jonnew/ONIX/eib-64/README.md

# eib-64
64-channel electrode interface board (EIB) with electrical and optical
stimulation. Designed for small animal (e.g. mouse) tetrode electrophysiology.
Compatible with [headstage-64](../headstage-64/) and small shuttle-drives.

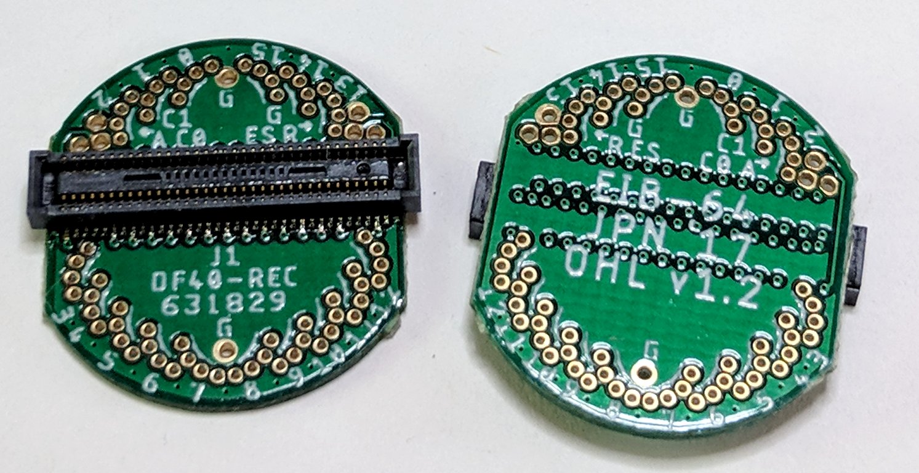
[picture p6: eib-64/img/eib-64.jpg]
eib-64


## Gerber Files
{% include gerber_layers.md %}

## Bill of Materials
The BOM is located on [this google
sheet](https://docs.google.com/spreadsheets/d/1F-KWcdvH_63iXjZf0cgCfDiFX6XXW3qw6rlR8DZrFpQ/edit#gid=1934583654).

## Pinout
The EIB pinout (ADC input mapping, stimulation connections, etc) is located on [this google sheet](https://docs.google.com/spreadsheets/d/11wRDYOqHN5lPb03yUdfXfK0zvaDYsVetplaNK-R90Gg/edit#gid=0)

## Tetrode Connectorization
This EIB uses Neuralynx ["small" gold pins](https://neuralynx.com/hardware/small-eib-pins) to attach tetrode wires. Usage instructions are provided in the [Neuralynx EIB pin Manual](https://neuralynx.com/documents/EIB%20Pins%20Manual.pdf).
