jonnew/ONIX/nanoz-adapter-128-256/README.md

# nanoz-adapter-128-256
Multiplexed adapter to interface eib-128 and eib-256 with the popular
[nanoZ](http://www.white-matter.com/nanoz/) electrode impedance tester and
plating device.

nanoz-128

## Gerber Files
{% include gerber_layers.md %}

## Bill of Materials
The BOM is located on [this google
sheet](https://docs.google.com/spreadsheets/d/1F-KWcdvH_63iXjZf0cgCfDiFX6XXW3qw6rlR8DZrFpQ/edit#gid=889124438).

## Electrode Mapping
The NanoZ internal channel number to EIB mapping for [eib-128](../README.md) and [eib-256](../eib-256/README.md) are provided in the following google sheets:
- [eib-128 channel mapping](https://docs.google.com/spreadsheets/d/11wRDYOqHN5lPb03yUdfXfK0zvaDYsVetplaNK-R90Gg/edit#gid=663991061)
- [eib-256 channel mapping](https://docs.google.com/spreadsheets/d/11wRDYOqHN5lPb03yUdfXfK0zvaDYsVetplaNK-R90Gg/edit#gid=538743909)
