jonnew/ONIX/nanoz-adapter-64/README.md

# nanoz-adapter-64
Adapter to interface eib-64 with the popular
[nanoZ](http://www.white-matter.com/nanoz/) electrode impedance tester and
plating device.

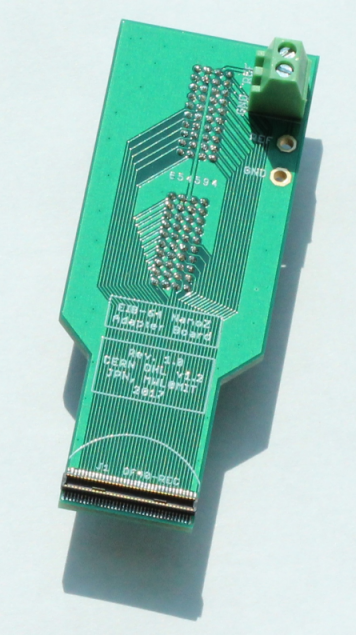
[picture p10: nanoz-adapter-64/img/nanoz-adapter-64.png]
nanoz-64


## Gerber Files
{% include gerber_layers.md %}

## Bill of Materials
The BOM is located on [this google
sheet](https://docs.google.com/spreadsheets/d/1F-KWcdvH_63iXjZf0cgCfDiFX6XXW3qw6rlR8DZrFpQ/edit#gid=889124438).

## Electrode Mapping
The NanoZ internal channel number to [eib-64](../eib-64/README.md) channel mapping is provided on [this google sheet](https://docs.google.com/spreadsheets/d/11wRDYOqHN5lPb03yUdfXfK0zvaDYsVetplaNK-R90Gg/edit#gid=0).
