jonnew/ONIX/omnetics-adapter-64/README.md

# omnetics-adapter-64
Adapter board for using omnetics-based EIBs with headstage-64

## Gerber Files
{% include gerber_layers.md %}

## Bill of Materials
The BOM is located on [this google
sheet](https://docs.google.com/spreadsheets/d/1F-KWcdvH_63iXjZf0cgCfDiFX6XXW3qw6rlR8DZrFpQ/edit#gid=1934583654).

## Pinout
The adapter pinout is located on [this google
sheet](https://docs.google.com/spreadsheets/d/11wRDYOqHN5lPb03yUdfXfK0zvaDYsVetplaNK-R90Gg/edit#gid=1490495645)
