jonnew/ONIX/headstage-neuropix/headstage-neuropix_large-zif/README.md

# headstage-neuropix (large ZIF)
This version of the headstage has a larger, more reliable ZIF connector.

## Bill of materials
TODO
