jonnew/ONIX/headstage-neuropix/headstage-neuropix_standard-zif/README.md

# headstage-neuropix (standard ZIF)
This version of the headstage uses the IMEC-specified ZIF connector.

## Bill of materials
TODO
