jonnew/ONIX/breakout/case/case_.JPG

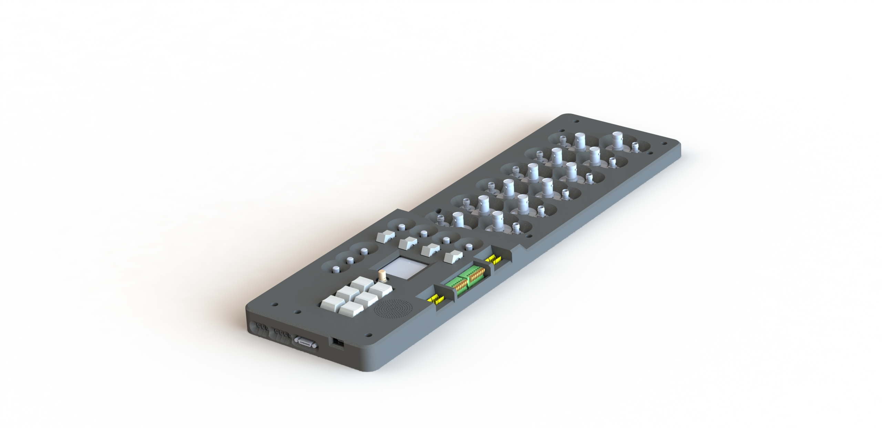
breakout/case/case_.JPG
