jonnew/ONIX/breakout/case/label/top_label_600ppi.png

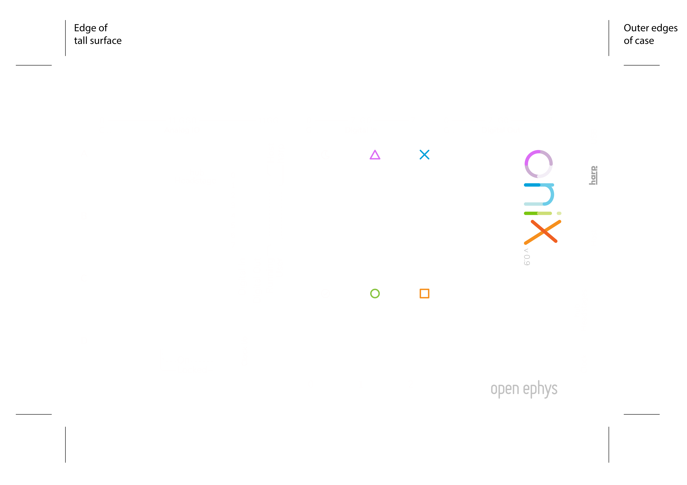
breakout/case/label/top_label_600ppi.png
