jonnew/ONIX/fmc-host/resources/fmc-lpc-pinout.jpg

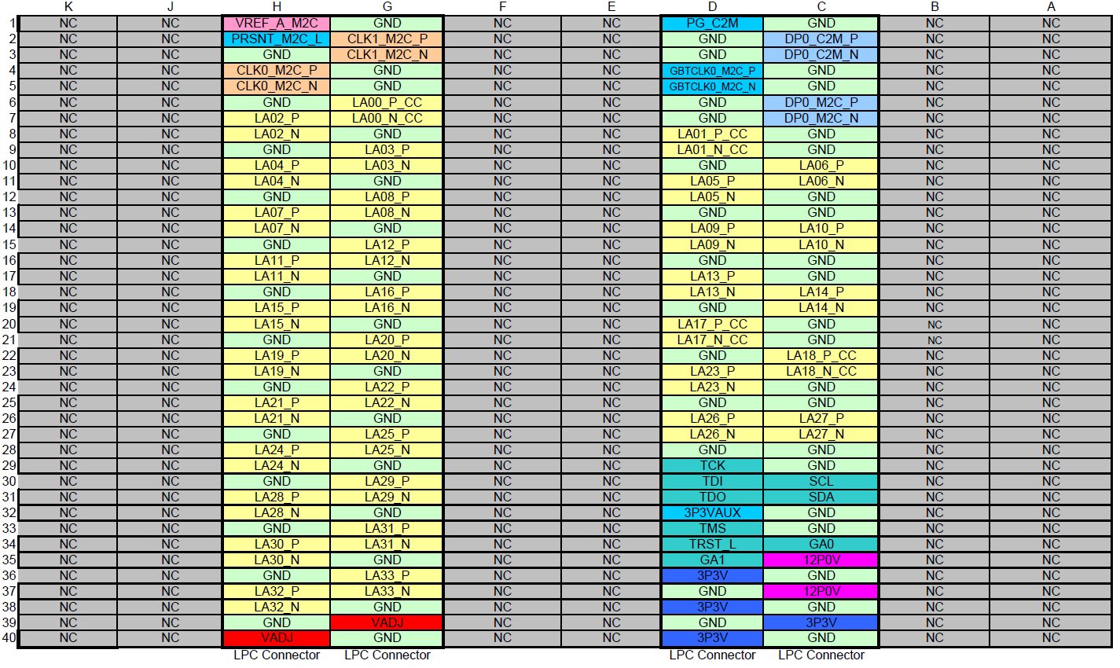
fmc-host/resources/fmc-lpc-pinout.jpg
