jonnew/ONIX/headstage-64/datasheets/MAX10_V81_WLCSP_routing_scheme.png

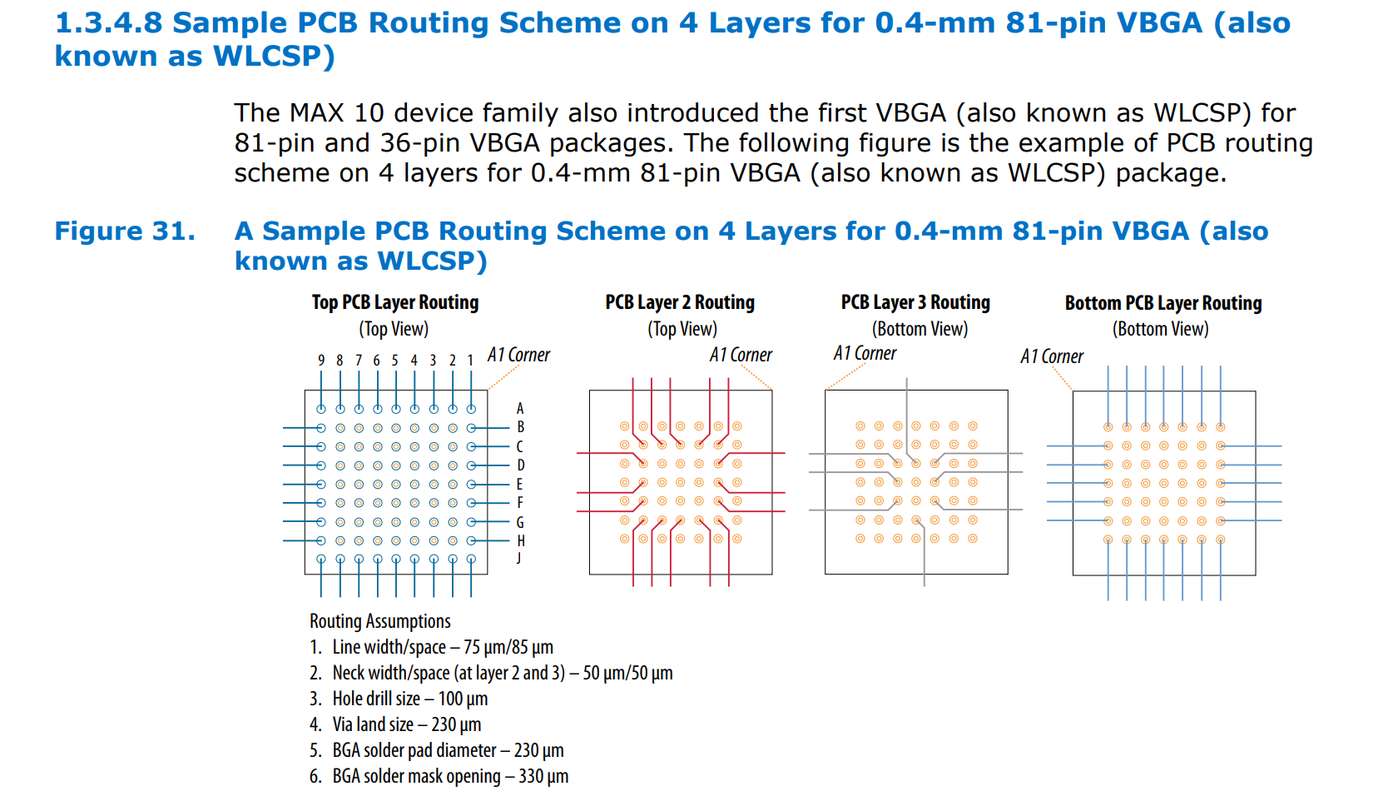
headstage-64/datasheets/MAX10_V81_WLCSP_routing_scheme.png
