jonnew/ONIX/headstage-64/decoupling-capacitors/max10-decoupling-plan.png

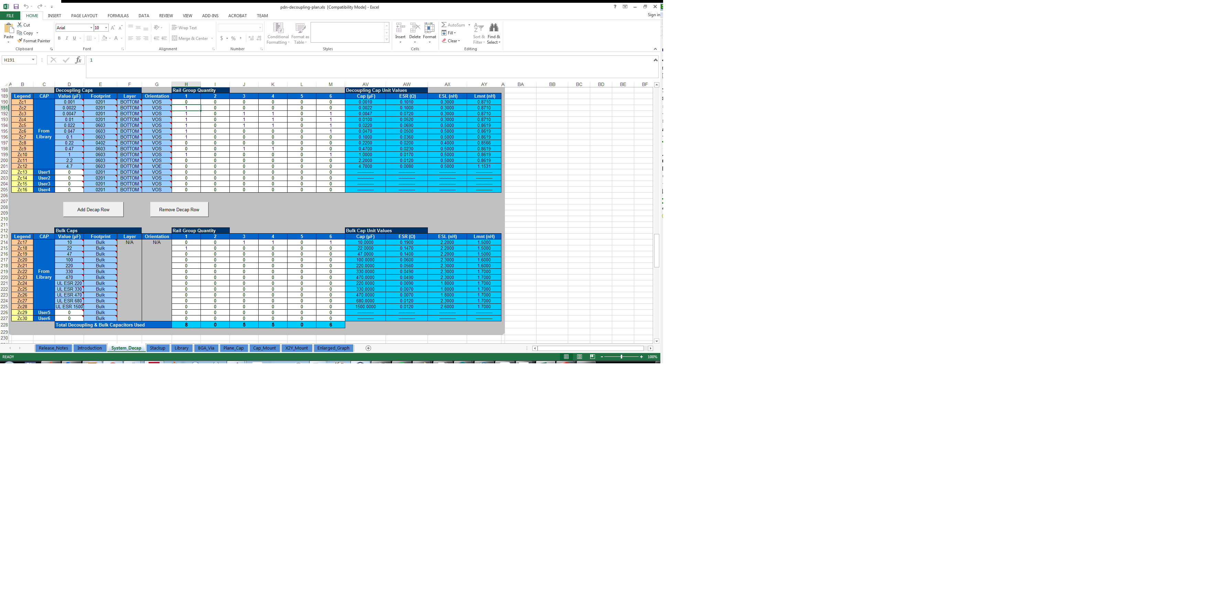
headstage-64/decoupling-capacitors/max10-decoupling-plan.png
