jonnew/ONIX/headstage-256/gerber/README_tab-placement.png

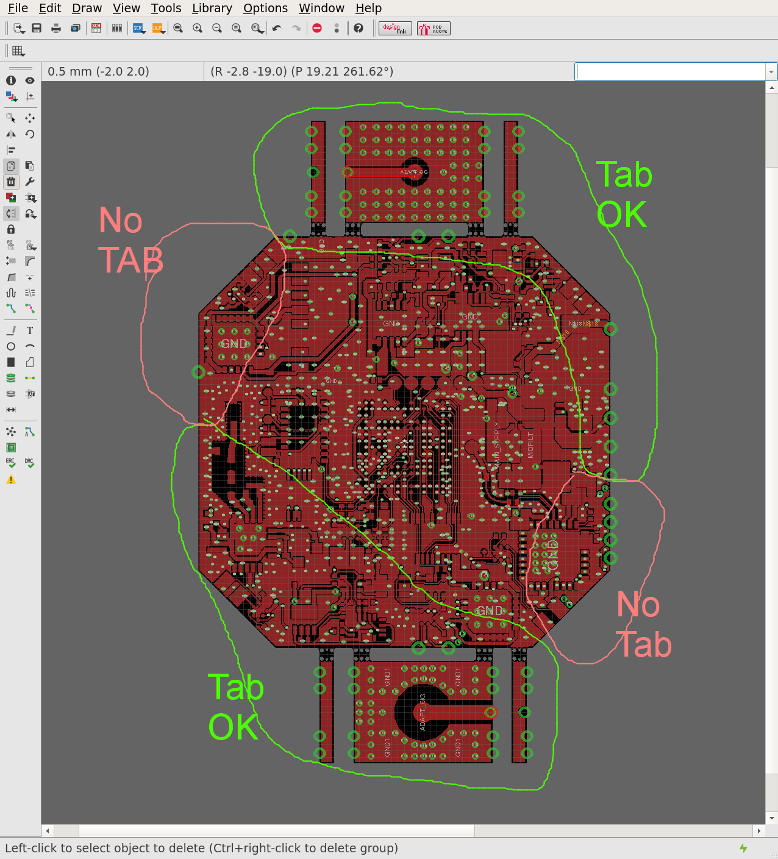
headstage-256/gerber/README_tab-placement.png
