jonnew/ONIX/breakout/case/label/onix_logo_bw.dxf

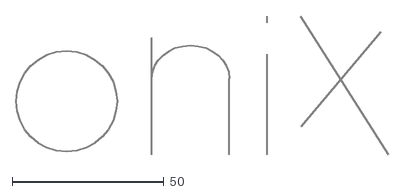
[picture p46: CAD file, 2020-10-13]
breakout/case/label/onix_logo_bw.dxf
122.9 x 45.6
