jonnew/ONIX/doc/size_comparison/rhd64.SLDPRT

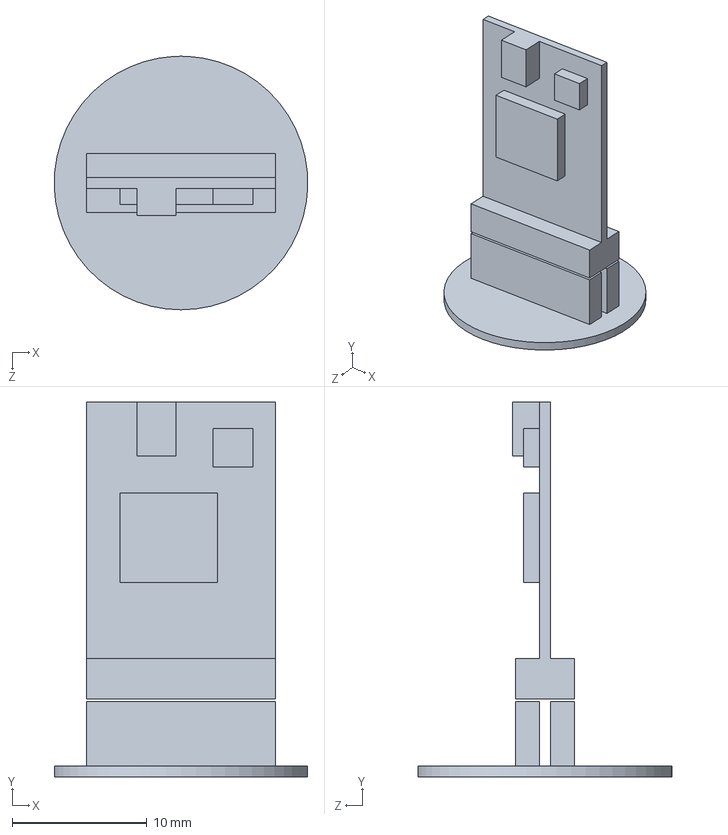
[picture p47: CAD file, 2020-05-30]
doc/size_comparison/rhd64.SLDPRT
18.8 x 27.8 x 18.8 mm
