jonnew/ONIX/fmc-host/pcie_case/fmc_host_pcie_case.SLDPRT

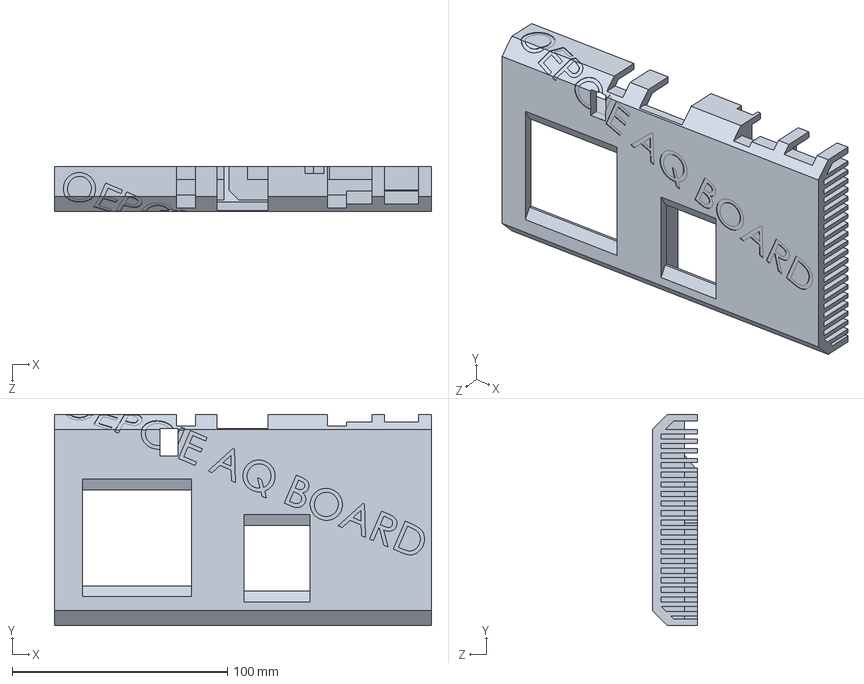
[picture p48: CAD file, 2019-09-29]
fmc-host/pcie_case/fmc_host_pcie_case.SLDPRT
175.0 x 98.0 x 21.0 mm
