jonnew/ONIX/fmc-host/revisions/rev-1.4/pcie_bracket/fmc-host.dxf

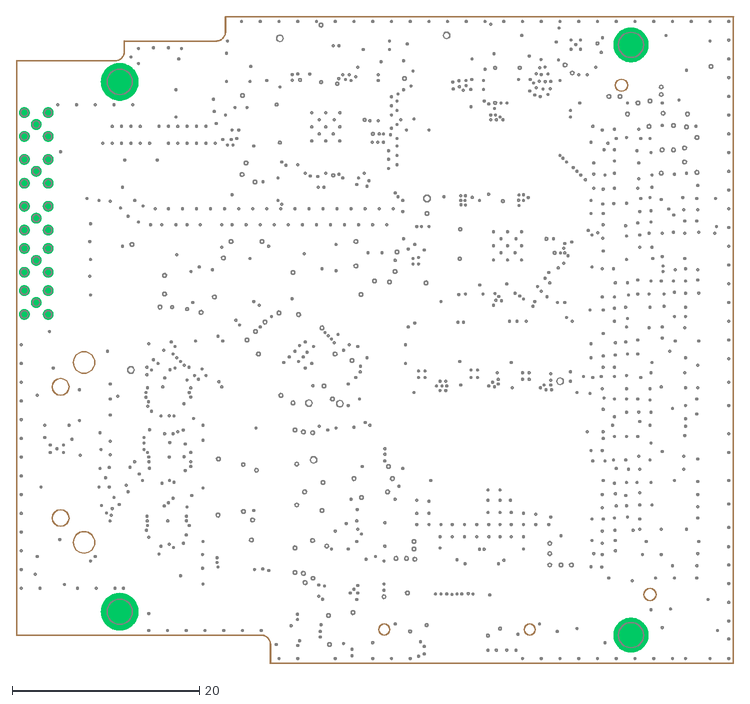
[picture p49: CAD file, 2020-07-13]
fmc-host/revisions/rev-1.4/pcie_bracket/fmc-host.dxf
76.6 x 69.1
