jonnew/ONIX/headstage-programmer/mechanical/headstage-neuropix-holder.SLDPRT

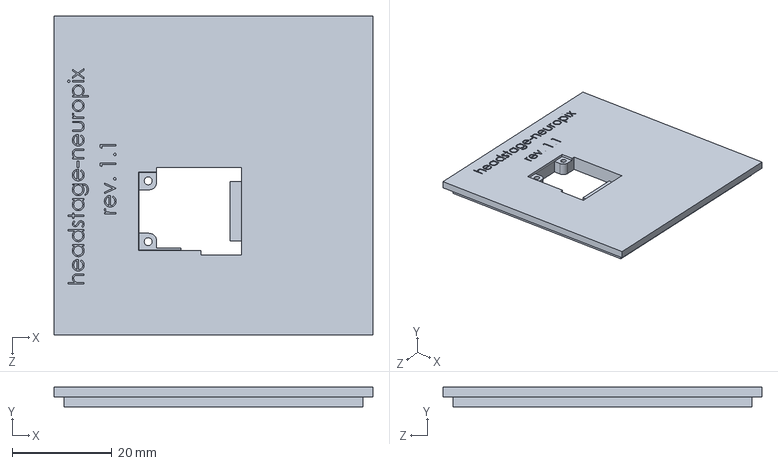
[picture p50: CAD file, 2019-10-03]
headstage-programmer/mechanical/headstage-neuropix-holder.SLDPRT
64.0 x 4.00 x 64.0 mm
