jonnew/ONIX/breakout/case/components/1_5_inch_screen/Adafruit_1.5_128x128_RGB_OLED.dxf

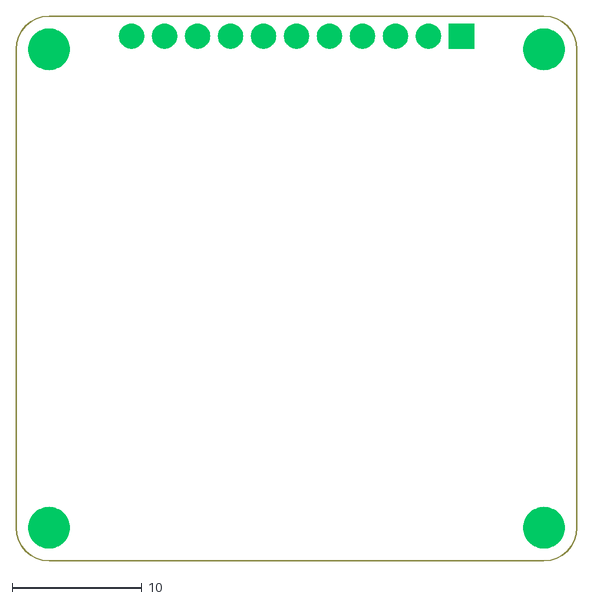
[picture p51: CAD file, 2019-09-01]
breakout/case/components/1_5_inch_screen/Adafruit_1.5_128x128_RGB_OLED.dxf
43.2 x 41.9
