jonnew/ONIX/breakout/case/components/cherryMX/MX轴 轴体 底部.SLDPRT

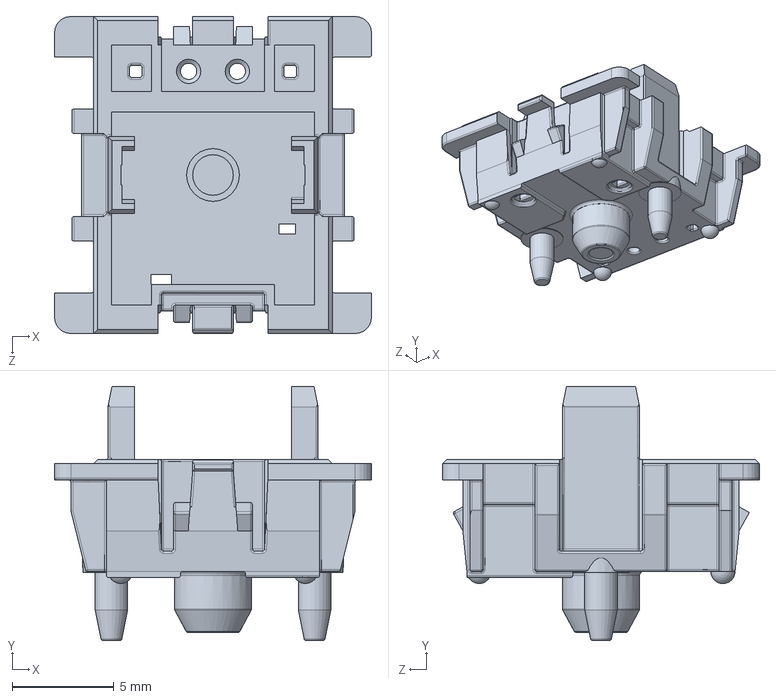
[picture p52: CAD file, 2019-09-01]
breakout/case/components/cherryMX/MX轴 轴体 底部.SLDPRT
15.6 x 12.5 x 15.6 mm
