jonnew/ONIX/breakout/case/components/sma_tall.SLDPRT

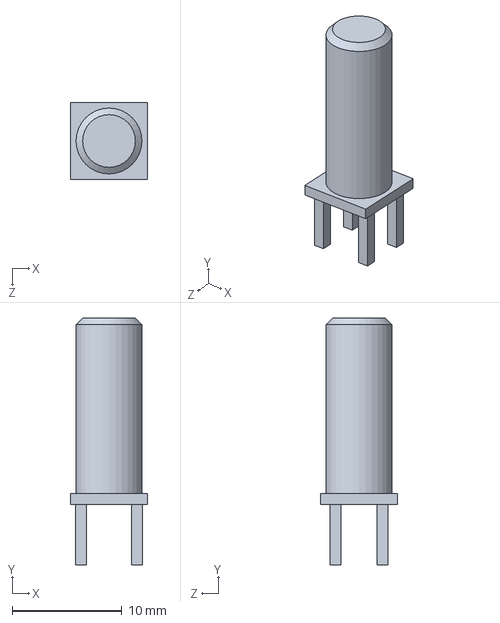
[picture p53: CAD file, 2019-12-28]
breakout/case/components/sma_tall.SLDPRT
7.00 x 22.5 x 7.00 mm
