jonnew/ONIX/breakout/case/pcb_spacer_lasercut_4mm_plastic.DXF

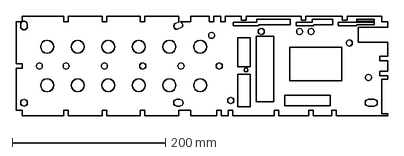
[picture p54: CAD file, 2021-03-16]
breakout/case/pcb_spacer_lasercut_4mm_plastic.DXF
485.0 x 130.0 mm
