jonnew/ONIX/doc/size_comparison/oe_round_spi.SLDPRT

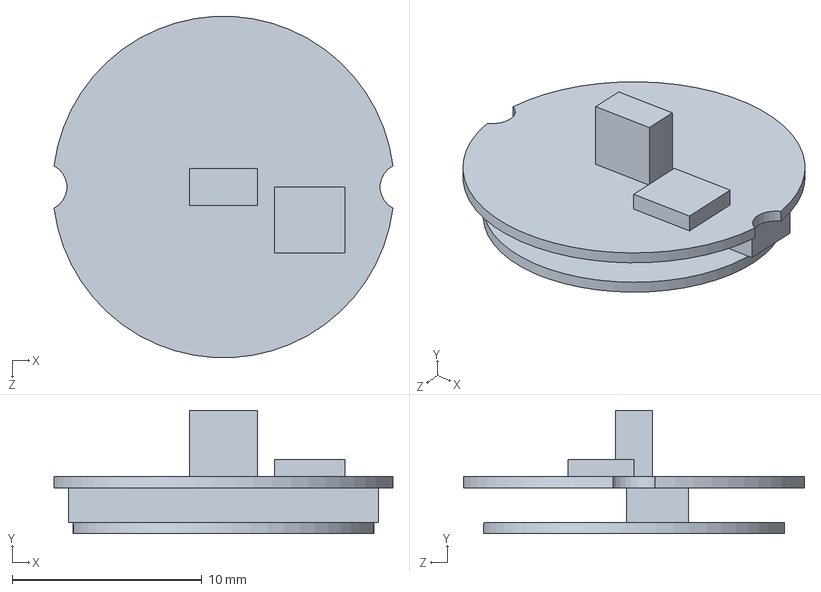
[picture p55: CAD file, 2020-05-30]
doc/size_comparison/oe_round_spi.SLDPRT
17.9 x 6.50 x 18.0 mm
