jonnew/ONIX/fmc-host/pcie_case/refs/WaveTherm-OC-PCB-FMC_OC-PCB-FMC.SLDPRT

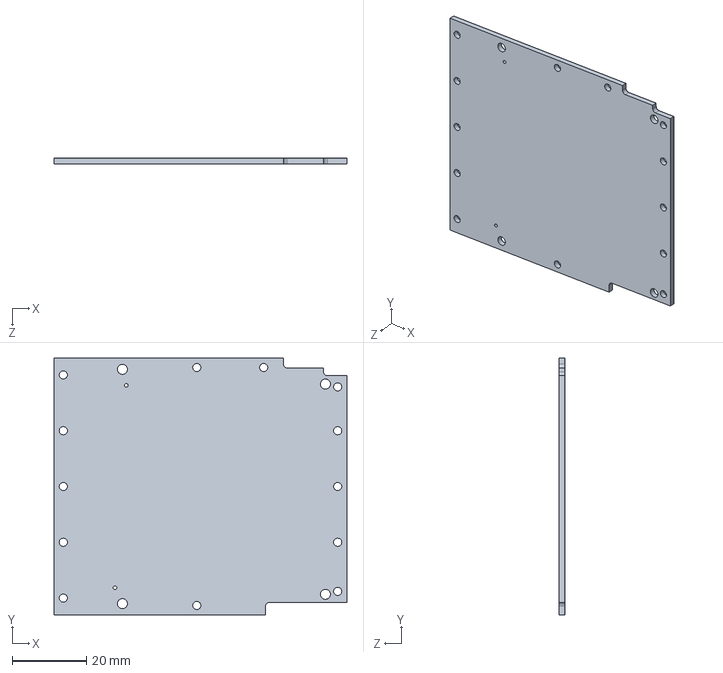
[picture p56: CAD file, 2019-05-07]
fmc-host/pcie_case/refs/WaveTherm-OC-PCB-FMC_OC-PCB-FMC.SLDPRT
78.8 x 69.0 x 1.60 mm
