jonnew/ONIX/fmc-host/revisions/rev-1.4/pcie_bracket/PCIe_bracket_cnc_thick.SLDPRT

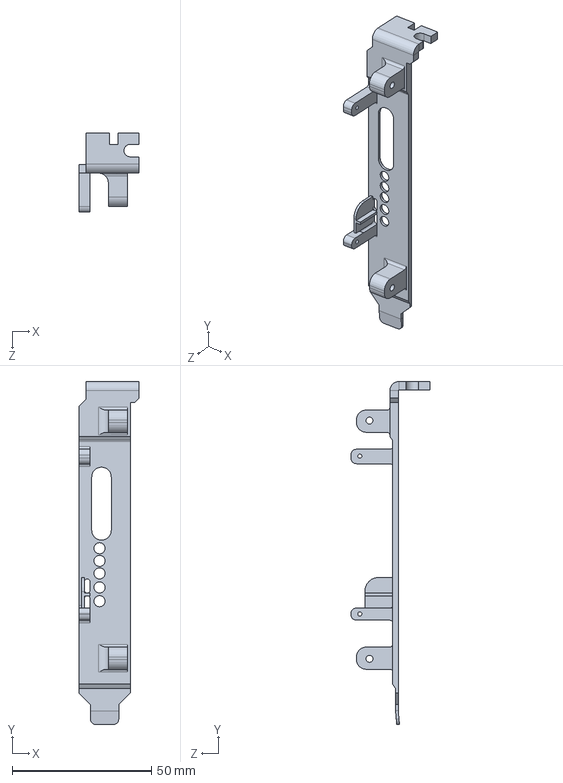
[picture p57: CAD file, 2020-03-31]
fmc-host/revisions/rev-1.4/pcie_bracket/PCIe_bracket_cnc_thick.SLDPRT
21.6 x 123.0 x 28.4 mm
