jonnew/ONIX/breakout/case/components/audio_plug_CUI_SJ1-3514-SMT-TR.sldprt

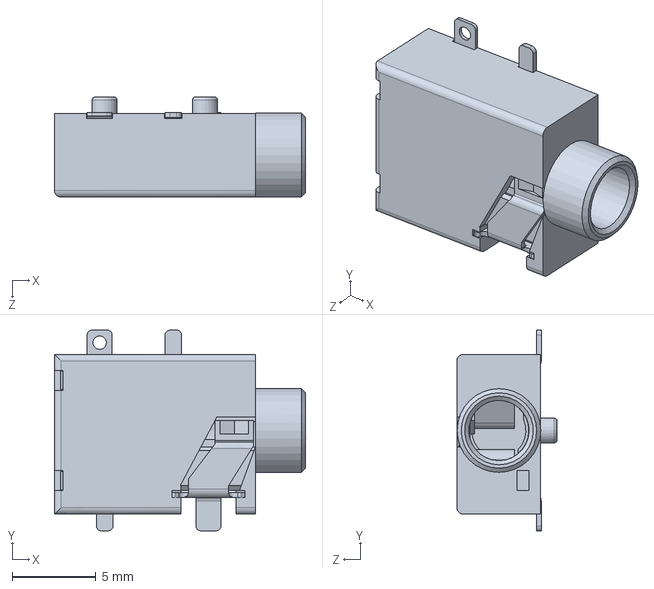
[picture p58: CAD file, 2019-12-28]
breakout/case/components/audio_plug_CUI_SJ1-3514-SMT-TR.sldprt
15.0 x 12.0 x 6.00 mm
