jonnew/ONIX/breakout/case/components/cherryMX/MX .STEP

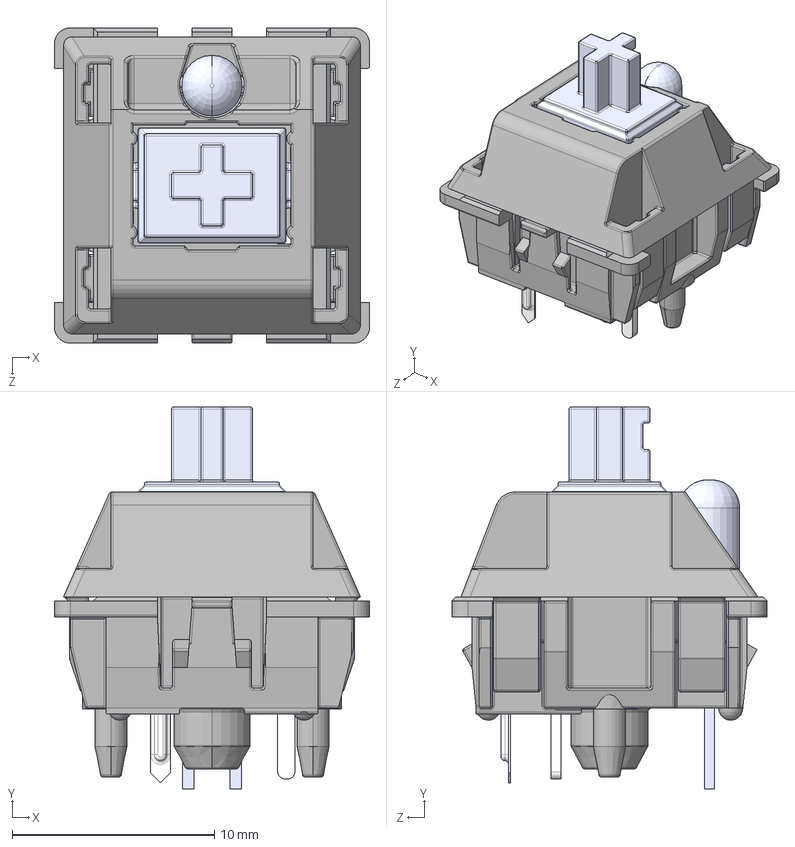
[picture p59: CAD file, 2019-09-01]
breakout/case/components/cherryMX/MX .STEP
15.6 x 18.9 x 15.6 mm
MX 轴 按键′_ü___¨1
MX 轴 轴体áì_¨￠¨__
MX粣 拸簽LEDLEDLED
MX轴 轴体 底部 μ×2__默认_á2____è_
针脚___默认__è_
