jonnew/ONIX/fmc-host/pcie_case/refs/WaveTherm-OC-PCB-FMC_SAMTEC_ASP-134488-01.sldprt

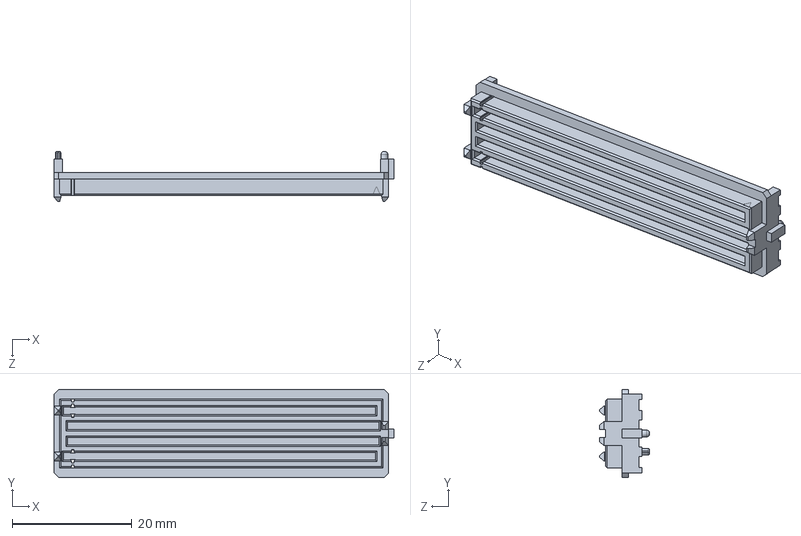
[picture p60: CAD file, 2019-05-07]
fmc-host/pcie_case/refs/WaveTherm-OC-PCB-FMC_SAMTEC_ASP-134488-01.sldprt
56.7 x 14.7 x 8.38 mm
