jonnew/ONIX/breakout/case/components/header_height_spacer_10mm.SLDPRT

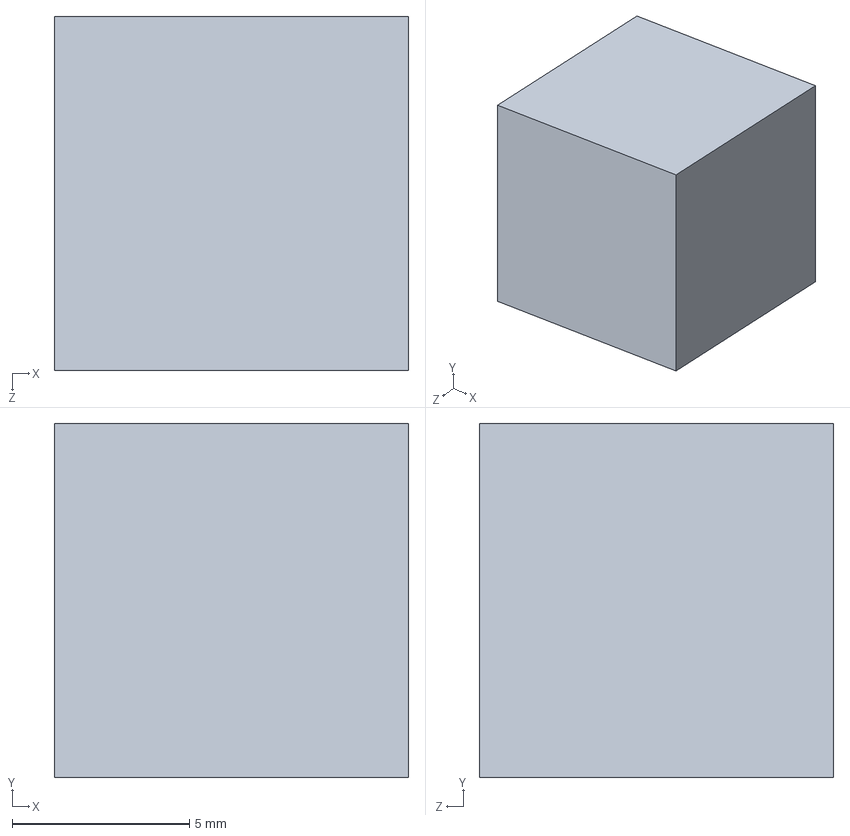
[picture p62: CAD file, 2019-12-28]
breakout/case/components/header_height_spacer_10mm.SLDPRT
10.0 x 10.0 x 10.0 mm
