jonnew/ONIX/fmc-host/revisions/rev-1.4/pcie_bracket/fmc_pcb.SLDPRT

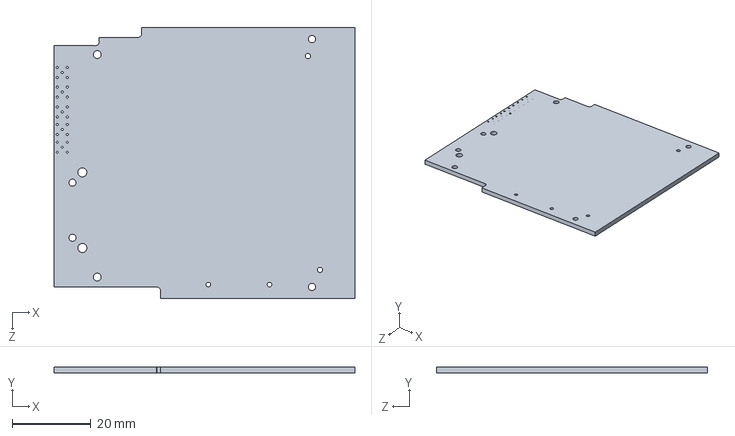
[picture p64: CAD file, 2019-09-29]
fmc-host/revisions/rev-1.4/pcie_bracket/fmc_pcb.SLDPRT
76.5 x 1.60 x 69.0 mm
