jonnew/ONIX/breakout/case/components/cherryMX/针脚.SLDPRT

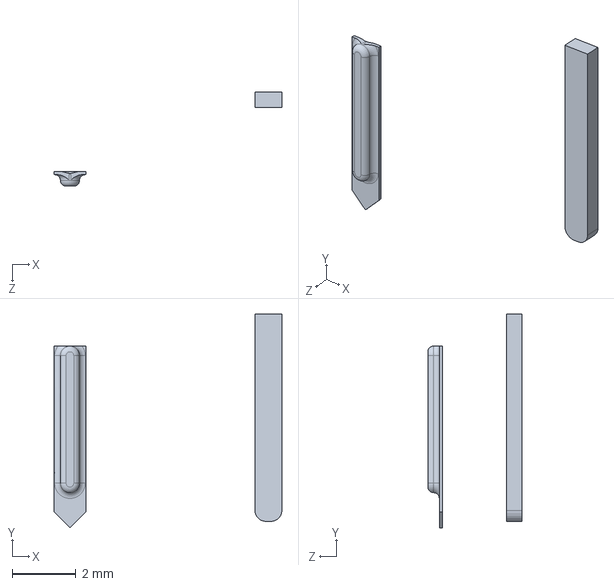
[picture p65: CAD file, 2019-09-01]
breakout/case/components/cherryMX/针脚.SLDPRT
7.15 x 6.70 x 2.96 mm
