jonnew/ONIX/breakout/case/components/mmcx_through_hole.SLDPRT

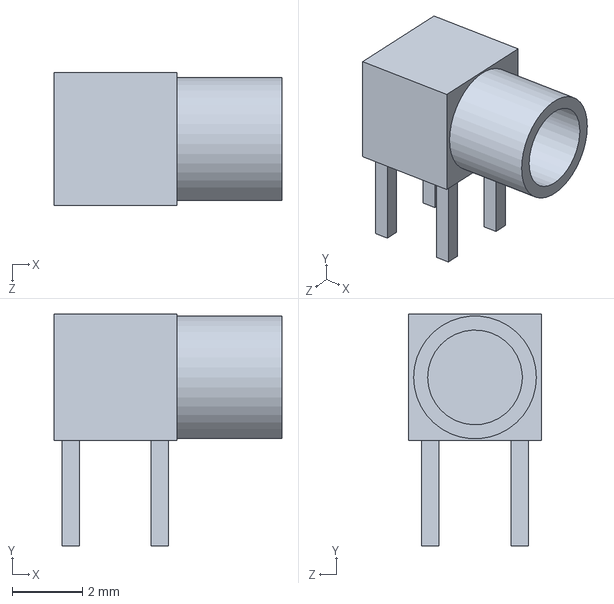
[picture p66: CAD file, 2019-12-28]
breakout/case/components/mmcx_through_hole.SLDPRT
6.50 x 6.60 x 3.80 mm
