jonnew/ONIX/breakout/case/pcb_bottom_waterjet_3mm_aluminum.DXF

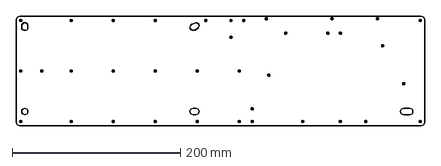
[picture p67: CAD file, 2021-03-16]
breakout/case/pcb_bottom_waterjet_3mm_aluminum.DXF
485.0 x 130.0 mm
