jonnew/ONIX/fmc-host/revisions/rev-1.4/pcie_bracket/PCIe bracket slot 1.SLDPRT

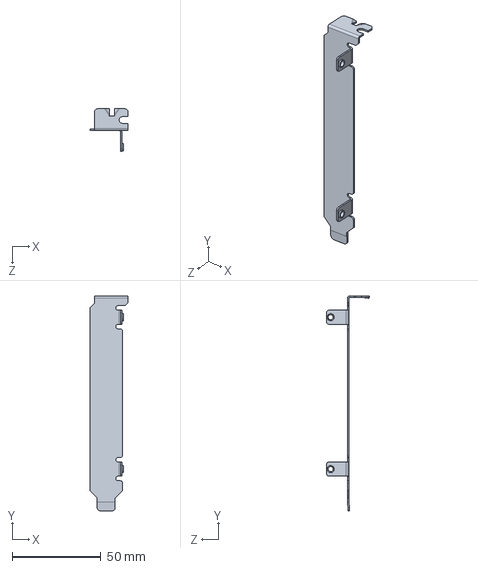
[picture p68: CAD file, 2019-09-29]
fmc-host/revisions/rev-1.4/pcie_bracket/PCIe bracket slot 1.SLDPRT
21.6 x 120.9 x 24.1 mm
