jonnew/ONIX/breakout/case/Body3.sldprt

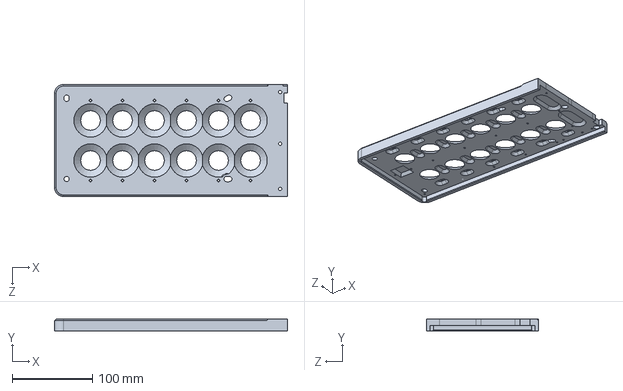
[picture p69: CAD file, 2021-03-16]
breakout/case/Body3.sldprt
291.2 x 15.0 x 140.0 mm
