jonnew/ONIX/breakout/case/components/bnc_112538.SLDPRT

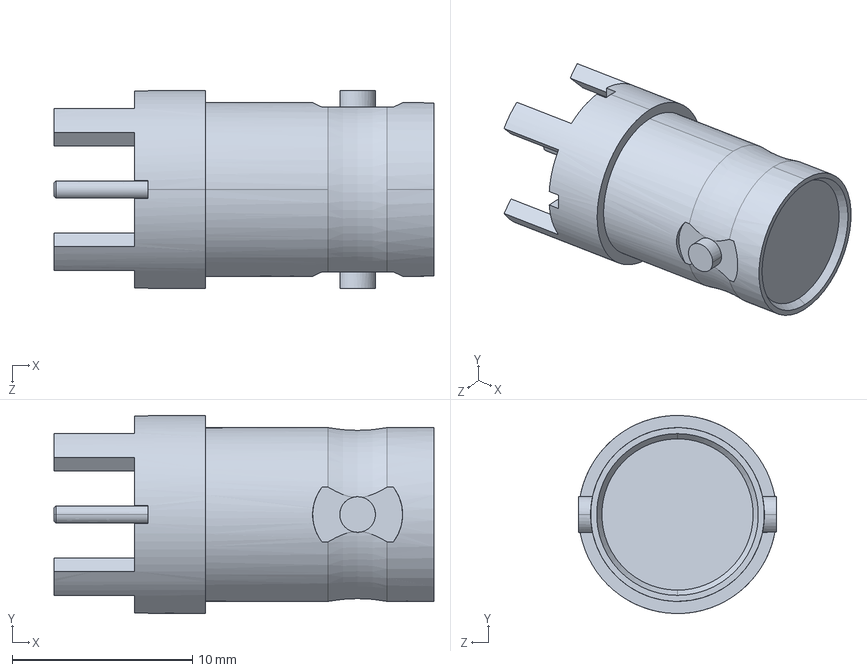
[picture p70: CAD file, 2019-12-28]
breakout/case/components/bnc_112538.SLDPRT
21.1 x 11.0 x 11.0 mm
