jonnew/ONIX/fmc-host/revisions/rev-1.4/pcie_bracket/FMC_10mm_stackheight_spacer.SLDPRT

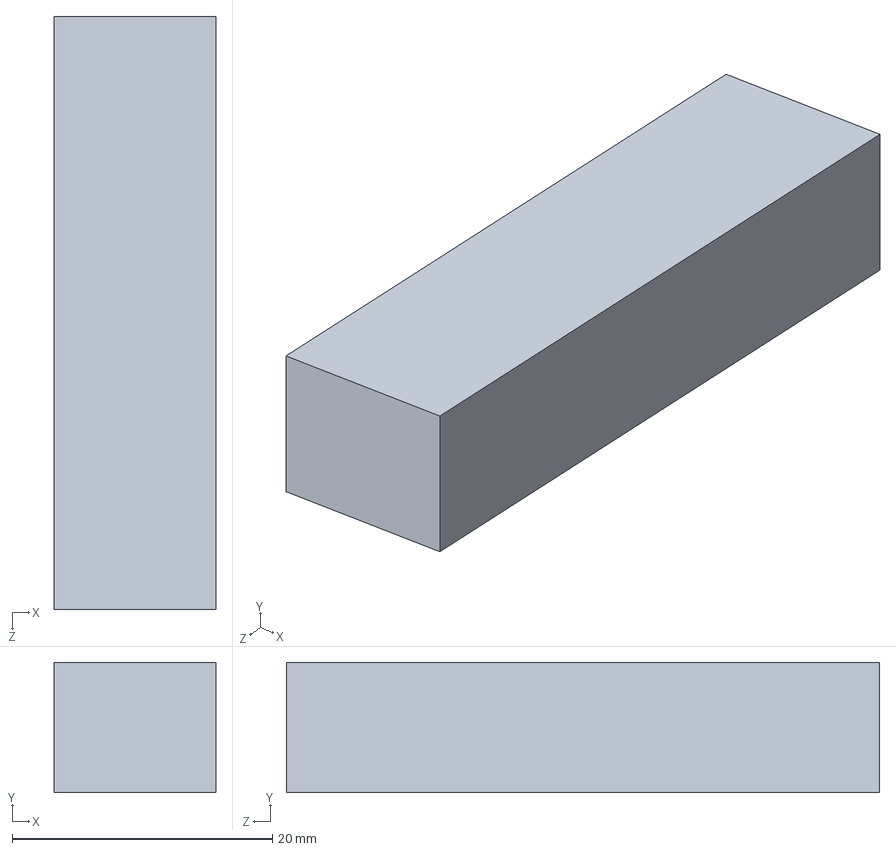
[picture p71: CAD file, 2019-09-29]
fmc-host/revisions/rev-1.4/pcie_bracket/FMC_10mm_stackheight_spacer.SLDPRT
12.5 x 10.0 x 45.6 mm
