jonnew/ONIX/headstage-programmer/mechanical/headstage-64-holder.SLDPRT

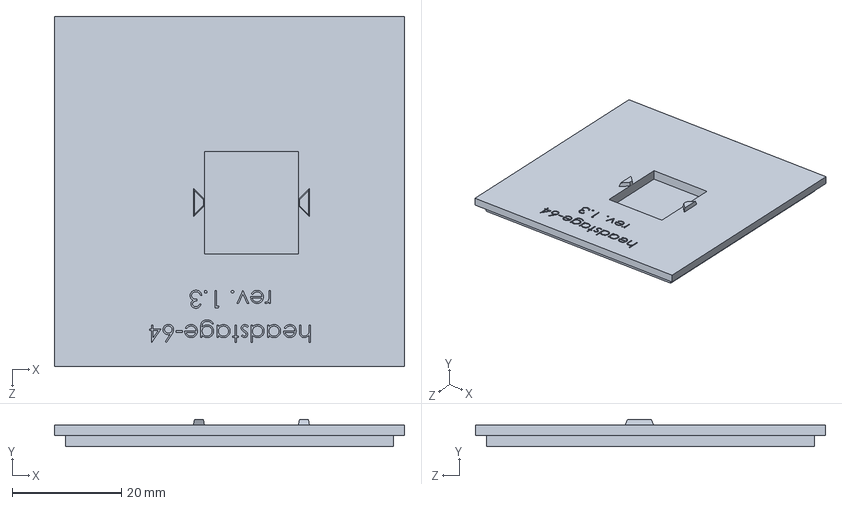
[picture p72: CAD file, 2019-09-30]
headstage-programmer/mechanical/headstage-64-holder.SLDPRT
64.0 x 5.00 x 64.0 mm
