jonnew/ONIX/breakout/case/components/cherryMX/MX 轴 轴体.SLDPRT

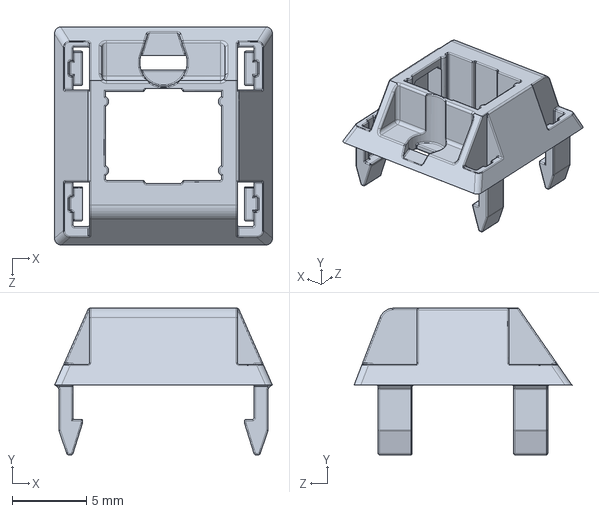
[picture p73: CAD file, 2019-09-01]
breakout/case/components/cherryMX/MX 轴 轴体.SLDPRT
14.7 x 9.90 x 14.7 mm
