jonnew/ONIX/breakout/case/components/header_69168-x20.SLDPRT

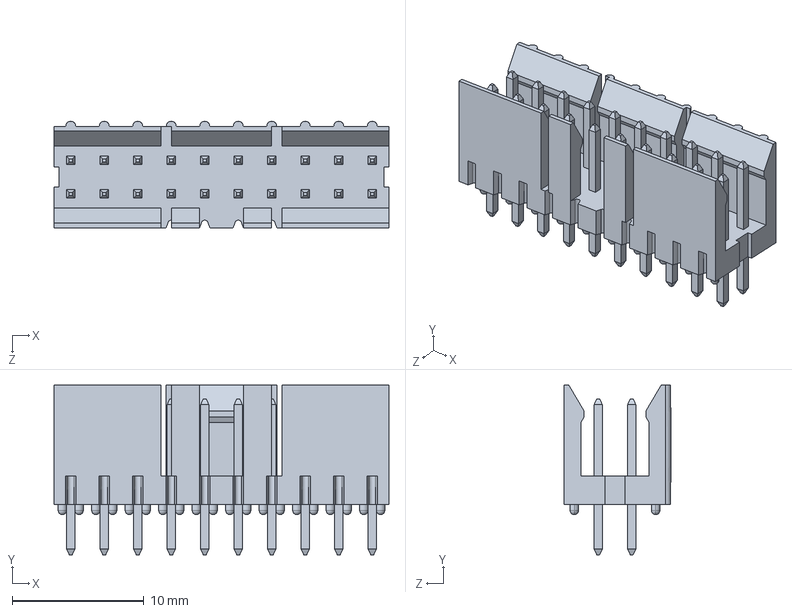
[picture p74: CAD file, 2019-12-28]
breakout/case/components/header_69168-x20.SLDPRT
25.4 x 12.9 x 8.08 mm
