jonnew/ONIX/headstage-programmer/mechanical/pcb-housing-base.SLDPRT

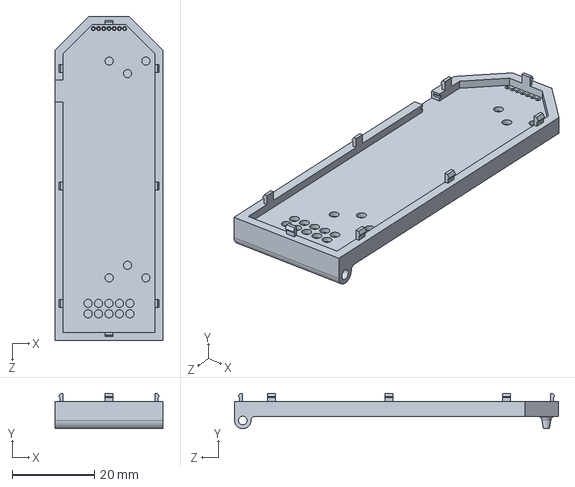
[picture p76: CAD file, 2019-09-30]
headstage-programmer/mechanical/pcb-housing-base.SLDPRT
26.2 x 8.60 x 78.6 mm
