jonnew/ONIX/breakout/case/breakout_case_pcb_3.SLDPRT

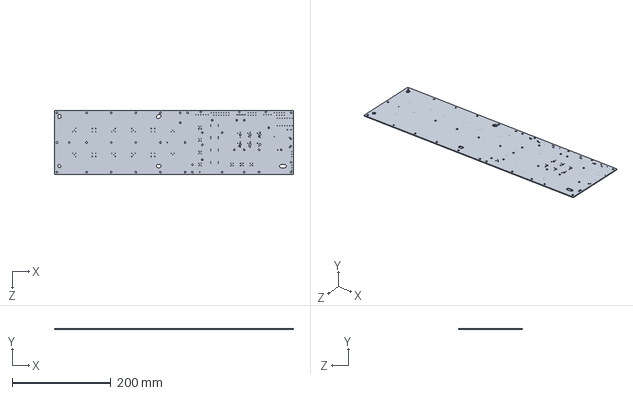
[picture p77: CAD file, 2020-09-16]
breakout/case/breakout_case_pcb_3.SLDPRT
485.0 x 1.60 x 130.0 mm
