jonnew/ONIX/breakout/case/components/cherryMX/MX轴 无帽LED.SLDPRT

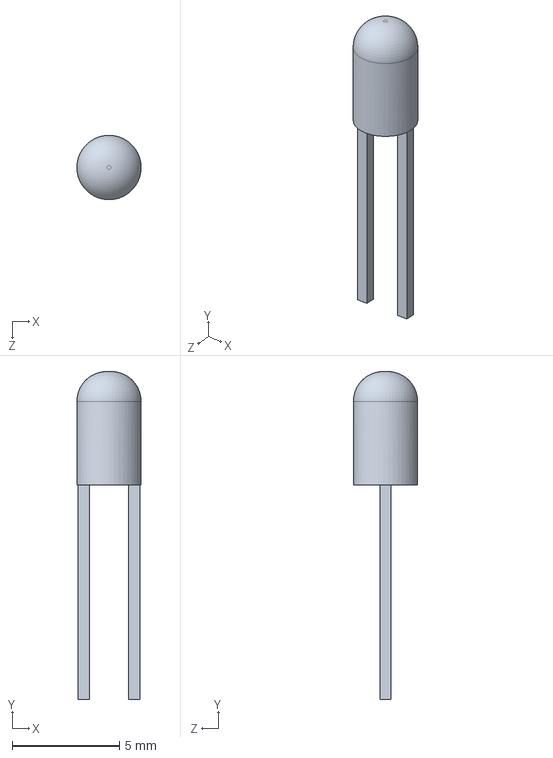
[picture p78: CAD file, 2019-09-01]
breakout/case/components/cherryMX/MX轴 无帽LED.SLDPRT
3.00 x 15.3 x 3.00 mm
