jonnew/ONIX/breakout/case/components/speaker_stapez_ BGC-D40-22-4-002 .SLDPRT

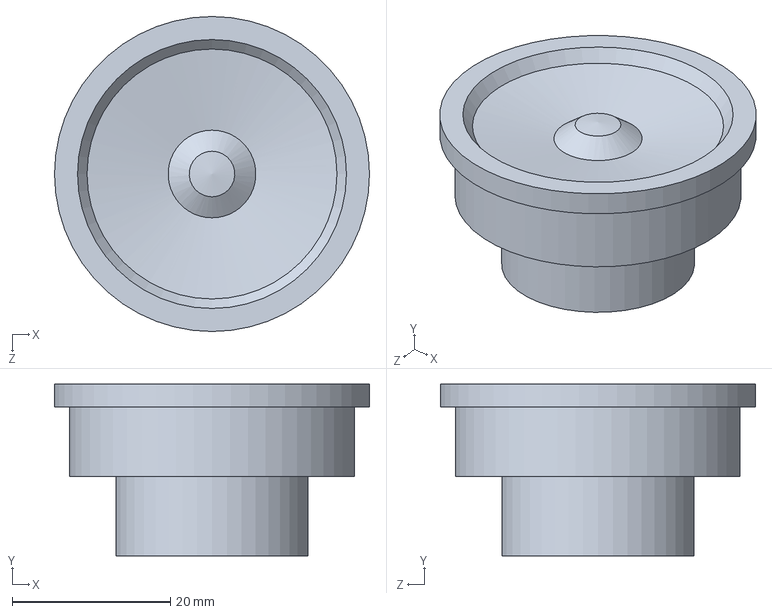
[picture p79: CAD file, 2019-09-01]
breakout/case/components/speaker_stapez_ BGC-D40-22-4-002 .SLDPRT
39.8 x 21.7 x 39.8 mm
