jonnew/ONIX/headstage-programmer/mechanical/headstage-256-holder.SLDPRT

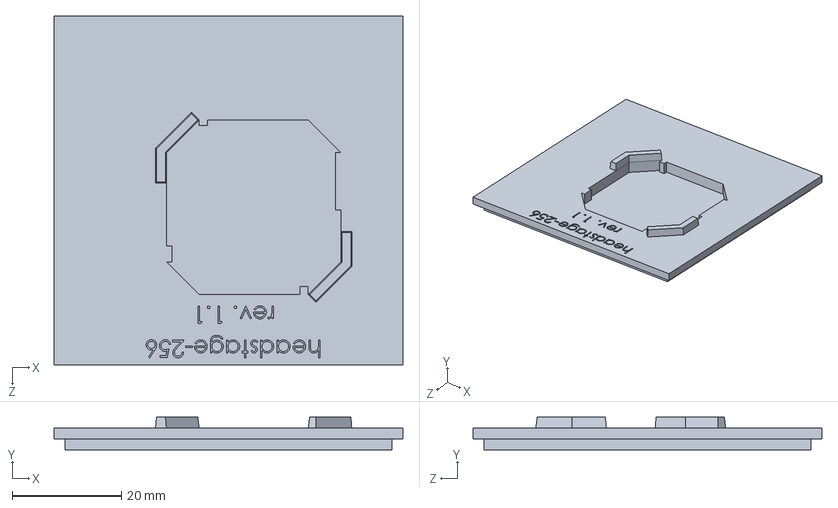
[picture p80: CAD file, 2019-09-30]
headstage-programmer/mechanical/headstage-256-holder.SLDPRT
64.0 x 6.00 x 64.0 mm
