jonnew/ONIX/breakout/case/breakout_case_top_shell.SLDPRT

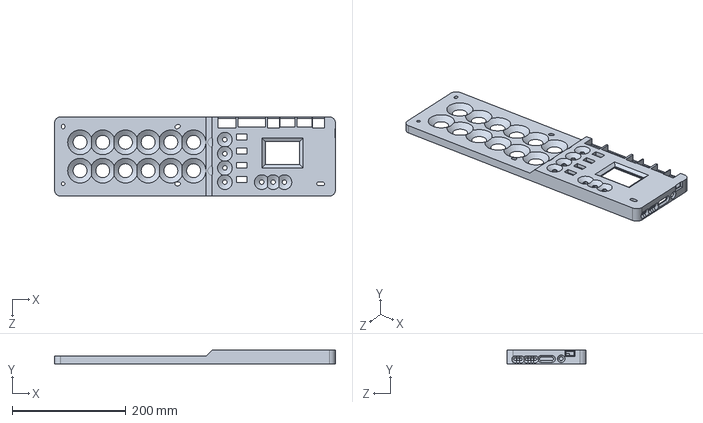
[picture p81: CAD file, 2020-09-01]
breakout/case/breakout_case_top_shell.SLDPRT
495.0 x 24.0 x 140.0 mm
