jonnew/ONIX/breakout/case/components/encoder_CUI_C14D32P-F3.sldprt

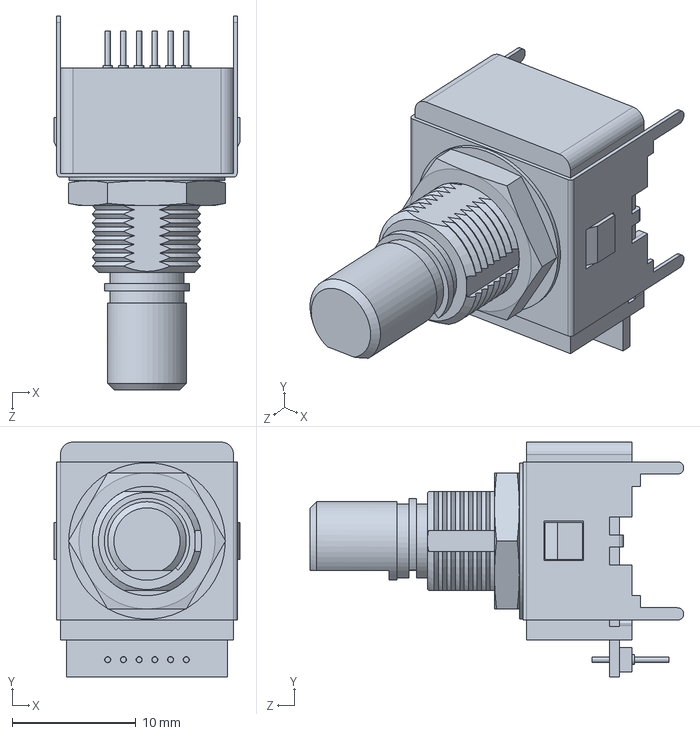
[picture p82: CAD file, 2019-09-01]
breakout/case/components/encoder_CUI_C14D32P-F3.sldprt
15.0 x 19.0 x 30.2 mm
