jonnew/ONIX/breakout/case/components/sma_small_c-5-1814832-1-b-3d.stp

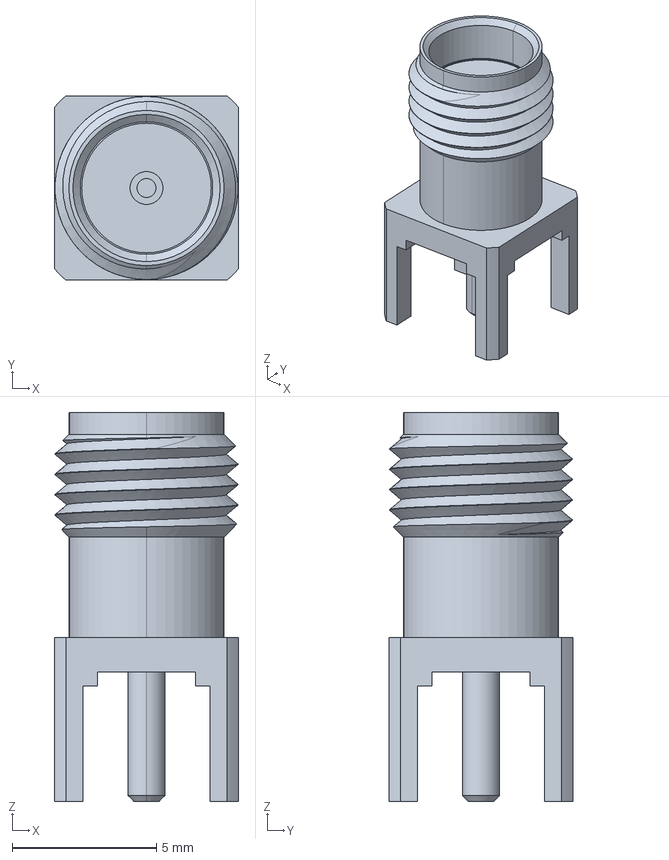
[picture p83: CAD file, 2019-09-01]
breakout/case/components/sma_small_c-5-1814832-1-b-3d.stp
6.40 x 6.40 x 13.5 mm
