jonnew/ONIX/breakout/case/WP154A4SEJ3VBDZGW-CA_rgb-led.SLDPRT

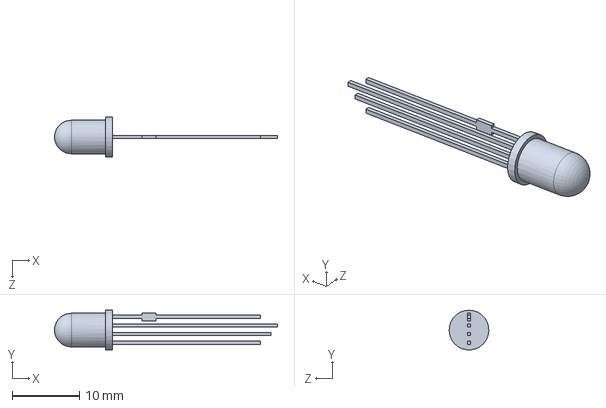
[picture p84: CAD file, 2020-05-30]
breakout/case/WP154A4SEJ3VBDZGW-CA_rgb-led.SLDPRT
33.1 x 5.88 x 5.89 mm
