jonnew/ONIX/headstage-programmer/mechanical/jig-base.sldprt

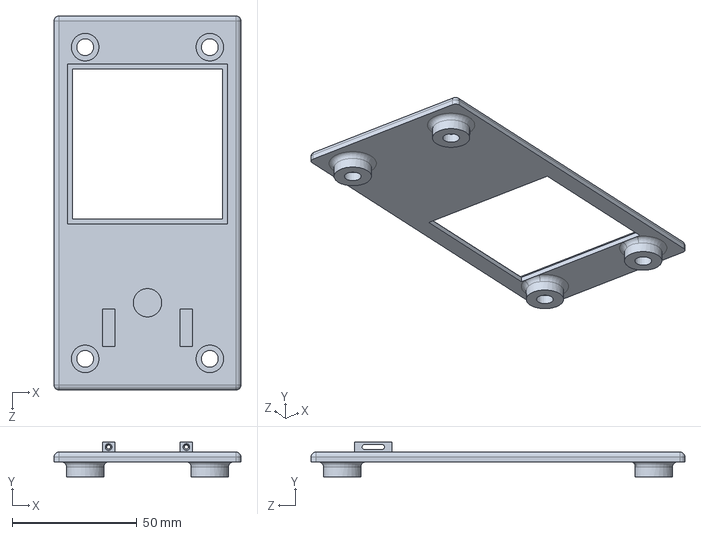
[picture p85: CAD file, 2019-09-30]
headstage-programmer/mechanical/jig-base.sldprt
75.0 x 14.0 x 150.0 mm
