jonnew/ONIX/breakout/case/components/cameralink_12226-8250-00FR.stp

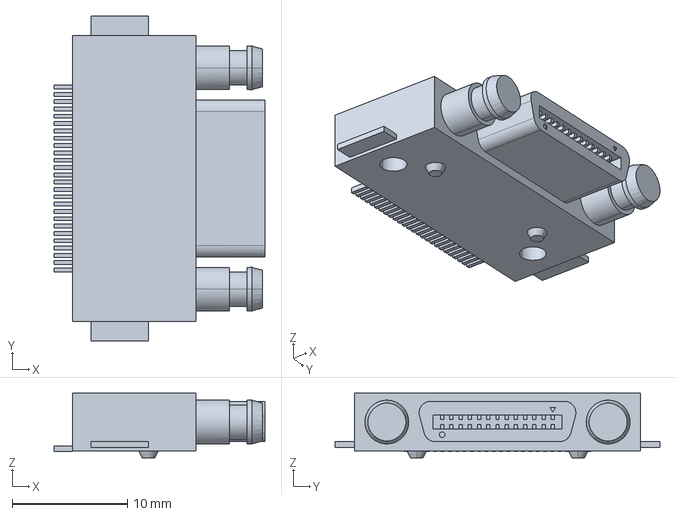
[picture p86: CAD file, 2019-09-01]
breakout/case/components/cameralink_12226-8250-00FR.stp
18.3 x 28.2 x 5.60 mm
