jonnew/ONIX/breakout/case/LPA-C011302S-2_lightpipe.SLDPRT

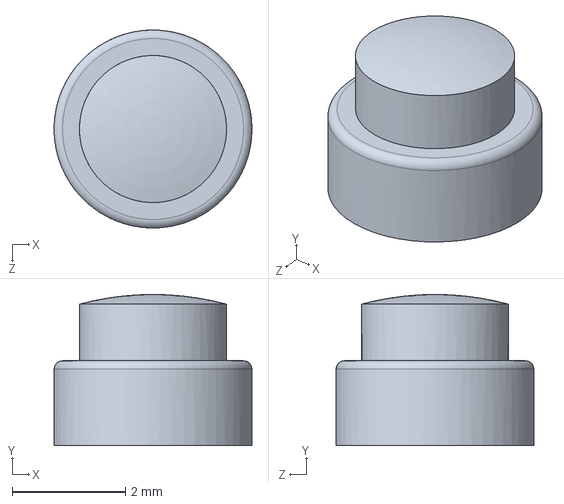
[picture p87: CAD file, 2020-05-30]
breakout/case/LPA-C011302S-2_lightpipe.SLDPRT
3.50 x 2.67 x 3.50 mm
