jonnew/ONIX/headstage-programmer/mechanical/pcb-housing-top.sldprt

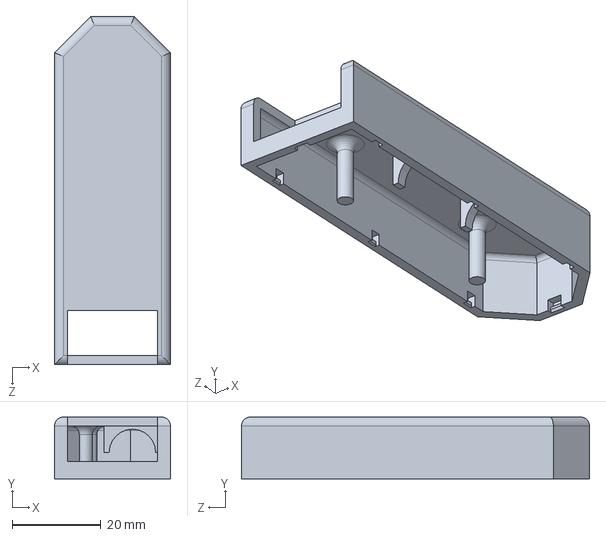
[picture p88: CAD file, 2019-09-30]
headstage-programmer/mechanical/pcb-housing-top.sldprt
26.2 x 14.0 x 78.6 mm
