jonnew/ONIX/breakout/case/breakout_case_bottom_shell.SLDPRT

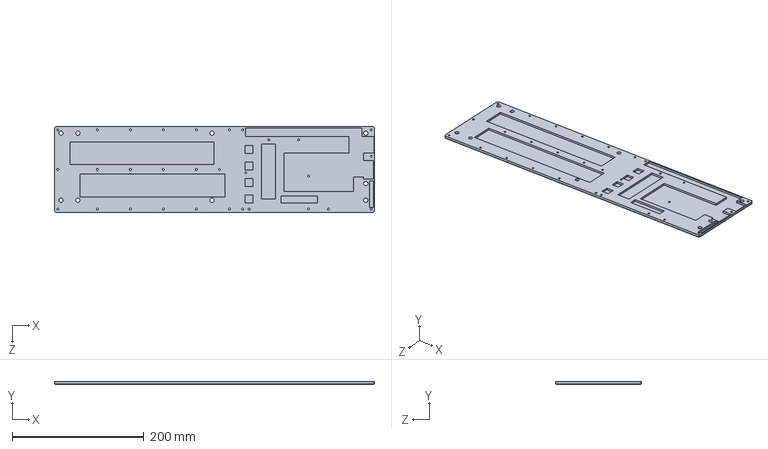
[picture p89: CAD file, 2020-05-30]
breakout/case/breakout_case_bottom_shell.SLDPRT
485.0 x 5.00 x 130.0 mm
