jonnew/ONIX/breakout/case/rotatary_knob.STL

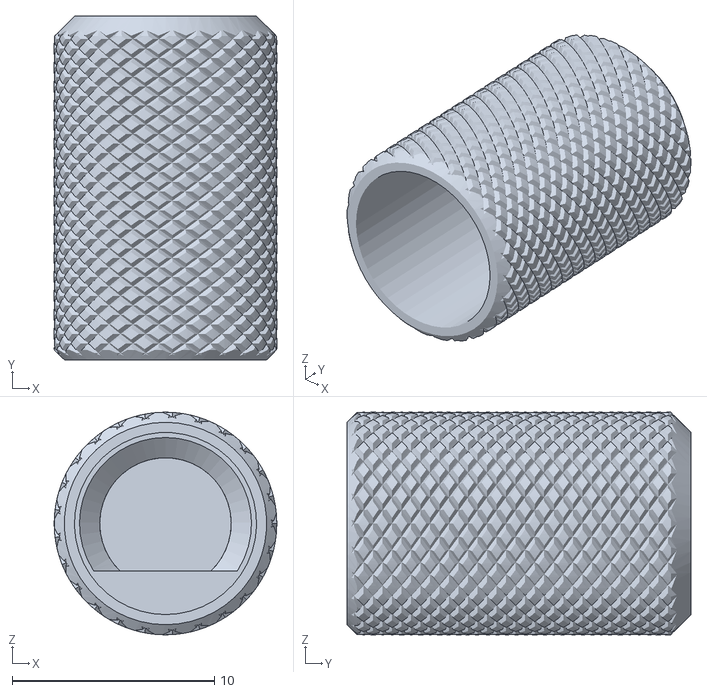
[picture p90: CAD file, 2019-09-23]
breakout/case/rotatary_knob.STL
11.0 x 17.0 x 11.0
