jonnew/ONIX/breakout/case/breakout_case_top_shell_draft.SLDPRT

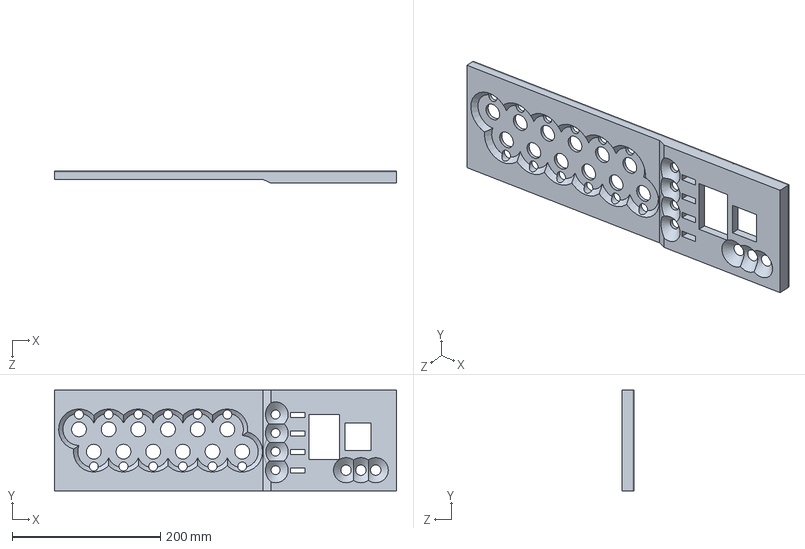
[picture p91: CAD file, 2019-08-21]
breakout/case/breakout_case_top_shell_draft.SLDPRT
461.0 x 136.0 x 16.6 mm
