jonnew/ONIX/breakout/case/analog-io-breakout.step

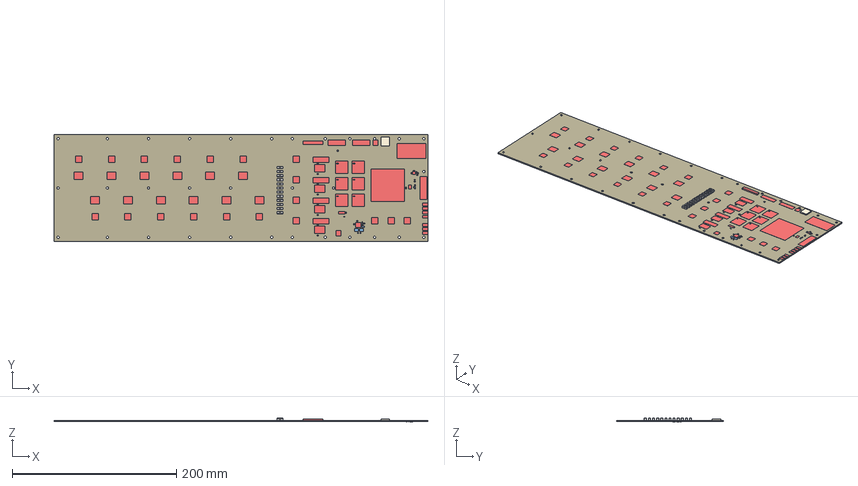
[picture p92: CAD file, 2019-08-19]
breakout/case/analog-io-breakout.step
455.0 x 130.0 x 4.27 mm
Board
FE10-2
MMCX-J-P-X-RA-SM1 x 7
SCREW2 x 2
SCREW8 x 2
SMA_JACK_142-0701-201 x 19
TESTPOINT_2MM
DIODE-ESD-BIDIRECTIONALDO-214AA x 12
TEENSY_3.1_BASIC
ADAFRUIT_1_5_OLED
CHERRY-MX x 6
12226-8250-00FR
1k x 34
SJ_2_0201 x 2
LTC2875_DFN
FIN1032MTCX
SN65LVDS9638DGN x 2
ROCKER_SWITCH x 4
G6KU-2F-RF-TR09DC5 x 4
LTM4622A
10uF
47uF x 2
B1,27 x 2
TCA9555
