jonnew/ONIX/breakout/case/Draw2.DXF

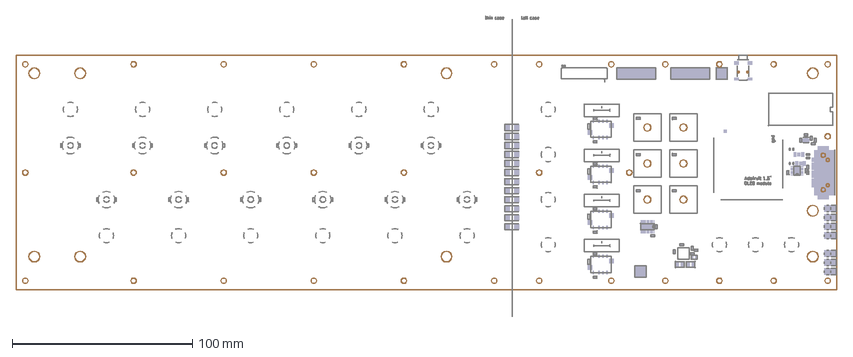
[picture p93: CAD file, 2019-08-19]
breakout/case/Draw2.DXF
455.0 x 166.8 mm
