jonnew/ONIX/omnetics-spi-wire-adapter/RHD2000_cable_adapt_PCB_assembly_guide.pdf

## RHD2000 Cable Adapter Board

0.500”

0.900”

FR-4, 0.031” thick, gold immersion finish

No through-hole components; only one SMD connector on top side only

actual size

Components (1 total)

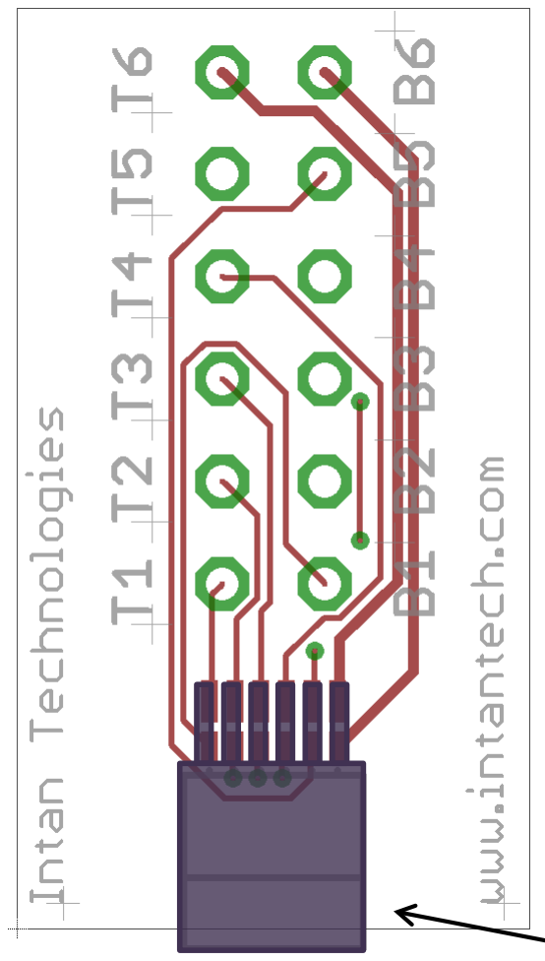
[picture p102: figure]
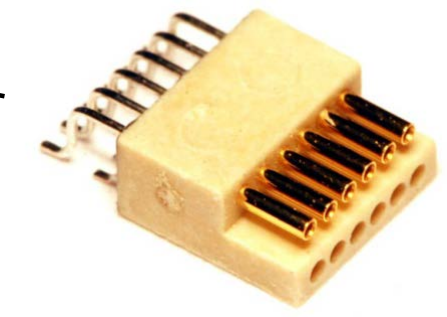
[picture p103: figure]

Omnetics A79623 connector
