jonnew/ONIX/headstage/assembly/bottom_with-mating-connectors.jpg

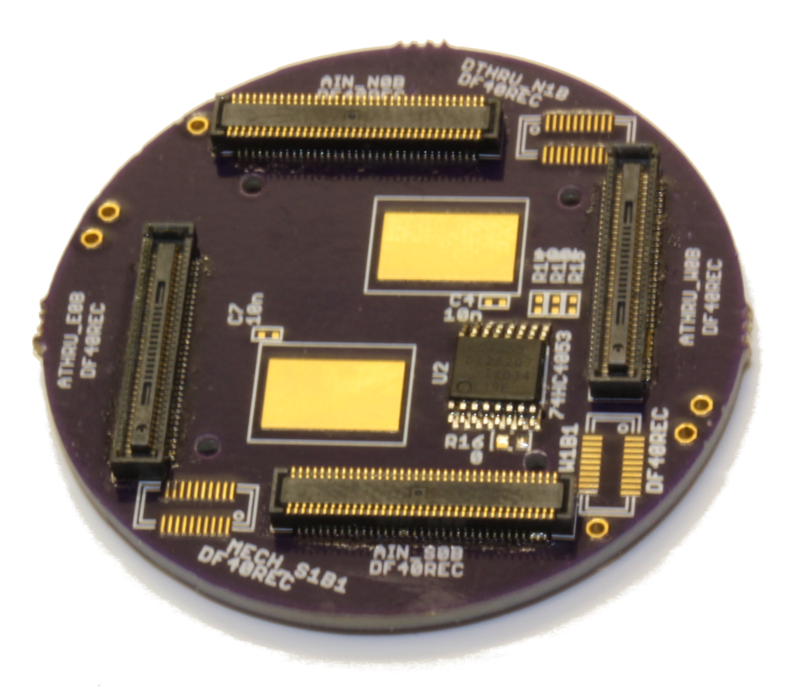
headstage/assembly/bottom_with-mating-connectors.jpg
