jonnew/ONIX/headstage/assembly/rev1.0_top.jpg

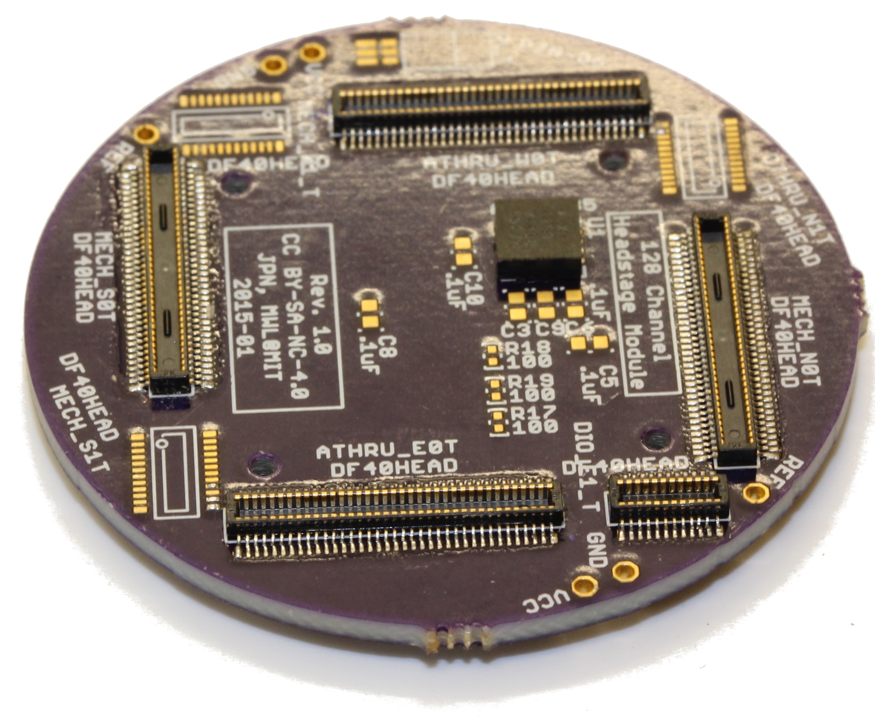
headstage/assembly/rev1.0_top.jpg
