jonnew/ONIX/2x64_Hirose_Circular/assembly/top_dmm-test.pdf

# Suggested pre-epoxy tests using digital multimeter (DMM) Page 1 of 2, PCB Top

Note: It may be easier to perform tests by inserting extra 70-pin headers into the 70 pin recepticals as shown in the picture. This exposes the solder pads of the 70-pin headers for DMM access.

### 8 orange pins: Test using DMM in ohmmeter

mode. Should have < 1Ω to GND test points

### 8 orange pins: Test using DMM in ohmmeter

mode. Should have < 1Ω to REF test points

128 red pins: Test using DMM in diode test mode. Touch the red lead to the GND test point. Touch the black lead to each of these pins. Diode test should return voltage in 0.6-0.8V range.
REF

GND

VCC

REF
GND
VCC
