jonnew/ONIX/headstage-64/revisions/rev-1.3/speedy-fab-files/README.md

## Speedy Circuits Fabrication Files

- These are the post-fabrication files of headstage-64 rev. 1.3 from [Speedy
  Circuits](http://www.speedy-circuits.com.tw/)
- Order number: M212I00018A83
- Board Specs:
  - Layer count: 8
  - Board thickness: 0.8 mm
  - BGA: Yes
  - Base Material: FR4
  - Smallest holes size: 0.1 mm
  - Holes per pc:  ~500 (Using all laser drills with plate shut process)
  - Solder mask: Green x 2 sides, < 1 mil resolution if possible
  - Silk screen: White x 2 sides
  - Min. traces/space: 2/2 mils
  - Board Finished: ENIG
  - Impedance controlled: No required
  - Blind vias: Yes (layers 1-6, 7-8)
  - Filled vias: Yes
  - Via in pad: Yes
