jonnew/ONIX/eib-64/revisions/rev-1.2/gerber-panel/README_HOLE_SIZES.png

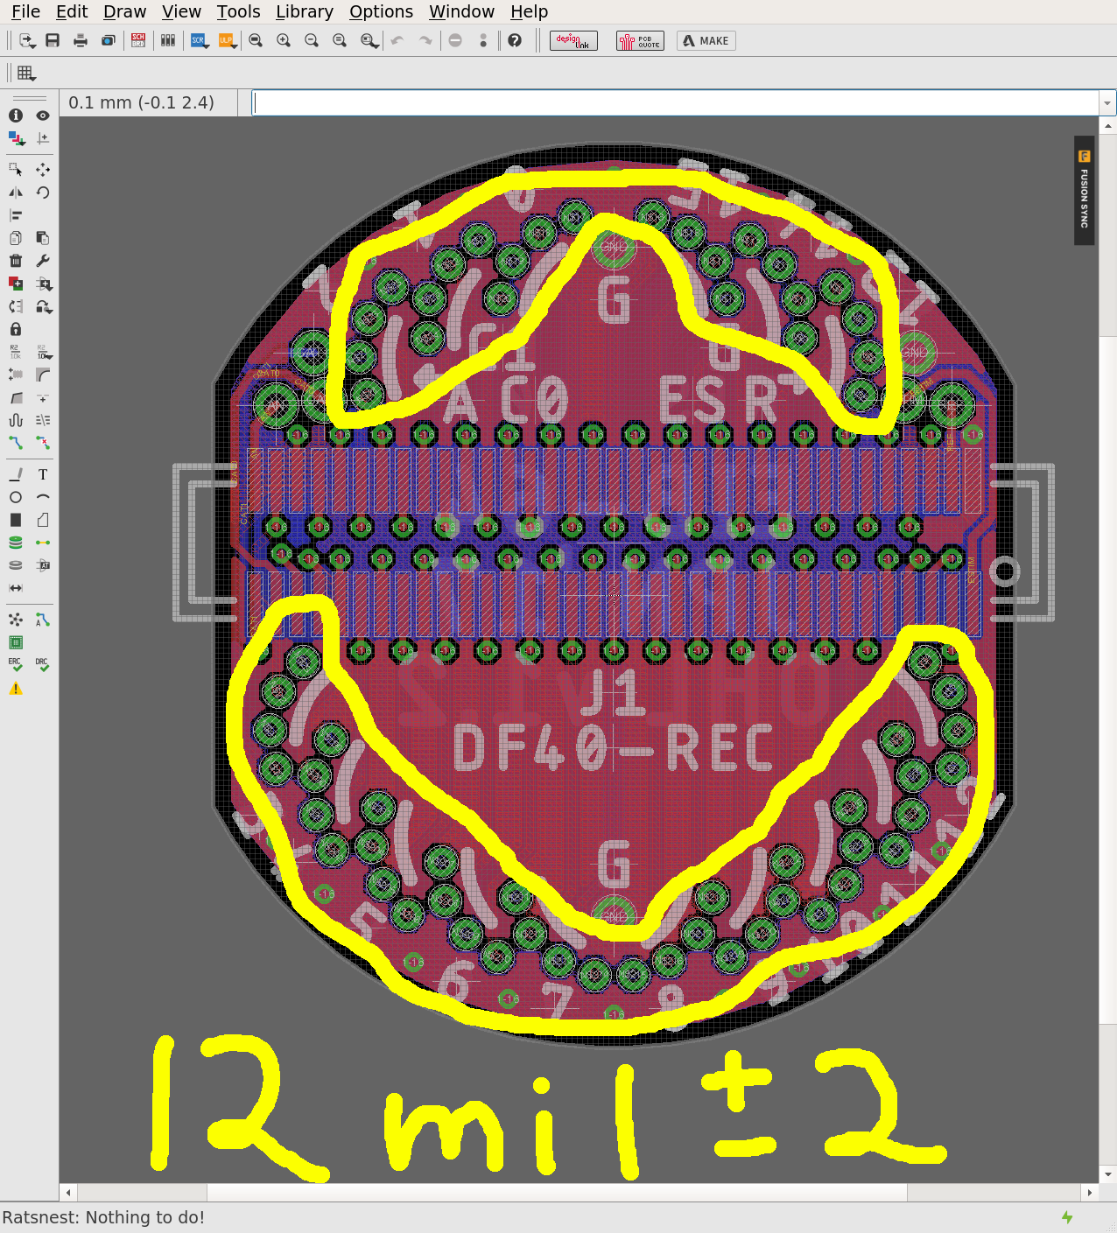
eib-64/revisions/rev-1.2/gerber-panel/README_HOLE_SIZES.png
