jonnew/ONIX/fmc-host/revisions/rev-1.4/gerber/tiles-bw.png

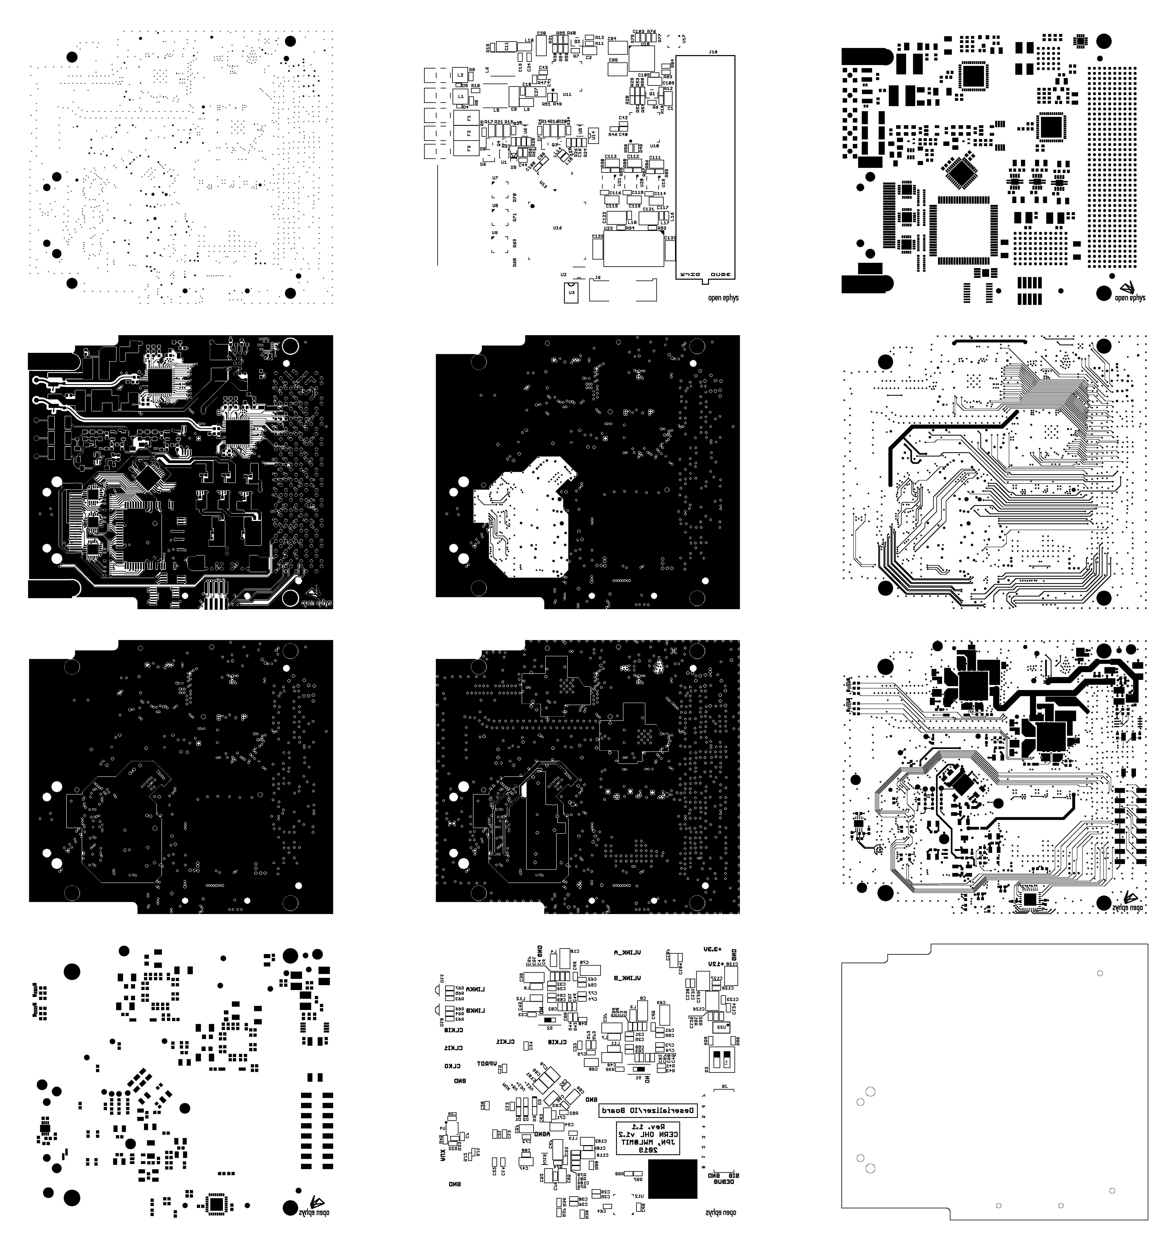
fmc-host/revisions/rev-1.4/gerber/tiles-bw.png
