jonnew/ONIX/headstage-64/revisions/rev-1.3/gerber/README_tab-placement.png

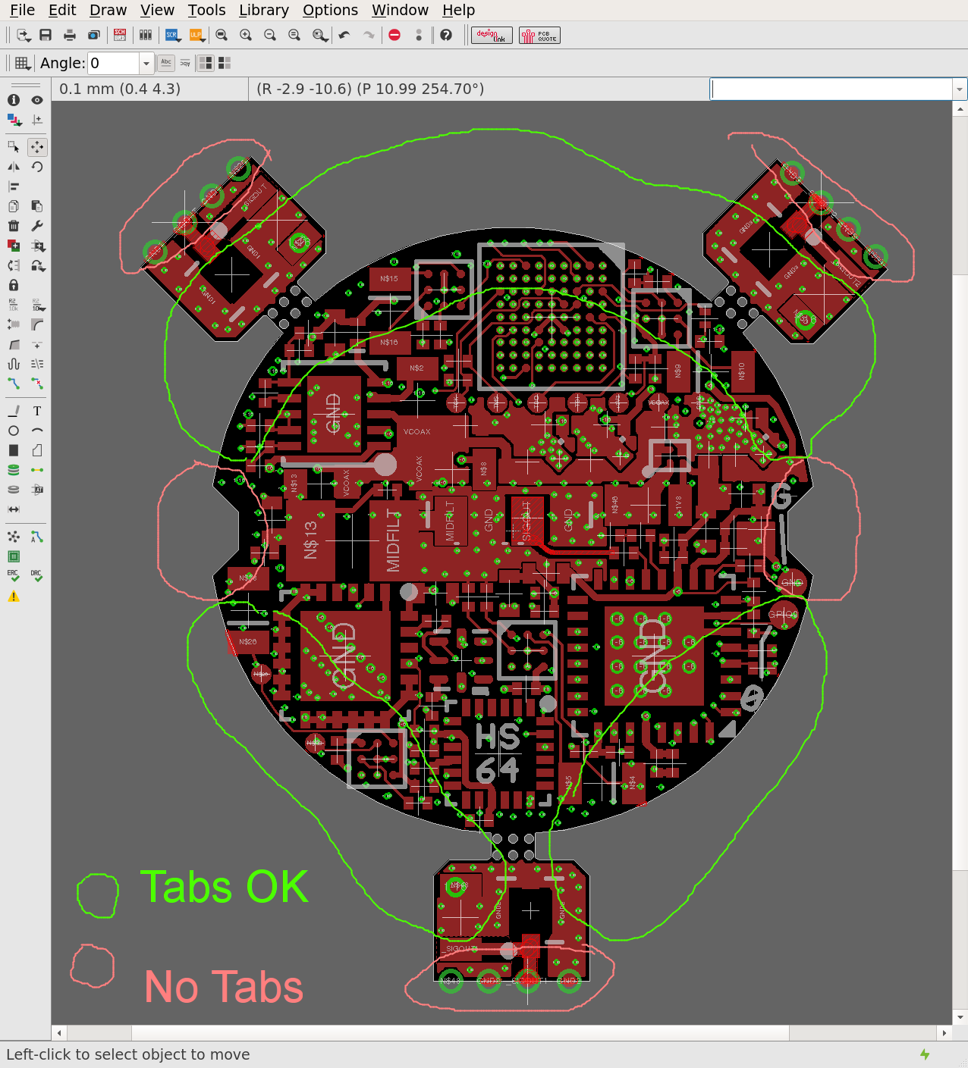
headstage-64/revisions/rev-1.3/gerber/README_tab-placement.png
