jonnew/ONIX/omnetics-spi-wire-adapter/RHD2000_cable_adapt_schematic.pdf

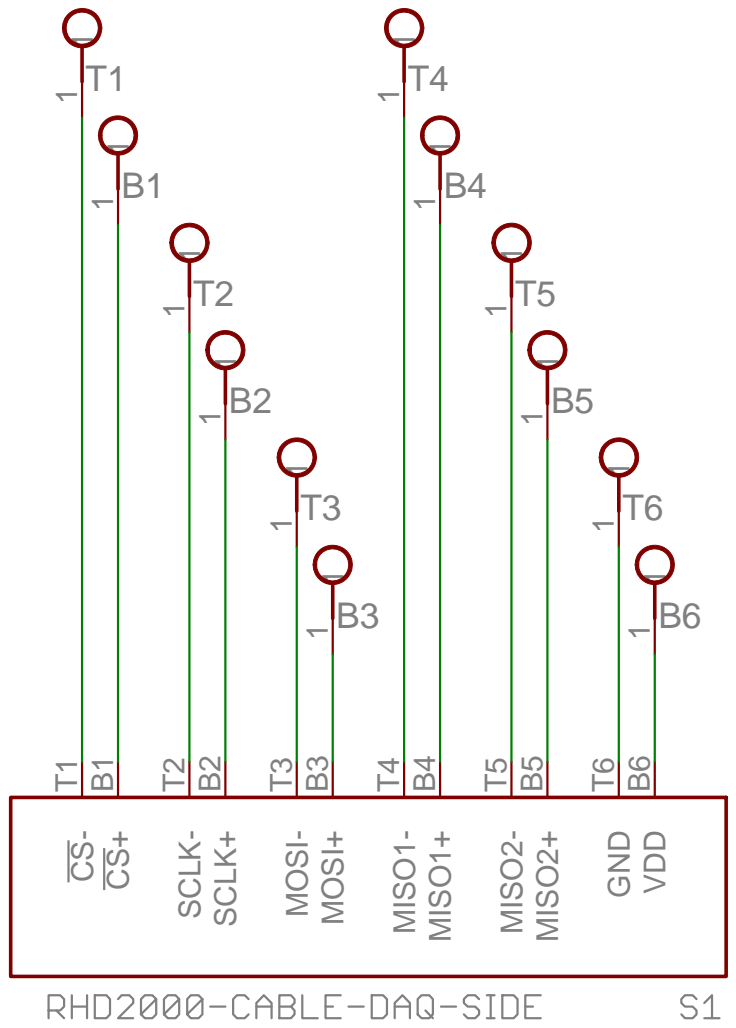
[picture p110: page 1]
MISO2- T5; MISO1+ B4; MISO2+ B5; VDD B6 GND T6; MOSI- T3; SCLK+ B2; MISO1- T4; MOSI+ B3; SCLK- T2

3/14/2013 5:38:04 PM f=1.08 C:\Users\Reid\Documents\PC Boards\RHD2000 Cable Adapter\RHD2000_cable_adapt.sch (Sheet: 1/1)
