jonnew/ONIX/headstage/assembly/bottom_assembly.pdf

# Bottom Components (16 total)

## page 3 of 7

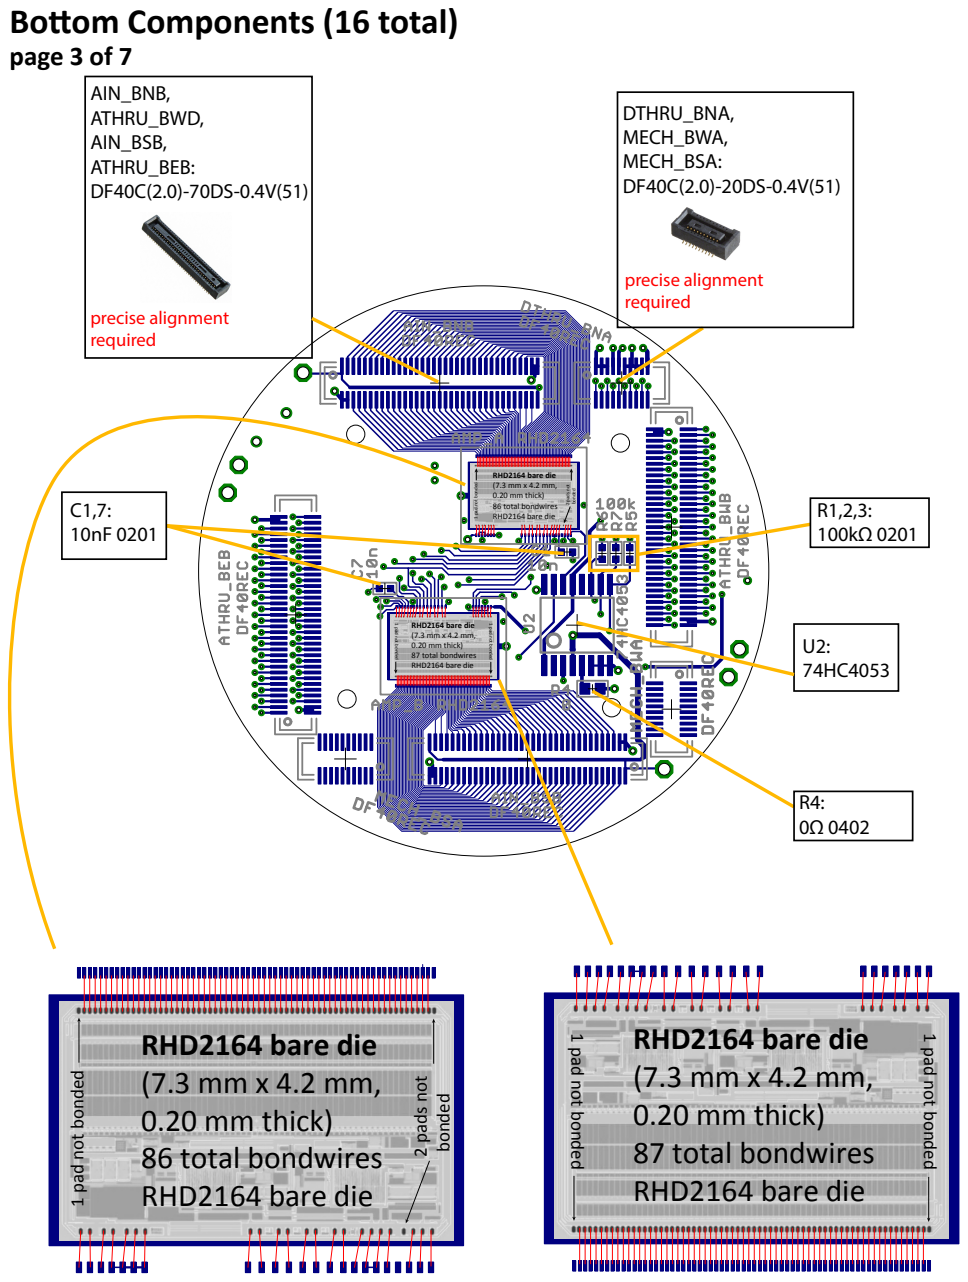
[picture p111: page 1]
RHD2164 bare die (7.3 mm x 4.2 mm, 0.20 mm thick) 86 total bondwires RHD2164 bare die; 2 pads not bonded; RHD2164 bare die (7.3 mm x 4.2 mm, 0.20 mm thick) 87 total bondwires RHD2164 bare die; AIN_BNB, ATHRU_BWD, AIN_BSB, ATHRU_BEB: DF40C(2.0)-70DS-0.4V(51); DTHRU_BNA, MECH_BWA, MECH_BSA: DF40C(2.0)-20DS-0.4V(51); precise alignment

required precise alignment
required

1 pad not bonded
