jonnew/ONIX/headstage/assembly/headstage_true-size.pdf

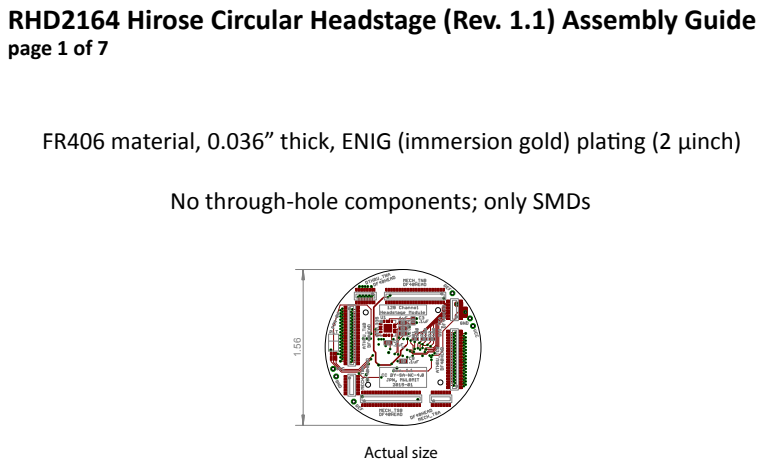
[picture p112: page 1]
Actual size

RHD2164 Hirose Circular Headstage (Rev. 1.1) Assembly Guide
page 1 of 7

FR406 material, 0.036” thick, ENIG (immersion gold) plating (2 μinch)

No through-hole components; only SMDs
