jonnew/ONIX/headstage/assembly/top_assembly.pdf

# Top Components (19 total)

## page 2 of 7

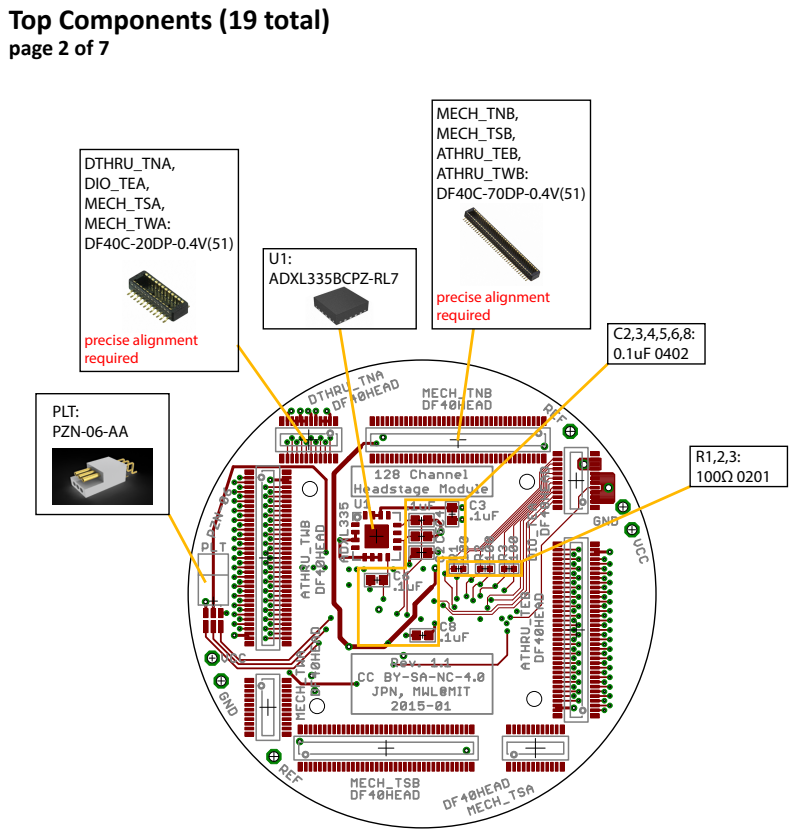
[picture p113: page 1]
U1: ADXL335BCPZ-RL7; MECH_TNB, MECH_TSB, ATHRU_TEB, ATHRU_TWB: DF40C-70DP-0.4V(51); DTHRU_TNA, DIO_TEA, MECH_TSA, MECH_TWA: DF40C-20DP-0.4V(51); PLT: PZN-06-AA; precise alignment required
