jonnew/ONIX/headstage/headstage_pcb.pdf

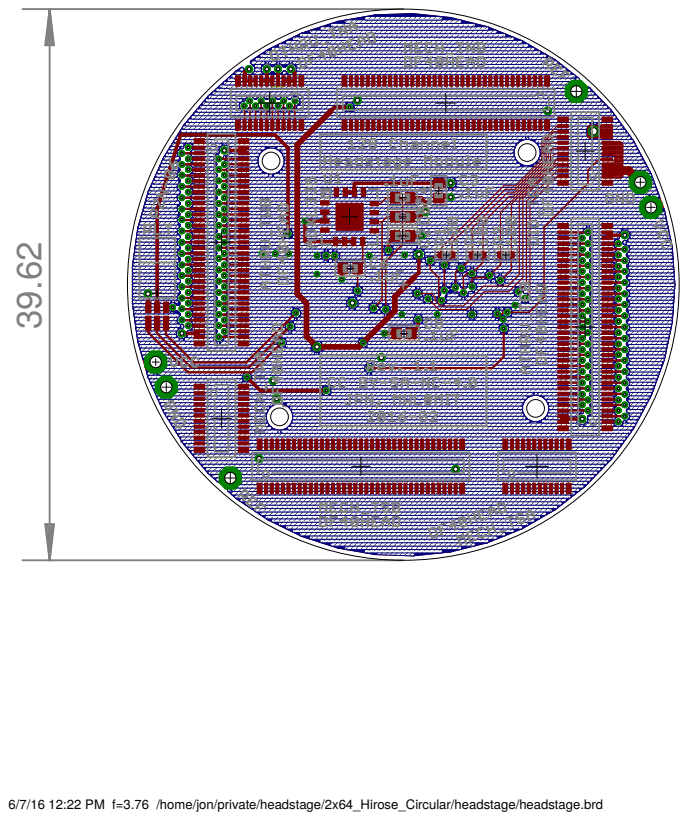
[picture p115: page 1]

6/7/16 12:22 PM f=3.76 /home/jon/private/headstage/2x64_Hirose_Circular/headstage/headstage.brd
