jonnew/ONIX/headstage-64/revisions/rev-1.3/spice/lt3463.asc

C1: cap; 4.7µ
C2: cap; 1µ
C3: cap; 10p
C4: cap; 0.1µ
C5: cap; 1µ
D2: schottky; B540C
L1: ind; 10µ
L2: ind; 10µ
R1: res; 4.53Meg
R2: res; 301k
R3: res; 280k
R4: res; 4.53Meg
R5: res; 100
R6: res; 100
U1: LT3463
V1: voltage; +5
Named nets: 0, +5v, V-, v+
.tran 0 10m 0 1u uic
