jonnew/ONIX/headstage-64/revisions/rev-1.3/spice/lt3472.asc

C1: cap; 10n
C2: cap; 10n
C3: cap; 4.7p
C4: cap; 2.2µ
C5: cap; 10p
C6: cap; 2.2µ
C7: cap; 1µ
L1: ind; 22µ
L2: ind2; 47µ
L3: ind2; 47µ
R1: res; 550K
R2: res; 320K
Rload1: res; 750
Rload2: res; 160
U1: LT3472
V1: voltage; 3.6
Named nets: 0, IN, OUT1, OUT2
.tran 1.5m startup
K1 L2 L3 1
