jonnew/ONIX/lighthouse-booster/spice/drive-circuit.asc

C1: cap; 220µF; V=16 Rser=0
C2: cap; 1100µ; Rser=0.2
C3: cap; 0.1µ
C4: cap; 220µF; V=16 Rser=0
C5: cap; 1100µ; Rser=0.2
C6: cap; 220µF; V=16 Rser=0
C7: cap; 1100µ; Rser=0.2
C8: cap; 220µF; V=16 Rser=0
C9: cap; 1100µ; Rser=0.2
C10: cap; 220µF; V=16 Rser=0
C11: cap; 1100µ; Rser=0.2
C12: cap; 220µF; V=16 Rser=0
C13: cap; 1100µ; Rser=0.2
C14: cap; 220µF; V=16 Rser=0
C15: cap; 1100µ; Rser=0.2
C16: cap; 220µF; V=16 Rser=0
C17: cap; 1100µ; Rser=0.2
C18: cap; 0.1µ
C19: cap; 100µF
D1: diode; F3583W
D2: diode; F3583W
D3: diode; F3583W
D4: diode; F3583W
D5: diode; F3583W
D6: diode; F3583W
D7: diode; F3583W
D8: diode; F3583W
D9: diode; F3583W
D10: diode; F3583W
D11: diode; F3583W
D12: diode; F3583W
D13: diode; F3583W
D14: diode; F3583W
D15: diode; F3583W
D16: diode; F3583W
D17: diode; F3583W
D18: diode; F3583W
D19: diode; F3583W
D20: diode; F3583W
D21: diode; F3583W
D22: diode; F3583W
D23: diode; F3583W
D24: diode; F3583W
D25: diode; F3583W
D26: diode; F3583W
D27: diode; F3583W
D28: diode; F3583W
D29: diode; F3583W
D30: diode; F3583W
D31: diode; F3583W
D32: diode; F3583W
D33: diode; F3583W
D34: diode; F3583W
D35: diode; F3583W
D36: diode; F3583W
D37: diode; F3583W
D38: diode; F3583W
D39: diode; F3583W
D40: diode; F3583W
D41: diode; F3583W
D42: diode; F3583W
D43: diode; F3583W
D44: diode; F3583W
D45: diode; F3583W
D46: diode; F3583W
D47: diode; F3583W
D48: diode; F3583W
D49: diode; F3583W
D50: diode; F3583W
D51: diode; F3583W
D52: diode; F3583W
D53: diode; F3583W
D54: diode; F3583W
D55: diode; F3583W
D56: diode; F3583W
D57: diode; F3583W
D58: diode; F3583W
D59: diode; F3583W
D60: diode; F3583W
D61: diode; F3583W
D62: diode; F3583W
D63: diode; F3583W
D64: diode; F3583W
D65: diode; F3583W
D66: diode; F3583W
D67: diode; F3583W
D68: diode; F3583W
D69: diode; F3583W
D70: diode; F3583W
D71: diode; F3583W
D72: diode; F3583W
D73: diode; F3583W
D74: diode; F3583W
D75: diode; F3583W
D76: diode; F3583W
D77: diode; F3583W
D78: diode; F3583W
D79: diode; F3583W
D80: diode; F3583W
D81: diode; F3583W
D82: diode; F3583W
D83: diode; F3583W
D84: diode; F3583W
D85: diode; F3583W
D86: diode; F3583W
D87: diode; F3583W
D88: diode; F3583W
D89: diode; F3583W
D90: diode; F3583W
D91: diode; F3583W
D92: diode; F3583W
D93: diode; F3583W
D94: diode; F3583W
D95: diode; F3583W
D96: diode; F3583W
D97: diode; F3583W
D98: diode; F3583W
D99: diode; F3583W
D100: diode; F3583W
D101: diode; F3583W
D102: diode; F3583W
D103: diode; F3583W
D104: diode; F3583W
D105: diode; F3583W
D106: diode; F3583W
D107: diode; F3583W
D108: diode; F3583W
D109: diode; F3583W
D110: diode; F3583W
D111: diode; F3583W
D112: diode; F3583W
D113: diode; F3583W
D114: diode; F3583W
D115: diode; F3583W
D116: diode; F3583W
D117: diode; F3583W
D118: diode; F3583W
D119: diode; F3583W
D120: diode; F3583W
L1: ind; 10n
M1: nmos; BSZ035N03LS
M2: nmos; BSZ035N03LS
M3: pmos; AON7407
M4: nmos; BSZ035N03LS
M5: nmos; BSZ035N03LS
M6: nmos; BSZ035N03LS
M7: nmos; BSZ035N03LS
M8: nmos; BSZ035N03LS
M9: nmos; BSZ035N03LS
R1: res; 0.18
R2: res; 0.18
R3: res; 0.2
R4: res; 0.18
R5: res; 0.18
R6: res; 0.18
R7: res; 0.18
R8: res; 0.18
R9: res; 0.18
R10: res; 0.18
R11: res; 0.18
R12: res; 10
R13: res; 0.18
R14: res; 0.18
R15: res; 0.18
R16: res; 0.18
R17: res; 0.18
R18: res; 10
R19: res; 0.18
R20: res; 0.18
R21: res; 0.18
R22: res; 0.18
R23: res; 0.18
R24: res; 10
R25: res; 0.18
R26: res; 0.18
R27: res; 0.18
R28: res; 0.18
R29: res; 0.18
R30: res; 10
R31: res; 0.18
R32: res; 0.18
R33: res; 0.18
R34: res; 0.18
R35: res; 0.18
R36: res; 10
R37: res; 0.18
R38: res; 0.18
R39: res; 0.18
R40: res; 0.18
R41: res; 0.18
R42: res; 10
R43: res; 10
R44: res; 0.18
R45: res; 0.18
R46: res; 0.18
R47: res; 0.18
R48: res; 0.18
R49: res; 10
R50: res; 100k
U1: LTC1693-5
U2: LTC6993-2
V1: voltage; 5V; Rser=0.01
V2: voltage; PULSE(0 5 3m 2n 2n 250n 500n 200)
V4: voltage; 12V; Rser=0.01
Named nets: 0, SYNC, +12V, +12V_CHRG, +5V
.tran 0 10m 0
.model F3583W D (

+               IS =            5.34E-16

+               N =             3.186659616

+               RS =            0.272510378

+               IKF =           506.7107657

+               IBV =           5.00E-10

+               NBV =           70

+               IBVL =          1.00E-08

+               NBVL =          1

+               BV =            6

+               CJO =           2.95E-10

+               TT =            3.50E-08

+               EG =            1.46)
