jonnew/ONIX/lighthouse-booster/spice/drive-circuit-current-sink.asc

C1: cap; 44µF; V=16 Rser=0.01
C2: cap; 1000µ; Rser=0.1
C3: cap; 0.1µ
I1: current; PULSE(0 5 50u 10n 10n 250n 500n 200)
M2: pmos; AON7407
R2: res; 1
U1: LTC1693-5
V1: voltage; 12V; Rser=0.01
V3: voltage; PULSE(0 3.3 50u 2n 2n 100u 500n 1)
Named nets: 0
.tran 500u
