jonnew/ONIX/serdes-interface/spice/estim-bjt-a.asc

C1: cap; 1000p
Q1: pnp; 2N2907
R1: res; 50k
R2: res; 1Meg
U1: LT1008
V1: voltage; 5v
V2: voltage; PULSE(0 {Vctl} 2m 1n 1n 5m)
V3: voltage; -5V
Named nets: 0, Vctl
;op
.tran 0 10m 0 1u
.params Vctl=0
.step param Vctl LIST 1 2 3 4
