jonnew/ONIX/serdes-interface/spice/estim-inst-amp-ac-open-loop.asc

C1: cap; 100p
R1: res; 250
R2: res; {Rload}
R3: res; 5.5k
R4: res; 25k
R5: res; 25k
U1: LTC2057HV
U2: LT1167
V1: voltage; 18V
V2: voltage; -18V
V3: voltage; 3.3V
V4: voltage; 0V; AC 1
Named nets: V+18, V-18, 0, OUT, FB, INM
.ac dec 10 100 10Meg
.step dec param Rload 1000 100e3 1
