jonnew/ONIX/spi-interface/spice/led-drive-ciruit.asc

C1: cap; 10µ
D1: diode; MLE
D2: zener; PDZ10B
M2: nmos; AO3402
R1: res; 24
R2: res; 10
R3: res; 10k
V1: voltage; 10; Rser=5
V2: voltage; PULSE(0 10 1m 1u 1u 1m 3m); Rser=0
Named nets: 0, VLED
.inc AO3402.lib
.inc PDZ10B.lib
.inc XlampMLE-parallel.lib
.inc XlampMLES-series.lib
.tran 3m
