jonnew/ONIX/nanoz-adapter-64/revisions/rev-1.0/eib-64-nanoz-adapter.brd

## EAGLE design nanoz-adapter-64/revisions/rev-1.0/eib-64-nanoz-adapter.brd (2017-12-13)

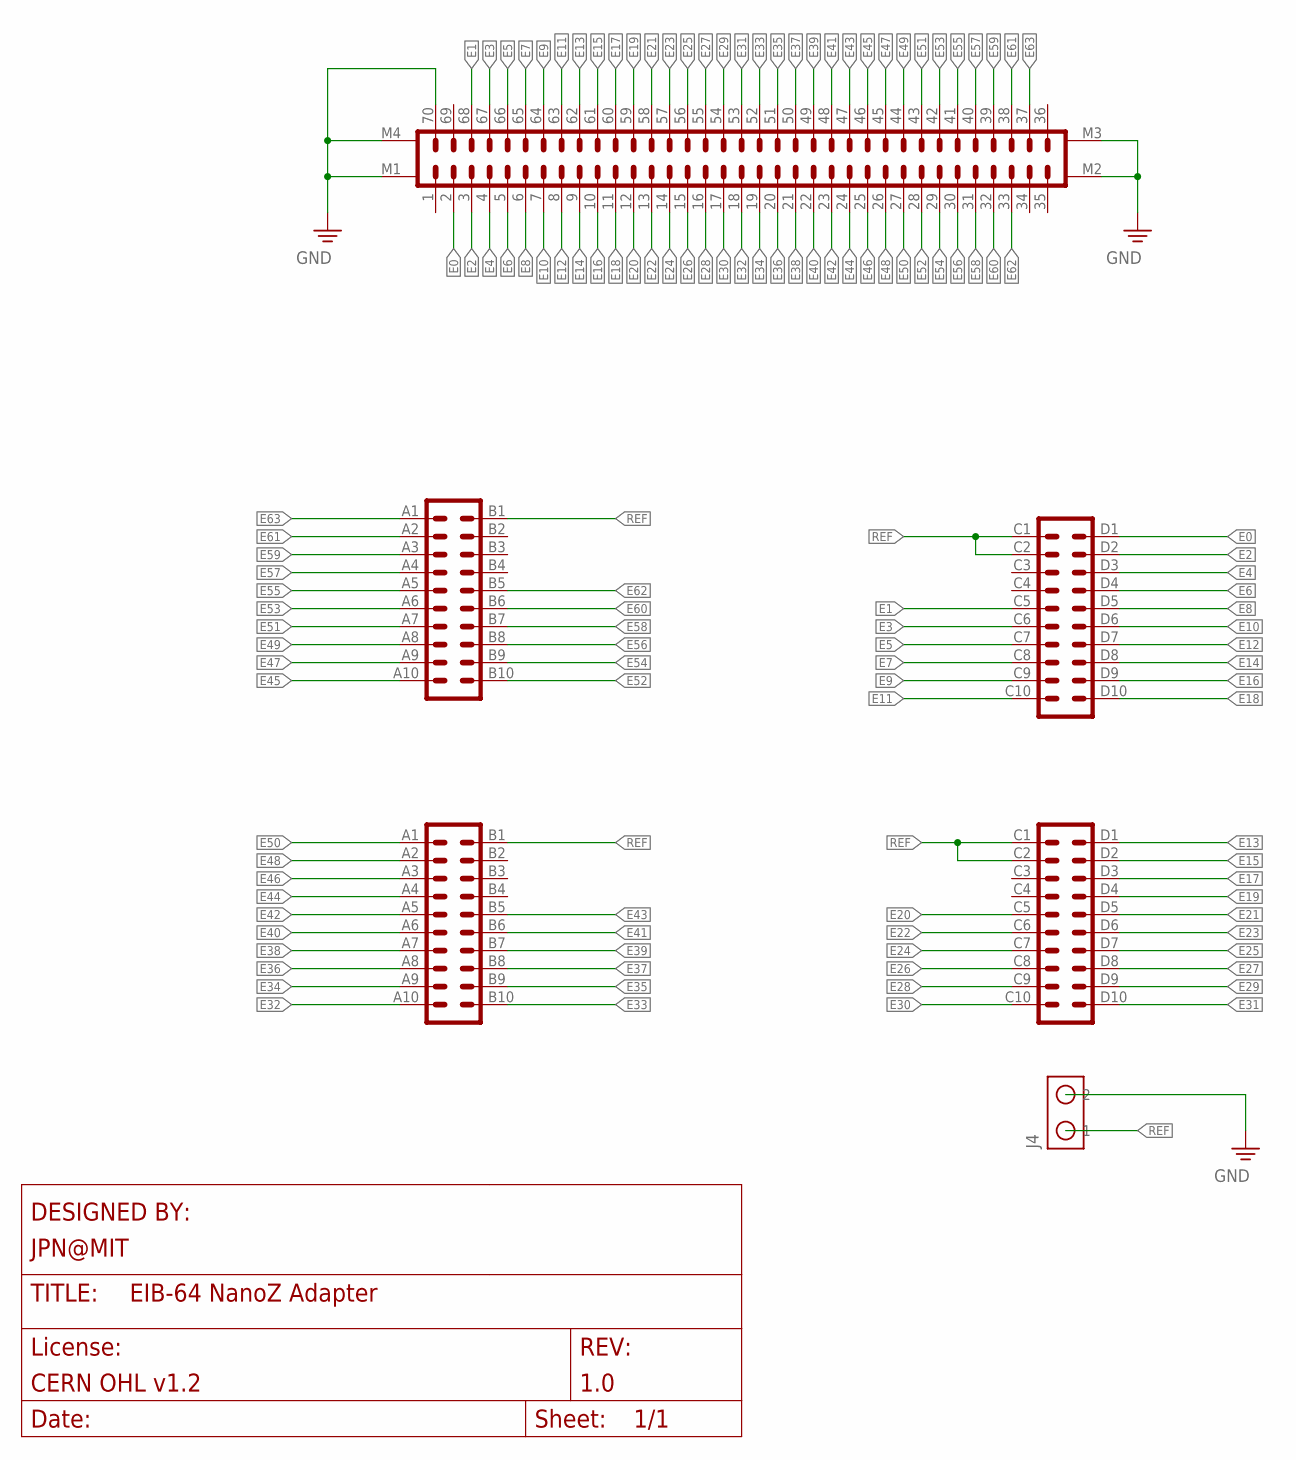
[picture p139: schematic eib-64-nanoz-adapter.sch]

Parts:
J1: DF40-REC; DF40-70HEAD
J2, J3: PINHD-4X10_MOLC-THRU; MOLC-110-11-S-Q
J4: SCREW2

Connections:
E0: J1.2, J2.D1 (20)
E1: J1.68, J2.C5 (5)
E2: J1.3, J2.D2 (19)
E3: J1.67, J2.C6 (6)
E4: J1.4, J2.D3 (18)
E5: J1.66, J2.C7 (7)
E6: J1.5, J2.D4 (17)
E7: J1.65, J2.C8 (8)
E8: J1.6, J2.D5 (16)
E9: J1.64, J2.C9 (9)
E10: J1.7, J2.D6 (15)
E11: J1.63, J2.C10 (10)
E12: J1.8, J2.D7 (14)
E13: J1.62, J3.D1 (20)
E14: J1.9, J2.D8 (13)
E15: J1.61, J3.D2 (19)
E16: J1.10, J2.D9 (12)
E17: J1.60, J3.D3 (18)
E18: J1.11, J2.D10 (11)
E19: J1.59, J3.D4 (17)
E20: J1.12, J3.C5 (5)
E21: J1.58, J3.D5 (16)
E22: J1.13, J3.C6 (6)
E23: J1.57, J3.D6 (15)
E24: J1.14, J3.C7 (7)
E25: J1.56, J3.D7 (14)
E26: J1.15, J3.C8 (8)
E27: J1.55, J3.D8 (13)
E28: J1.16, J3.C9 (9)
E29: J1.54, J3.D9 (12)
E30: J1.17, J3.C10 (10)
E31: J1.53, J3.D10 (11)
E32: J1.18, J3.A10 (10)
E33: J1.52, J3.B10 (11)
E34: J1.19, J3.A9 (9)
E35: J1.51, J3.B9 (12)
E36: J1.20, J3.A8 (8)
E37: J1.50, J3.B8 (13)
E38: J1.21, J3.A7 (7)
E39: J1.49, J3.B7 (14)
E40: J1.22, J3.A6 (6)
E41: J1.48, J3.B6 (15)
E42: J1.23, J3.A5 (5)
E43: J1.47, J3.B5 (16)
E44: J1.24, J3.A4 (4)
E45: J1.46, J2.A10 (10)
E46: J1.25, J3.A3 (3)
E47: J1.45, J2.A9 (9)
E48: J1.26, J3.A2 (2)
E49: J1.44, J2.A8 (8)
E50: J1.27, J3.A1 (1)
E51: J1.43, J2.A7 (7)
E52: J1.28, J2.B10 (11)
E53: J1.42, J2.A6 (6)
E54: J1.29, J2.B9 (12)
E55: J1.41, J2.A5 (5)
E56: J1.30, J2.B8 (13)
E57: J1.40, J2.A4 (4)
E58: J1.31, J2.B7 (14)
E59: J1.39, J2.A3 (3)
E60: J1.32, J2.B6 (15)
E61: J1.38, J2.A2 (2)
E62: J1.33, J2.B5 (16)
E63: J1.37, J2.A1 (1)
GND: J1.70, J1.M1, J1.M2, J1.M3, J1.M4, J4.P$2 (2)
REF: J2.B1 (20), J2.C1 (1), J2.C2 (2), J3.B1 (20), J3.C1 (1), J3.C2 (2), J4.P$1 (1)

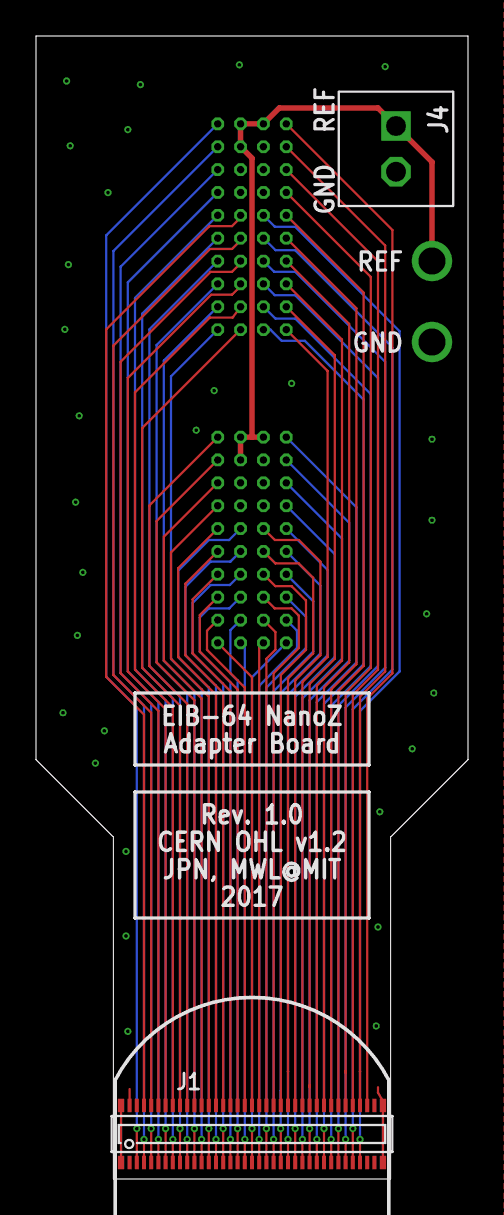
[picture p140: board eib-64-nanoz-adapter.brd from above]

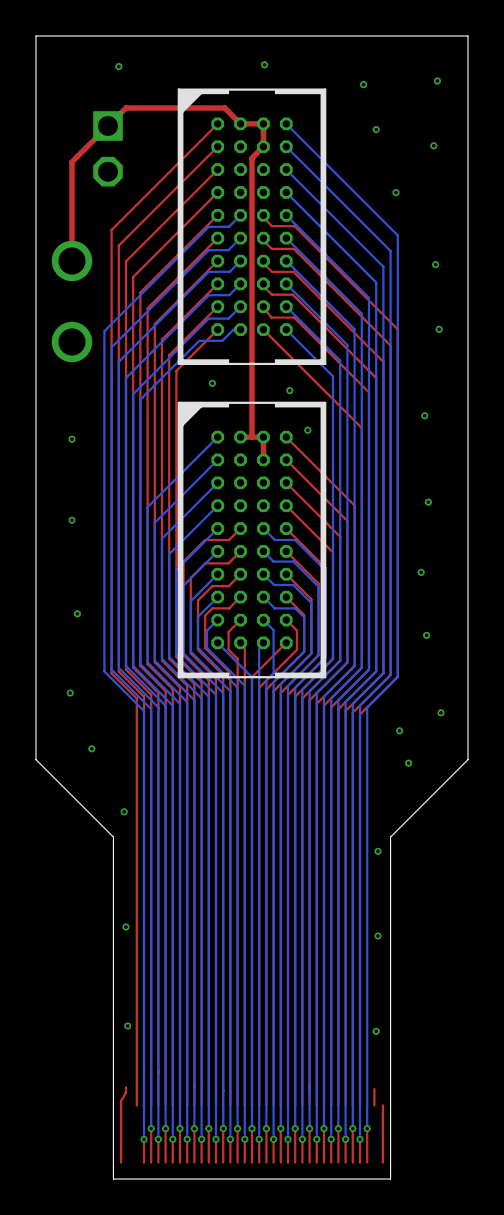
[picture p141: board eib-64-nanoz-adapter.brd from below]

Board: 4 copper layers, 24.0 x 63.5 mm, 4 parts (2 on the bottom side), 66 nets.
