jonnew/ONIX/eib-64-large/revisions/rev-1.0/eib-64-large.brd

## EAGLE design eib-64-large/revisions/rev-1.0/eib-64-large.brd (2019-12-16)

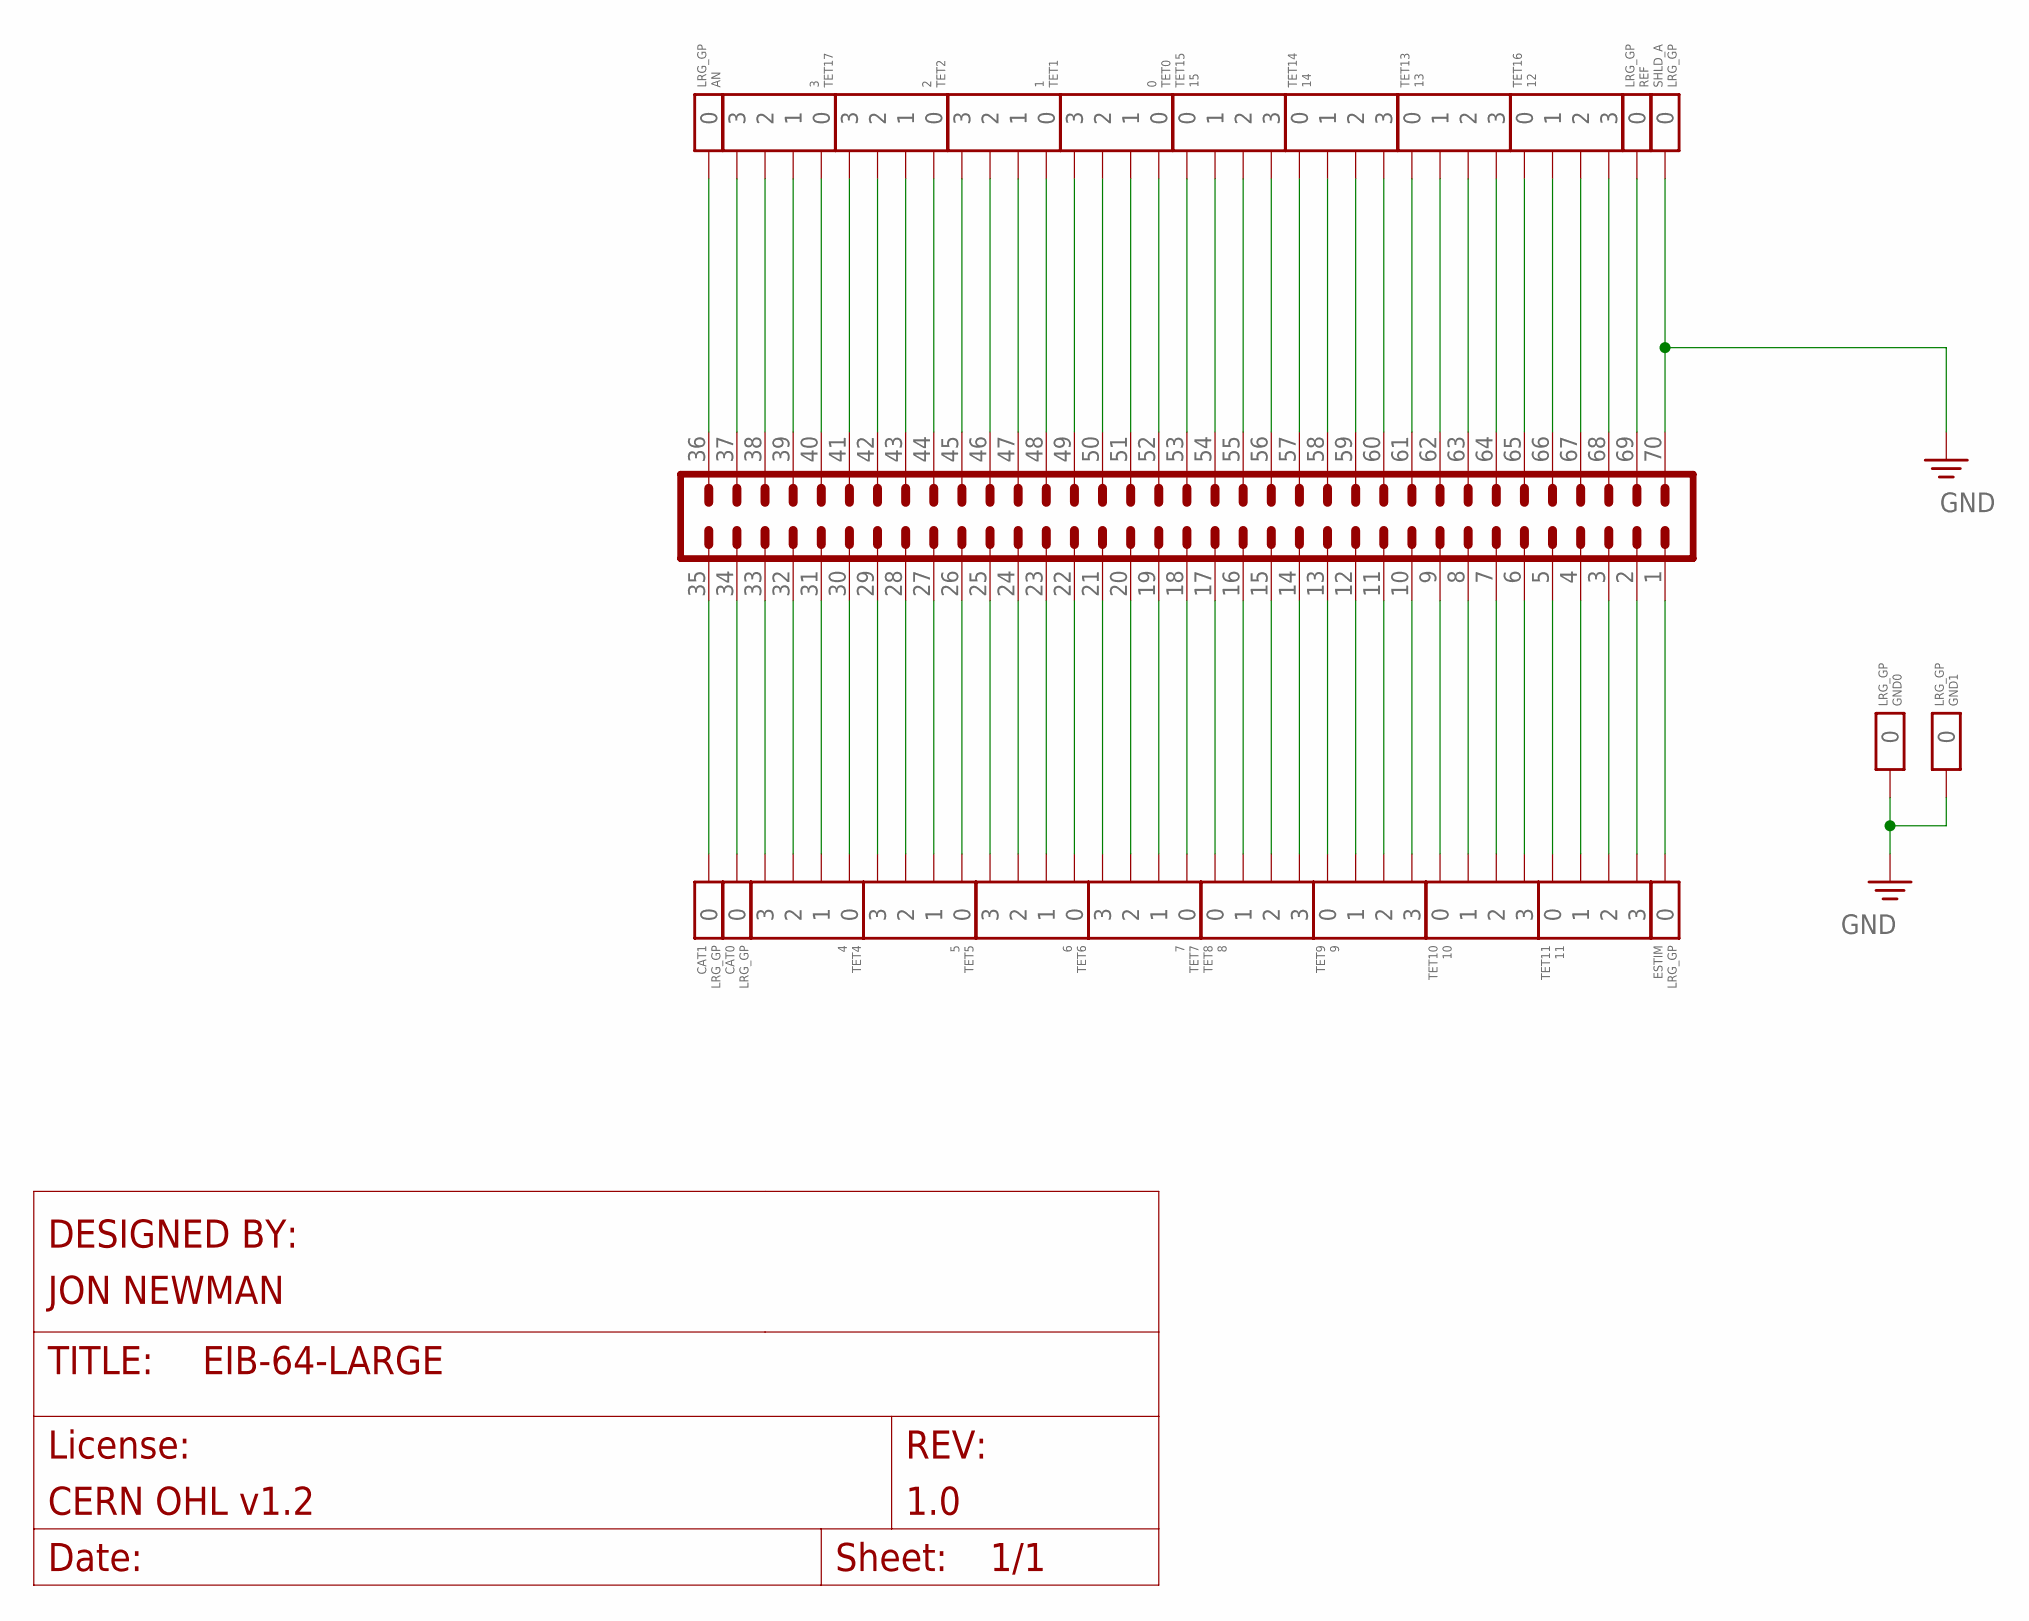
[picture p142: schematic eib-64-large.sch]

Parts:
AN: LRG_GP; GOLDPIN_0.5ID_0.7OD
CAT0, CAT1: LRG_GP; GOLDPIN_0.5ID_0.7OD
ESTIM: LRG_GP; GOLDPIN_0.5ID_0.7OD
GND0, GND1: LRG_GP; GOLDPIN_0.5ID_0.7OD
J1: DF40-REC; DDF40-70REC-LRG
REF: LRG_GP; GOLDPIN_0.5ID_0.7OD
SHLD_A: LRG_GP; GOLDPIN_0.5ID_0.7OD
TET0: 0; TETRODE_128_0.5ID_0.7OD
TET1: 1; TETRODE_128_0.5ID_0.7OD
TET2: 2; TETRODE_128_0.5ID_0.7OD
TET4: 4; TETRODE_128_0.5ID_0.7OD
TET5: 5; TETRODE_128_0.5ID_0.7OD
TET6: 6; TETRODE_128_0.5ID_0.7OD
TET7: 7; TETRODE_128_0.5ID_0.7OD
TET8: 8; TETRODE_128_0.5ID_0.7OD
TET9: 9; TETRODE_128_0.5ID_0.7OD
TET10: 10; TETRODE_128_0.5ID_0.7OD
TET11: 11; TETRODE_128_0.5ID_0.7OD
TET13: 13; TETRODE_128_0.5ID_0.7OD
TET14: 14; TETRODE_128_0.5ID_0.7OD
TET15: 15; TETRODE_128_0.5ID_0.7OD
TET16: 12; TETRODE_128_0.5ID_0.7OD
TET17: 3; TETRODE_128_0.5ID_0.7OD

Connections:
AN: AN.P$1, J1.36
CAT0: CAT0.P$1, J1.34
CAT1: CAT1.P$1, J1.35
ESTIM: ESTIM.P$1, J1.1
GND: GND0.P$1, GND1.P$1, J1.70, SHLD_A.P$1
unnamed: J1.68, TET16.3
unnamed: J1.65, TET16.0
unnamed: J1.66, TET16.1
unnamed: J1.67, TET16.2
unnamed: J1.64, TET13.3
unnamed: J1.63, TET13.2
unnamed: J1.62, TET13.1
unnamed: J1.61, TET13.0
unnamed: J1.60, TET14.3
unnamed: J1.59, TET14.2
unnamed: J1.58, TET14.1
unnamed: J1.57, TET14.0
unnamed: J1.56, TET15.3
unnamed: J1.55, TET15.2
unnamed: J1.54, TET15.1
unnamed: J1.53, TET15.0
unnamed: J1.52, TET0.0
unnamed: J1.51, TET0.1
unnamed: J1.50, TET0.2
unnamed: J1.49, TET0.3
unnamed: J1.48, TET1.0
unnamed: J1.47, TET1.1
unnamed: J1.46, TET1.2
unnamed: J1.45, TET1.3
unnamed: J1.44, TET2.0
unnamed: J1.43, TET2.1
unnamed: J1.42, TET2.2
unnamed: J1.41, TET2.3
unnamed: J1.40, TET17.0
unnamed: J1.39, TET17.1
unnamed: J1.38, TET17.2
unnamed: J1.37, TET17.3
unnamed: J1.5, TET11.0
unnamed: J1.4, TET11.1
unnamed: J1.3, TET11.2
unnamed: J1.2, TET11.3
unnamed: J1.33, TET4.3
unnamed: J1.32, TET4.2
unnamed: J1.31, TET4.1
unnamed: J1.30, TET4.0
unnamed: J1.29, TET5.3
unnamed: J1.28, TET5.2
unnamed: J1.27, TET5.1
unnamed: J1.26, TET5.0
unnamed: J1.25, TET6.3
unnamed: J1.24, TET6.2
unnamed: J1.23, TET6.1
unnamed: J1.22, TET6.0
unnamed: J1.21, TET7.3
unnamed: J1.20, TET7.2
unnamed: J1.19, TET7.1
unnamed: J1.18, TET7.0
unnamed: J1.17, TET8.0
unnamed: J1.16, TET8.1
unnamed: J1.15, TET8.2
unnamed: J1.14, TET8.3
unnamed: J1.13, TET9.0
unnamed: J1.12, TET9.1
unnamed: J1.11, TET9.2
unnamed: J1.10, TET9.3
unnamed: J1.9, TET10.0
unnamed: J1.8, TET10.1
unnamed: J1.7, TET10.2
unnamed: J1.6, TET10.3
REF: J1.69, REF.P$1

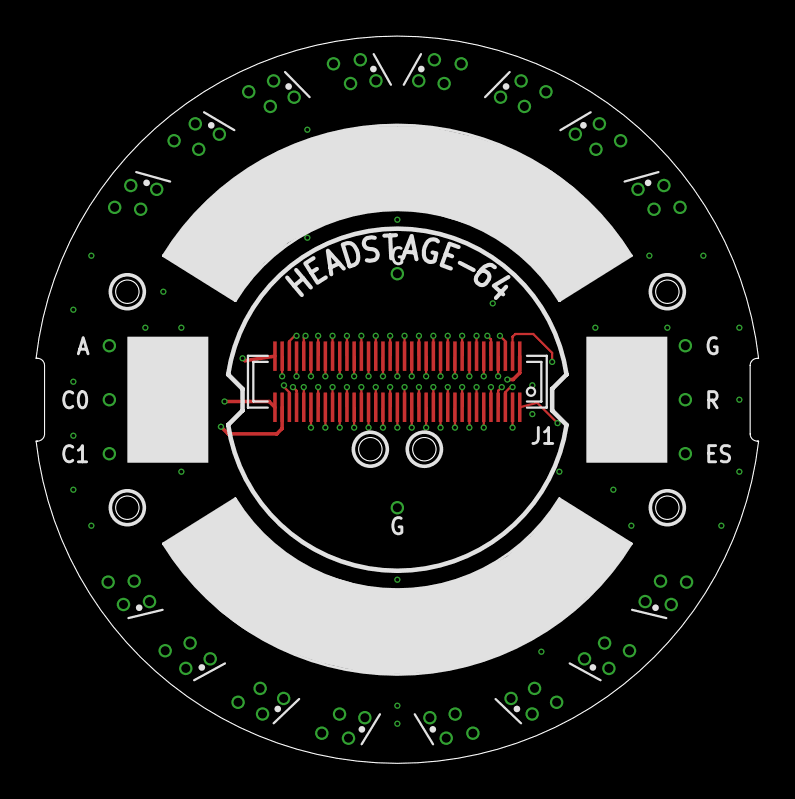
[picture p143: board eib-64-large.brd from above]

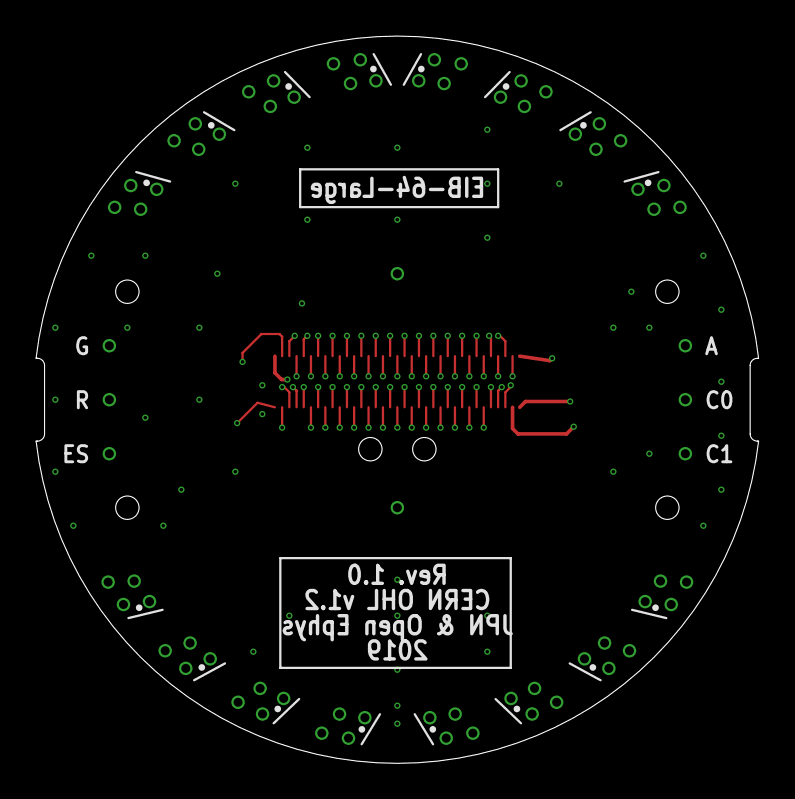
[picture p144: board eib-64-large.brd from below]

Board: 4 copper layers, 40.1 x 40.4 mm, 25 parts (8 on the bottom side), 70 nets.
