jonnew/ONIX/omnetics-adapter-64/revisions/rev-1.0/omnetics-adapter-64.brd

## EAGLE design omnetics-adapter-64/revisions/rev-1.0/omnetics-adapter-64.brd (2019-11-26)

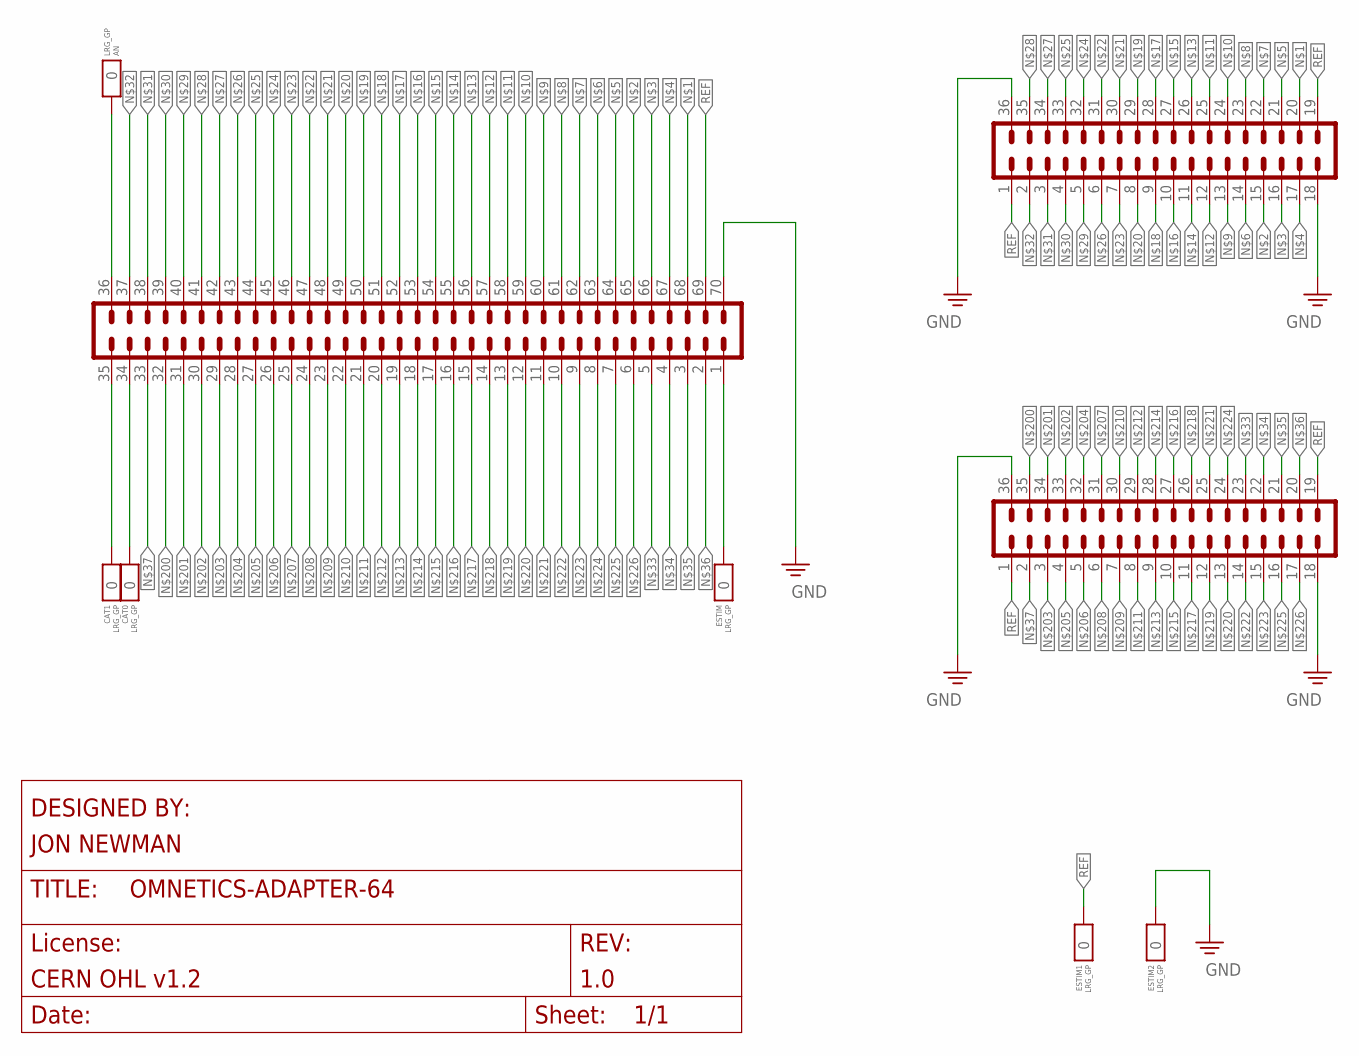
[picture p145: schematic omnetics-adapter-64.sch]

Parts:
AN: LRG_GP; GOLDPIN_0.5ID_0.7OD
CAT0, CAT1: LRG_GP; GOLDPIN_0.5ID_0.7OD
ESTIM, ESTIM1, ESTIM2: LRG_GP; GOLDPIN_0.5ID_0.7OD
J1: DF40-REC; DDF40-70REC-LRG
J2, J3: PINHD-2X18_NPD; NPD-36-VV-GS

Connections:
AN: AN.P$1, J1.36
CAT0: CAT0.P$1, J1.34
CAT1: CAT1.P$1, J1.35
ESTIM: ESTIM.P$1, J1.1
GND: ESTIM2.P$1, J1.70, J2.18, J2.36, J3.18, J3.36
unnamed: J1.68, J2.20
unnamed: J1.65, J2.15
unnamed: J1.66, J2.16
unnamed: J1.67, J2.17
unnamed: J1.64, J2.21
unnamed: J1.63, J2.14
unnamed: J1.62, J2.22
unnamed: J1.61, J2.23
unnamed: J1.60, J2.13
unnamed: J1.59, J2.24
unnamed: J1.58, J2.25
unnamed: J1.57, J2.12
unnamed: J1.56, J2.26
unnamed: J1.55, J2.11
unnamed: J1.54, J2.27
unnamed: J1.53, J2.10
unnamed: J1.52, J2.28
unnamed: J1.51, J2.9
unnamed: J1.50, J2.29
unnamed: J1.49, J2.8
unnamed: J1.48, J2.30
unnamed: J1.47, J2.31
unnamed: J1.46, J2.7
unnamed: J1.45, J2.32
unnamed: J1.44, J2.33
unnamed: J1.43, J2.6
unnamed: J1.42, J2.34
unnamed: J1.41, J2.35
unnamed: J1.40, J2.5
unnamed: J1.39, J2.4
unnamed: J1.38, J2.3
unnamed: J1.37, J2.2
unnamed: J1.5, J3.23
unnamed: J1.4, J3.22
unnamed: J1.3, J3.21
unnamed: J1.2, J3.20
unnamed: J1.33, J3.2
unnamed: J1.32, J3.35
unnamed: J1.31, J3.34
unnamed: J1.30, J3.33
unnamed: J1.29, J3.3
unnamed: J1.28, J3.32
unnamed: J1.27, J3.4
unnamed: J1.26, J3.5
unnamed: J1.25, J3.31
unnamed: J1.24, J3.6
unnamed: J1.23, J3.7
unnamed: J1.22, J3.30
unnamed: J1.21, J3.8
unnamed: J1.20, J3.29
unnamed: J1.19, J3.9
unnamed: J1.18, J3.28
unnamed: J1.17, J3.10
unnamed: J1.16, J3.27
unnamed: J1.15, J3.11
unnamed: J1.14, J3.26
unnamed: J1.13, J3.12
unnamed: J1.12, J3.13
unnamed: J1.11, J3.25
unnamed: J1.10, J3.14
unnamed: J1.9, J3.15
unnamed: J1.8, J3.24
unnamed: J1.7, J3.16
unnamed: J1.6, J3.17
REF: ESTIM1.P$1, J1.69, J2.1, J2.19, J3.1, J3.19

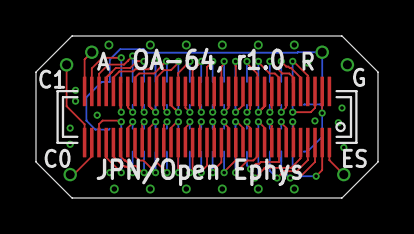
[picture p146: board omnetics-adapter-64.brd from above]

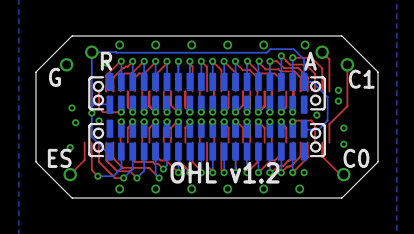
[picture p147: board omnetics-adapter-64.brd from below]

Board: 2 copper layers, 19.0 x 9.0 mm, 9 parts (2 on the bottom side), 70 nets.
