jonnew/ONIX/headstage-programmer/revisions/rev-1.2/headstage-programmer.brd

## EAGLE design headstage-programmer/revisions/rev-1.2/headstage-programmer.brd (2019-09-27, an earlier design)

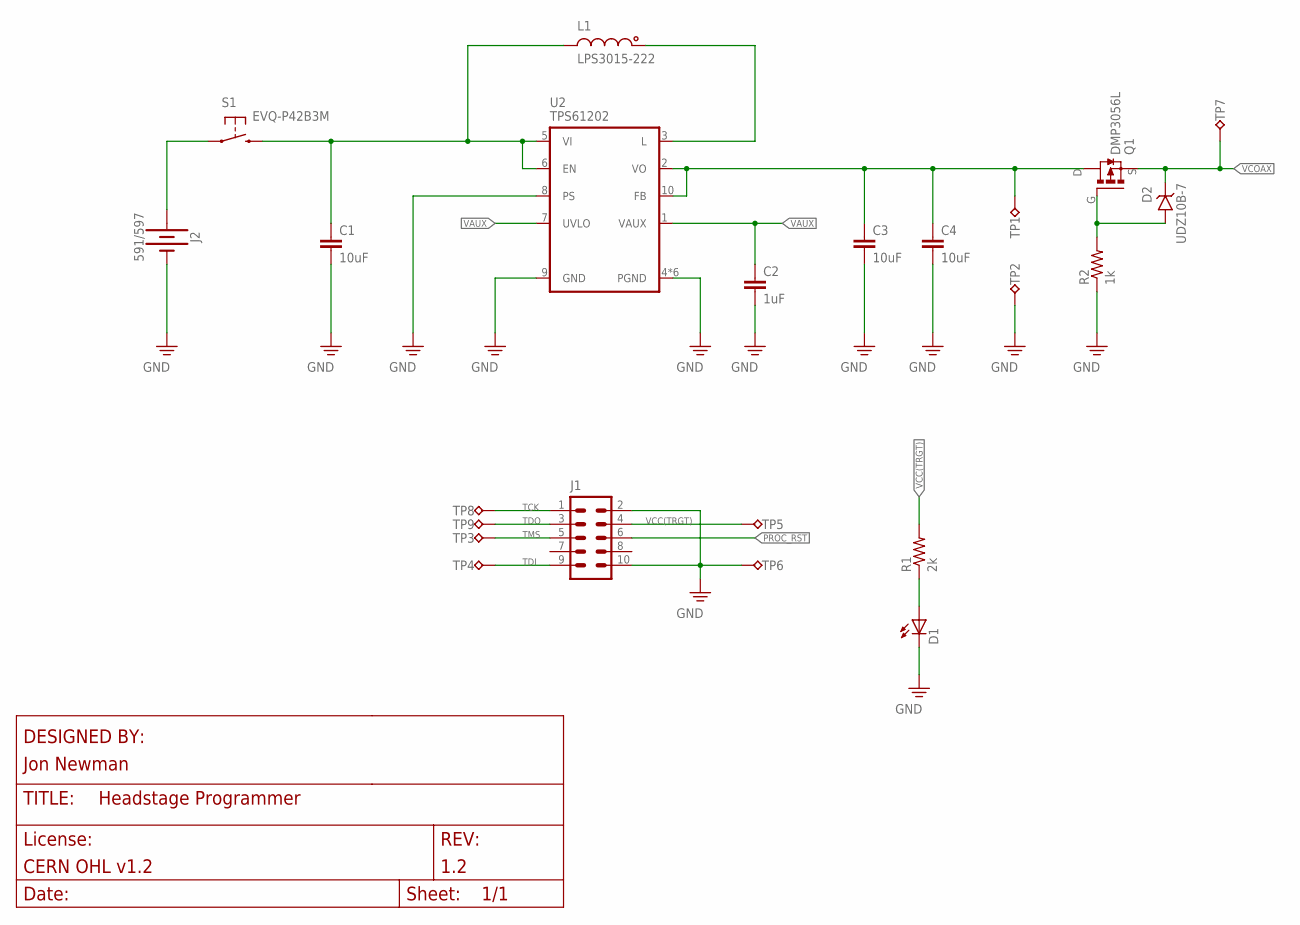
[picture p151: schematic headstage-programmer.sch]

Parts:
C1, C3, C4: 10uF; 0805
C2: 1uF; 0603
D1: LED_0603; LED-0603
D2: UDZ10B-7; SOD-323; PARTNO UDZ10B-7
J1: 302-S101; 2X05_IDC
J2: 591/597; 597/591_AAA-HOLDER
L1: LPS3015-222; LPS3015
Q1: DMP3056L; SOT23-GSD; PARTNO DMP3056L-7
R1: 2k; 0603
R2: 1k; 0603
S1: EVQ-P42B3M; EVQP4
TP1, TP2: TP_1MM; TESTPOINT_1MM
TP3, TP4, TP5, TP6, TP7, TP8, TP9: TP_S500-6350-P2; POGO_S500-6350-P2
U2: TPS61202; PWSON-N10+4-3X3

Connections:
GND: C1.2, C2.2, C3.2, C4.2, D1.C, J1.2, J1.10, J2.-1 (-), J2.-2 (-), J2.-3 (-), R2.1, TP2.1, TP6.P$1, U2.4 (PGND), U2.8 (PS), U2.9 (GND), U2.PAD (PGND), U2.PAD1 (PGND), U2.PAD2 (PGND), U2.PAD3 (PGND), U2.PAD4 (PGND)
unnamed: D1.A, R1.1
unnamed: L1.1, U2.3 (L)
unnamed: J2.+1 (+), J2.+2 (+), J2.+3 (+), S1.1
unnamed: D2.A, Q1.G, R2.2
PROC_RST: J1.6
TCK: J1.1, TP8.P$1
TDI: J1.9, TP4.P$1
TDO: J1.3, TP9.P$1
TMS: J1.5, TP3.P$1
VAUX: C2.1, U2.1 (VAUX), U2.7 (UVLO)
VCC(TRGT): J1.4, R1.2, TP5.P$1
VCOAX: D2.C, Q1.S, TP7.P$1
VIN: C1.1, L1.2, S1.2 (S), U2.5 (VI), U2.6 (EN)
VO: C3.1, C4.1, Q1.D, TP1.1, U2.2 (VO), U2.10 (FB)

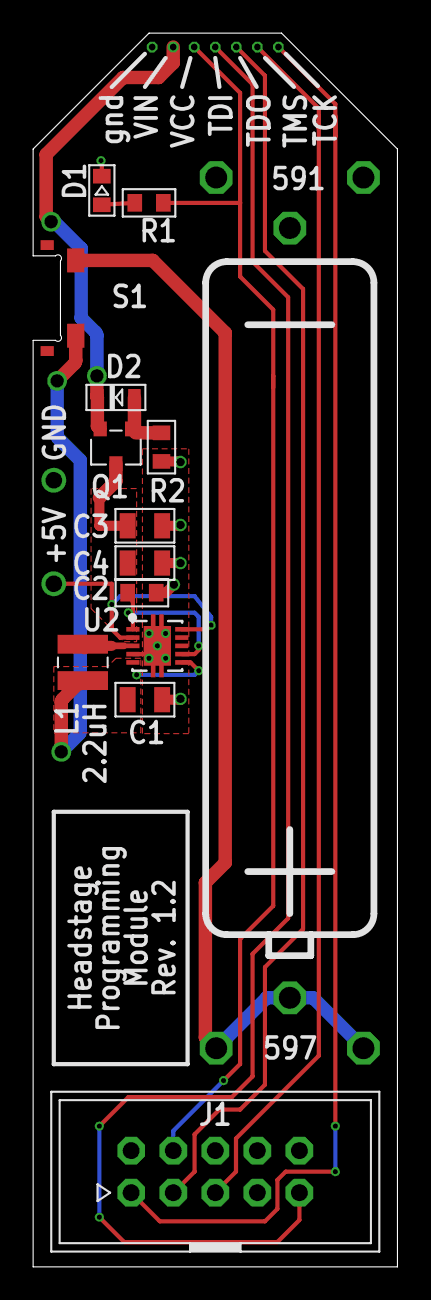
[picture p152: board headstage-programmer/revisions/rev-1.2/headstage-programmer.brd from above]

Board: 2 copper layers, 22.0 x 74.5 mm, 23 parts (0 on the bottom side), 14 nets.
