jonnew/ONIX/headstage-64/headstage-64-coax-adapter.brd

## EAGLE design headstage-64/headstage-64-coax-adapter.brd (2020-02-06)

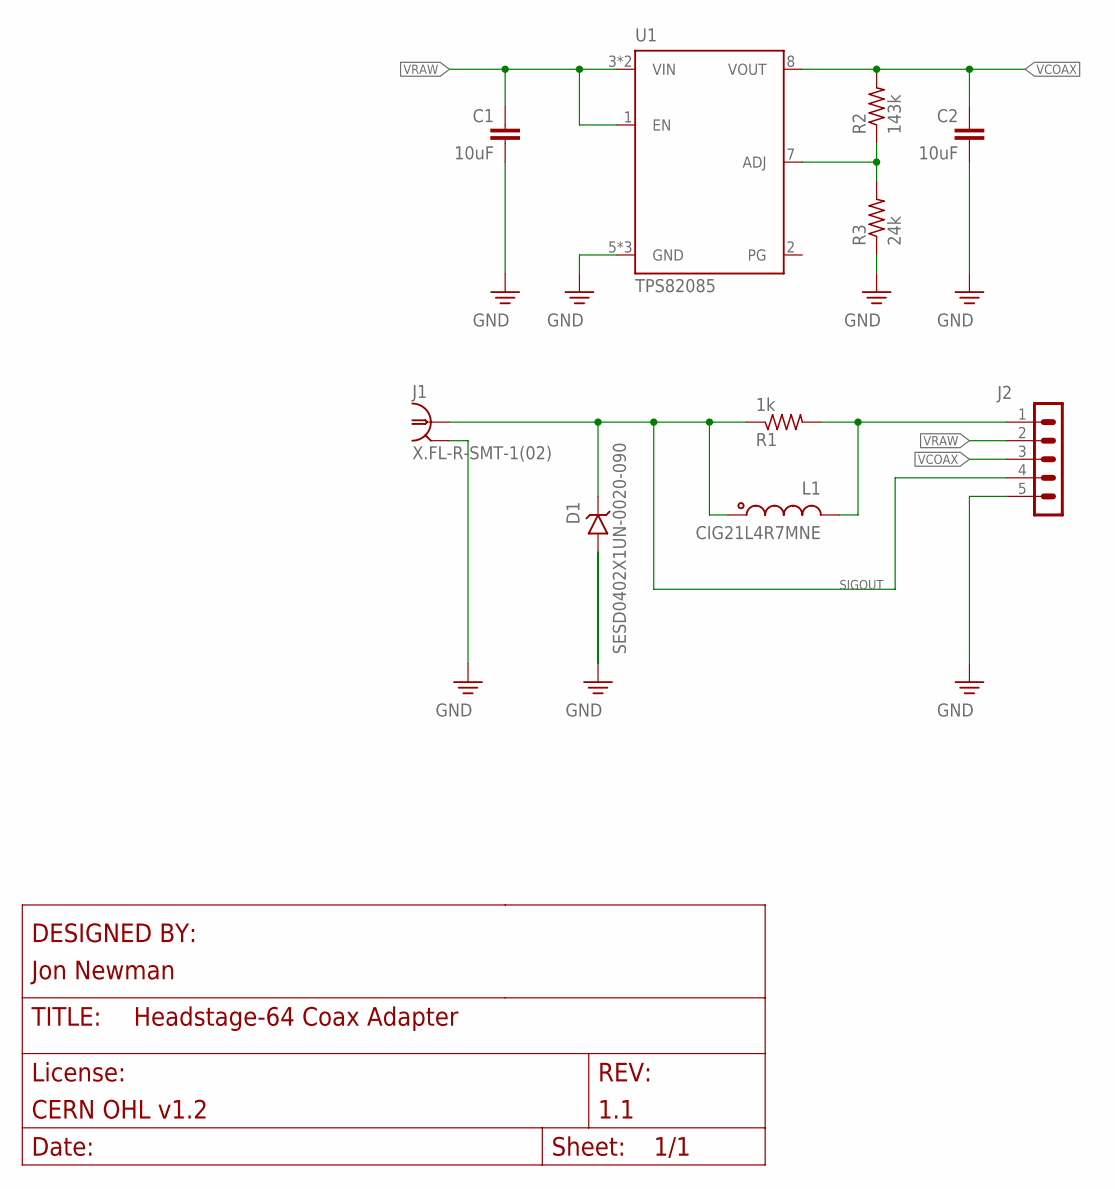
[picture p153: schematic headstage-64-coax-adapter.sch]

Parts:
C1, C2: 10uF; 0402T; PARTNO CL05A475MO5NUNC
D1: SESD0402X1UN-0020-090; 0402T-DFN
J1: X.FL-R-SMT-1(02); X_FL_R_SMT_1(02)
J2: PINHD-1X5_HEADSTAGE-64-REV1.4-DAUGHTER-CARD-CASTE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; HEADSTAGE-64-REV1.4-DAUGHTER-CARD-CASTELLATED
L1: CIG21L4R7MNE; 0805T
R1: 1k; 0201T
R2: 143k; 0201T
R3: 24k; 0201T
U1: TPS82085; MICROSIP9-2.8X3

Connections:
GND: C1.2, C2.2, D1.A, J1.P$2 (2), J1.P$3 (2), J1.P$4 (2), J2.5, R3.1, U1.5 (GND), U1.6 (GND), U1.PAD (GND)
unnamed: R2.1, R3.2, U1.7 (ADJ)
unnamed: J2.1, L1.2, R1.2
SIGOUT: D1.C, J1.P$1 (1), J2.4, L1.1, R1.1
VCOAX: C2.1, J2.3, R2.2, U1.8 (VOUT)
VRAW: C1.1, J2.2, U1.1 (EN), U1.3 (VIN), U1.4 (VIN)

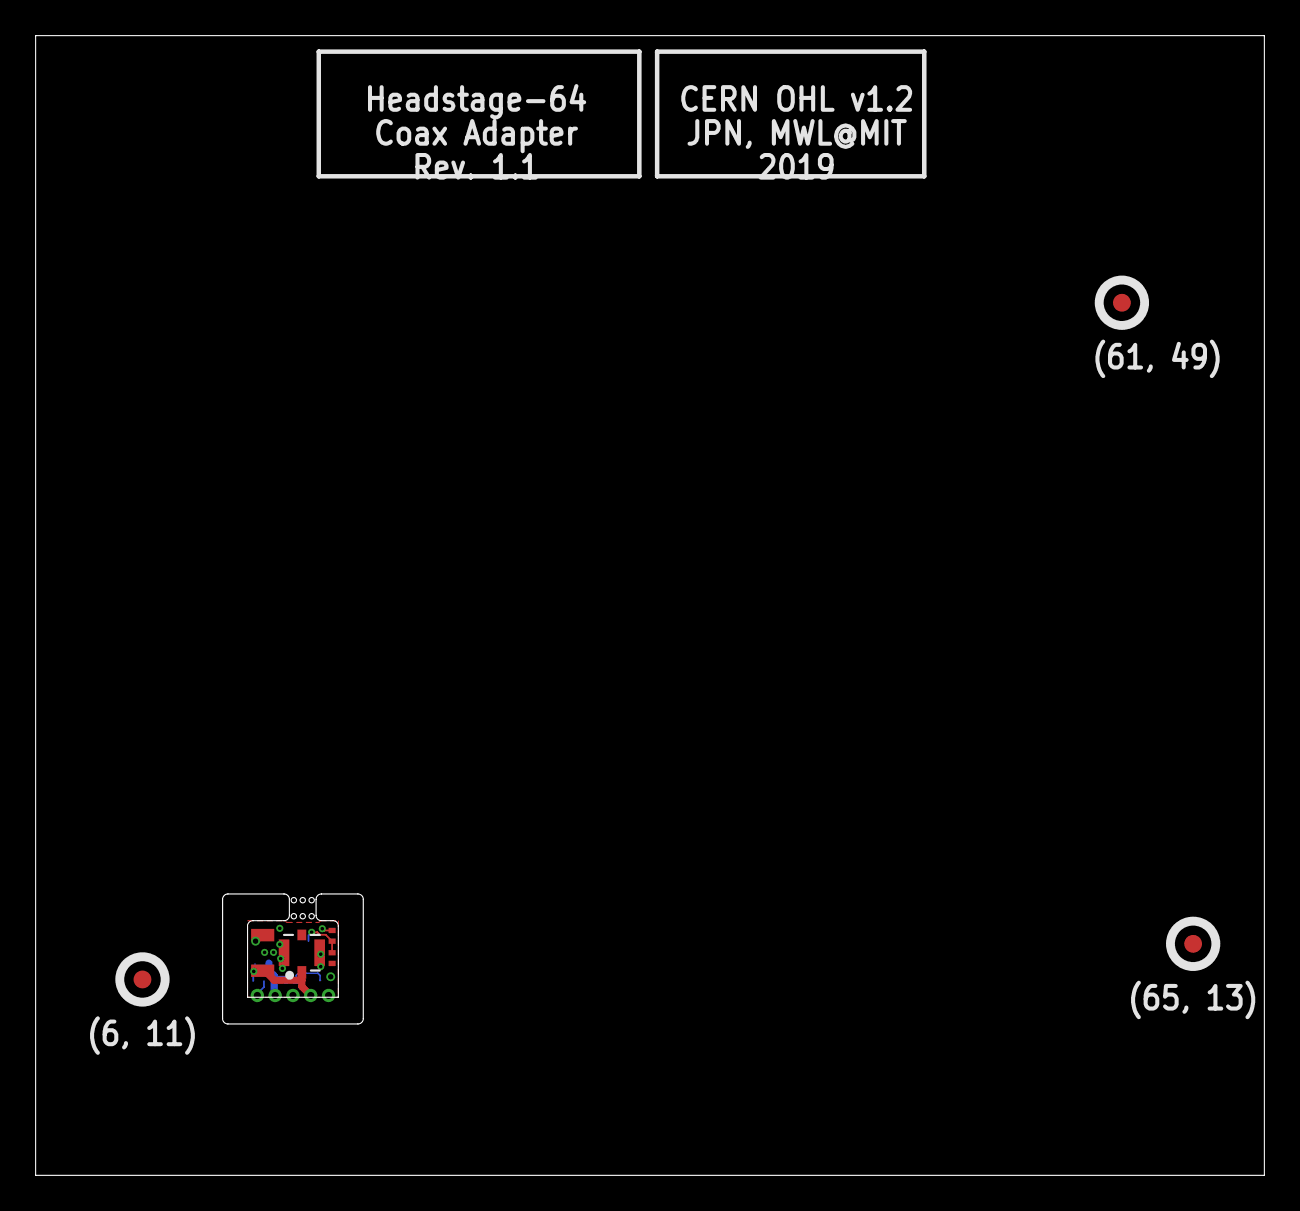
[picture p154: board headstage-64-coax-adapter.brd from above]

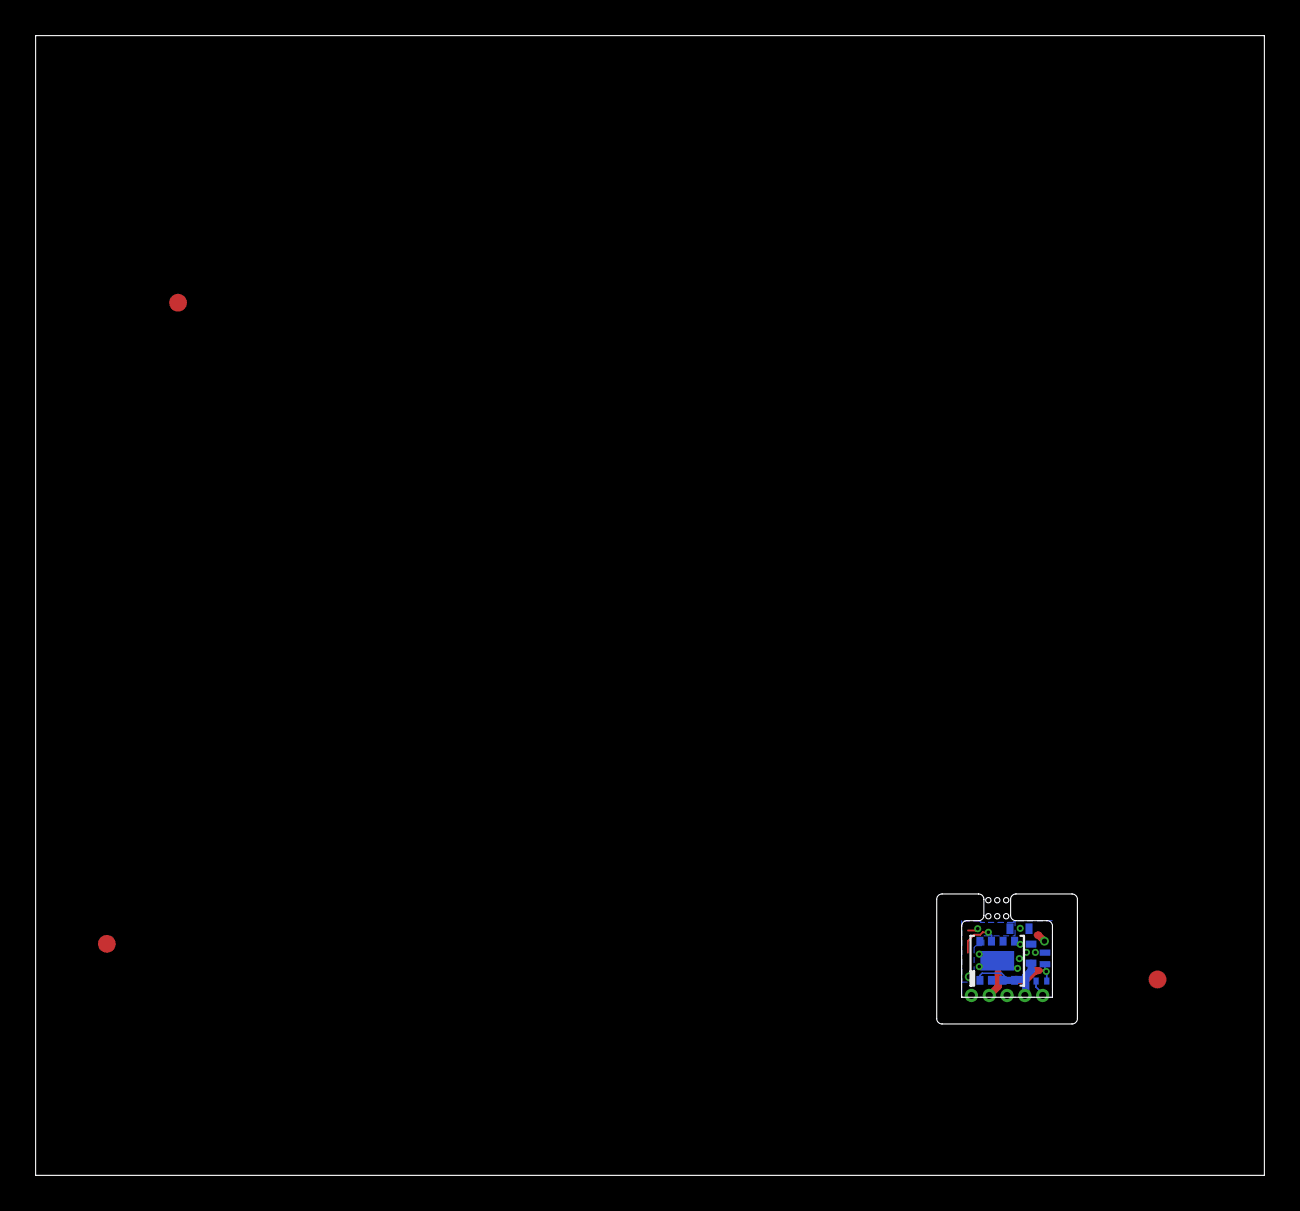
[picture p155: board headstage-64-coax-adapter.brd from below]

Board: 4 copper layers, 69.0 x 64.0 mm, 13 parts (5 on the bottom side), 6 nets.

Other parts of the board:
E$1, E$2, E$4: FIDUCIAL
