jonnew/ONIX/lesion-breakout/lesion-breakout.brd

## EAGLE design lesion-breakout/lesion-breakout.brd (2019-12-07)

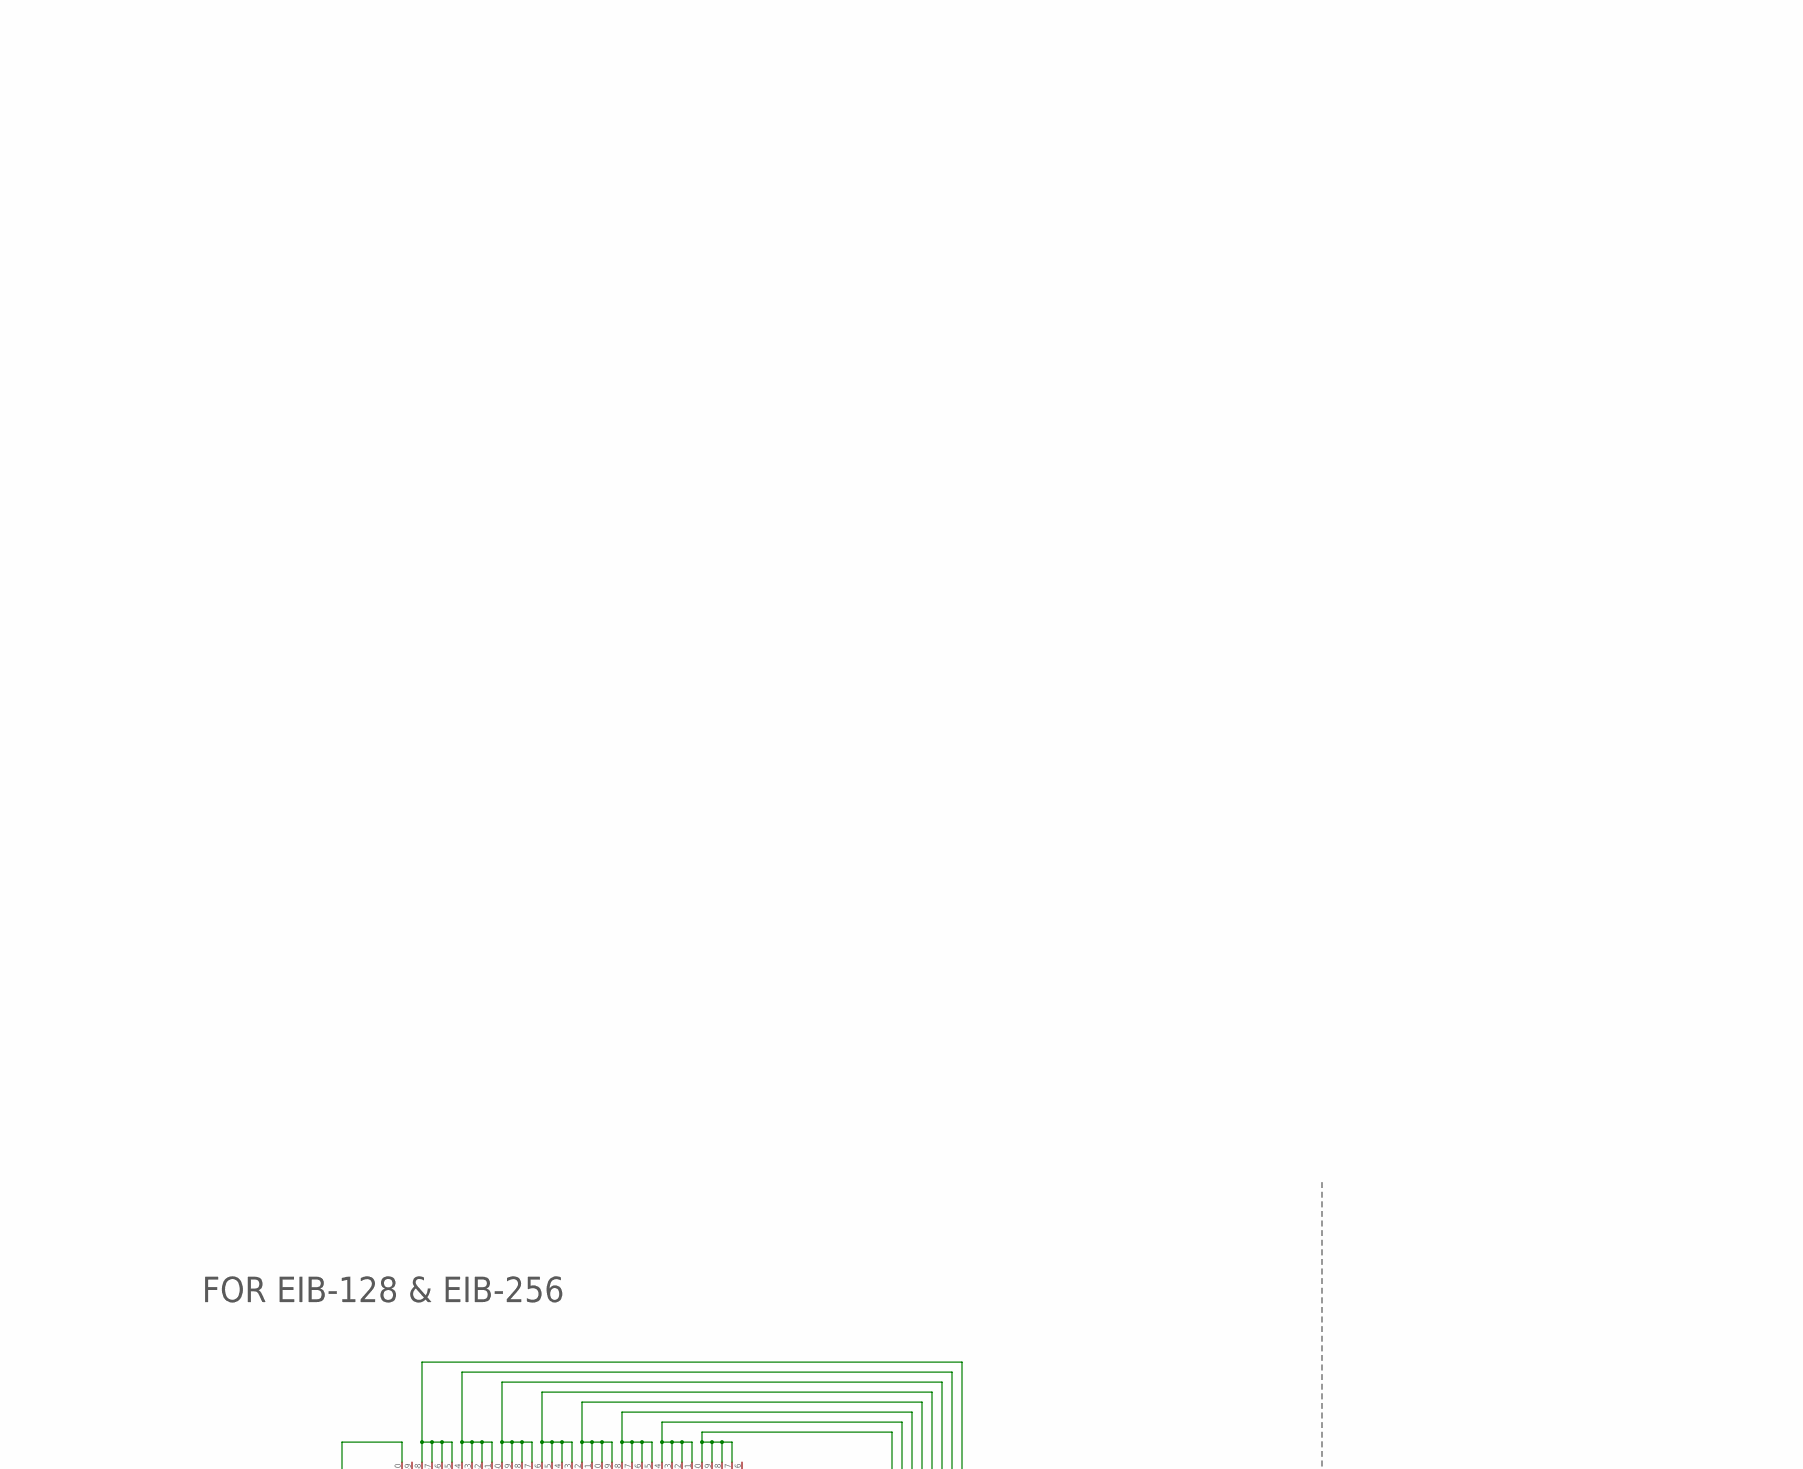
[picture p156: schematic lesion-breakout.sch, part in row 1, column 1]

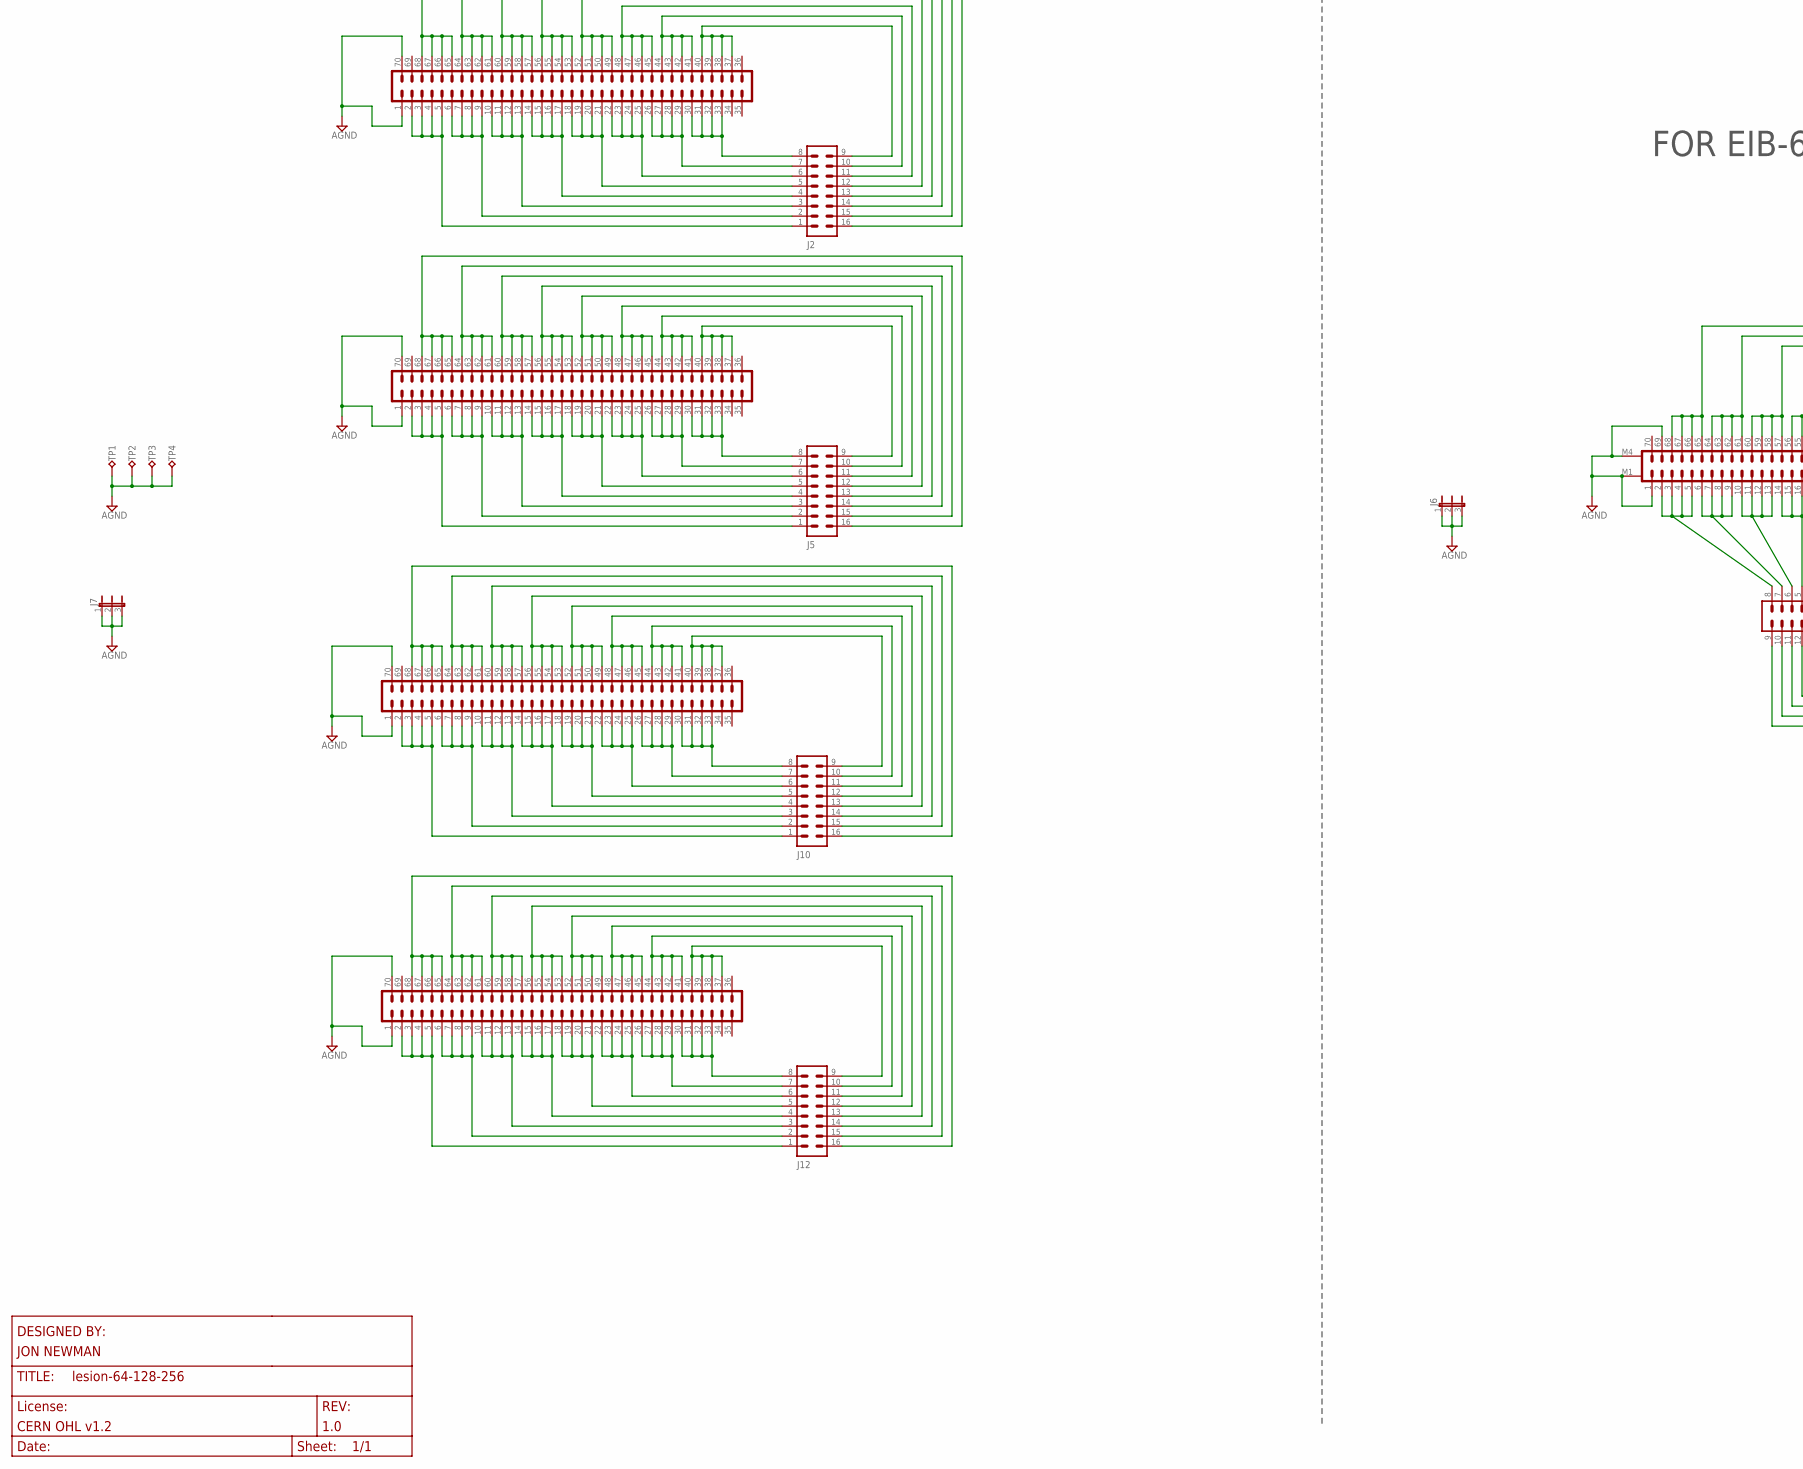
[picture p157: schematic lesion-breakout.sch, part in row 2, column 1]

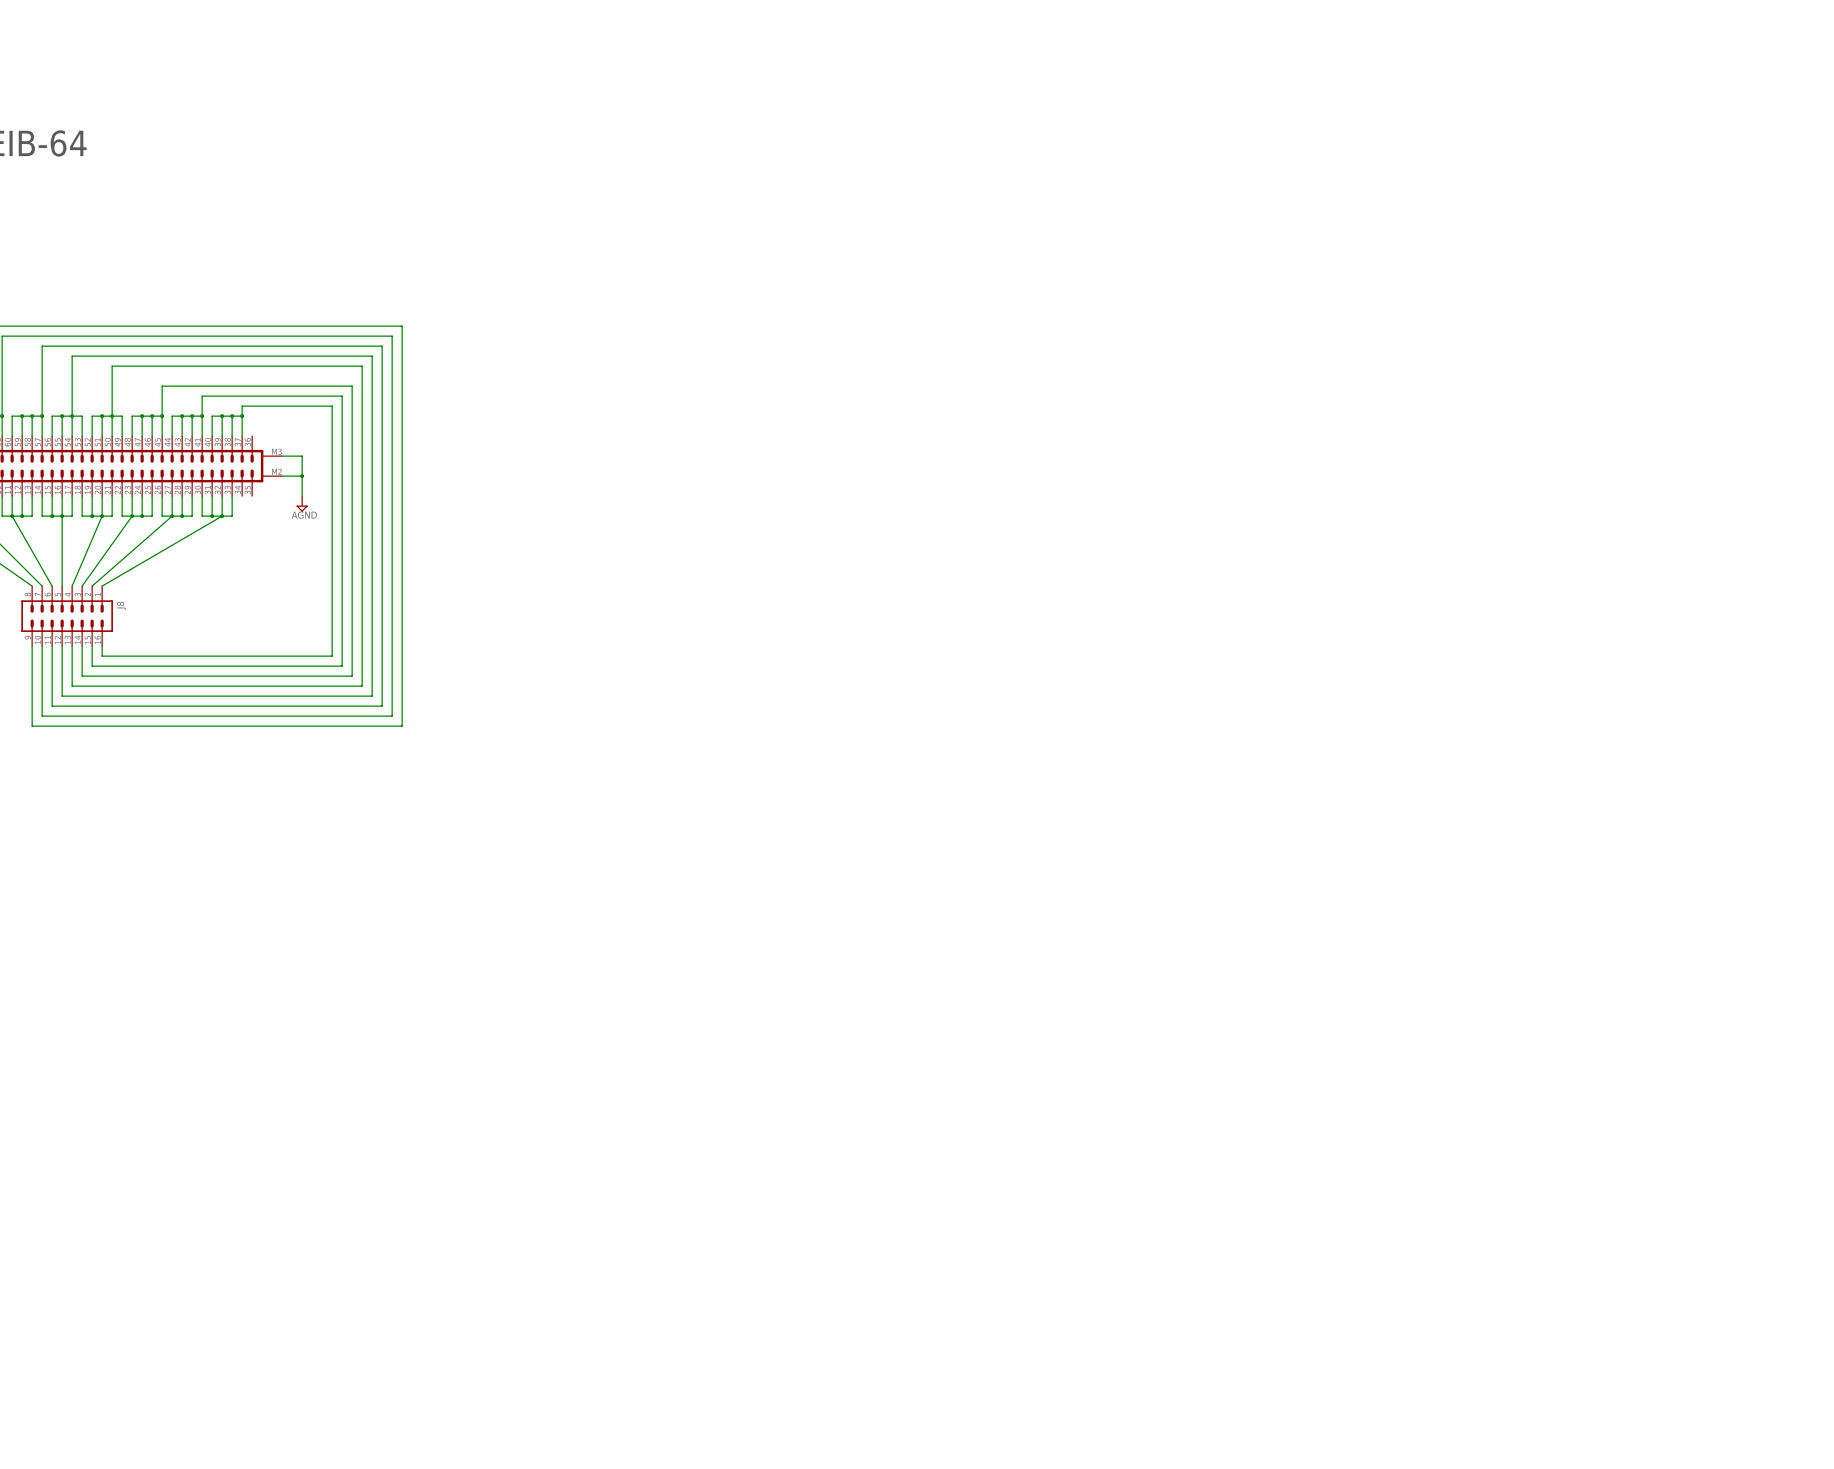
[picture p158: schematic lesion-breakout.sch, part in row 2, column 2]

Parts:
J1, J3, J9, J11: DF40C(2.0)-70DS-0.4V(51); DF40-70REC
J2, J5, J8, J10, J12: PINHD-2X8_SMD_0.5"; JP2X8_SMD_0.5"
J4: DF40C-70DP-0.4V(51); DF40-70HEAD-LESS-SILK
J6, J7: JP3E_SMD-0.05; JP3_SMD-0.05
TP1, TP2, TP3, TP4: TP_1MM; TESTPOINT_1MM

Connections:
AGND: J1.1, J1.70, J3.1, J3.70, J4.1, J4.69, J4.M1, J4.M2, J4.M3, J4.M4, J6.1, J6.2, J6.3, J7.1, J7.2, J7.3, J9.1, J9.70, J11.1, J11.70, TP1.1, TP2.1, TP3.1, TP4.1
unnamed: J4.53, J4.54, J4.55, J4.56, J8.12 (10)
unnamed: J4.57, J4.58, J4.59, J4.60, J8.11 (12)
unnamed: J4.61, J4.62, J4.63, J4.64, J8.10 (14)
unnamed: J4.2, J4.3, J4.4, J4.5, J8.8 (15)
unnamed: J4.65, J4.66, J4.67, J4.68, J8.9 (16)
unnamed: J4.10, J4.11, J4.12, J4.13, J8.6 (11)
unnamed: J4.14, J4.15, J4.16, J4.17, J8.5 (9)
unnamed: J4.18, J4.19, J4.20, J4.21, J8.4 (7)
unnamed: J4.22, J4.23, J4.24, J4.25, J8.3 (5)
unnamed: J4.26, J4.27, J4.28, J4.29, J8.2 (3)
unnamed: J4.30, J4.31, J4.32, J4.33, J8.1
unnamed: J4.37, J4.38, J4.39, J4.40, J8.16 (2)
unnamed: J4.41, J4.42, J4.43, J4.44, J8.15 (4)
unnamed: J4.45, J4.46, J4.47, J4.48, J8.14 (6)
unnamed: J4.49, J4.50, J4.51, J4.52, J8.13 (8)
unnamed: J4.6, J4.7, J4.8, J4.9, J8.7 (13)
unnamed: J1.2, J1.3, J1.4, J1.5, J2.1
unnamed: J1.6, J1.7, J1.8, J1.9, J2.2 (3)
unnamed: J1.10, J1.11, J1.12, J1.13, J2.3 (5)
unnamed: J1.14, J1.15, J1.16, J1.17, J2.4 (7)
unnamed: J1.18, J1.19, J1.20, J1.21, J2.5 (9)
unnamed: J1.22, J1.23, J1.24, J1.25, J2.6 (11)
unnamed: J1.26, J1.27, J1.28, J1.29, J2.7 (13)
unnamed: J1.30, J1.31, J1.32, J1.33, J2.8 (15)
unnamed: J1.37, J1.38, J1.39, J1.40, J2.9 (16)
unnamed: J1.41, J1.42, J1.43, J1.44, J2.10 (14)
unnamed: J1.45, J1.46, J1.47, J1.48, J2.11 (12)
unnamed: J1.49, J1.50, J1.51, J1.52, J2.12 (10)
unnamed: J1.53, J1.54, J1.55, J1.56, J2.13 (8)
unnamed: J1.57, J1.58, J1.59, J1.60, J2.14 (6)
unnamed: J1.61, J1.62, J1.63, J1.64, J2.15 (4)
unnamed: J1.65, J1.66, J1.67, J1.68, J2.16 (2)
unnamed: J3.2, J3.3, J3.4, J3.5, J5.1
unnamed: J3.6, J3.7, J3.8, J3.9, J5.2 (3)
unnamed: J3.10, J3.11, J3.12, J3.13, J5.3 (5)
unnamed: J3.14, J3.15, J3.16, J3.17, J5.4 (7)
unnamed: J3.18, J3.19, J3.20, J3.21, J5.5 (9)
unnamed: J3.22, J3.23, J3.24, J3.25, J5.6 (11)
unnamed: J3.26, J3.27, J3.28, J3.29, J5.7 (13)
unnamed: J3.30, J3.31, J3.32, J3.33, J5.8 (15)
unnamed: J3.37, J3.38, J3.39, J3.40, J5.9 (16)
unnamed: J3.41, J3.42, J3.43, J3.44, J5.10 (14)
unnamed: J3.45, J3.46, J3.47, J3.48, J5.11 (12)
unnamed: J3.49, J3.50, J3.51, J3.52, J5.12 (10)
unnamed: J3.53, J3.54, J3.55, J3.56, J5.13 (8)
unnamed: J3.57, J3.58, J3.59, J3.60, J5.14 (6)
unnamed: J3.61, J3.62, J3.63, J3.64, J5.15 (4)
unnamed: J3.65, J3.66, J3.67, J3.68, J5.16 (2)
unnamed: J9.2, J9.3, J9.4, J9.5, J10.1
unnamed: J9.6, J9.7, J9.8, J9.9, J10.2 (3)
unnamed: J9.10, J9.11, J9.12, J9.13, J10.3 (5)
unnamed: J9.14, J9.15, J9.16, J9.17, J10.4 (7)
unnamed: J9.18, J9.19, J9.20, J9.21, J10.5 (9)
unnamed: J9.22, J9.23, J9.24, J9.25, J10.6 (11)
unnamed: J9.26, J9.27, J9.28, J9.29, J10.7 (13)
unnamed: J9.30, J9.31, J9.32, J9.33, J10.8 (15)
unnamed: J9.37, J9.38, J9.39, J9.40, J10.9 (16)
unnamed: J9.41, J9.42, J9.43, J9.44, J10.10 (14)
unnamed: J9.45, J9.46, J9.47, J9.48, J10.11 (12)
unnamed: J9.49, J9.50, J9.51, J9.52, J10.12 (10)
unnamed: J9.53, J9.54, J9.55, J9.56, J10.13 (8)
unnamed: J9.57, J9.58, J9.59, J9.60, J10.14 (6)
unnamed: J9.61, J9.62, J9.63, J9.64, J10.15 (4)
unnamed: J9.65, J9.66, J9.67, J9.68, J10.16 (2)
unnamed: J11.2, J11.3, J11.4, J11.5, J12.1
unnamed: J11.6, J11.7, J11.8, J11.9, J12.2 (3)
unnamed: J11.10, J11.11, J11.12, J11.13, J12.3 (5)
unnamed: J11.14, J11.15, J11.16, J11.17, J12.4 (7)
unnamed: J11.18, J11.19, J11.20, J11.21, J12.5 (9)
unnamed: J11.22, J11.23, J11.24, J11.25, J12.6 (11)
unnamed: J11.26, J11.27, J11.28, J11.29, J12.7 (13)
unnamed: J11.30, J11.31, J11.32, J11.33, J12.8 (15)
unnamed: J11.37, J11.38, J11.39, J11.40, J12.9 (16)
unnamed: J11.41, J11.42, J11.43, J11.44, J12.10 (14)
unnamed: J11.45, J11.46, J11.47, J11.48, J12.11 (12)
unnamed: J11.49, J11.50, J11.51, J11.52, J12.12 (10)
unnamed: J11.53, J11.54, J11.55, J11.56, J12.13 (8)
unnamed: J11.57, J11.58, J11.59, J11.60, J12.14 (6)
unnamed: J11.61, J11.62, J11.63, J11.64, J12.15 (4)
unnamed: J11.65, J11.66, J11.67, J11.68, J12.16 (2)

Notes on the sheet:
FOR EIB-128 & EIB-256
FOR EIB-64

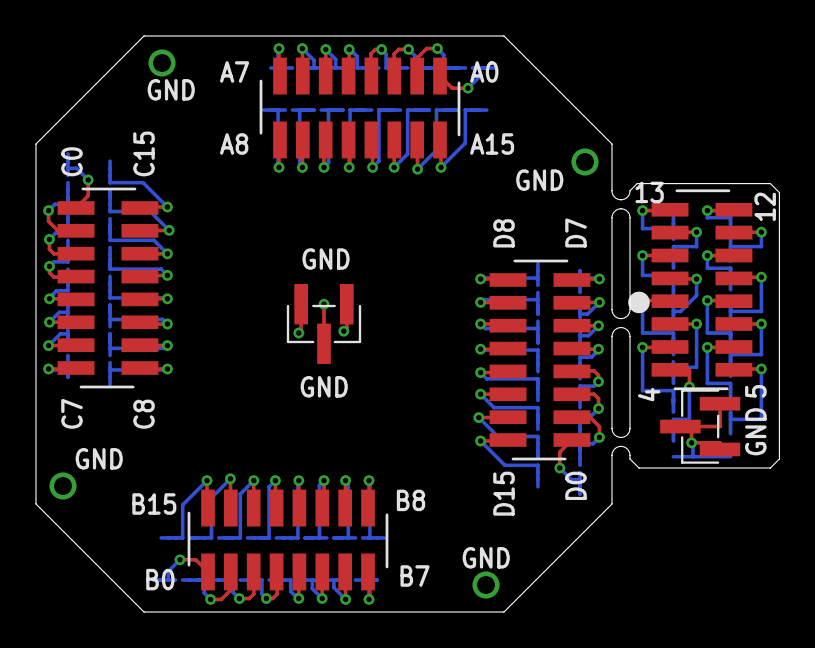
[picture p159: board lesion-breakout.brd from above]

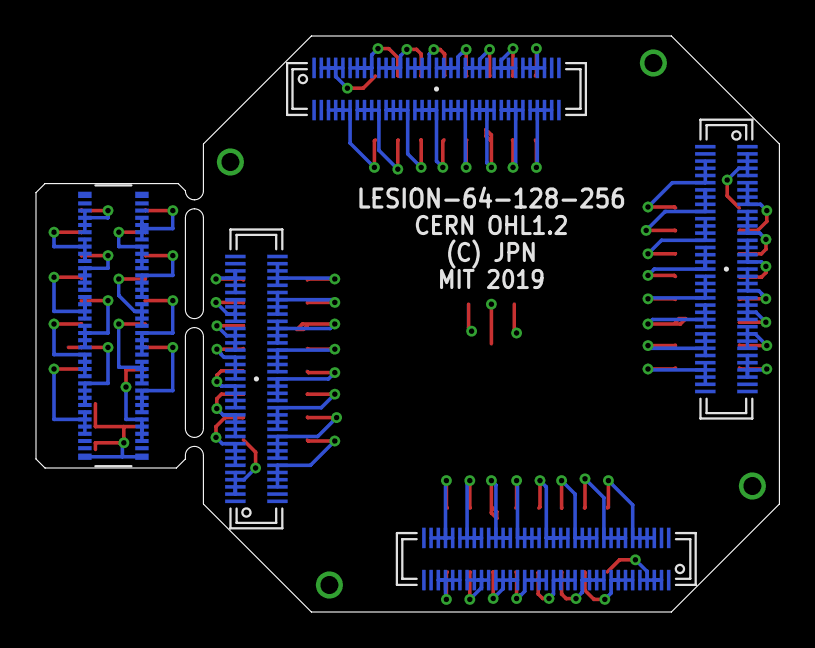
[picture p160: board lesion-breakout.brd from below]

Board: 2 copper layers, 41.3 x 32.0 mm, 16 parts (5 on the bottom side), 81 nets.
