jonnew/ONIX/headstage-256/expansion-uphone/hs-256-expansion-uphone.brd

## EAGLE design headstage-256/expansion-uphone/hs-256-expansion-uphone.brd (2019-11-25)

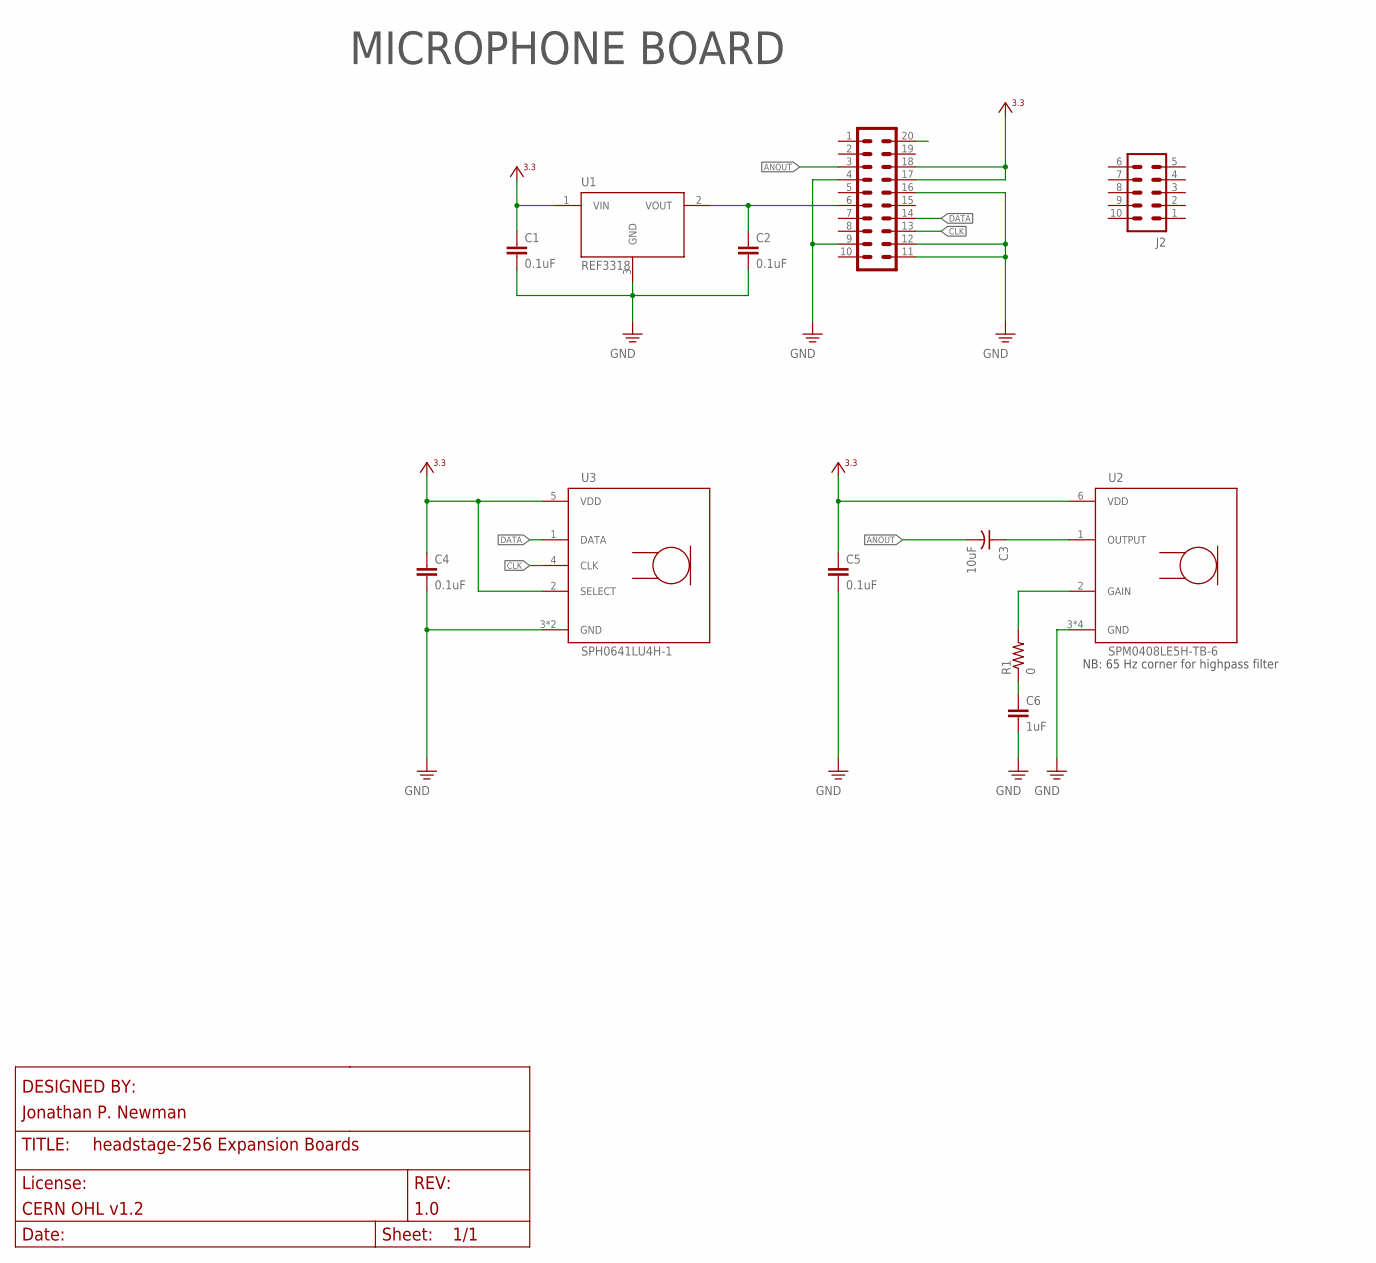
[picture p161: schematic hs-256-expansion-uphone.sch]

Parts:
C1, C2, C4, C5: 0.1uF; 0402
C3: 10uF; 0805-POL
C6: 1uF; 0402
J1: PINHD-2X10_DF40-20REC; DF40-20REC
J2: PINHD-2X5_DF40-REC; DF40-10REC
R1: 0; 0402
U1: REF3318; SOT23
U2: SPM0408LE5H-TB-6; KNOWLES-SPM
U3: SPH0641LU4H-1; KNOWLES-SPH

Connections:
+3V3: C1.1, C4.1, C5.1, J1.17, J1.18, U1.1 (VIN), U2.6 (VDD), U3.2 (SELECT), U3.5 (VDD)
ANOUT: C3.C (-), J1.3
CLK: J1.13, U3.4 (CLK)
DATA: J1.14, U3.1 (DATA)
GND: C1.2, C2.2, C4.2, C5.2, C6.2, J1.4, J1.9, J1.11, J1.12, J1.16, U1.3 (GND), U2.3 (GND), U2.4 (GND), U2.5 (GND), U2.7 (GND), U3.3 (GND), U3.6 (GND)
unnamed: C6.1, R1.1
unnamed: R1.2, U2.2 (GAIN)
unnamed: C3.A (+), U2.1 (OUTPUT)
VREF: C2.1, J1.6, U1.2 (VOUT)

Notes on the sheet:
NB: 65 Hz corner for highpass filter
MICROPHONE BOARD

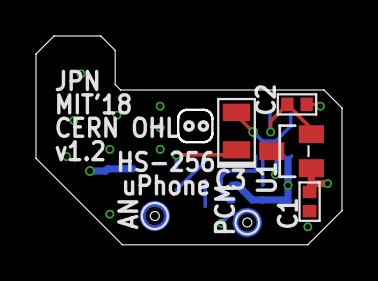
[picture p162: board hs-256-expansion-uphone.brd from above]

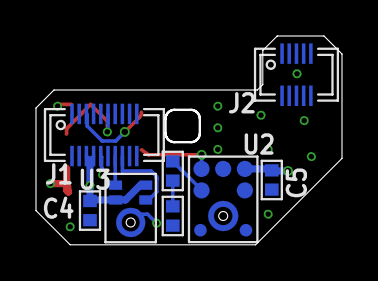
[picture p163: board hs-256-expansion-uphone.brd from below]

Board: 4 copper layers, 17.0 x 11.6 mm, 12 parts (8 on the bottom side), 9 nets.
