jonnew/ONIX/headstage-256/expansion-long-range/hs-256-expansion-long-range.brd

## EAGLE design headstage-256/expansion-long-range/hs-256-expansion-long-range.brd (2019-11-25)

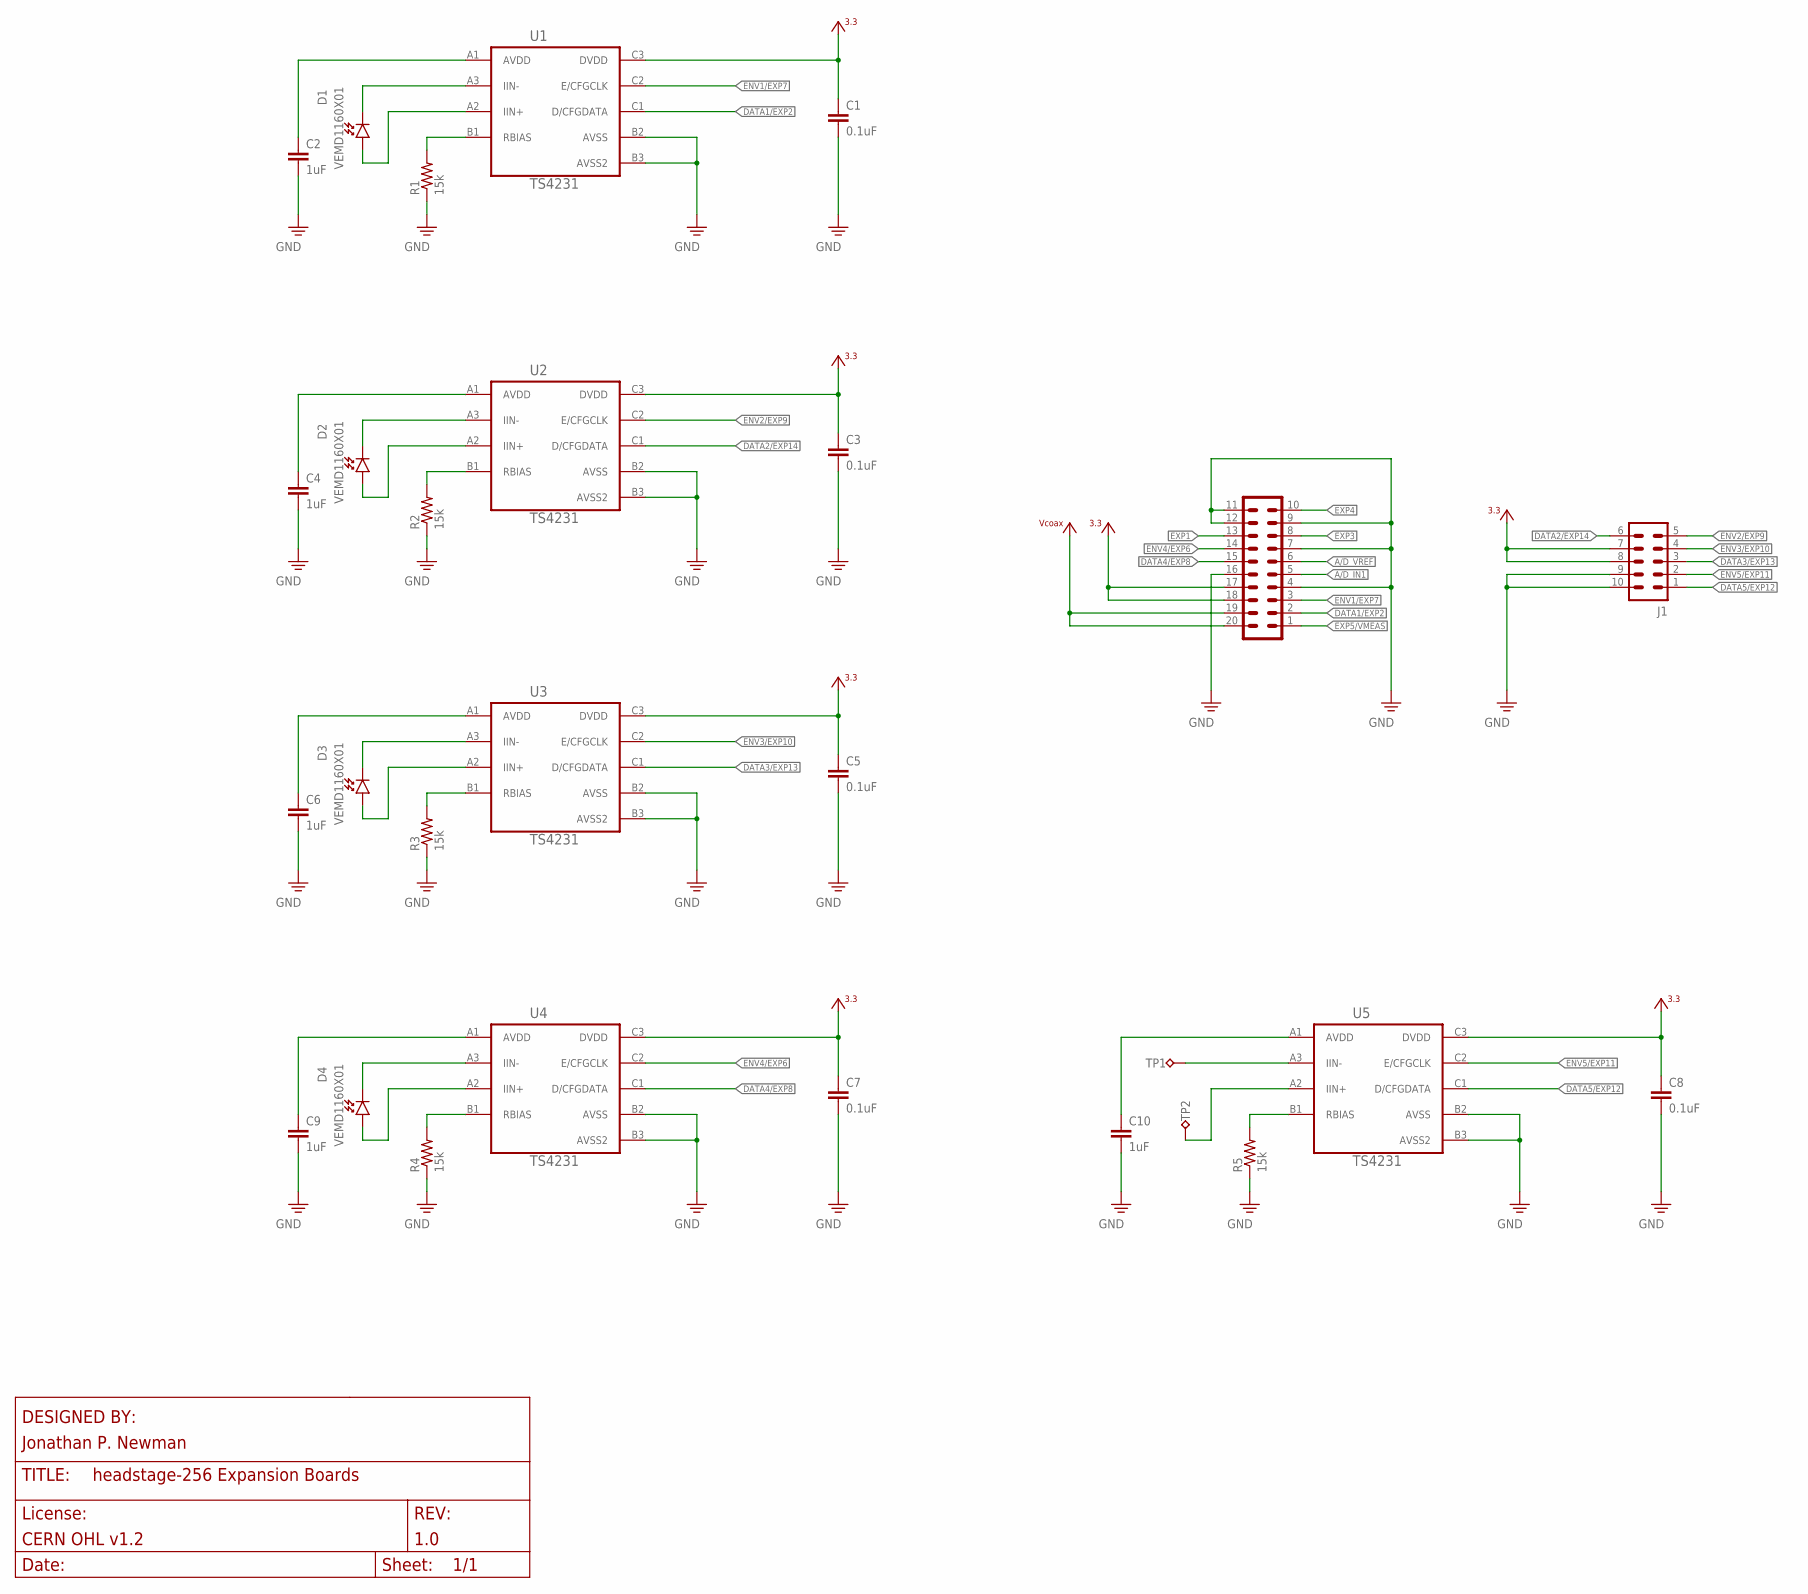
[picture p164: schematic hs-256-expansion-long-range.sch]

Parts:
C1, C3, C5, C7, C8: 0.1uF; 0201; PARTNO C0603X5R1C104K030BC
C2, C4, C6, C9, C10: 1uF; 0201; PARTNO CL03A105MP3ZSNH
D1, D2, D3, D4: VEMD1160X01; SFH2400FA
J1: PINHD-2X5_DF40-REC; DF40-10REC
J2: PINHD-2X10_DF40-20REC; DF40-20REC
R1, R2, R3, R4, R5: 15k; 0201
TP1, TP2: TPTP20SQ; TP20SQ
U1, U2, U3, U4, U5: TS4231; WLCSP3X3

Connections:
+3V3: C1.1, C3.1, C5.1, C7.1, C8.1, J1.7 (8), J1.8 (6), J2.17, J2.18, U1.C3 (DVDD), U2.C3 (DVDD), U3.C3 (DVDD), U4.C3 (DVDD), U5.C3 (DVDD)
A/D_IN1: J2.5
A/D_VREF: J2.6
DATA1/EXP2: J2.2, U1.C1 (D/CFGDATA)
DATA2/EXP14: J1.6 (10), U2.C1 (D/CFGDATA)
DATA3/EXP13: J1.3 (5), U3.C1 (D/CFGDATA)
DATA4/EXP8: J2.15, U4.C1 (D/CFGDATA)
DATA5/EXP12: J1.1, U5.C1 (D/CFGDATA)
ENV1/EXP7: J2.3, U1.C2 (E/CFGCLK)
ENV2/EXP9: J1.5 (9), U2.C2 (E/CFGCLK)
ENV3/EXP10: J1.4 (7), U3.C2 (E/CFGCLK)
ENV4/EXP6: J2.14, U4.C2 (E/CFGCLK)
ENV5/EXP11: J1.2 (3), U5.C2 (E/CFGCLK)
EXP1: J2.13
EXP3: J2.8
EXP4: J2.10
EXP5/VMEAS: J2.1
GND: C1.2, C2.2, C3.2, C4.2, C5.2, C6.2, C7.2, C8.2, C9.2, C10.2, J1.9 (4), J1.10 (2), J2.4, J2.7, J2.9, J2.11, J2.12, J2.16, R1.1, R2.1, R3.1, R4.1, R5.1, U1.B2 (AVSS), U1.B3 (AVSS2), U2.B2 (AVSS), U2.B3 (AVSS2), U3.B2 (AVSS), U3.B3 (AVSS2), U4.B2 (AVSS), U4.B3 (AVSS2), U5.B2 (AVSS), U5.B3 (AVSS2)
unnamed: D2.1 (C), U2.A3 (IIN-)
unnamed: D2.3 (A), U2.A2 (IIN+)
unnamed: R2.2, U2.B1 (RBIAS)
unnamed: C4.1, U2.A1 (AVDD)
unnamed: D3.1 (C), U3.A3 (IIN-)
unnamed: D3.3 (A), U3.A2 (IIN+)
unnamed: R3.2, U3.B1 (RBIAS)
unnamed: C6.1, U3.A1 (AVDD)
unnamed: D4.1 (C), U4.A3 (IIN-)
unnamed: D4.3 (A), U4.A2 (IIN+)
unnamed: R4.2, U4.B1 (RBIAS)
unnamed: C9.1, U4.A1 (AVDD)
unnamed: TP1.TP, U5.A3 (IIN-)
unnamed: TP2.TP, U5.A2 (IIN+)
unnamed: R5.2, U5.B1 (RBIAS)
unnamed: C10.1, U5.A1 (AVDD)
unnamed: D1.1 (C), U1.A3 (IIN-)
unnamed: D1.3 (A), U1.A2 (IIN+)
unnamed: R1.2, U1.B1 (RBIAS)
unnamed: C2.1, U1.A1 (AVDD)
VCOAX: J2.19, J2.20

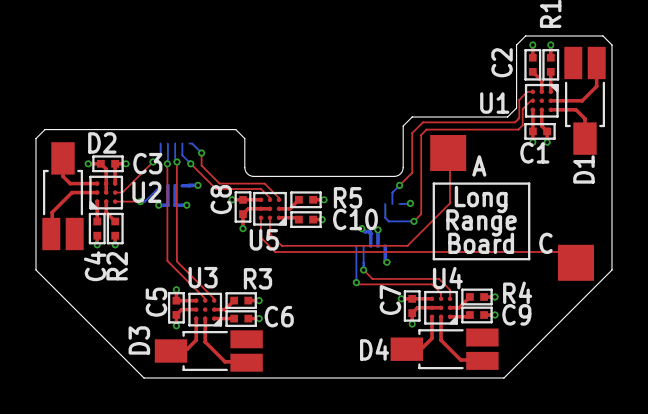
[picture p165: board hs-256-expansion-long-range.brd from above]

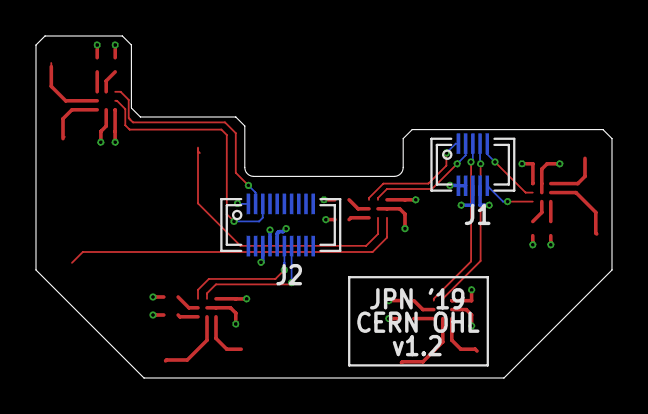
[picture p166: board hs-256-expansion-long-range.brd from below]

Board: 4 copper layers, 32.0 x 19.0 mm, 28 parts (2 on the bottom side), 33 nets.
