jonnew/ONIX/headstage-256/expansion-debug/hs-256-expansion-debug.brd

## EAGLE design headstage-256/expansion-debug/hs-256-expansion-debug.brd (2019-11-25)

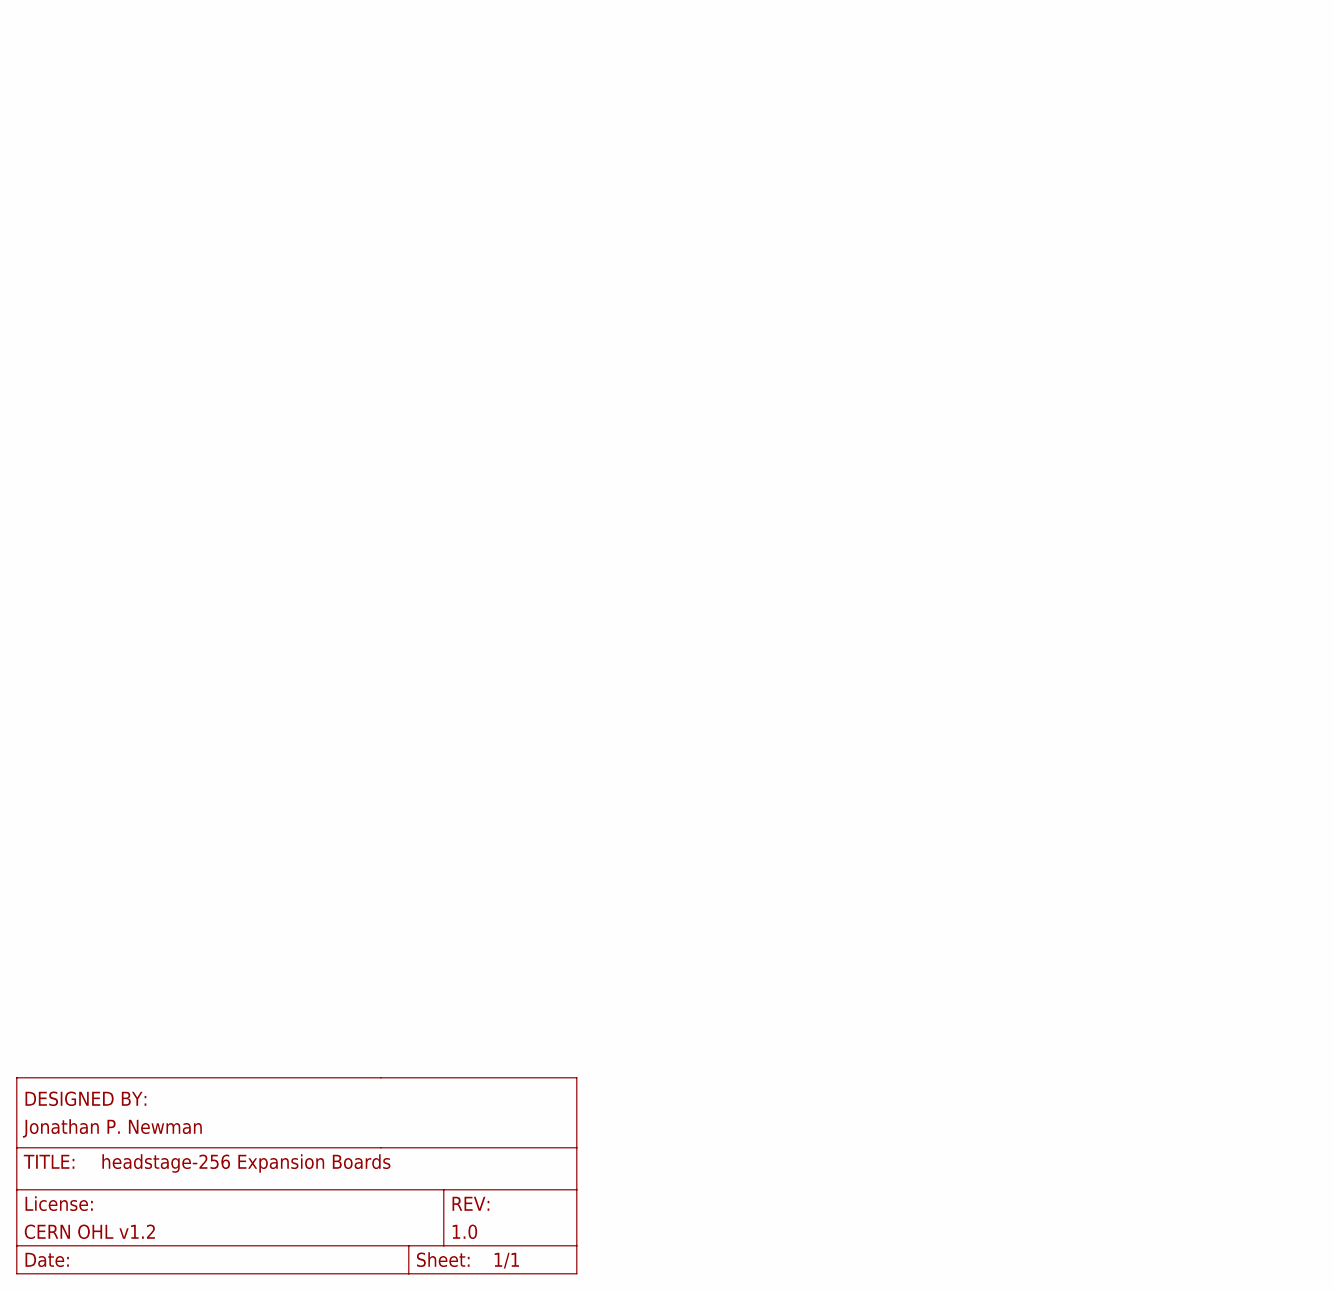
[picture p167: schematic hs-256-expansion-debug.sch, part in row 1, column 1]

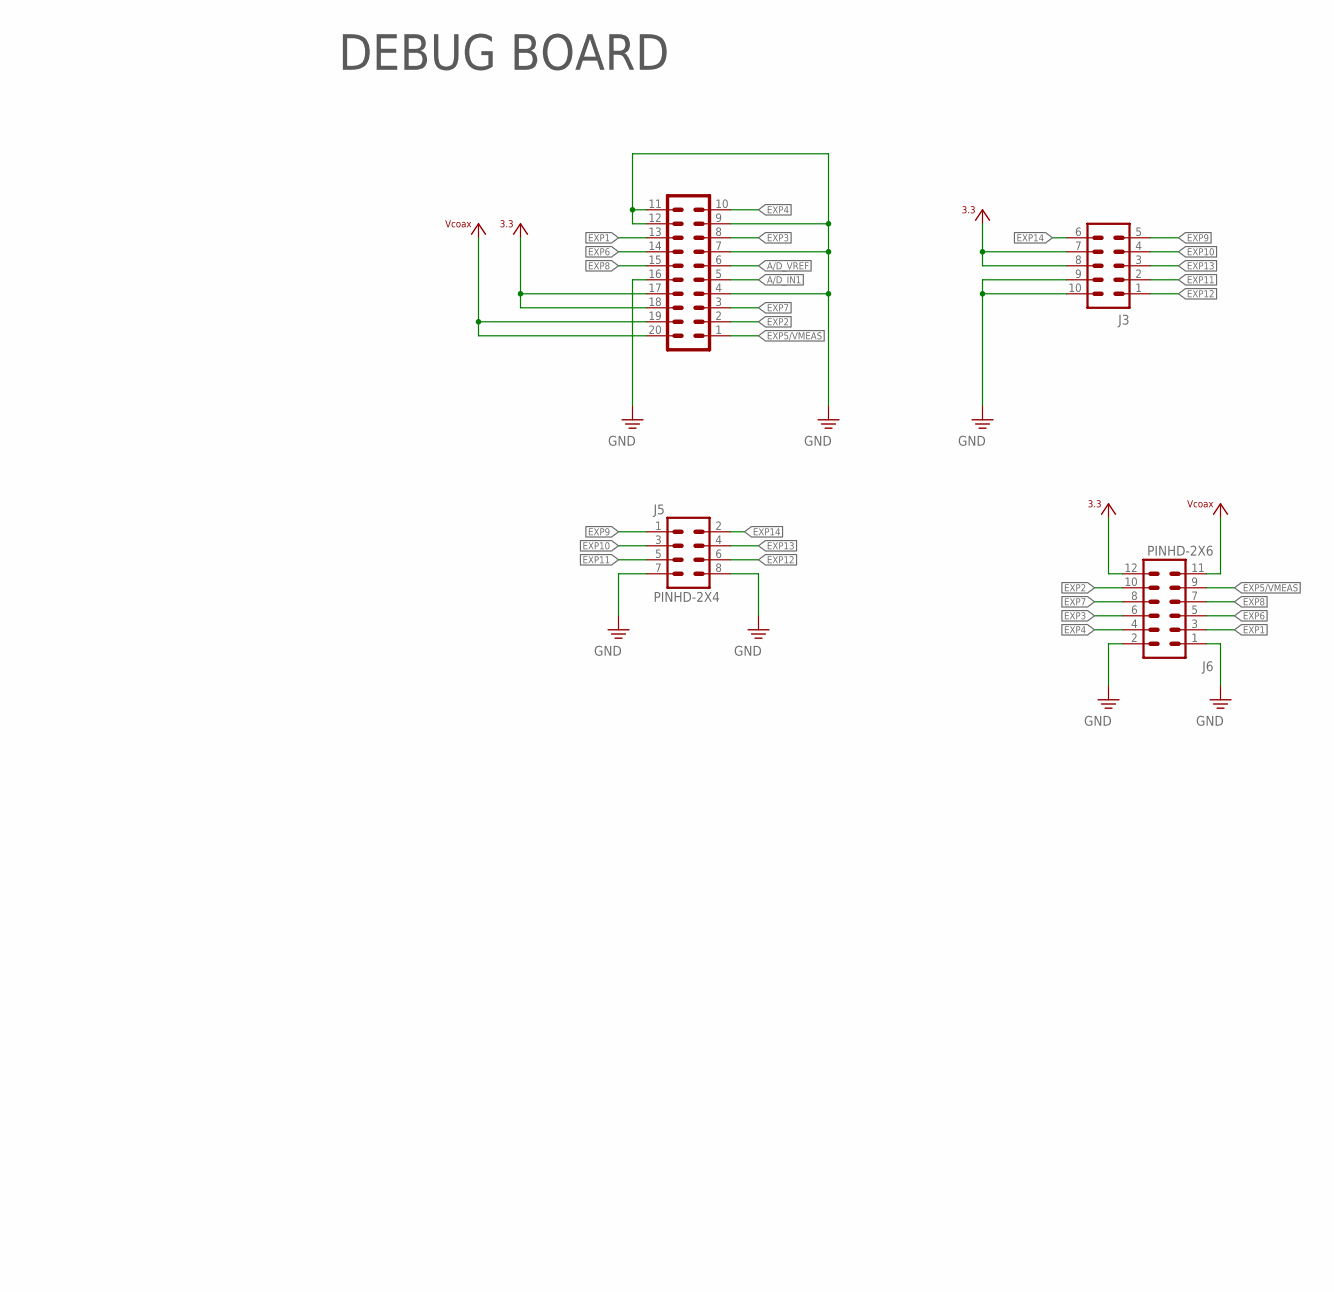
[picture p168: schematic hs-256-expansion-debug.sch, part in row 1, column 2]

Parts:
J3: PINHD-2X5_DF40-REC; DF40-10REC
J4: PINHD-2X10_DF40-20REC; DF40-20REC
J5: PINHD-2X4; 2X04-BIG
J6: PINHD-2X6; 2X06-BIG

Connections:
+3V3: J3.7 (8), J3.8 (6), J4.17, J4.18, J6.12
A/D_IN1: J4.5
A/D_VREF: J4.6
EXP1: J4.13, J6.3
EXP2: J4.2, J6.10
EXP3: J4.8, J6.6
EXP4: J4.10, J6.4
EXP5/VMEAS: J4.1, J6.9
EXP6: J4.14, J6.5
EXP7: J4.3, J6.8
EXP8: J4.15, J6.7
EXP9: J3.5 (9), J5.1
EXP10: J3.4 (7), J5.3
EXP11: J3.2 (3), J5.5
EXP12: J3.1, J5.6
EXP13: J3.3 (5), J5.4
EXP14: J3.6 (10), J5.2
GND: J3.9 (4), J3.10 (2), J4.4, J4.7, J4.9, J4.11, J4.12, J4.16, J5.7, J5.8, J6.1, J6.2
VCOAX: J4.19, J4.20, J6.11

Notes on the sheet:
DEBUG BOARD
