jonnew/ONIX/headstage-256/expansion-debug/hs-256-expansion-debug.brd

## EAGLE design headstage-256/expansion-debug/hs-256-expansion-debug.brd (continued)

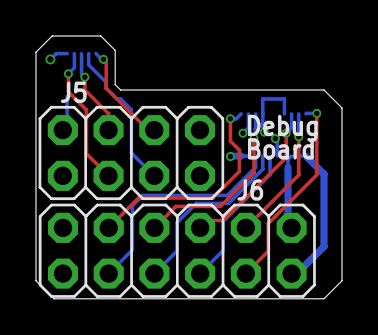
[picture p169: board hs-256-expansion-debug.brd from above]

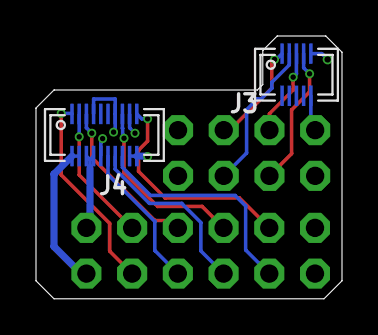
[picture p170: board hs-256-expansion-debug.brd from below]

Board: 4 copper layers, 17.0 x 14.6 mm, 4 parts (2 on the bottom side), 17 nets.
