jonnew/ONIX/lighthouse-booster/lighthouse-booster.brd

## EAGLE design lighthouse-booster/lighthouse-booster.brd (2019-11-19)

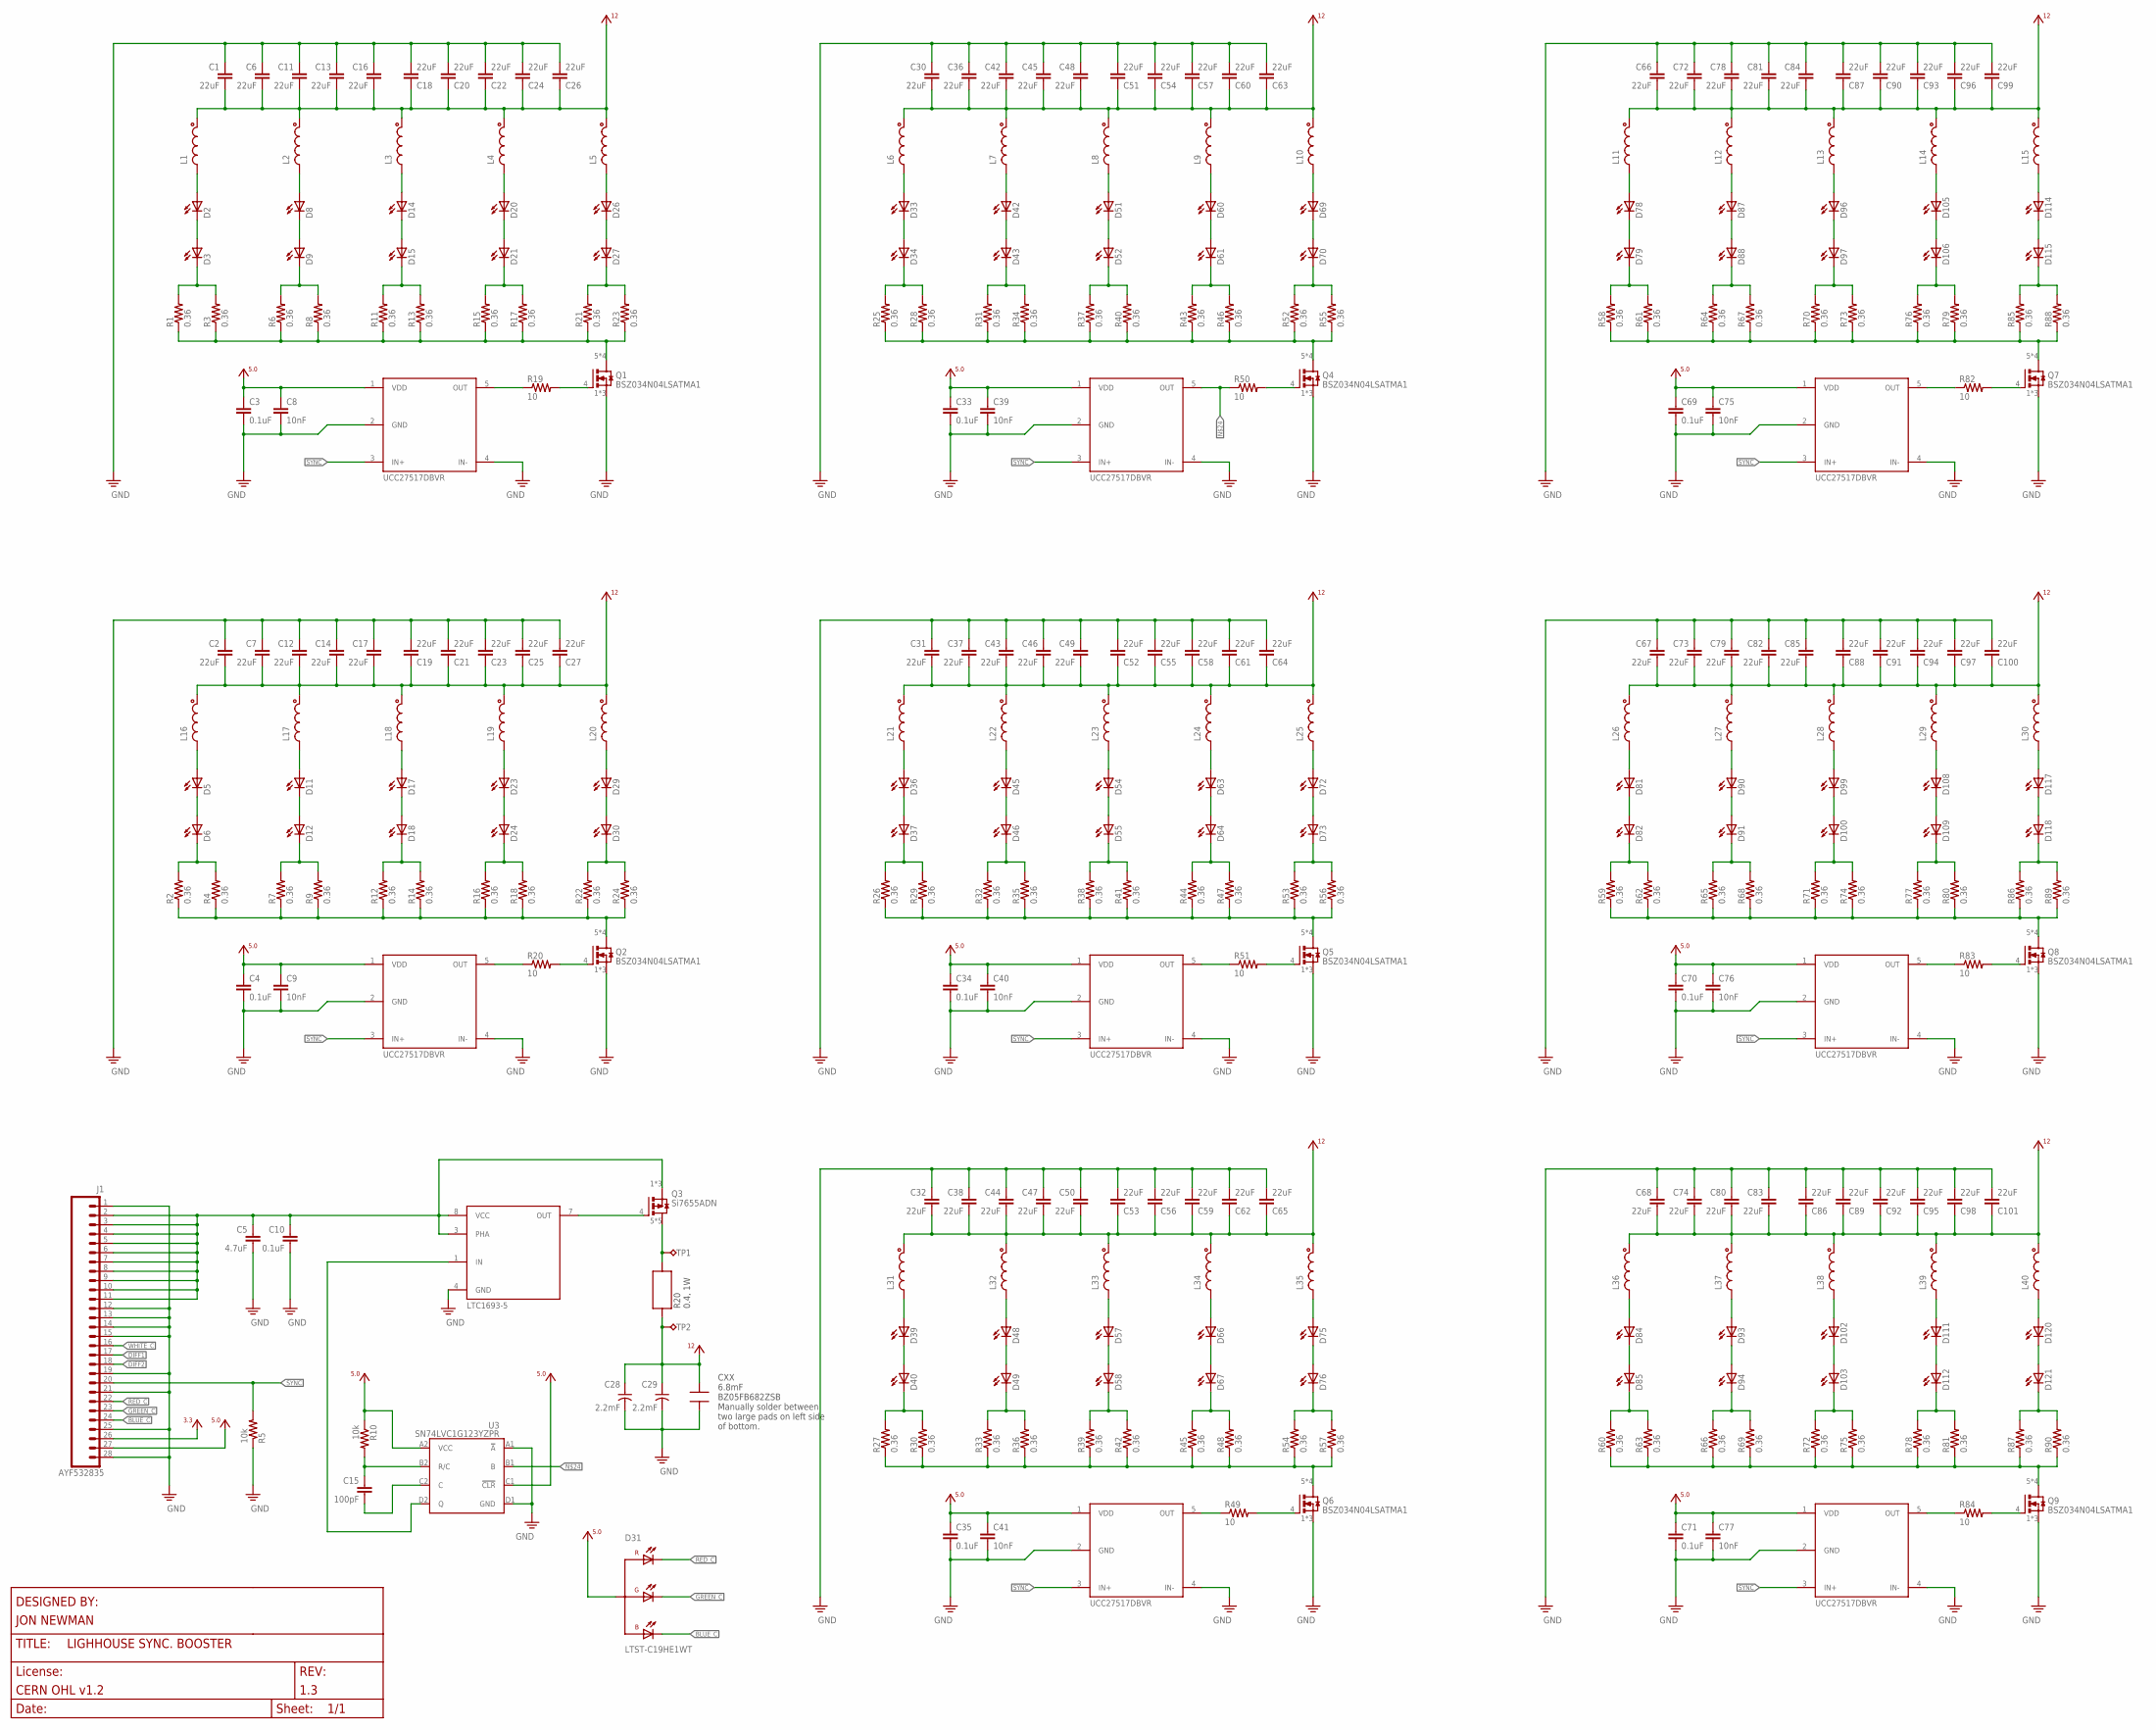
[picture p171: schematic lighthouse-booster.sch]

Parts:
C1, C2, C6, C7, C11, C12, C13, C14, C16, C17, C18, C19, C20, C21, C22, C23, C24, C25, C26, C27, C30, C31, C32, C36, C37, C38, C42, C43, C44, C45, C46, C47, C48, C49, C50, C51, C52, C53, C54, C55, C56, C57, C58, C59, C60, C61, C62, C63, C64, C65, C66, C67, C68, C72, C73, C74, C78, C79, C80, C81, C82, C83, C84, C85, C86, C87, C88, C89, C90, C91, C92, C93, C94, C95, C96, C97, C98, C99, C100, C101: 22uF; 0805T
C3, C4, C10, C33, C34, C35, C69, C70, C71: 0.1uF; 0402T
C5: 4.7uF; 0603T
C8, C9, C39, C40, C41, C75, C76, C77: 10nF; 0402T
C15: 100pF; 0402T
C28, C29: 2.2mF; C5MMA-SMD
D2, D3, D5, D6, D8, D9, D11, D12, D14, D15, D17, D18, D20, D21, D23, D24, D26, D27, D29, D30, D33, D34, D36, D37, D39, D40, D42, D43, D45, D46, D48, D49, D51, D52, D54, D55, D57, D58, D60, D61, D63, D64, D66, D67, D69, D70, D72, D73, D75, D76, D78, D79, D81, D82, D84, D85, D87, D88, D90, D91, D93, D94, D96, D97, D99, D100, D102, D103, D105, D106, D108, D109, D111, D112, D114, D115, D117, D118, D120, D121: LED_LUXEON-3.7MM; LUXEON-3.7MM
D31: LTST-C19HE1WT
J1: AYF532835; Y5B/Y5BW-28
L1, L2, L3, L4, L5, L6, L7, L8, L9, L10, L11, L12, L13, L14, L15, L16, L17, L18, L19, L20, L21, L22, L23, L24, L25, L26, L27, L28, L29, L30, L31, L32, L33, L34, L35, L36, L37, L38, L39, L40: L_0805T; 0805T
Q1, Q2, Q4, Q5, Q6, Q7, Q8, Q9: BSZ034N04LSATMA1; PG-TSDSON-8
Q3: Si7655ADN; POWERPACK-1212-8
R1, R2, R3, R4, R6, R7, R8, R9, R11, R12, R13, R14, R15, R16, R17, R18, R21, R22, R23, R24, R25, R26, R27, R28, R29, R30, R31, R32, R33, R34, R35, R36, R37, R38, R39, R40, R41, R42, R43, R44, R45, R46, R47, R48, R52, R53, R54, R55, R56, R57, R58, R59, R60, R61, R62, R63, R64, R65, R66, R67, R68, R69, R70, R71, R72, R73, R74, R75, R76, R77, R78, R79, R80, R81, R85, R86, R87, R88, R89, R90: 0.36; 0805T
R5, R10: 10k; 0402T
R19, R20, R49, R50, R51, R82, R83, R84: 10; 0402T
TP1, TP2: TPTP18SQ; TP18SQ
U1, U2, U5, U6, U7, U8, U9, U10: UCC27517DBVR; SOT-23-5
U3: SN74LVC1G123YZPR; DSBGA8-1.9X0.9MM
U4: LTC1693-5; MSOP-8-3X3

Connections:
+3V3: J1.26
+5V0: C3.1, C4.1, C8.1, C9.1, C33.1, C34.1, C35.1, C39.1, C40.1, C41.1, C69.1, C70.1, C71.1, C75.1, C76.1, C77.1, D31.4 (A), J1.27, R10.1, U1.1 (VDD), U2.1 (VDD), U3.A2 (VCC), U3.C1 (!CLR), U5.1 (VDD), U6.1 (VDD), U7.1 (VDD), U8.1 (VDD), U9.1 (VDD), U10.1 (VDD)
+12V: C1.2, C2.2, C6.2, C7.2, C11.2, C12.2, C13.2, C14.2, C16.2, C17.2, C18.1, C19.1, C20.1, C21.1, C22.1, C23.1, C24.1, C25.1, C26.1, C27.1, C28.A (+), C29.A (+), C30.2, C31.2, C32.2, C36.2, C37.2, C38.2, C42.2, C43.2, C44.2, C45.2, C46.2, C47.2, C48.2, C49.2, C50.2, C51.1, C52.1, C53.1, C54.1, C55.1, C56.1, C57.1, C58.1, C59.1, C60.1, C61.1, C62.1, C63.1, C64.1, C65.1, C66.2, C67.2, C68.2, C72.2, C73.2, C74.2, C78.2, C79.2, C80.2, C81.2, C82.2, C83.2, C84.2, C85.2, C86.1, C87.1, C88.1, C89.1, C90.1, C91.1, C92.1, C93.1, C94.1, C95.1, C96.1, C97.1, C98.1, C99.1, C100.1, C101.1, L1.1, L2.1, L3.1, L4.1, L5.1, L6.1, L7.1, L8.1, L9.1, L10.1, L11.1, L12.1, L13.1, L14.1, L15.1, L16.1, L17.1, L18.1, L19.1, L20.1, L21.1, L22.1, L23.1, L24.1, L25.1, L26.1, L27.1, L28.1, L29.1, L30.1, L31.1, L32.1, L33.1, L34.1, L35.1, L36.1, L37.1, L38.1, L39.1, L40.1, TP2.TP
BLUE_C: D31.3 (CB), J1.24
DIFF1: J1.17
DIFF2: J1.18
GND: C1.1, C2.1, C3.2, C4.2, C5.2, C6.1, C7.1, C8.2, C9.2, C10.2, C11.1, C12.1, C13.1, C14.1, C16.1, C17.1, C18.2, C19.2, C20.2, C21.2, C22.2, C23.2, C24.2, C25.2, C26.2, C27.2, C28.C (-), C29.C (-), C30.1, C31.1, C32.1, C33.2, C34.2, C35.2, C36.1, C37.1, C38.1, C39.2, C40.2, C41.2, C42.1, C43.1, C44.1, C45.1, C46.1, C47.1, C48.1, C49.1, C50.1, C51.2, C52.2, C53.2, C54.2, C55.2, C56.2, C57.2, C58.2, C59.2, C60.2, C61.2, C62.2, C63.2, C64.2, C65.2, C66.1, C67.1, C68.1, C69.2, C70.2, C71.2, C72.1, C73.1, C74.1, C75.2, C76.2, C77.2, C78.1, C79.1, C80.1, C81.1, C82.1, C83.1, C84.1, C85.1, C86.2, C87.2, C88.2, C89.2, C90.2, C91.2, C92.2, C93.2, C94.2, C95.2, C96.2, C97.2, C98.2, C99.2, C100.2, C101.2, J1.1, J1.12, J1.13, J1.14, J1.15, J1.19, J1.21, J1.25, J1.28, Q1.1 (S), Q1.2 (S), Q1.3 (S), Q2.1 (S), Q2.2 (S), Q2.3 (S), Q4.1 (S), Q4.2 (S), Q4.3 (S), Q5.1 (S), Q5.2 (S), Q5.3 (S), Q6.1 (S), Q6.2 (S), Q6.3 (S), Q7.1 (S), Q7.2 (S), Q7.3 (S), Q8.1 (S), Q8.2 (S), Q8.3 (S), Q9.1 (S), Q9.2 (S), Q9.3 (S), R5.1, U1.2 (GND), U1.4 (IN-), U2.2 (GND), U2.4 (IN-), U3.A1 (!A), U3.D1 (GND), U4.4 (GND), U5.2 (GND), U5.4 (IN-), U6.2 (GND), U6.4 (IN-), U7.2 (GND), U7.4 (IN-), U8.2 (GND), U8.4 (IN-), U9.2 (GND), U9.4 (IN-), U10.2 (GND), U10.4 (IN-)
GREEN_C: D31.2 (CG), J1.23
unnamed: D76.C, R54.2, R57.2
unnamed: D75.C, D76.A1 (A), D76.A2 (A)
unnamed: D75.A1 (A), D75.A2 (A), L35.2
unnamed: Q6.5 (D), Q6.6 (D), Q6.7 (D), Q6.8 (D), R27.1, R30.1, R33.1, R36.1, R39.1, R42.1, R45.1, R48.1, R54.1, R57.1
unnamed: R49.1, U7.5 (OUT)
unnamed: D58.C, R39.2, R42.2
unnamed: D57.C, D58.A1 (A), D58.A2 (A)
unnamed: D67.C, R45.2, R48.2
unnamed: D66.C, D67.A1 (A), D67.A2 (A)
unnamed: D66.A1 (A), D66.A2 (A), L34.2
unnamed: D30.C, R22.2, R24.2
unnamed: D57.A1 (A), D57.A2 (A), L33.2
unnamed: D49.C, R33.2, R36.2
unnamed: D48.C, D49.A1 (A), D49.A2 (A)
unnamed: D48.A1 (A), D48.A2 (A), L32.2
unnamed: D40.C, R27.2, R30.2
unnamed: D39.C, D40.A1 (A), D40.A2 (A)
unnamed: D39.A1 (A), D39.A2 (A), L31.2
unnamed: D29.C, D30.A1 (A), D30.A2 (A)
unnamed: D29.A1 (A), D29.A2 (A), L20.2
unnamed: Q2.5 (D), Q2.6 (D), Q2.7 (D), Q2.8 (D), R2.1, R4.1, R7.1, R9.1, R12.1, R14.1, R16.1, R18.1, R22.1, R24.1
unnamed: R82.1, U8.5 (OUT)
unnamed: Q6.4 (G), R49.2
unnamed: R50.1, U3.B1 (B), U5.5 (OUT)
unnamed: Q1.4 (G), R19.2
unnamed: R20.1, U2.5 (OUT)
unnamed: Q5.4 (G), R51.2
unnamed: R83.1, U9.5 (OUT)
unnamed: D24.C, R16.2, R18.2
unnamed: D23.C, D24.A1 (A), D24.A2 (A)
unnamed: D23.A1 (A), D23.A2 (A), L19.2
unnamed: D18.C, R12.2, R14.2
unnamed: D17.C, D18.A1 (A), D18.A2 (A)
unnamed: D17.A1 (A), D17.A2 (A), L18.2
unnamed: D12.C, R7.2, R9.2
unnamed: D11.C, D12.A1 (A), D12.A2 (A)
unnamed: D11.A1 (A), D11.A2 (A), L17.2
unnamed: D6.C, R2.2, R4.2
unnamed: D5.C, D6.A1 (A), D6.A2 (A)
unnamed: D5.A1 (A), D5.A2 (A), L16.2
unnamed: Q2.4 (G), R20.2
unnamed: R84.1, U10.5 (OUT)
unnamed: C15.1, R10.2, U3.B2 (R/C)
unnamed: U3.D2 (Q), U4.1 (IN)
unnamed: C15.2, U3.C2 (C)
unnamed: C5.1, C10.1, J1.2, J1.3, J1.4, J1.5, J1.6, J1.7, J1.8, J1.9, J1.10, J1.11, Q3.1 (S), Q3.2 (S), Q3.3 (S), U4.3 (PHA), U4.8 (VCC)
unnamed: D27.C, R21.2, R23.2
unnamed: D26.C, D27.A1 (A), D27.A2 (A)
unnamed: D26.A1 (A), D26.A2 (A), L5.2
unnamed: Q1.5 (D), Q1.6 (D), Q1.7 (D), Q1.8 (D), R1.1, R3.1, R6.1, R8.1, R11.1, R13.1, R15.1, R17.1, R21.1, R23.1
unnamed: Q3.5 (D), Q3.6 (D), Q3.7 (D), Q3.8 (D), Q3.PAD (D), TP1.TP
unnamed: D21.C, R15.2, R17.2
unnamed: D20.C, D21.A1 (A), D21.A2 (A)
unnamed: D20.A1 (A), D20.A2 (A), L4.2
unnamed: D15.C, R11.2, R13.2
unnamed: D14.C, D15.A1 (A), D15.A2 (A)
unnamed: D14.A1 (A), D14.A2 (A), L3.2
unnamed: D9.C, R6.2, R8.2
unnamed: D8.C, D9.A1 (A), D9.A2 (A)
unnamed: D8.A1 (A), D8.A2 (A), L2.2
unnamed: D3.C, R1.2, R3.2
unnamed: D2.C, D3.A1 (A), D3.A2 (A)
unnamed: D2.A1 (A), D2.A2 (A), L1.2
unnamed: R19.1, U1.5 (OUT)
unnamed: Q3.4 (G), U4.7 (OUT)
unnamed: D70.C, R52.2, R55.2
unnamed: D69.C, D70.A1 (A), D70.A2 (A)
unnamed: D69.A1 (A), D69.A2 (A), L10.2
unnamed: Q4.5 (D), Q4.6 (D), Q4.7 (D), Q4.8 (D), R25.1, R28.1, R31.1, R34.1, R37.1, R40.1, R43.1, R46.1, R52.1, R55.1
unnamed: D61.C, R43.2, R46.2
unnamed: D60.C, D61.A1 (A), D61.A2 (A)
unnamed: D60.A1 (A), D60.A2 (A), L9.2
unnamed: D52.C, R37.2, R40.2
unnamed: D51.C, D52.A1 (A), D52.A2 (A)
unnamed: D51.A1 (A), D51.A2 (A), L8.2
unnamed: D43.C, R31.2, R34.2
unnamed: D42.C, D43.A1 (A), D43.A2 (A)
unnamed: D42.A1 (A), D42.A2 (A), L7.2
unnamed: D34.C, R25.2, R28.2
unnamed: D33.C, D34.A1 (A), D34.A2 (A)
unnamed: D33.A1 (A), D33.A2 (A), L6.2
unnamed: Q4.4 (G), R50.2
unnamed: D115.C, R85.2, R88.2
unnamed: D114.C, D115.A1 (A), D115.A2 (A)
unnamed: D114.A1 (A), D114.A2 (A), L15.2
unnamed: Q7.5 (D), Q7.6 (D), Q7.7 (D), Q7.8 (D), R58.1, R61.1, R64.1, R67.1, R70.1, R73.1, R76.1, R79.1, R85.1, R88.1
unnamed: D106.C, R76.2, R79.2
unnamed: D105.C, D106.A1 (A), D106.A2 (A)
unnamed: D105.A1 (A), D105.A2 (A), L14.2
unnamed: D97.C, R70.2, R73.2
unnamed: D96.C, D97.A1 (A), D97.A2 (A)
unnamed: D96.A1 (A), D96.A2 (A), L13.2
unnamed: D88.C, R64.2, R67.2
unnamed: D87.C, D88.A1 (A), D88.A2 (A)
unnamed: D87.A1 (A), D87.A2 (A), L12.2
unnamed: D79.C, R58.2, R61.2
unnamed: D78.C, D79.A1 (A), D79.A2 (A)
unnamed: D78.A1 (A), D78.A2 (A), L11.2
unnamed: Q7.4 (G), R82.2
unnamed: D73.C, R53.2, R56.2
unnamed: D72.C, D73.A1 (A), D73.A2 (A)
unnamed: D72.A1 (A), D72.A2 (A), L25.2
unnamed: Q5.5 (D), Q5.6 (D), Q5.7 (D), Q5.8 (D), R26.1, R29.1, R32.1, R35.1, R38.1, R41.1, R44.1, R47.1, R53.1, R56.1
unnamed: D64.C, R44.2, R47.2
unnamed: D63.C, D64.A1 (A), D64.A2 (A)
unnamed: D63.A1 (A), D63.A2 (A), L24.2
unnamed: D55.C, R38.2, R41.2
unnamed: D54.C, D55.A1 (A), D55.A2 (A)
unnamed: D54.A1 (A), D54.A2 (A), L23.2
unnamed: D46.C, R32.2, R35.2
unnamed: D45.C, D46.A1 (A), D46.A2 (A)
unnamed: D45.A1 (A), D45.A2 (A), L22.2
unnamed: D37.C, R26.2, R29.2
unnamed: D36.C, D37.A1 (A), D37.A2 (A)
unnamed: D36.A1 (A), D36.A2 (A), L21.2
unnamed: R51.1, U6.5 (OUT)
unnamed: D118.C, R86.2, R89.2
unnamed: D117.C, D118.A1 (A), D118.A2 (A)
unnamed: D117.A1 (A), D117.A2 (A), L30.2
unnamed: Q8.5 (D), Q8.6 (D), Q8.7 (D), Q8.8 (D), R59.1, R62.1, R65.1, R68.1, R71.1, R74.1, R77.1, R80.1, R86.1, R89.1
unnamed: D109.C, R77.2, R80.2
unnamed: D108.C, D109.A1 (A), D109.A2 (A)
unnamed: D108.A1 (A), D108.A2 (A), L29.2
unnamed: D100.C, R71.2, R74.2
unnamed: D99.C, D100.A1 (A), D100.A2 (A)
unnamed: D99.A1 (A), D99.A2 (A), L28.2
unnamed: D91.C, R65.2, R68.2
unnamed: D90.C, D91.A1 (A), D91.A2 (A)
unnamed: D90.A1 (A), D90.A2 (A), L27.2
unnamed: D82.C, R59.2, R62.2
unnamed: D81.C, D82.A1 (A), D82.A2 (A)
unnamed: D81.A1 (A), D81.A2 (A), L26.2
unnamed: Q8.4 (G), R83.2
unnamed: D121.C, R87.2, R90.2
unnamed: D120.C, D121.A1 (A), D121.A2 (A)
unnamed: D120.A1 (A), D120.A2 (A), L40.2
unnamed: Q9.5 (D), Q9.6 (D), Q9.7 (D), Q9.8 (D), R60.1, R63.1, R66.1, R69.1, R72.1, R75.1, R78.1, R81.1, R87.1, R90.1
unnamed: D112.C, R78.2, R81.2
unnamed: D111.C, D112.A1 (A), D112.A2 (A)
unnamed: D111.A1 (A), D111.A2 (A), L39.2
unnamed: D103.C, R72.2, R75.2
unnamed: D102.C, D103.A1 (A), D103.A2 (A)
unnamed: D102.A1 (A), D102.A2 (A), L38.2
unnamed: D94.C, R66.2, R69.2
unnamed: D93.C, D94.A1 (A), D94.A2 (A)
unnamed: D93.A1 (A), D93.A2 (A), L37.2
unnamed: D85.C, R60.2, R63.2
unnamed: D84.C, D85.A1 (A), D85.A2 (A)
unnamed: D84.A1 (A), D84.A2 (A), L36.2
unnamed: Q9.4 (G), R84.2
RED_C: D31.1 (CR), J1.22
SYNC: J1.20, R5.2, U1.3 (IN+), U2.3 (IN+), U5.3 (IN+), U6.3 (IN+), U7.3 (IN+), U8.3 (IN+), U9.3 (IN+), U10.3 (IN+)
WHITE_C: J1.16

Notes on the sheet:
R20 0.4, 1W
CXX 6.8mF BZ05FB682ZSB Manually solder between two large pads on left side of bottom.

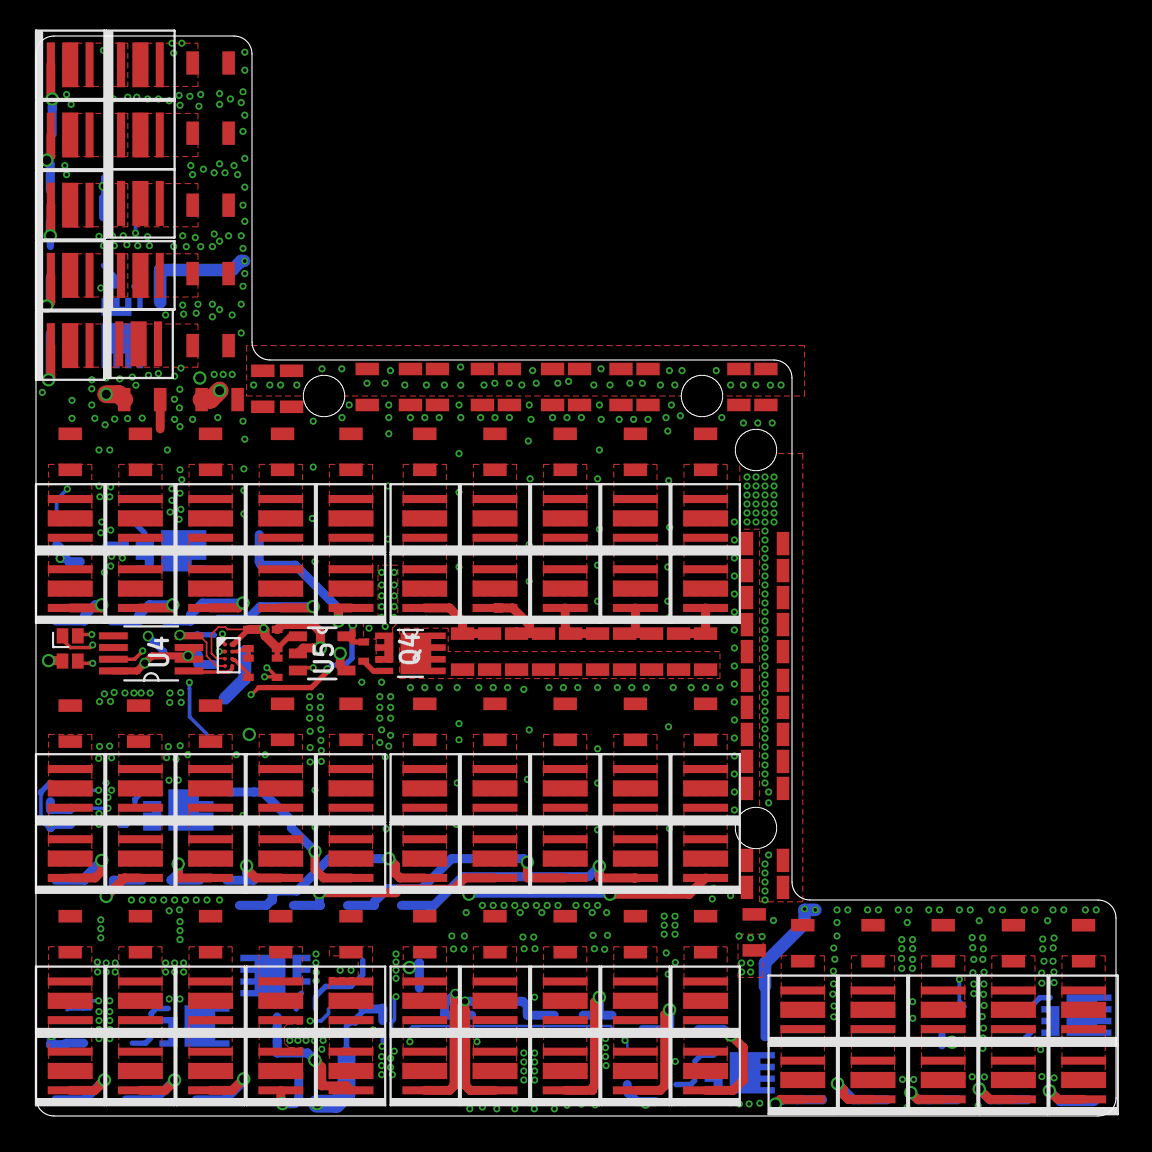
[picture p172: board lighthouse-booster.brd from above]

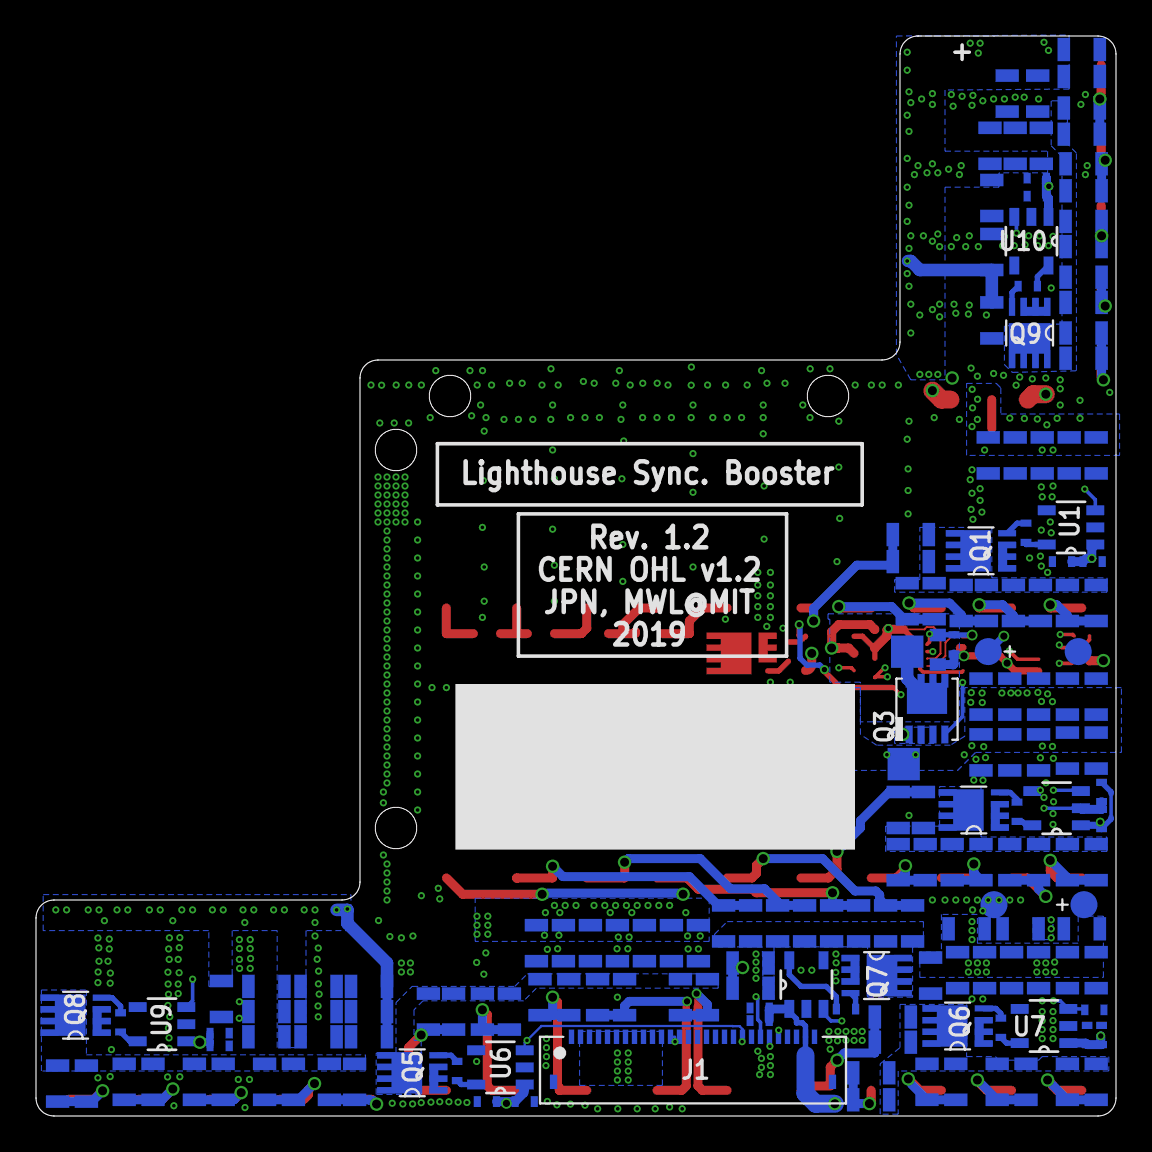
[picture p173: board lighthouse-booster.brd from below]

Board: 4 copper layers, 60.0 x 60.0 mm, 334 parts (166 on the bottom side), 157 nets.
