jonnew/ONIX/breakout/analog-io-breakout.brd

## EAGLE design breakout/analog-io-breakout.brd (2019-08-26)

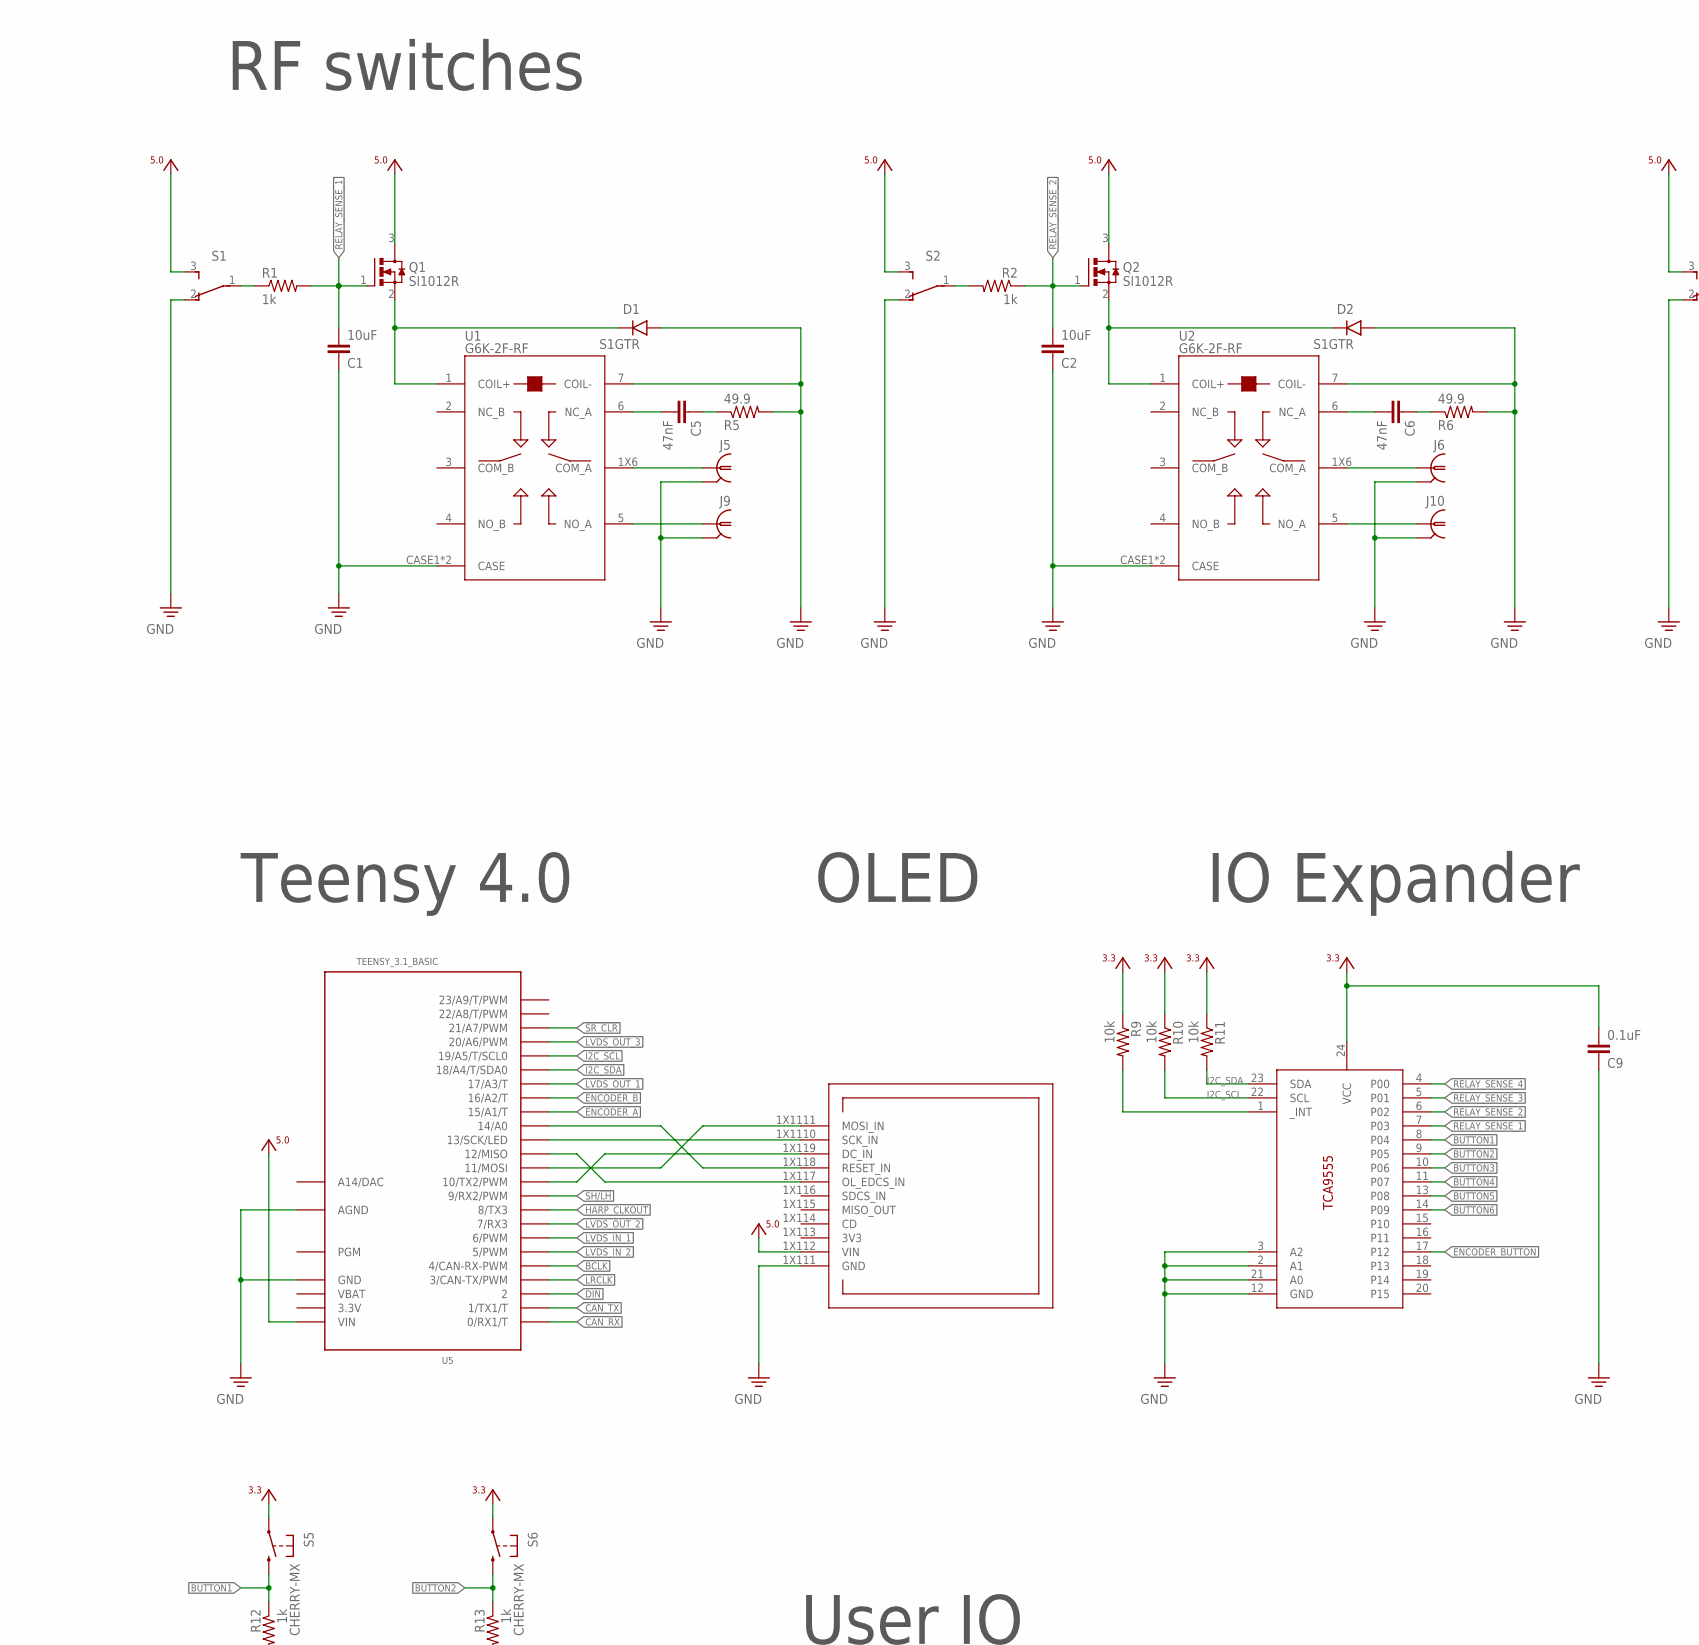
[picture p176: schematic analog-io-breakout.sch, part in row 1, column 1]

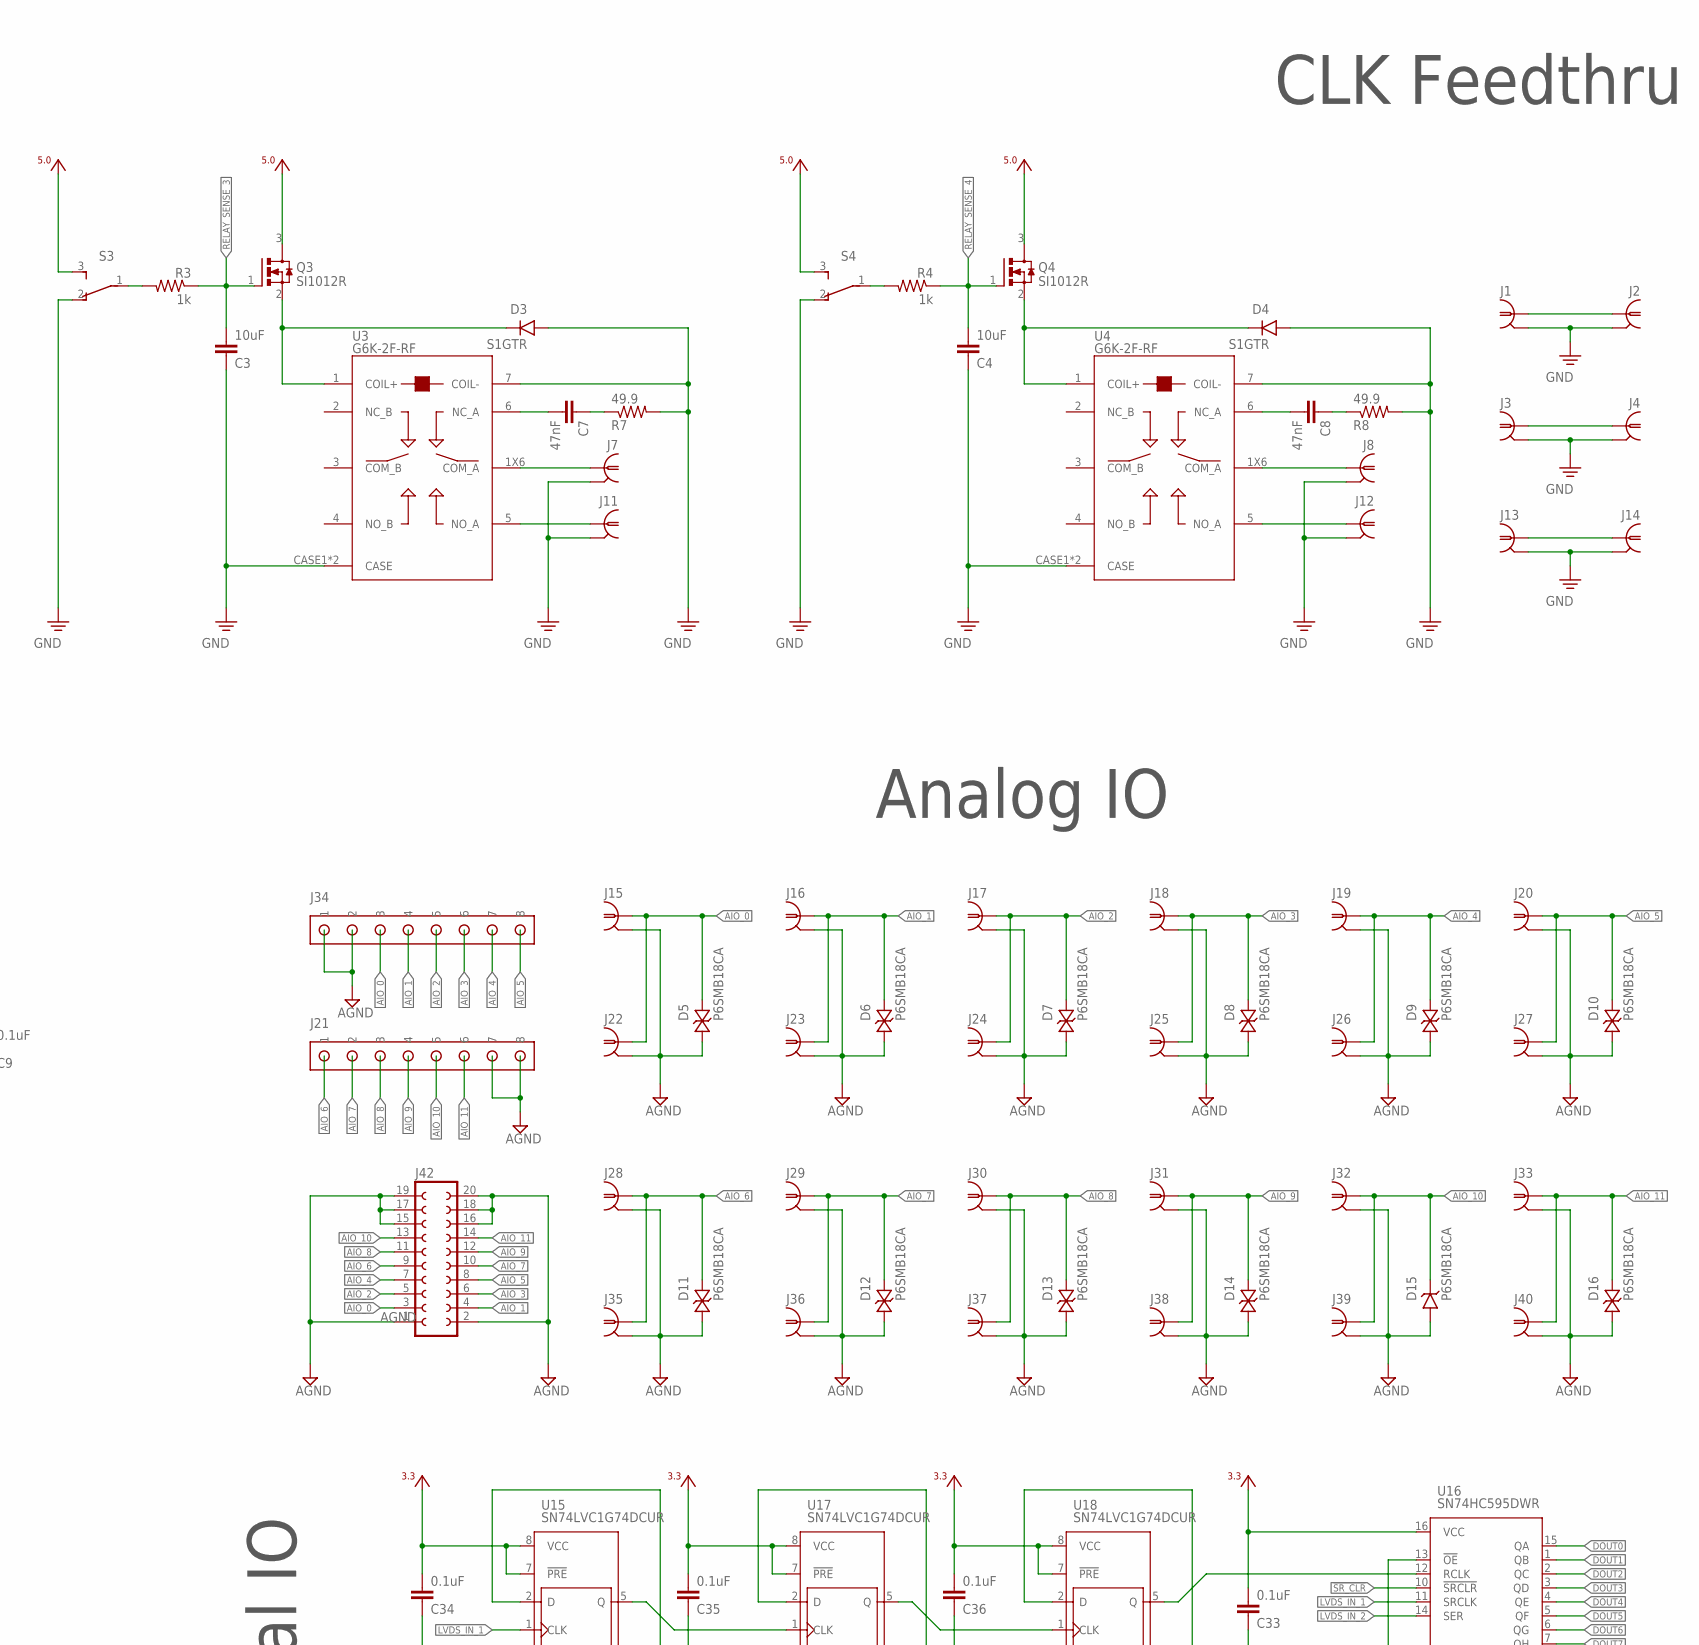
[picture p177: schematic analog-io-breakout.sch, part in row 1, column 2]

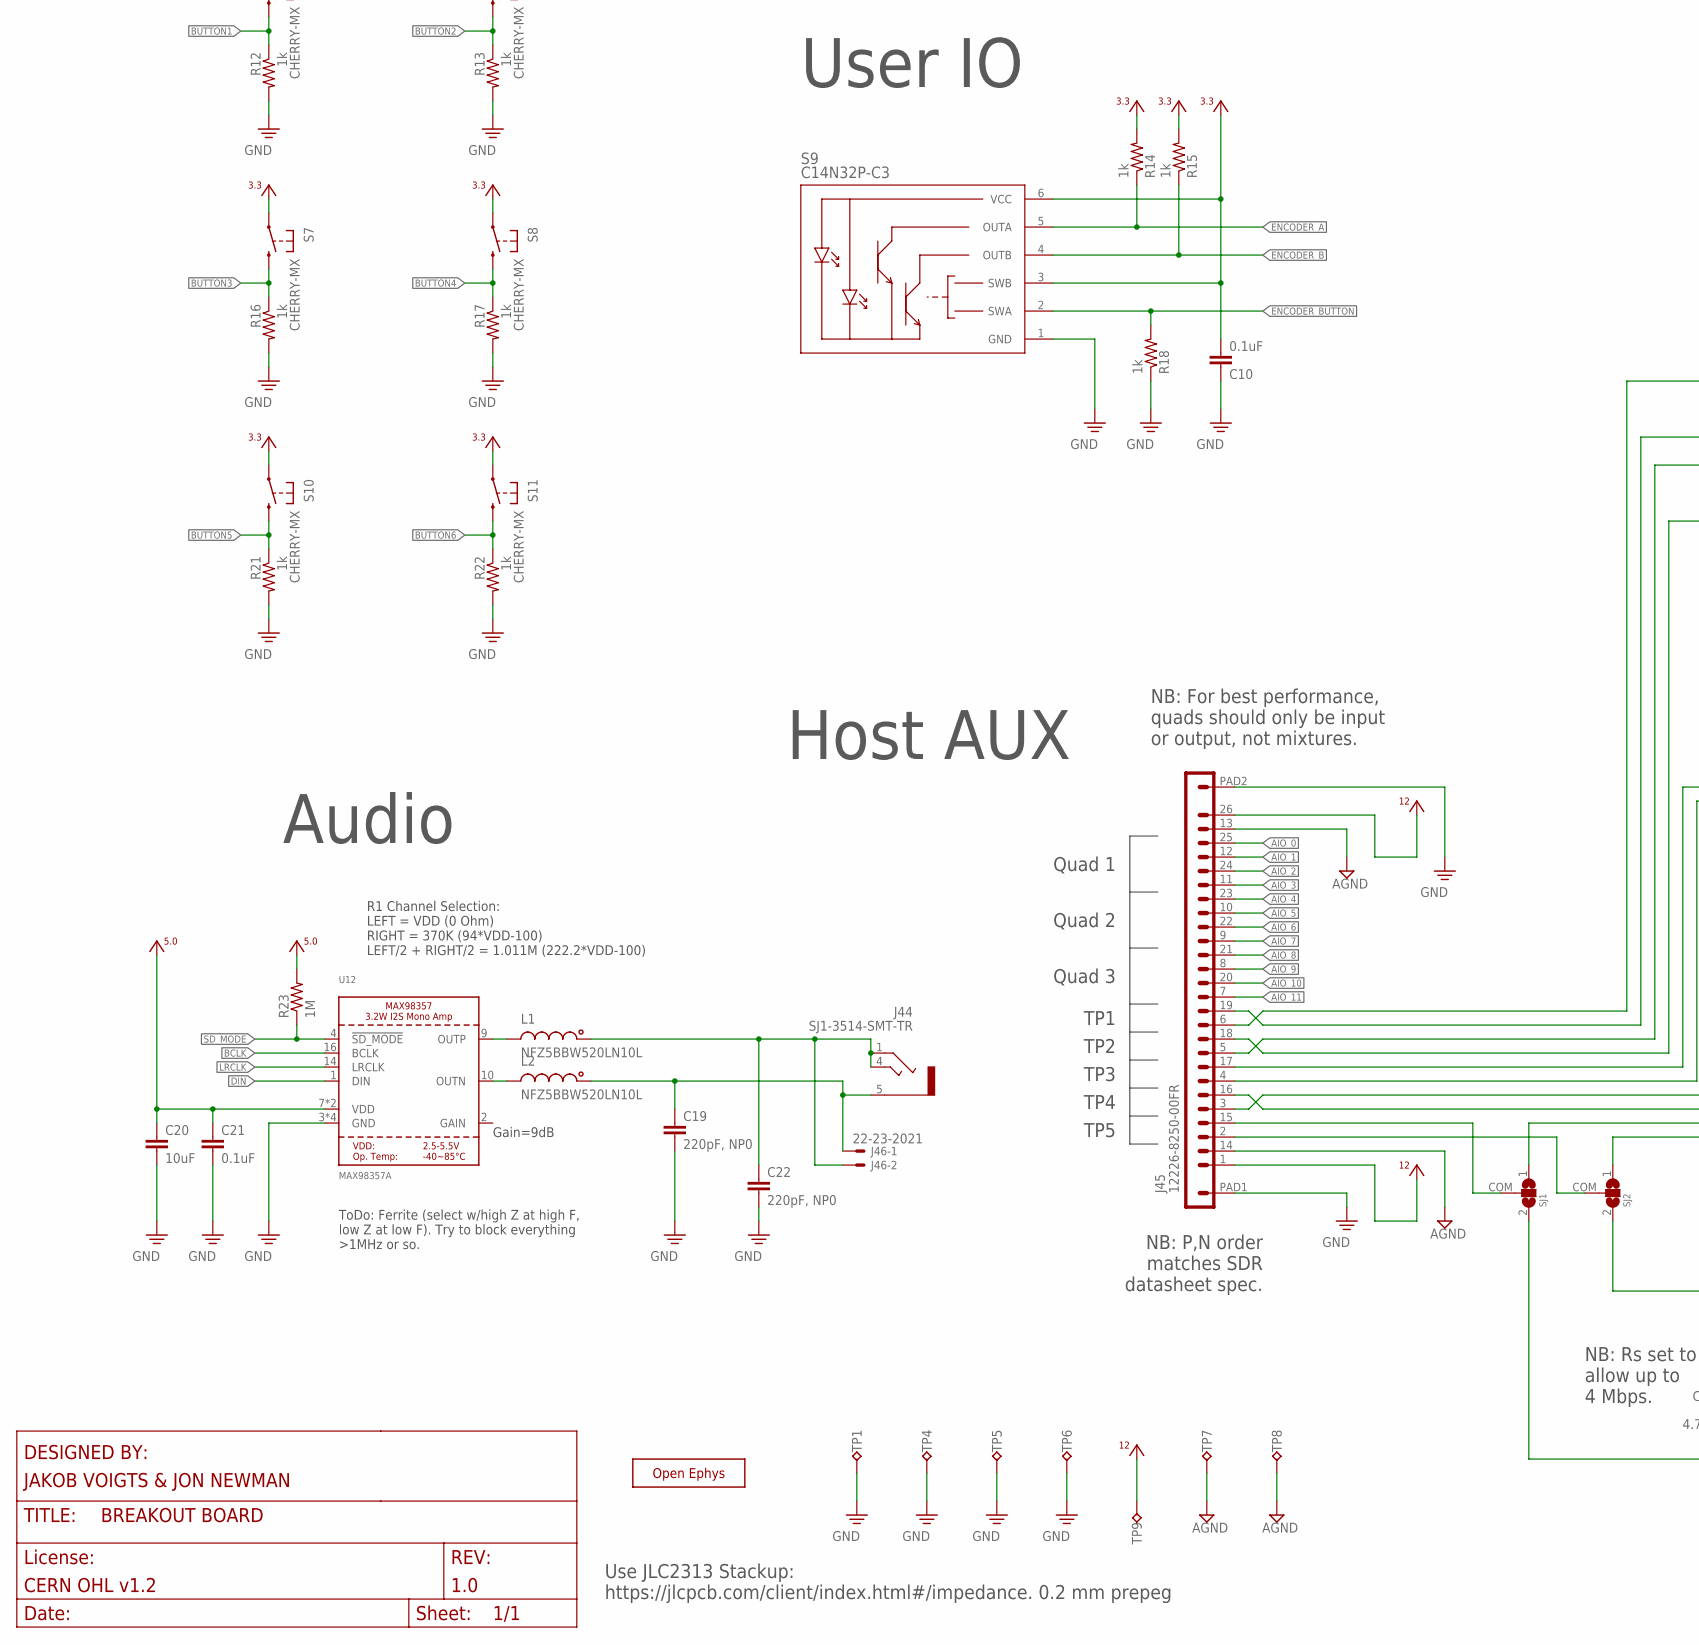
[picture p178: schematic analog-io-breakout.sch, part in row 2, column 1]

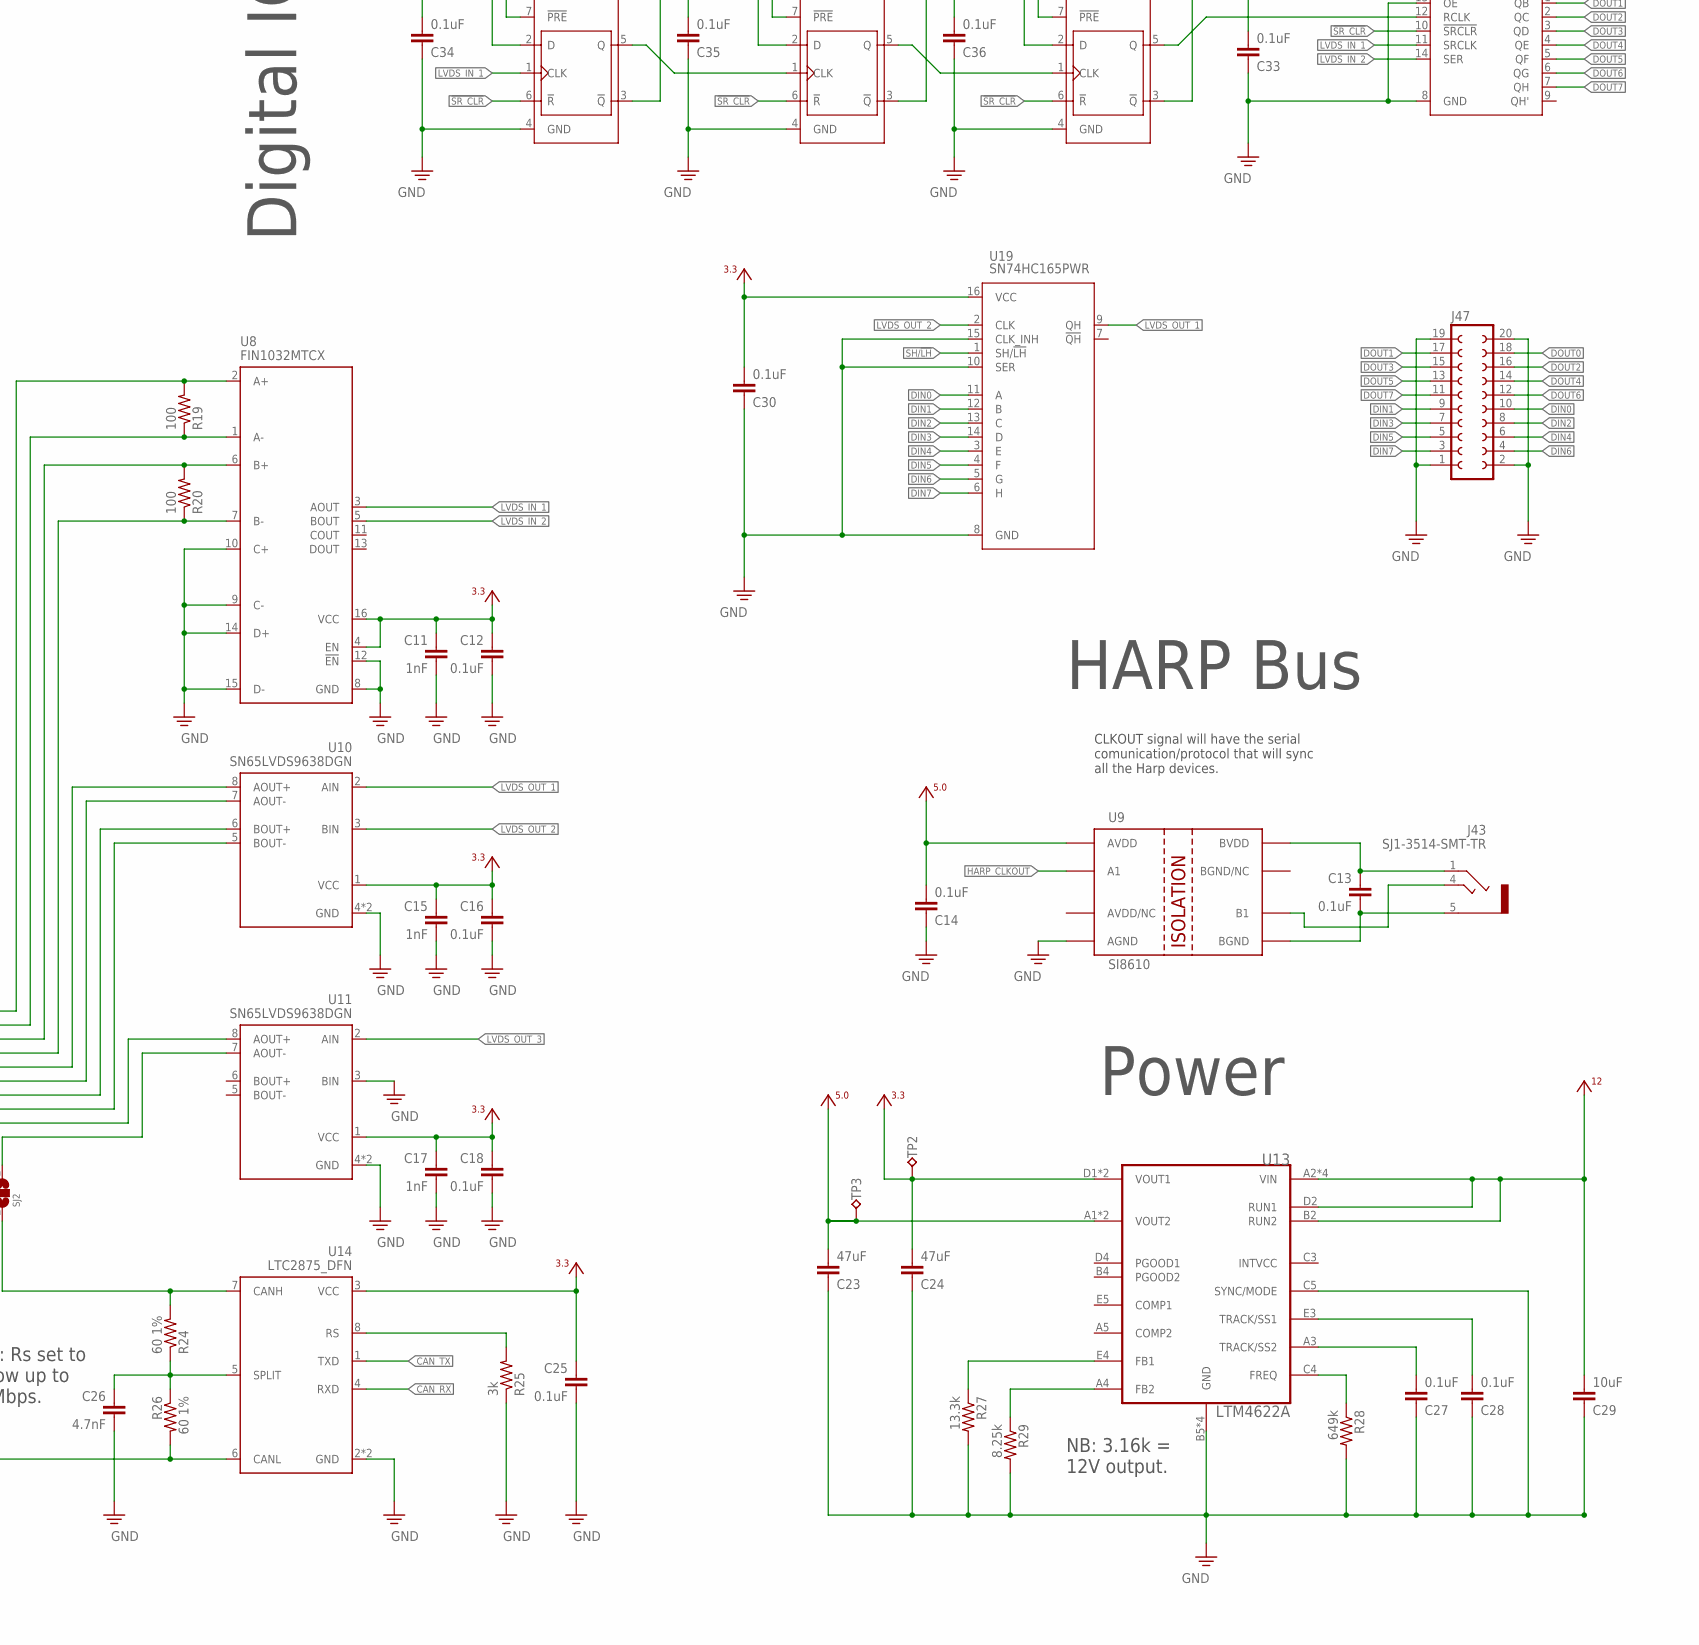
[picture p179: schematic analog-io-breakout.sch, part in row 2, column 2]

Parts:
C1, C2, C3, C4, C20, C29: 10uF; 0805
C5, C6, C7, C8: 47nF; 0402
C9, C10, C12, C13, C14, C16, C18, C21, C25, C27, C28, C30, C33, C34, C35, C36: 0.1uF; 0402
C11, C15, C17: 1nF; 0402
C19, C22: 220pF, NP0; 0402
C23, C24: 47uF; 1210
C26: 4.7nF; 0402
D1, D2, D3, D4: S1GTR; SMA-DO214AC
D5, D6, D7, D8, D9, D10, D11, D12, D13, D14, D15, D16: P6SMB18CA; SMA-DO214AC
J1, J3, J9, J10, J11, J12, J13: COAX_MMCX-THRU; MMCX-THRU
J2, J4, J5, J6, J7, J8, J14, J22, J23, J24, J25, J26, J27, J35, J36, J37, J38, J39, J40: COAX_SMA-VERT; SMA_JACK_142-0701-201
J15, J16, J17, J18, J19, J20, J28, J29, J30, J31, J32, J33: COAX_0731010360; 0731010360
J21, J34: SCREW8
J42, J47: FE10-2
J43, J44: SJ1-3514-SMT-TR; 35RASMT2BHNTRX
J45: 12226-8250-00FR; 12226-82X0-00XX
J46: 22-23-2021
L1, L2: NFZ5BBW520LN10L; 2020
Q1, Q2, Q3, Q4: SI1012R; SC75
R1, R2, R3, R4, R12, R13, R14, R15, R16, R17, R18, R21, R22: 1k; 0402
R5, R6, R7, R8: 49.9; 0402
R9, R10, R11: 10k; 0402
R19, R20: 100; 0402
R23: 1M; 0402
R24, R26: 60 1%; 0402
R25: 3k; 0402
R27: 13.3k; 0402
R28: 649k; 0402
R29: 8.25k; 0402
S1, S2, S3, S4: SPDT_CK-710; CK_7101J1V3QE2
S5, S6, S7, S8, S10, S11: CHERRY-MX
S9: C14N32P-C3
SJ1, SJ2: SJ2_0201; SJ_2_0201
TP1, TP4, TP5, TP6, TP7, TP8: TP_2MM; TESTPOINT_2MM
TP2, TP3: TPB1,27; B1,27
TP9: TPTP12R; TP12R
U1, U2, U3, U4: G6K-2F-RF; G6KU-2F-RF
U5: TEENSY_3.1_BASIC
U6: ADAFRUIT_1_5_OLED
U7: TCA9555; TSSOP-24
U8: FIN1032MTCX; TSSOP-16
U9: SI8610; SO-08
U10, U11: SN65LVDS9638DGN; MSOP-8-PAD-3X3
U12: MAX98357A; QFN16_3MM
U13: LTM4622A; BGA_5X5_625X625
U14: LTC2875_DFN; DFN83X3
U15, U17, U18: SN74LVC1G74DCUR; VSSOP-N8-3X3
U16: SN74HC595DWR; TSSOP-16
U19: SN74HC165PWR; TSSOP-16
X: OE-LOGO_28X20; OE-LOGO-28X20

Connections:
3.3V: U5.3.3V, U5.3.3V1 (3.3V)
!SR_CLR: U5.21/A7 (21/A7/PWM), U15.6 (!R), U16.10 (!SRCLR), U17.6 (!R), U18.6 (!R)
+3V3: C9.2, C10.2, C11.1, C12.1, C15.1, C16.1, C17.1, C18.1, C24.2, C25.1, C30.2, C33.2, C34.2, C35.2, C36.2, R9.1, R10.1, R11.1, R14.2, R15.2, S5.SW1, S6.SW1, S7.SW1, S8.SW1, S9.3 (SWB), S9.6 (VCC), S10.SW1, S11.SW1, TP2.TP, U7.24 (VCC), U8.4 (EN), U8.16 (VCC), U10.1 (VCC), U11.1 (VCC), U13.D1 (VOUT1), U13.E1 (VOUT1), U14.3 (VCC), U15.7 (!PRE), U15.8 (VCC), U16.16 (VCC), U17.7 (!PRE), U17.8 (VCC), U18.7 (!PRE), U18.8 (VCC), U19.16 (VCC)
+5V0: C14.2, C20.1, C21.1, C23.2, Q1.3 (D), Q2.3 (D), Q3.3 (D), Q4.3 (D), R23.2, S1.3, S2.3, S3.3, S4.3, TP3.TP, U5.VIN, U6.1X112 (VIN), U9.1 (AVDD), U12.7 (VDD), U12.8 (VDD), U13.A1 (VOUT2), U13.B1 (VOUT2)
+12V: C29.2, J45.1, J45.26, TP9.TP, U13.A2 (VIN), U13.B2 (RUN2), U13.B3 (VIN), U13.D2 (RUN1), U13.D3 (VIN), U13.E2 (VIN)
AGND: D5.A (1), D6.A (1), D7.A (1), D8.A (1), D9.A (1), D10.A (1), D11.A (1), D12.A (1), D13.A (1), D14.A (1), D15.A, D16.A (1), J15.2, J15.3 (2), J15.4 (2), J15.5 (2), J16.2, J16.3 (2), J16.4 (2), J16.5 (2), J17.2, J17.3 (2), J17.4 (2), J17.5 (2), J18.2, J18.3 (2), J18.4 (2), J18.5 (2), J19.2, J19.3 (2), J19.4 (2), J19.5 (2), J20.2, J20.3 (2), J20.4 (2), J20.5 (2), J21.7, J21.8, J22.GND$1 (2), J22.GND$2 (2), J22.GND$3 (2), J22.GND$4 (2), J23.GND$1 (2), J23.GND$2 (2), J23.GND$3 (2), J23.GND$4 (2), J24.GND$1 (2), J24.GND$2 (2), J24.GND$3 (2), J24.GND$4 (2), J25.GND$1 (2), J25.GND$2 (2), J25.GND$3 (2), J25.GND$4 (2), J26.GND$1 (2), J26.GND$2 (2), J26.GND$3 (2), J26.GND$4 (2), J27.GND$1 (2), J27.GND$2 (2), J27.GND$3 (2), J27.GND$4 (2), J28.2, J28.3 (2), J28.4 (2), J28.5 (2), J29.2, J29.3 (2), J29.4 (2), J29.5 (2), J30.2, J30.3 (2), J30.4 (2), J30.5 (2), J31.2, J31.3 (2), J31.4 (2), J31.5 (2), J32.2, J32.3 (2), J32.4 (2), J32.5 (2), J33.2, J33.3 (2), J33.4 (2), J33.5 (2), J34.1, J34.2, J35.GND$1 (2), J35.GND$2 (2), J35.GND$3 (2), J35.GND$4 (2), J36.GND$1 (2), J36.GND$2 (2), J36.GND$3 (2), J36.GND$4 (2), J37.GND$1 (2), J37.GND$2 (2), J37.GND$3 (2), J37.GND$4 (2), J38.GND$1 (2), J38.GND$2 (2), J38.GND$3 (2), J38.GND$4 (2), J39.GND$1 (2), J39.GND$2 (2), J39.GND$3 (2), J39.GND$4 (2), J40.GND$1 (2), J40.GND$2 (2), J40.GND$3 (2), J40.GND$4 (2), J42.1, J42.2, J42.15, J42.16, J42.17, J42.18, J42.19, J42.20, J45.13, J45.14, TP7.1, TP8.1
AIO_0: D5.C (2), J15.1, J22.CLK (1), J34.3, J42.3, J45.25
AIO_1: D6.C (2), J16.1, J23.CLK (1), J34.4, J42.4, J45.12
AIO_2: D7.C (2), J17.1, J24.CLK (1), J34.5, J42.5, J45.24
AIO_3: D8.C (2), J18.1, J25.CLK (1), J34.6, J42.6, J45.11
AIO_4: D9.C (2), J19.1, J26.CLK (1), J34.7, J42.7, J45.23
AIO_5: D10.C (2), J20.1, J27.CLK (1), J34.8, J42.8, J45.10
AIO_6: D11.C (2), J21.1, J28.1, J35.CLK (1), J42.9, J45.22
AIO_7: D12.C (2), J21.2, J29.1, J36.CLK (1), J42.10, J45.9
AIO_8: D13.C (2), J21.3, J30.1, J37.CLK (1), J42.11, J45.21
AIO_9: D14.C (2), J21.4, J31.1, J38.CLK (1), J42.12, J45.8
AIO_10: D15.C, J21.5, J32.1, J39.CLK (1), J42.13, J45.20
AIO_11: D16.C (2), J21.6, J33.1, J40.CLK (1), J42.14, J45.7
BCLK: U5.4 (4/CAN-RX-PWM), U12.16 (BCLK)
BUTTON1: R12.1, S5.SW2 (S), U7.8 (P04)
BUTTON2: R13.1, S6.SW2 (S), U7.9 (P05)
BUTTON3: R16.1, S7.SW2 (S), U7.10 (P06)
BUTTON4: R17.1, S8.SW2 (S), U7.11 (P07)
BUTTON5: R21.1, S10.SW2 (S), U7.13 (P08)
BUTTON6: R22.1, S11.SW2 (S), U7.14 (P09)
CAN_N: R26.2, SJ1.2, U14.6 (CANL)
CAN_P: R24.2, SJ2.2, U14.7 (CANH)
CAN_RX: U5.0 (0/RX1/T), U14.4 (RXD)
CAN_TX: U5.1 (1/TX1/T), U14.1 (TXD)
CLK/8: U16.12 (RCLK), U18.5 (Q)
DIN: U5.2, U12.1 (DIN)
DIN0: J47.10, U19.11 (A)
DIN1: J47.9, U19.12 (B)
DIN2: J47.8, U19.13 (C)
DIN3: J47.7, U19.14 (D)
DIN4: J47.6, U19.3 (E)
DIN5: J47.5, U19.4 (F)
DIN6: J47.4, U19.5 (G)
DIN7: J47.3, U19.6 (H)
DOUT0: J47.18, U16.15 (QA)
DOUT1: J47.17, U16.1 (QB)
DOUT2: J47.16, U16.2 (QC)
DOUT3: J47.15, U16.3 (QD)
DOUT4: J47.14, U16.4 (QE)
DOUT5: J47.13, U16.5 (QF)
DOUT6: J47.12, U16.6 (QG)
DOUT7: J47.11, U16.7 (QH)
ENCODER_A: R14.1, S9.5 (OUTA), U5.15/A1 (15/A1/T)
ENCODER_B: R15.1, S9.4 (OUTB), U5.16/A2 (16/A2/T)
ENCODER_BUTTON: R18.2, S9.2 (SWA), U7.17 (P12)
GND: C1.1, C2.1, C3.1, C4.1, C9.1, C10.1, C11.2, C12.2, C14.1, C15.2, C16.2, C17.2, C18.2, C19.2, C20.2, C21.2, C22.2, C23.1, C24.1, C25.2, C26.2, C27.1, C28.1, C29.1, C30.1, C33.1, C34.1, C35.1, C36.1, D1.A, D2.A, D3.A, D4.A, J1.GND@1 (2), J1.GND@2 (2), J1.GND@3 (2), J1.GND@4 (2), J2.GND$1 (2), J2.GND$2 (2), J2.GND$3 (2), J2.GND$4 (2), J3.GND@1 (2), J3.GND@2 (2), J3.GND@3 (2), J3.GND@4 (2), J4.GND$1 (2), J4.GND$2 (2), J4.GND$3 (2), J4.GND$4 (2), J5.GND$1 (2), J5.GND$2 (2), J5.GND$3 (2), J5.GND$4 (2), J6.GND$1 (2), J6.GND$2 (2), J6.GND$3 (2), J6.GND$4 (2), J7.GND$1 (2), J7.GND$2 (2), J7.GND$3 (2), J7.GND$4 (2), J8.GND$1 (2), J8.GND$2 (2), J8.GND$3 (2), J8.GND$4 (2), J9.GND@1 (2), J9.GND@2 (2), J9.GND@3 (2), J9.GND@4 (2), J10.GND@1 (2), J10.GND@2 (2), J10.GND@3 (2), J10.GND@4 (2), J11.GND@1 (2), J11.GND@2 (2), J11.GND@3 (2), J11.GND@4 (2), J12.GND@1 (2), J12.GND@2 (2), J12.GND@3 (2), J12.GND@4 (2), J13.GND@1 (2), J13.GND@2 (2), J13.GND@3 (2), J13.GND@4 (2), J14.GND$1 (2), J14.GND$2 (2), J14.GND$3 (2), J14.GND$4 (2), J45.PAD1, J45.PAD2, J47.1, J47.2, J47.19, J47.20, R5.2, R6.2, R7.2, R8.2, R12.2, R13.2, R16.2, R17.2, R18.1, R21.2, R22.2, R25.1, R27.2, R28.2, R29.2, S1.2 (1), S2.2 (1), S3.2 (1), S4.2 (1), S9.1 (GND), TP1.1, TP4.1, TP5.1, TP6.1, U1.7 (COIL-), U1.CASE1 (CASE), U1.CASE2 (CASE), U2.7 (COIL-), U2.CASE1 (CASE), U2.CASE2 (CASE), U3.7 (COIL-), U3.CASE1 (CASE), U3.CASE2 (CASE), U4.7 (COIL-), U4.CASE1 (CASE), U4.CASE2 (CASE), U5.AGND, U5.GND, U5.GND1 (GND), U6.1X111 (GND), U7.2 (A1), U7.3 (A2), U7.12 (GND), U7.21 (A0), U8.8 (GND), U8.9 (C-), U8.10 (C+), U8.12 (!EN), U8.14 (D+), U8.15 (D-), U9.4 (AGND), U10.4 (GND), U10.PAD (GND), U11.3 (BIN), U11.4 (GND), U11.PAD (GND), U12.3 (GND), U12.11 (GND), U12.15 (GND), U12.THERMAL (GND), U13.B5 (GND), U13.C1 (GND), U13.C2 (GND), U13.C5 (SYNC/MODE), U13.D5 (GND), U14.2 (GND), U14.PAD (GND), U15.4 (GND), U16.8 (GND), U16.13 (!OE), U17.4 (GND), U18.4 (GND), U19.8 (GND), U19.10 (SER), U19.15 (CLK_INH)
HARP_CLKOUT: U5.8 (8/TX3), U9.2 (A1)
I2C_SCL: R10.2, U5.19/A5 (19/A5/T/SCL0), U7.22 (SCL)
I2C_SDA: R11.2, U5.18/A4 (18/A4/T/SDA0), U7.23 (SDA)
LRCLK: U5.3 (3/CAN-TX/PWM), U12.14 (LRCLK)
LVDS_DIN0_N1: J45.4, U10.7 (AOUT-)
LVDS_DIN0_P1: J45.17, U10.8 (AOUT+)
LVDS_DIN1_N1: J45.16, U10.5 (BOUT-)
LVDS_DIN1_P1: J45.3, U10.6 (BOUT+)
LVDS_DIN2_N: SJ2.1, U11.7 (AOUT-)
LVDS_DIN2_P: SJ1.1, U11.8 (AOUT+)
LVDS_DOUT0_N1: J45.19, R19.1, U8.1 (A-)
LVDS_DOUT0_P1: J45.6, R19.2, U8.2 (A+)
LVDS_DOUT1_N1: J45.18, R20.1, U8.7 (B-)
LVDS_DOUT1_P1: J45.5, R20.2, U8.6 (B+)
LVDS_IN_1: U5.6 (6/PWM), U8.3 (AOUT), U15.1 (CLK), U16.11 (SRCLK)
LVDS_IN_2: U5.5 (5/PWM), U8.5 (BOUT), U16.14 (SER)
LVDS_OUT_1: U5.17/A3 (17/A3/T), U10.2 (AIN), U19.9 (QH)
LVDS_OUT_2: U5.7 (7/RX3), U10.3 (BIN), U19.2 (CLK)
LVDS_OUT_3: U5.20/A6 (20/A6/PWM), U11.2 (AIN)
unnamed: J1.SIG (1), J2.CLK (1)
unnamed: U5.11 (11/MOSI), U6.1X1111 (MOSI_IN)
unnamed: J3.SIG (1), J4.CLK (1)
unnamed: J13.SIG (1), J14.CLK (1)
unnamed: D1.C, Q1.2 (S), U1.1 (COIL+)
unnamed: U5.13 (13/SCK/LED), U6.1X1110 (SCK_IN)
unnamed: U5.10 (10/TX2/PWM), U6.1X119 (DC_IN)
unnamed: U5.14/A0, U6.1X118 (RESET_IN)
unnamed: U5.12 (12/MISO), U6.1X117 (OL_EDCS_IN)
unnamed: L2.2, U12.10 (OUTN)
unnamed: J45.2, SJ2.COM
unnamed: J45.15, SJ1.COM
unnamed: R25.2, U14.8 (RS)
unnamed: L1.2, U12.9 (OUTP)
unnamed: C5.2, U1.6 (NC_A)
unnamed: C13.1, J43.1, U9.8 (BVDD)
unnamed: C13.2, J43.5, U9.5 (BGND)
unnamed: J43.4, U9.6 (B1)
unnamed: J10.SIG (1), U2.5 (NO_A)
unnamed: U15.2 (D), U15.3 (!Q)
unnamed: U15.5 (Q), U17.1 (CLK)
unnamed: C6.1, R6.1
unnamed: R1.1, S1.1 (2)
unnamed: R29.1, U13.A4 (FB2)
unnamed: R27.1, U13.E4 (FB1)
unnamed: C27.2, U13.A3 (TRACK/SS2)
unnamed: C28.2, U13.E3 (TRACK/SS1)
unnamed: J9.SIG (1), U1.5 (NO_A)
unnamed: J5.CLK (1), U1.1X6 (COM_A)
unnamed: C5.1, R5.1
unnamed: C6.2, U2.6 (NC_A)
unnamed: D3.C, Q3.2 (S), U3.1 (COIL+)
unnamed: C7.1, R7.1
unnamed: J6.CLK (1), U2.1X6 (COM_A)
unnamed: R2.2, S2.1 (2)
unnamed: C7.2, U3.6 (NC_A)
unnamed: J11.SIG (1), U3.5 (NO_A)
unnamed: R3.2, S3.1 (2)
unnamed: D4.C, Q4.2 (S), U4.1 (COIL+)
unnamed: D2.C, Q2.2 (S), U2.1 (COIL+)
unnamed: C26.1, R24.1, R26.1, U14.5 (SPLIT)
unnamed: R9.2, U7.1 (_INT)
unnamed: J7.CLK (1), U3.1X6 (COM_A)
unnamed: R4.2, S4.1 (2)
unnamed: C8.1, R8.1
unnamed: C8.2, U4.6 (NC_A)
unnamed: J12.SIG (1), U4.5 (NO_A)
unnamed: J8.CLK (1), U4.1X6 (COM_A)
unnamed: U17.2 (D), U17.3 (!Q)
unnamed: U17.5 (Q), U18.1 (CLK)
unnamed: U18.2 (D), U18.3 (!Q)
unnamed: R28.1, U13.C4 (FREQ)
RELAY_SENSE_1: C1.2, Q1.1 (G), R1.2, U7.7 (P03)
RELAY_SENSE_2: C2.2, Q2.1 (G), R2.1, U7.6 (P02)
RELAY_SENSE_3: C3.2, Q3.1 (G), R3.1, U7.5 (P01)
RELAY_SENSE_4: C4.2, Q4.1 (G), R4.1, U7.4 (P00)
SD_MODE: R23.1, U12.4 (!SD_MODE)
SH/!LH: U5.9 (9/RX2/PWM), U19.1 (SH/!LH)
VBAT: U5.VBAT
VO+: C22.1, J44.1, J44.4, J46.2, L1.1
VO-: C19.1, J44.5, J46.1, L2.1

Notes on the sheet:
Use JLC2313 Stackup: https://jlcpcb.com/client/index.html#/impedance. 0.2 mm prepeg
Teensy 4.0
Quad 1
Quad 2
Quad 3
NB: For best performance, quads should only be input or output, not mixtures.
TP1
TP2
TP3
TP4
TP5
NB: P,N order matches SDR datasheet spec.
NB: Rs set to allow up to 4 Mbps.
NB: 3.16k = 12V output.
Power
Host AUX
RF switches
Analog IO
CLKOUT signal will have the serial comunication/protocol that will sync all the Harp devices.
HARP Bus
R1 Channel Selection: LEFT = VDD (0 Ohm) RIGHT = 370K (94*VDD-100) LEFT/2 + RIGHT/2 = 1.011M (222.2*VDD-100)
ToDo: Ferrite (select w/high Z at high F, low Z at low F). Try to block everything >1MHz or so.
Gain=9dB
Audio
IO Expander
OLED
User IO
CLK Feedthru
Digital IO

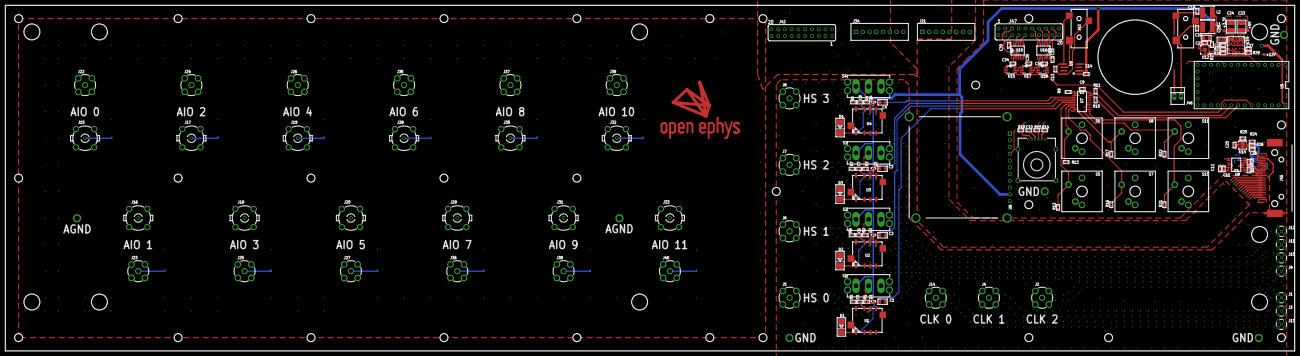
[picture p180: board analog-io-breakout.brd from above]

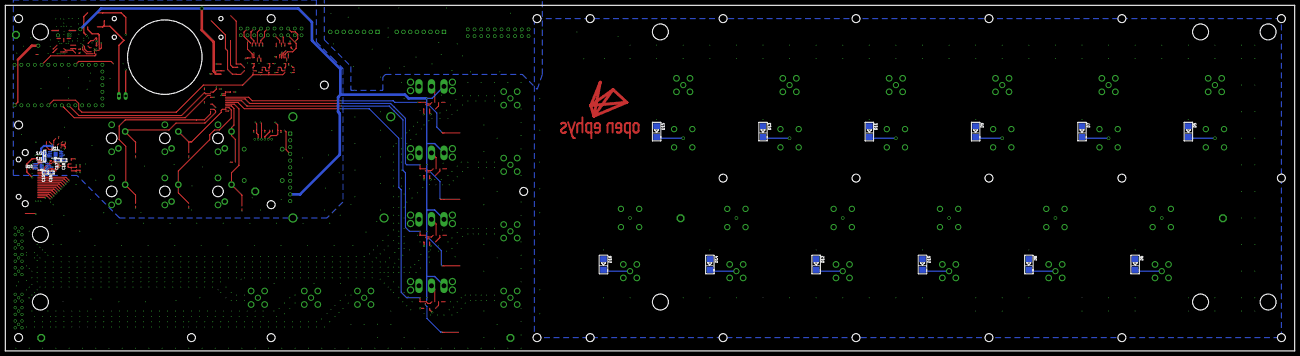
[picture p181: board analog-io-breakout.brd from below]

Board: 4 copper layers, 485.0 x 130.0 mm, 173 parts (20 on the bottom side), 130 nets.
