jonnew/ONIX/eib-256/eib-256.brd

## EAGLE design eib-256/eib-256.brd (2018-07-25)

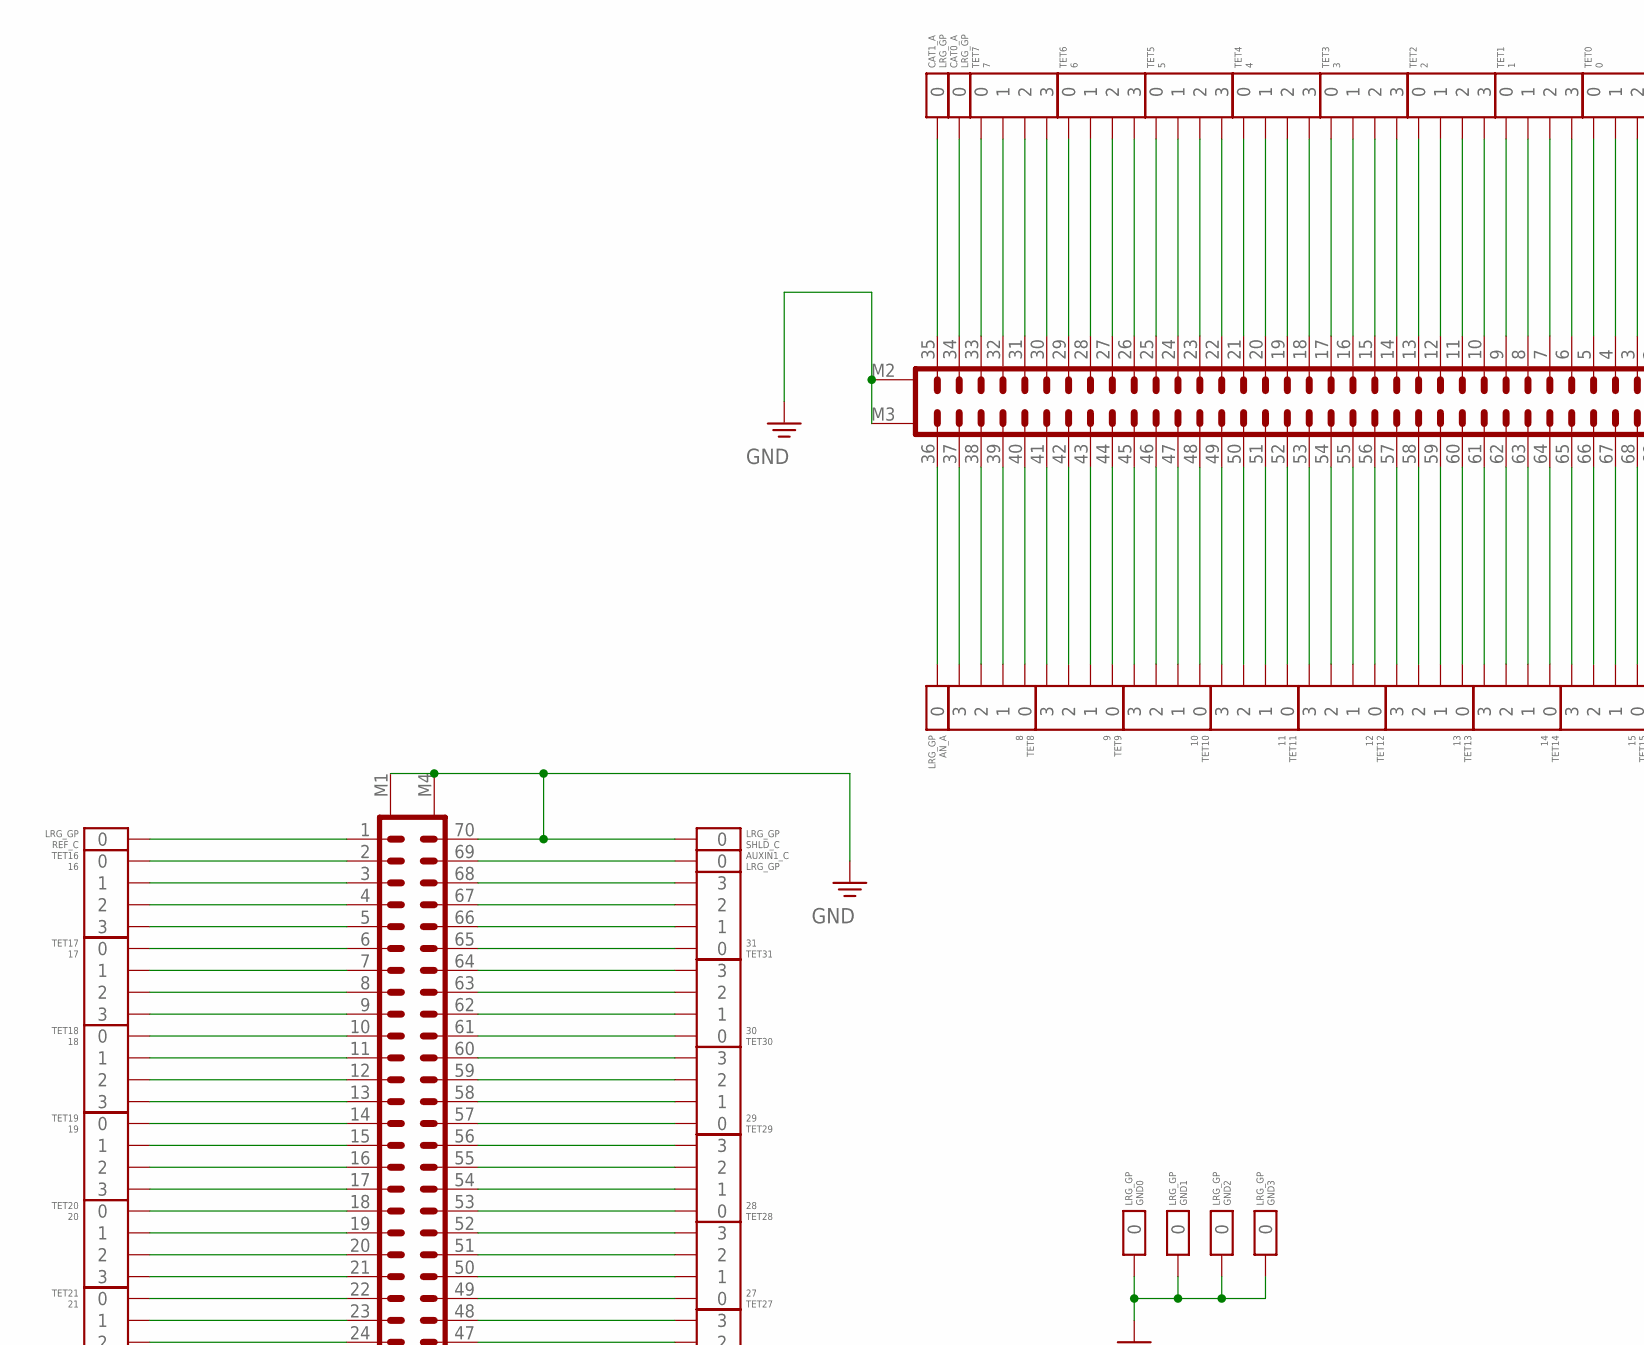
[picture p184: schematic eib-256.sch, part in row 1, column 1]

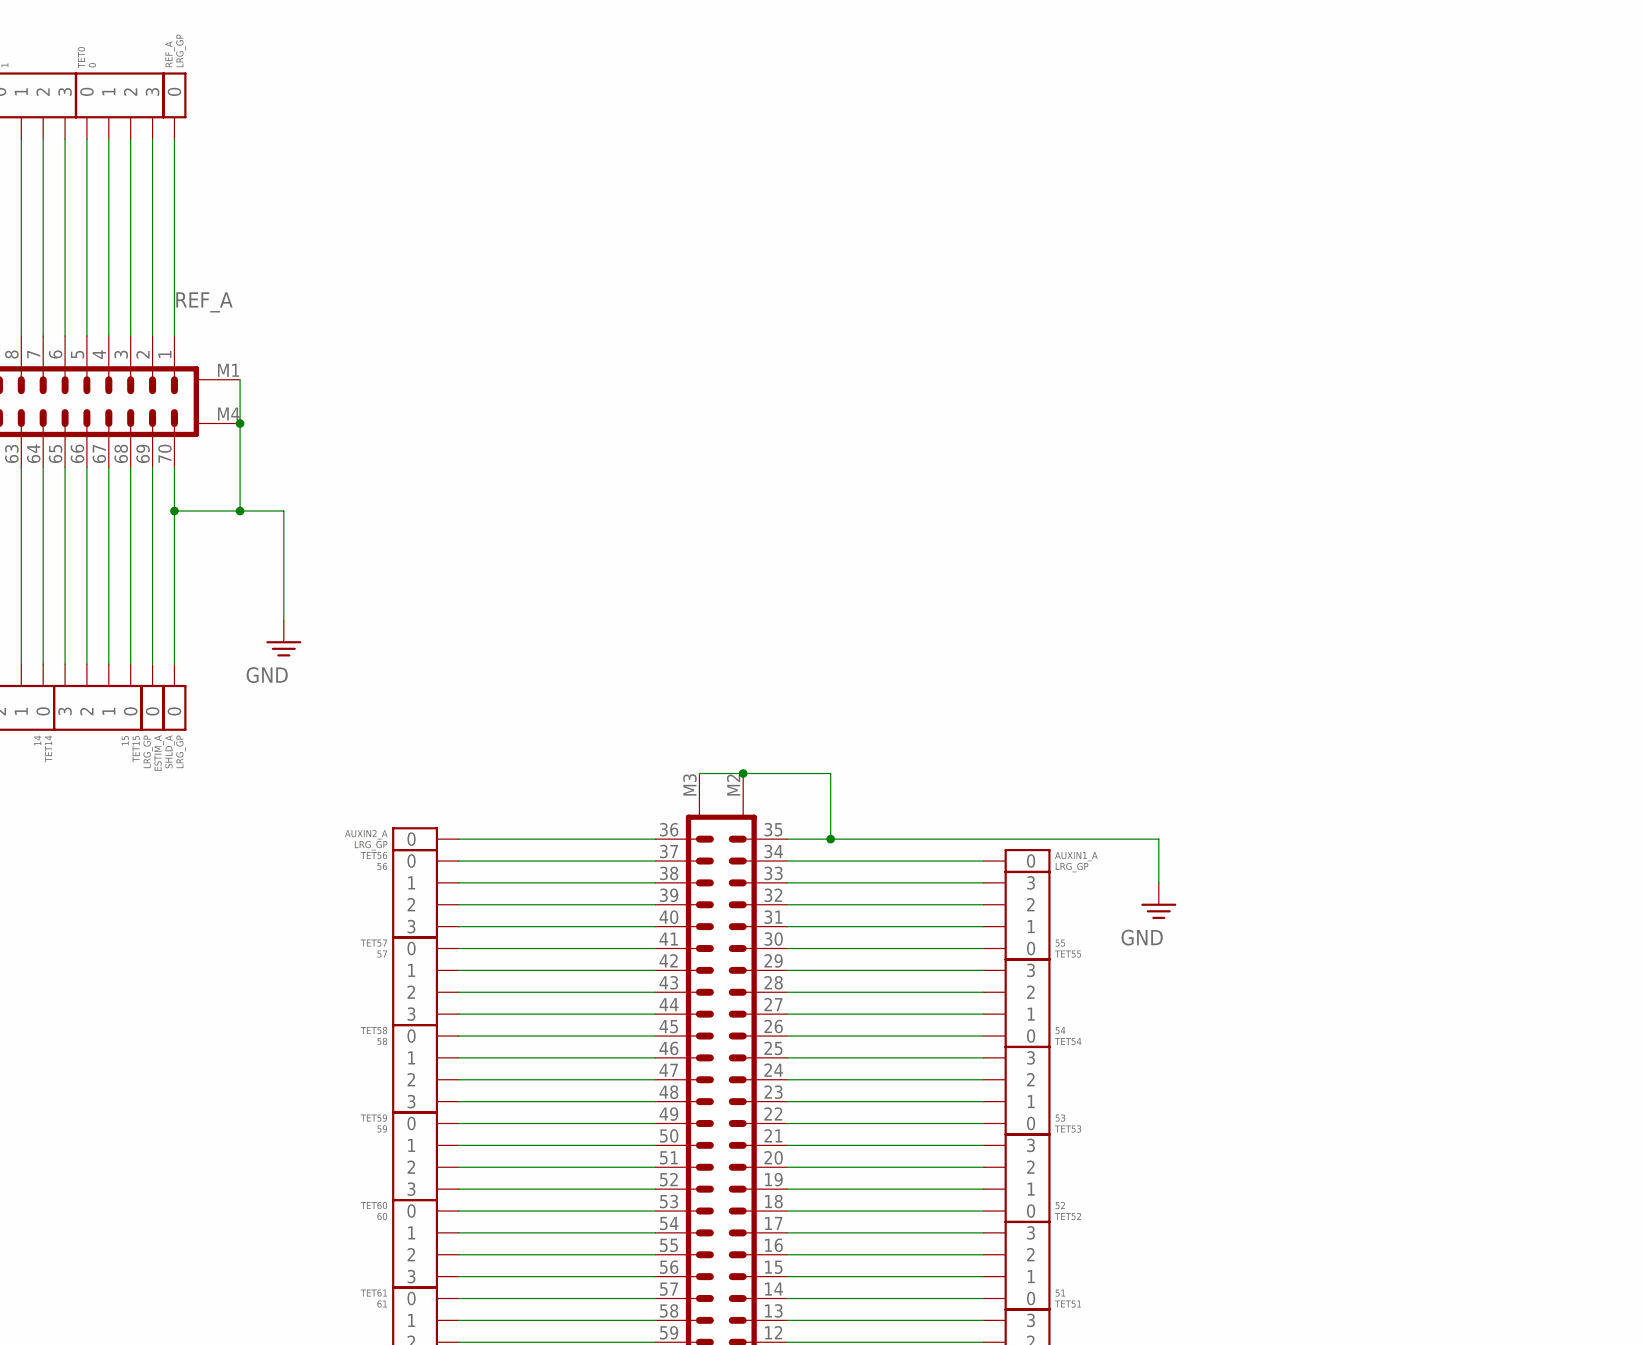
[picture p185: schematic eib-256.sch, part in row 1, column 2]

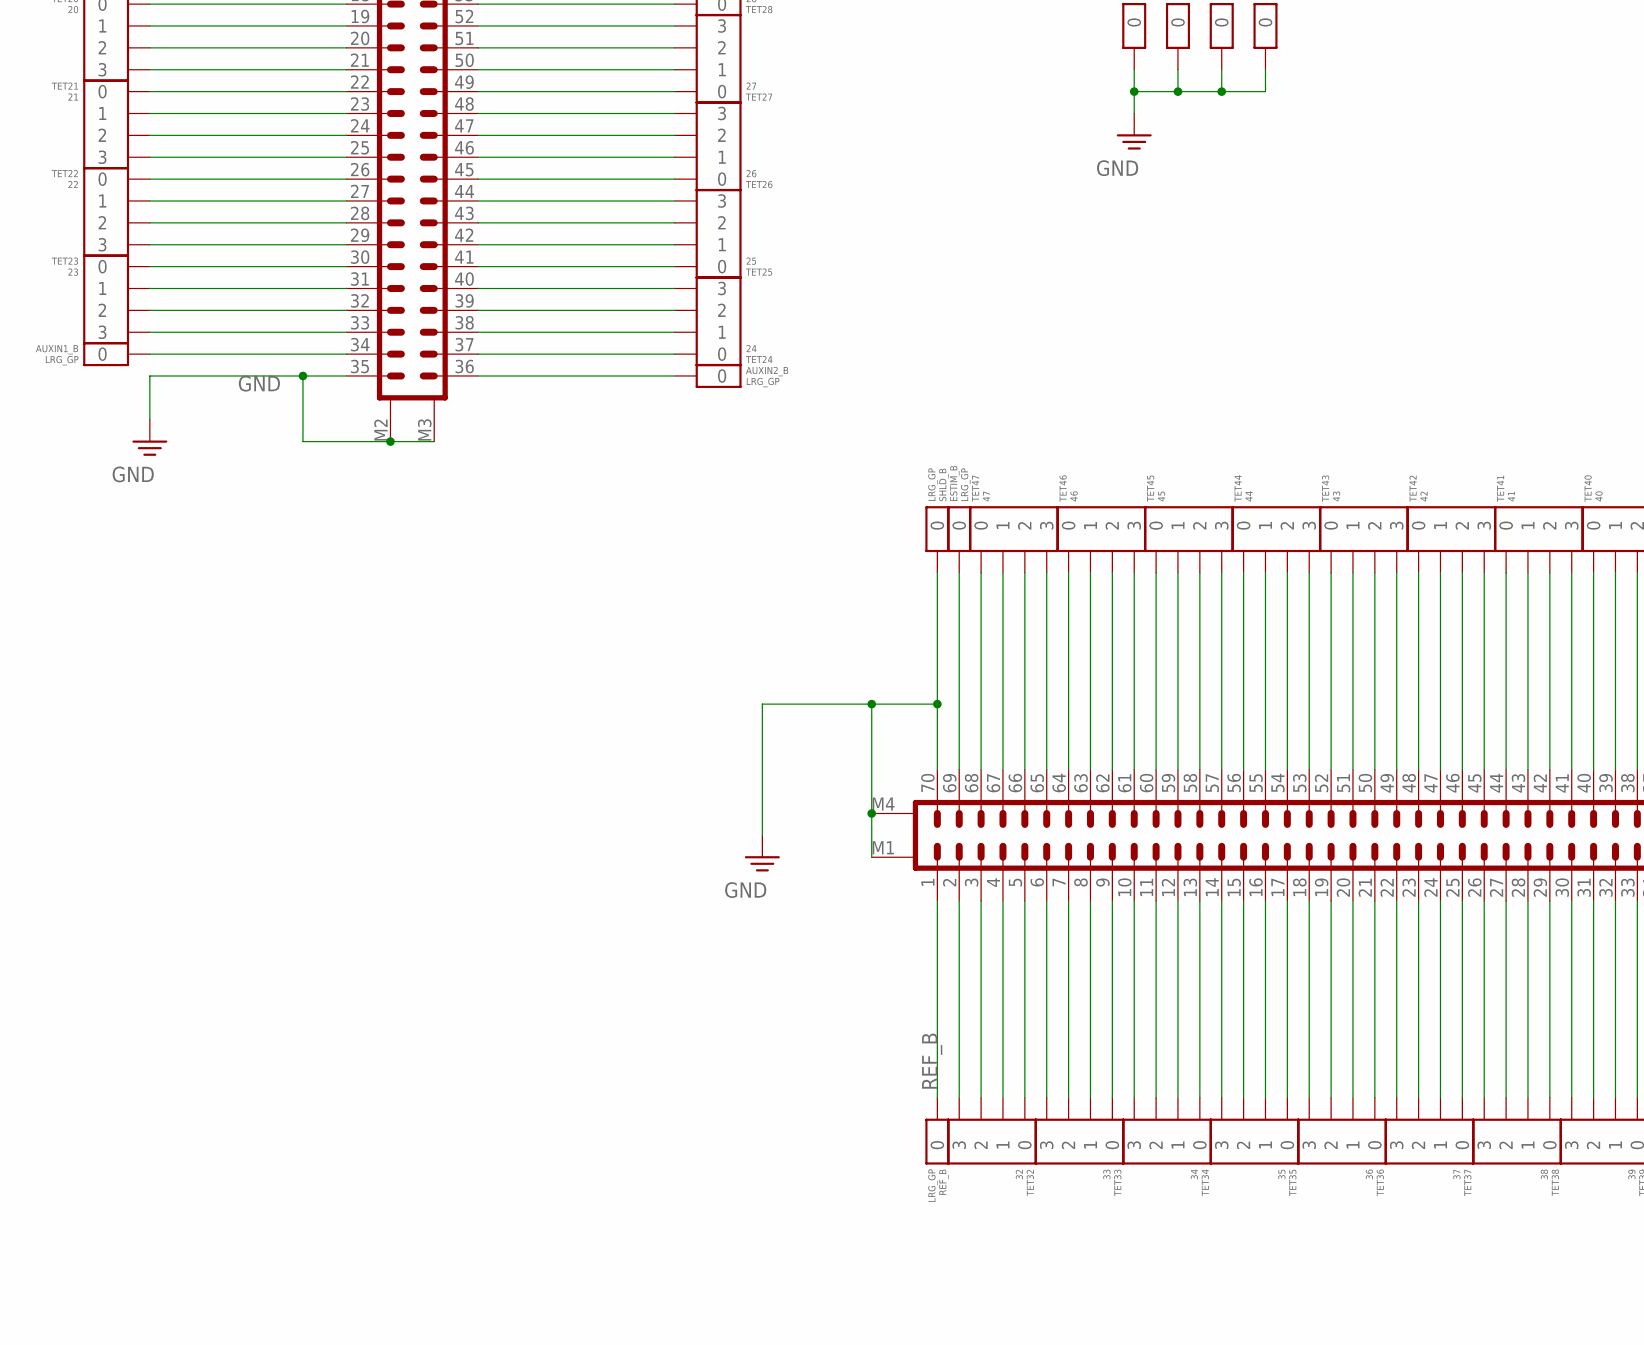
[picture p186: schematic eib-256.sch, part in row 2, column 1]

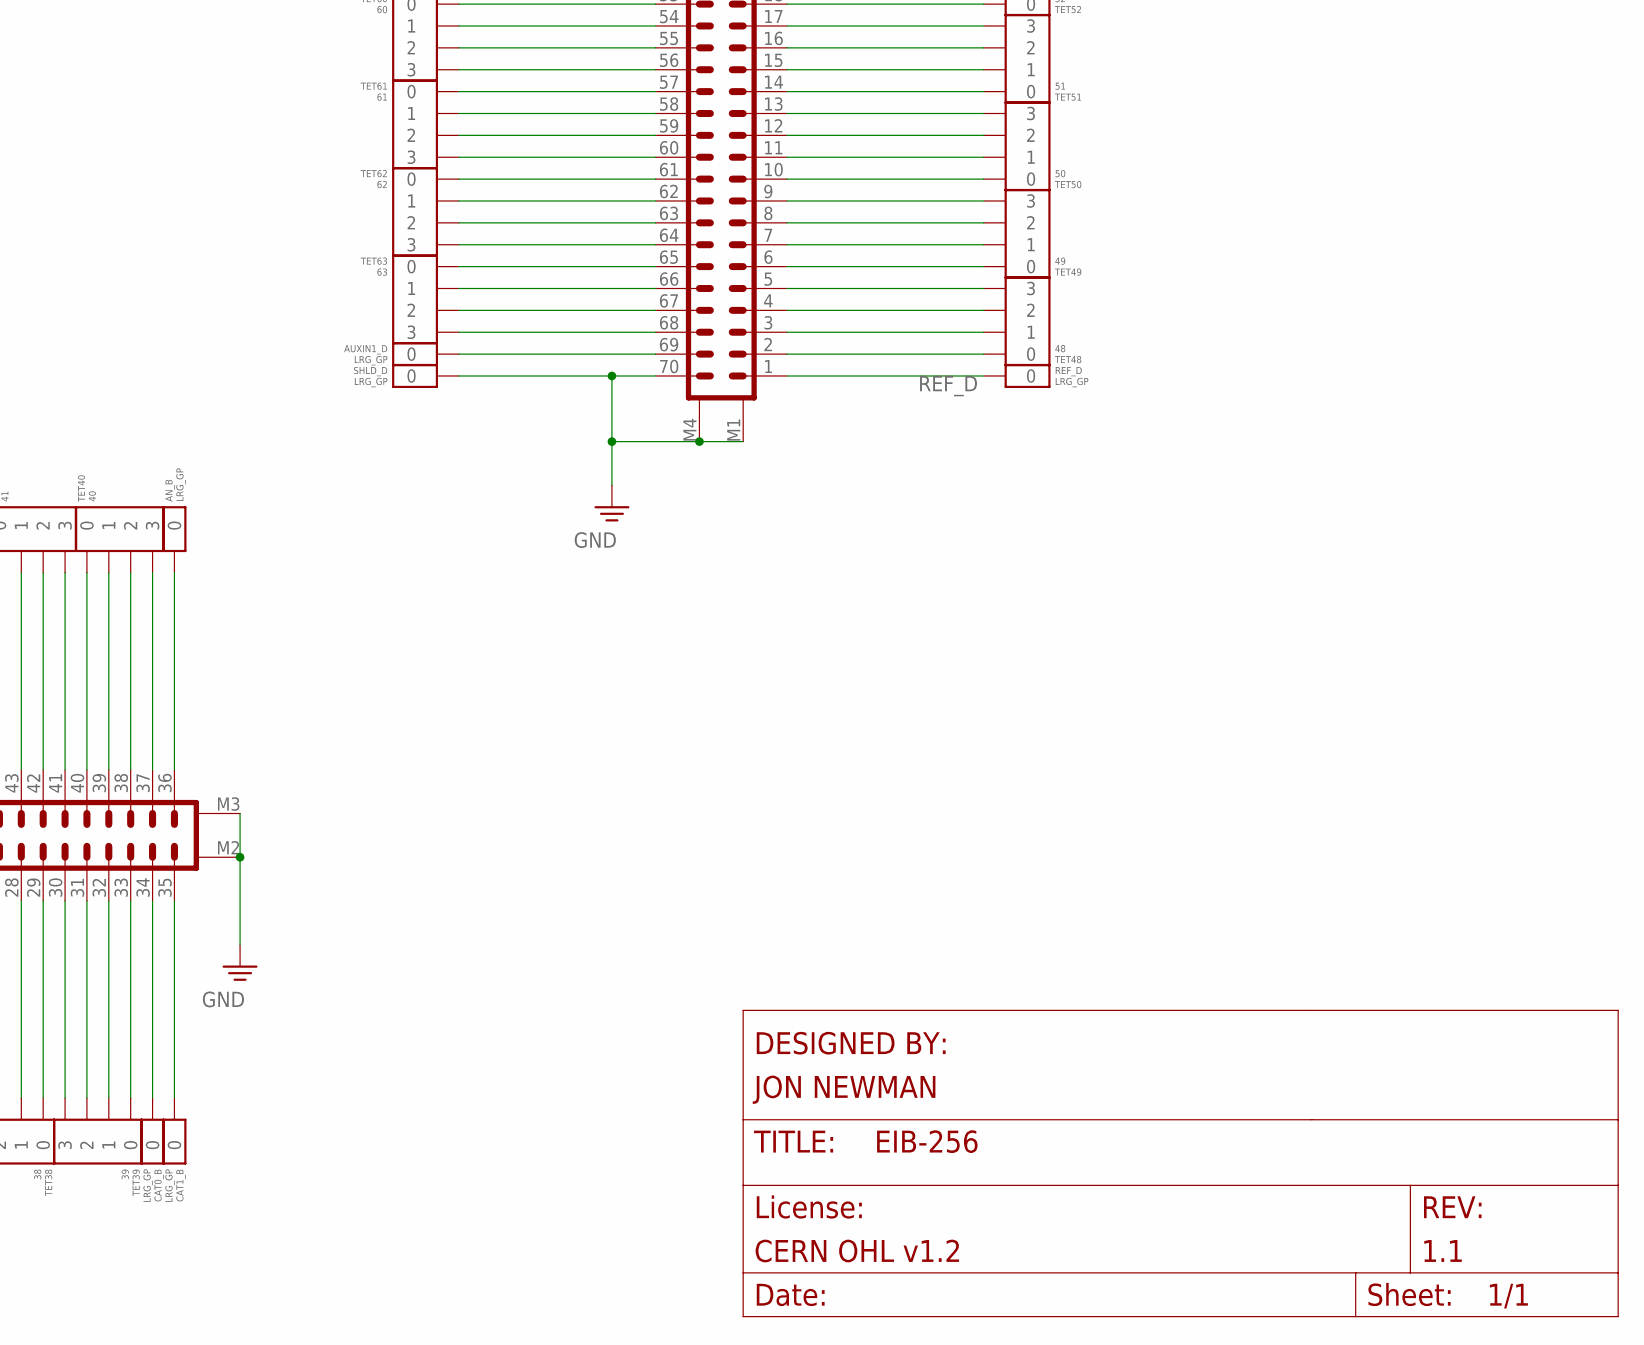
[picture p187: schematic eib-256.sch, part in row 2, column 2]

Parts:
A: DF40HEAD; DF40-70HEAD
AN_A: LRG_GP; GOLDPIN_0.5ID_0.7OD
AN_B: LRG_GP; GOLDPIN_0.5ID_0.7OD
AUXIN1_A, AUXIN1_B, AUXIN1_C, AUXIN1_D, AUXIN2_A, AUXIN2_B: LRG_GP; GOLDPIN_0.5ID_0.7OD
B: DF40HEAD; DF40-70HEAD
C: DF40HEAD; DF40-70HEAD
CAT0_A, CAT0_B, CAT1_A, CAT1_B: LRG_GP; GOLDPIN_0.5ID_0.7OD
D: DF40HEAD; DF40-70HEAD
ESTIM_A: LRG_GP; GOLDPIN_0.5ID_0.7OD
ESTIM_B: LRG_GP; GOLDPIN_0.5ID_0.7OD
GND0, GND1, GND2, GND3: LRG_GP; GOLDPIN_0.5ID_0.7OD
REF_A: LRG_GP; GOLDPIN_0.5ID_0.7OD
REF_B: LRG_GP; GOLDPIN_0.5ID_0.7OD
REF_C: LRG_GP; GOLDPIN_0.5ID_0.7OD
REF_D: LRG_GP; GOLDPIN_0.5ID_0.7OD
SHLD_A: LRG_GP; GOLDPIN_0.5ID_0.7OD
SHLD_B: LRG_GP; GOLDPIN_0.5ID_0.7OD
SHLD_C: LRG_GP; GOLDPIN_0.5ID_0.7OD
SHLD_D: LRG_GP; GOLDPIN_0.5ID_0.7OD
TET0: 0; TETRODE_0.3ID_LINEAR
TET1: 1; TETRODE_0.3ID_LINEAR
TET2: 2; TETRODE_0.3ID_LINEAR
TET3: 3; TETRODE_0.3ID_LINEAR
TET4: 4; TETRODE_0.3ID_LINEAR
TET5: 5; TETRODE_0.3ID_LINEAR
TET6: 6; TETRODE_0.3ID_LINEAR
TET7: 7; TETRODE_0.3ID_LINEAR
TET8: 8; TETRODE_0.3ID_LINEAR
TET9: 9; TETRODE_0.3ID_LINEAR
TET10: 10; TETRODE_0.3ID_LINEAR
TET11: 11; TETRODE_0.3ID_LINEAR
TET12: 12; TETRODE_0.3ID_LINEAR
TET13: 13; TETRODE_0.3ID_LINEAR
TET14: 14; TETRODE_0.3ID_LINEAR
TET15: 15; TETRODE_0.3ID_LINEAR
TET16: 16; TETRODE_0.3ID_LINEAR
TET17: 17; TETRODE_0.3ID_LINEAR
TET18: 18; TETRODE_0.3ID_LINEAR
TET19: 19; TETRODE_0.3ID_LINEAR
TET20: 20; TETRODE_0.3ID_LINEAR
TET21: 21; TETRODE_0.3ID_LINEAR
TET22: 22; TETRODE_0.3ID_LINEAR
TET23: 23; TETRODE_0.3ID_LINEAR
TET24: 24; TETRODE_0.3ID_LINEAR
TET25: 25; TETRODE_0.3ID_LINEAR
TET26: 26; TETRODE_0.3ID_LINEAR
TET27: 27; TETRODE_0.3ID_LINEAR
TET28: 28; TETRODE_0.3ID_LINEAR
TET29: 29; TETRODE_0.3ID_LINEAR
TET30: 30; TETRODE_0.3ID_LINEAR
TET31: 31; TETRODE_0.3ID_LINEAR
TET32: 32; TETRODE_0.3ID_LINEAR
TET33: 33; TETRODE_0.3ID_LINEAR
TET34: 34; TETRODE_0.3ID_LINEAR
TET35: 35; TETRODE_0.3ID_LINEAR
TET36: 36; TETRODE_0.3ID_LINEAR
TET37: 37; TETRODE_0.3ID_LINEAR
TET38: 38; TETRODE_0.3ID_LINEAR
TET39: 39; TETRODE_0.3ID_LINEAR
TET40: 40; TETRODE_0.3ID_LINEAR
TET41: 41; TETRODE_0.3ID_LINEAR
TET42: 42; TETRODE_0.3ID_LINEAR
TET43: 43; TETRODE_0.3ID_LINEAR
TET44: 44; TETRODE_0.3ID_LINEAR
TET45: 45; TETRODE_0.3ID_LINEAR
TET46: 46; TETRODE_0.3ID_LINEAR
TET47: 47; TETRODE_0.3ID_LINEAR
TET48: 48; TETRODE_0.3ID_LINEAR
TET49: 49; TETRODE_0.3ID_LINEAR
TET50: 50; TETRODE_0.3ID_LINEAR
TET51: 51; TETRODE_0.3ID_LINEAR
TET52: 52; TETRODE_0.3ID_LINEAR
TET53: 53; TETRODE_0.3ID_LINEAR
TET54: 54; TETRODE_0.3ID_LINEAR
TET55: 55; TETRODE_0.3ID_LINEAR
TET56: 56; TETRODE_0.3ID_LINEAR
TET57: 57; TETRODE_0.3ID_LINEAR
TET58: 58; TETRODE_0.3ID_LINEAR
TET59: 59; TETRODE_0.3ID_LINEAR
TET60: 60; TETRODE_0.3ID_LINEAR
TET61: 61; TETRODE_0.3ID_LINEAR
TET62: 62; TETRODE_0.3ID_LINEAR
TET63: 63; TETRODE_0.3ID_LINEAR

Connections:
AN_A: A.36, AN_A.P$1
AN_B: AN_B.P$1, B.36
AUXIN1_A: AUXIN1_A.P$1, D.34
AUXIN1_B: AUXIN1_B.P$1, C.34
AUXIN1_C: AUXIN1_C.P$1, C.69
AUXIN1_D: AUXIN1_D.P$1, D.69
AUXIN2_A: AUXIN2_A.P$1, D.36
AUXIN2_B: AUXIN2_B.P$1, C.36
CAT0_A: A.34, CAT0_A.P$1
CAT0_B: B.34, CAT0_B.P$1
CAT1_A: A.35, CAT1_A.P$1
CAT1_B: B.35, CAT1_B.P$1
ESTIM_A: A.69, ESTIM_A.P$1
ESTIM_B: B.69, ESTIM_B.P$1
GND: A.70, A.M1, A.M2, A.M3, A.M4, B.70, B.M1, B.M2, B.M3, B.M4, C.35, C.70, C.M1, C.M2, C.M3, C.M4, D.35, D.70, D.M1, D.M2, D.M3, D.M4, GND0.P$1, GND1.P$1, GND2.P$1, GND3.P$1, SHLD_A.P$1, SHLD_B.P$1, SHLD_C.P$1, SHLD_D.P$1
unnamed: D.2, TET48.0
unnamed: D.3, TET48.1
unnamed: D.4, TET48.2
unnamed: D.5, TET48.3
unnamed: D.6, TET49.0
unnamed: D.7, TET49.1
unnamed: D.8, TET49.2
unnamed: D.9, TET49.3
unnamed: D.10, TET50.0
unnamed: D.11, TET50.1
unnamed: D.12, TET50.2
unnamed: D.13, TET50.3
unnamed: D.14, TET51.0
unnamed: D.15, TET51.1
unnamed: D.16, TET51.2
unnamed: D.17, TET51.3
unnamed: D.18, TET52.0
unnamed: D.19, TET52.1
unnamed: D.20, TET52.2
unnamed: D.21, TET52.3
unnamed: D.22, TET53.0
unnamed: D.23, TET53.1
unnamed: D.24, TET53.2
unnamed: D.25, TET53.3
unnamed: D.26, TET54.0
unnamed: D.27, TET54.1
unnamed: D.28, TET54.2
unnamed: D.29, TET54.3
unnamed: D.30, TET55.0
unnamed: D.31, TET55.1
unnamed: D.32, TET55.2
unnamed: D.42, TET57.1
unnamed: D.43, TET57.2
unnamed: D.44, TET57.3
unnamed: D.45, TET58.0
unnamed: D.46, TET58.1
unnamed: D.47, TET58.2
unnamed: D.48, TET58.3
unnamed: D.49, TET59.0
unnamed: D.50, TET59.1
unnamed: D.51, TET59.2
unnamed: D.52, TET59.3
unnamed: D.53, TET60.0
unnamed: D.54, TET60.1
unnamed: D.55, TET60.2
unnamed: D.56, TET60.3
unnamed: D.57, TET61.0
unnamed: D.58, TET61.1
unnamed: D.59, TET61.2
unnamed: D.60, TET61.3
unnamed: D.61, TET62.0
unnamed: D.62, TET62.1
unnamed: D.63, TET62.2
unnamed: D.64, TET62.3
unnamed: D.65, TET63.0
unnamed: D.66, TET63.1
unnamed: D.67, TET63.2
unnamed: D.68, TET63.3
unnamed: D.41, TET57.0
unnamed: D.40, TET56.3
unnamed: D.39, TET56.2
unnamed: D.38, TET56.1
unnamed: D.33, TET55.3
unnamed: D.37, TET56.0
unnamed: C.3, TET16.1
unnamed: C.2, TET16.0
unnamed: C.32, TET23.2
unnamed: C.33, TET23.3
unnamed: C.28, TET22.2
unnamed: C.29, TET22.3
unnamed: C.24, TET21.2
unnamed: C.25, TET21.3
unnamed: C.20, TET20.2
unnamed: C.21, TET20.3
unnamed: C.16, TET19.2
unnamed: C.17, TET19.3
unnamed: C.12, TET18.2
unnamed: C.13, TET18.3
unnamed: C.8, TET17.2
unnamed: C.9, TET17.3
unnamed: C.66, TET31.1
unnamed: C.65, TET31.0
unnamed: C.62, TET30.1
unnamed: C.64, TET30.3
unnamed: C.58, TET29.1
unnamed: C.57, TET29.0
unnamed: C.54, TET28.1
unnamed: C.53, TET28.0
unnamed: C.49, TET27.0
unnamed: C.50, TET27.1
unnamed: C.46, TET26.1
unnamed: C.45, TET26.0
unnamed: C.42, TET25.1
unnamed: C.41, TET25.0
unnamed: C.38, TET24.1
unnamed: C.37, TET24.0
unnamed: B.33, TET39.0
unnamed: B.32, TET39.1
unnamed: B.31, TET39.2
unnamed: B.30, TET39.3
unnamed: B.29, TET38.0
unnamed: B.28, TET38.1
unnamed: A.33, TET7.0
unnamed: A.32, TET7.1
unnamed: A.31, TET7.2
unnamed: A.30, TET7.3
unnamed: A.29, TET6.0
unnamed: A.28, TET6.1
unnamed: A.27, TET6.2
unnamed: A.26, TET6.3
unnamed: A.25, TET5.0
unnamed: A.24, TET5.1
unnamed: A.23, TET5.2
unnamed: A.22, TET5.3
unnamed: A.21, TET4.0
unnamed: A.20, TET4.1
unnamed: A.19, TET4.2
unnamed: A.18, TET4.3
unnamed: A.17, TET3.0
unnamed: A.16, TET3.1
unnamed: A.15, TET3.2
unnamed: A.14, TET3.3
unnamed: A.13, TET2.0
unnamed: A.12, TET2.1
unnamed: A.11, TET2.2
unnamed: A.10, TET2.3
unnamed: A.9, TET1.0
unnamed: A.8, TET1.1
unnamed: A.7, TET1.2
unnamed: A.6, TET1.3
unnamed: A.5, TET0.0
unnamed: A.4, TET0.1
unnamed: A.3, TET0.2
unnamed: A.2, TET0.3
unnamed: A.38, TET8.2
unnamed: A.39, TET8.1
unnamed: A.40, TET8.0
unnamed: A.41, TET9.3
unnamed: A.42, TET9.2
unnamed: A.43, TET9.1
unnamed: A.44, TET9.0
unnamed: A.45, TET10.3
unnamed: A.46, TET10.2
unnamed: A.47, TET10.1
unnamed: A.48, TET10.0
unnamed: A.49, TET11.3
unnamed: A.50, TET11.2
unnamed: A.51, TET11.1
unnamed: A.52, TET11.0
unnamed: A.53, TET12.3
unnamed: A.54, TET12.2
unnamed: A.55, TET12.1
unnamed: A.56, TET12.0
unnamed: A.57, TET13.3
unnamed: A.58, TET13.2
unnamed: A.59, TET13.1
unnamed: A.60, TET13.0
unnamed: A.61, TET14.3
unnamed: A.62, TET14.2
unnamed: A.63, TET14.1
unnamed: A.64, TET14.0
unnamed: A.65, TET15.3
unnamed: A.66, TET15.2
unnamed: A.67, TET15.1
unnamed: A.68, TET15.0
unnamed: B.27, TET38.2
unnamed: B.26, TET38.3
unnamed: B.25, TET37.0
unnamed: B.24, TET37.1
unnamed: B.23, TET37.2
unnamed: B.22, TET37.3
unnamed: B.21, TET36.0
unnamed: B.20, TET36.1
unnamed: B.19, TET36.2
unnamed: B.18, TET36.3
unnamed: B.17, TET35.0
unnamed: B.16, TET35.1
unnamed: B.15, TET35.2
unnamed: B.14, TET35.3
unnamed: B.13, TET34.0
unnamed: B.12, TET34.1
unnamed: B.11, TET34.2
unnamed: B.10, TET34.3
unnamed: B.9, TET33.0
unnamed: B.8, TET33.1
unnamed: B.7, TET33.2
unnamed: B.6, TET33.3
unnamed: B.5, TET32.0
unnamed: B.4, TET32.1
unnamed: B.3, TET32.2
unnamed: B.38, TET40.2
unnamed: B.39, TET40.1
unnamed: B.40, TET40.0
unnamed: B.41, TET41.3
unnamed: B.42, TET41.2
unnamed: B.43, TET41.1
unnamed: B.44, TET41.0
unnamed: B.45, TET42.3
unnamed: B.46, TET42.2
unnamed: B.47, TET42.1
unnamed: B.48, TET42.0
unnamed: B.49, TET43.3
unnamed: B.50, TET43.2
unnamed: B.51, TET43.1
unnamed: B.52, TET43.0
unnamed: B.53, TET44.3
unnamed: B.54, TET44.2
unnamed: B.55, TET44.1
unnamed: B.56, TET44.0
unnamed: B.57, TET45.3
unnamed: B.58, TET45.2
unnamed: B.59, TET45.1
unnamed: B.60, TET45.0
unnamed: B.61, TET46.3
unnamed: B.62, TET46.2
unnamed: B.63, TET46.1
unnamed: B.64, TET46.0
unnamed: B.65, TET47.3
unnamed: B.66, TET47.2
unnamed: B.67, TET47.1
unnamed: B.68, TET47.0
unnamed: B.2, TET32.3
unnamed: B.37, TET40.3
unnamed: C.4, TET16.2
unnamed: C.5, TET16.3
unnamed: C.6, TET17.0
unnamed: C.7, TET17.1
unnamed: C.10, TET18.0
unnamed: C.11, TET18.1
unnamed: C.14, TET19.0
unnamed: C.15, TET19.1
unnamed: C.18, TET20.0
unnamed: C.19, TET20.1
unnamed: C.22, TET21.0
unnamed: C.23, TET21.1
unnamed: C.27, TET22.1
unnamed: C.26, TET22.0
unnamed: C.30, TET23.0
unnamed: C.31, TET23.1
unnamed: C.43, TET25.2
unnamed: C.48, TET26.3
unnamed: C.47, TET26.2
unnamed: C.52, TET27.3
unnamed: C.51, TET27.2
unnamed: C.56, TET28.3
unnamed: C.55, TET28.2
unnamed: C.60, TET29.3
unnamed: C.59, TET29.2
unnamed: C.61, TET30.0
unnamed: C.63, TET30.2
unnamed: C.68, TET31.3
unnamed: C.67, TET31.2
unnamed: C.44, TET25.3
unnamed: C.39, TET24.2
unnamed: C.40, TET24.3
unnamed: A.37, TET8.3
REF_A: A.1, REF_A.P$1
REF_B: B.1, REF_B.P$1
REF_C: C.1, REF_C.P$1
REF_D: D.1, REF_D.P$1

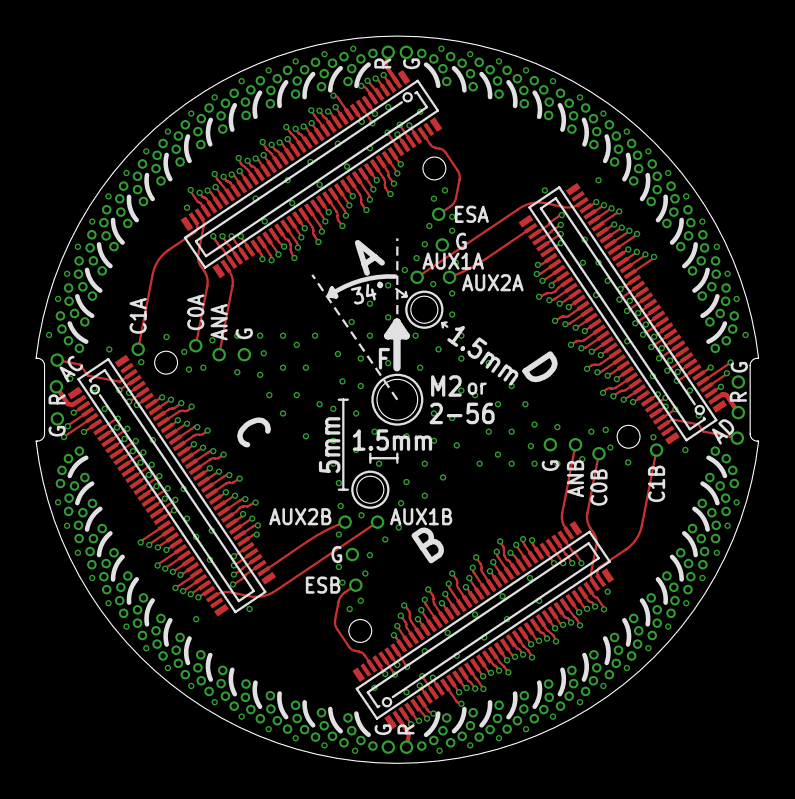
[picture p188: board eib-256.brd from above]

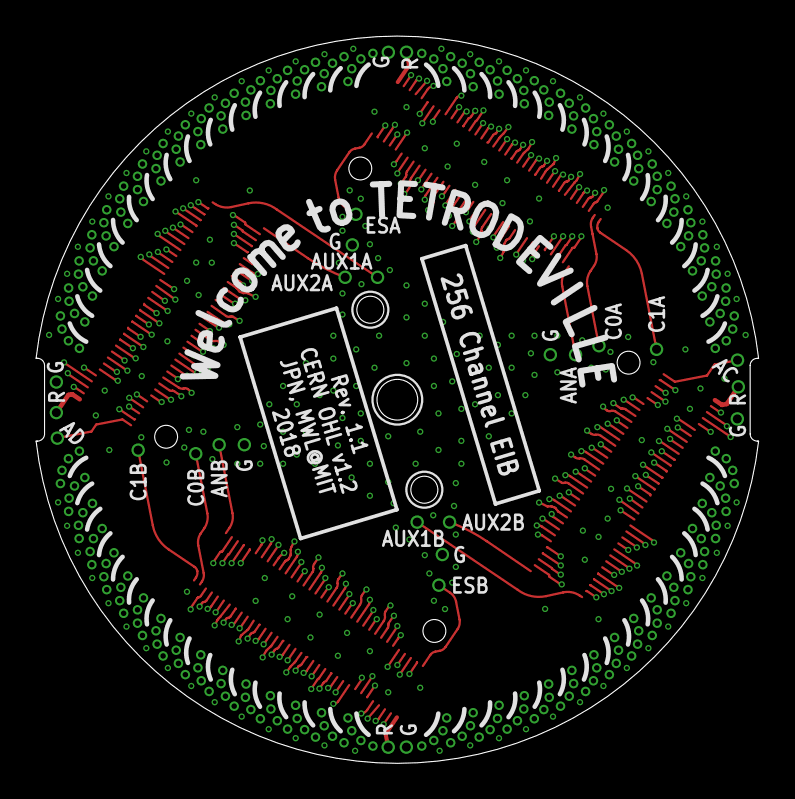
[picture p189: board eib-256.brd from below]

Board: 4 copper layers, 40.1 x 40.4 mm, 95 parts (32 on the bottom side), 275 nets.

Other parts of the board:
U$1: EIB_MOUNT_A
