jonnew/ONIX/nanoz-adapter-128-256/eib-128-256-nanoz-adapter.brd

## EAGLE design nanoz-adapter-128-256/eib-128-256-nanoz-adapter.brd (2018-05-18)

Schematic: eib-128-256-nanoz-adapter.sch

Parts:
A: DF40HEAD; DF40-70REC
B: DF40HEAD; DF40-70REC
C: DF40HEAD; DF40-70REC
C1, C2, C5, C6, C10, C12, C13, C15, C20, C22, C23, C25, C29, C30, C33, C34: 1uF; 0603
C3, C4, C7, C8, C9, C11, C14, C16, C19, C21, C24, C26, C27, C28, C31, C32: 0.1uF; 0402
C17, C18: 10uF; 1210-POL
D: DF40HEAD; DF40-70REC
D1, D2: MMSZ5240BS; SOD-323; PARTNO UDZ10B-7
D3, D4: LED_0603; LED-0603
J1, J2, J3, J4, J5: JP3E_SMD; JP3_SMD
J6: SCREW4
J7, J8: PINHD-4X10_MOLC-THRU; MOLC-110-11-S-Q
Q1: DMN3404L; SOT23-GSD; PARTNO DMN3404L-7
Q2: DMP3056L; SOT23-GSD; PARTNO DMP3056L-7
R1, R2, R5, R6: 1k; 0603
R3, R4: 10k; 0603
S1: 219-2MSTR; SMS-002
U1, U2, U3, U4, U5, U6, U7, U8, U9, U10, U11, U12, U13, U14, U15, U16, U17, U18, U19, U20, U21, U22, U23, U24, U25, U26, U27, U28, U29, U30, U31, U32: DG4052A; MQFN16-1.8X2.6

Connections:
A: J1.2, R3.1, U1.8 (A), U2.8 (A), U3.8 (A), U4.8 (A), U5.8 (A), U6.8 (A), U7.8 (A), U8.8 (A), U9.8 (A), U10.8 (A), U11.8 (A), U12.8 (A), U13.8 (A), U14.8 (A), U15.8 (A), U16.8 (A), U17.8 (A), U18.8 (A), U19.8 (A), U20.8 (A), U21.8 (A), U22.8 (A), U23.8 (A), U24.8 (A), U25.8 (A), U26.8 (A), U27.8 (A), U28.8 (A), U29.8 (A), U30.8 (A), U31.8 (A), U32.8 (A)
B: J2.2, R4.1, U1.7 (B), U2.7 (B), U3.7 (B), U4.7 (B), U5.7 (B), U6.7 (B), U7.7 (B), U8.7 (B), U9.7 (B), U10.7 (B), U11.7 (B), U12.7 (B), U13.7 (B), U14.7 (B), U15.7 (B), U16.7 (B), U17.7 (B), U18.7 (B), U19.7 (B), U20.7 (B), U21.7 (B), U22.7 (B), U23.7 (B), U24.7 (B), U25.7 (B), U26.7 (B), U27.7 (B), U28.7 (B), U29.7 (B), U30.7 (B), U31.7 (B), U32.7 (B)
GND: C1.2, C2.2, C3.2, C4.2, C5.2, C6.2, C7.2, C8.2, C9.2, C10.2, C11.2, C12.2, C13.2, C14.2, C15.2, C16.2, C17.-, C18.+, C19.2, C20.2, C21.2, C22.2, C23.2, C24.2, C25.2, C26.2, C27.2, C28.2, C29.2, C30.2, C31.2, C32.2, C33.2, C34.2, D3.C, D4.A, J3.1, J3.2, J6.3, R1.1, R2.2, S1.1, S1.2, U1.4 (EN), U1.6 (GND), U2.4 (EN), U2.6 (GND), U3.4 (EN), U3.6 (GND), U4.4 (EN), U4.6 (GND), U5.4 (EN), U5.6 (GND), U6.4 (EN), U6.6 (GND), U7.4 (EN), U7.6 (GND), U8.4 (EN), U8.6 (GND), U9.4 (EN), U9.6 (GND), U10.4 (EN), U10.6 (GND), U11.4 (EN), U11.6 (GND), U12.4 (EN), U12.6 (GND), U14.4 (EN), U14.6 (GND), U15.4 (EN), U15.6 (GND), U16.4 (EN), U16.6 (GND), U17.4 (EN), U17.6 (GND), U18.4 (EN), U18.6 (GND), U19.4 (EN), U19.6 (GND), U20.4 (EN), U20.6 (GND), U21.4 (EN), U21.6 (GND), U22.4 (EN), U22.6 (GND), U24.4 (EN), U24.6 (GND), U25.4 (EN), U25.6 (GND), U26.4 (EN), U26.6 (GND), U27.4 (EN), U27.6 (GND), U28.4 (EN), U28.6 (GND), U29.4 (EN), U29.6 (GND), U30.4 (EN), U30.6 (GND), U32.4 (EN), U32.6 (GND)
GND1: U13.6 (GND)
GND2: U23.6 (GND)
GND4: U31.6 (GND)
GND_HEAD: J3.3, J7.B4 (17)
GPIO0_HEAD: J1.1, J7.C3 (3)
GPIO1_HEAD: J2.1, J7.C4 (4)
GPIO2_HEAD: J8.C3 (3)
GPIO3_HEAD: J8.C4 (4)
unnamed: C.2, U1.9 (X3)
unnamed: C.3, U1.10 (X0)
unnamed: C.4, U1.12 (X1)
unnamed: C.5, U1.13 (X2)
unnamed: C.6, U1.15 (Y0)
unnamed: C.7, U1.16 (Y2)
unnamed: C.8, U1.2 (Y3)
unnamed: C.9, U1.3 (Y1)
unnamed: C.10, U2.9 (X3)
unnamed: C.11, U2.10 (X0)
unnamed: C.12, U2.12 (X1)
unnamed: C.13, U2.13 (X2)
unnamed: C.14, U2.15 (Y0)
unnamed: C.15, U2.16 (Y2)
unnamed: C.16, U2.2 (Y3)
unnamed: C.17, U2.3 (Y1)
unnamed: C.18, U3.9 (X3)
unnamed: C.19, U3.10 (X0)
unnamed: C.20, U3.12 (X1)
unnamed: C.21, U3.13 (X2)
unnamed: C.22, U3.15 (Y0)
unnamed: C.23, U3.16 (Y2)
unnamed: C.24, U3.2 (Y3)
unnamed: C.25, U3.3 (Y1)
unnamed: C.26, U4.9 (X3)
unnamed: C.27, U4.10 (X0)
unnamed: C.28, U4.12 (X1)
unnamed: C.29, U4.13 (X2)
unnamed: C.30, U4.15 (Y0)
unnamed: C.31, U4.16 (Y2)
unnamed: C.32, U4.2 (Y3)
unnamed: C.33, U4.3 (Y1)
unnamed: C.41, U8.13 (X2)
unnamed: C.42, U8.12 (X1)
unnamed: C.43, U8.10 (X0)
unnamed: C.44, U8.9 (X3)
unnamed: C.45, U7.3 (Y1)
unnamed: C.46, U7.2 (Y3)
unnamed: C.47, U7.16 (Y2)
unnamed: C.48, U7.15 (Y0)
unnamed: C.49, U7.13 (X2)
unnamed: C.37, U8.3 (Y1)
unnamed: C.38, U8.2 (Y3)
unnamed: C.39, U8.16 (Y2)
unnamed: C.40, U8.15 (Y0)
unnamed: C.50, U7.12 (X1)
unnamed: C.51, U7.10 (X0)
unnamed: C.52, U7.9 (X3)
unnamed: C.53, U6.3 (Y1)
unnamed: C.54, U6.2 (Y3)
unnamed: C.55, U6.16 (Y2)
unnamed: C.56, U6.15 (Y0)
unnamed: C.57, U6.13 (X2)
unnamed: C.58, U6.12 (X1)
unnamed: C.59, U6.10 (X0)
unnamed: C.60, U6.9 (X3)
unnamed: C.61, U5.3 (Y1)
unnamed: C.62, U5.2 (Y3)
unnamed: C.63, U5.16 (Y2)
unnamed: C.64, U5.15 (Y0)
unnamed: C.65, U5.13 (X2)
unnamed: C.66, U5.12 (X1)
unnamed: C.67, U5.10 (X0)
unnamed: C.68, U5.9 (X3)
unnamed: D3.A, R5.1
unnamed: D1.A, Q2.G, R1.2
unnamed: D4.C, R6.2
unnamed: D2.C, Q1.G, R2.1
unnamed: J1.3, S1.4
unnamed: J2.3, S1.3
REF: J6.4, J7.B1 (20), J7.C1 (1), J7.C2 (2), J8.B1 (20), J8.C1 (1), J8.C2 (2)
TT00: J8.A1 (1), U24.11 (X)
TT01: J8.A2 (2), U24.1 (Y)
TT02: J8.A3 (3), U23.11 (X)
TT03: J8.A4 (4), U23.1 (Y)
TT04: J8.A5 (5), U21.11 (X)
TT05: J8.B5 (16), U21.1 (Y)
TT06: J8.A6 (6), U19.11 (X)
TT07: J8.B6 (15), U19.1 (Y)
TT08: J8.A10 (10), U11.11 (X)
TT09: J8.B10 (11), U11.1 (Y)
TT10: J8.A9 (9), U13.11 (X)
TT11: J8.B9 (12), U13.1 (Y)
TT12: J8.A8 (8), U15.11 (X)
TT13: J8.B8 (13), U15.1 (Y)
TT14: J8.A7 (7), U17.11 (X)
TT15: J8.B7 (14), U17.1 (Y)
TT16: J8.C10 (10), U1.11 (X)
TT17: J8.D10 (11), U1.1 (Y)
TT18: J8.C9 (9), U2.11 (X)
TT19: J8.D9 (12), U2.1 (Y)
TT20: J8.C8 (8), U3.11 (X)
TT21: J8.D8 (13), U3.1 (Y)
TT22: J8.C7 (7), U4.11 (X)
TT23: J8.D7 (14), U4.1 (Y)
TT24: J8.D2 (19), U8.11 (X)
TT25: J8.D1 (20), U8.1 (Y)
TT26: J8.D4 (17), U7.11 (X)
TT27: J8.D3 (18), U7.1 (Y)
TT28: J8.C5 (5), U6.11 (X)
TT29: J8.D5 (16), U6.1 (Y)
TT30: J8.C6 (6), U5.11 (X)
TT31: J8.D6 (15), U5.1 (Y)
TT32: J7.C10 (10), U9.11 (X)
TT33: J7.D10 (11), U9.1 (Y)
TT34: J7.C9 (9), U10.11 (X)
TT35: J7.D9 (12), U10.1 (Y)
TT36: J7.C8 (8), U12.11 (X)
TT37: J7.D8 (13), U12.1 (Y)
TT38: J7.C7 (7), U14.11 (X)
TT39: J7.D7 (14), U14.1 (Y)
TT40: J7.D2 (19), U22.11 (X)
TT41: J7.D1 (20), U22.1 (Y)
TT42: J7.D4 (17), U20.11 (X)
TT43: J7.D3 (18), U20.1 (Y)
TT44: J7.C5 (5), U18.11 (X)
TT45: J7.D5 (16), U18.1 (Y)
TT46: J7.C6 (6), U16.11 (X)
TT47: J7.D6 (15), U16.1 (Y)
TT48: J7.A1 (1), U32.11 (X)
TT49: J7.A2 (2), U32.1 (Y)
TT50: J7.A3 (3), U31.11 (X)
TT51: J7.A4 (4), U31.1 (Y)
TT52: J7.A5 (5), U30.11 (X)
TT53: J7.B5 (16), U30.1 (Y)
TT54: J7.A6 (6), U29.11 (X)
TT55: J7.B6 (15), U29.1 (Y)
TT56: J7.A10 (10), U25.11 (X)
TT57: J7.B10 (11), U25.1 (Y)
TT58: J7.A9 (9), U26.11 (X)
TT59: J7.B9 (12), U26.1 (Y)
TT60: J7.A8 (8), U27.11 (X)
TT61: J7.B8 (13), U27.1 (Y)
TT62: J7.A7 (7), U28.11 (X)
TT63: J7.B7 (14), U28.1 (Y)
VCC: C1.1, C2.1, C3.1, C4.1, C9.1, C10.1, C15.1, C16.1, C17.+, C19.1, C20.1, C25.1, C26.1, C31.1, C32.1, C33.1, C34.1, D1.C, Q2.S, R3.2, R4.2, R5.2, U1.14 (V+), U2.14 (V+), U3.14 (V+), U4.14 (V+), U5.14 (V+), U6.14 (V+), U7.14 (V+), U8.14 (V+), U9.14 (V+), U10.14 (V+), U11.14 (V+), U12.14 (V+), U13.14 (V+), U14.14 (V+), U15.14 (V+), U16.14 (V+), U17.14 (V+), U18.14 (V+), U19.14 (V+), U20.14 (V+), U21.14 (V+), U22.14 (V+), U23.14 (V+), U24.14 (V+), U25.14 (V+), U26.14 (V+), U27.14 (V+), U28.14 (V+), U29.14 (V+), U30.14 (V+), U31.14 (V+), U32.14 (V+)
VCC_HEAD: J5.3, J7.B2 (19)
VCC_LOCAL: J5.1, J6.1
VCC_PRE: J5.2, Q2.D
VSS: C5.1, C6.1, C7.1, C8.1, C11.1, C12.1, C13.1, C14.1, C18.-, C21.1, C22.1, C23.1, C24.1, C27.1, C28.1, C29.1, C30.1, D2.A, Q1.S, R6.1, U1.5 (V-), U2.5 (V-), U3.5 (V-), U4.5 (V-), U5.5 (V-), U6.5 (V-), U7.5 (V-), U8.5 (V-), U9.5 (V-), U10.5 (V-), U11.5 (V-), U12.5 (V-), U13.5 (V-), U14.5 (V-), U15.5 (V-), U16.5 (V-), U17.5 (V-), U18.5 (V-), U19.5 (V-), U20.5 (V-), U21.5 (V-), U22.5 (V-), U23.5 (V-), U24.5 (V-), U25.5 (V-), U26.5 (V-), U27.5 (V-), U28.5 (V-), U29.5 (V-), U30.5 (V-), U31.5 (V-), U32.5 (V-)
VSS_HEAD: J4.3, J7.B3 (18)
VSS_LOCAL: J4.1, J6.2
VSS_PRE: J4.2, Q1.D

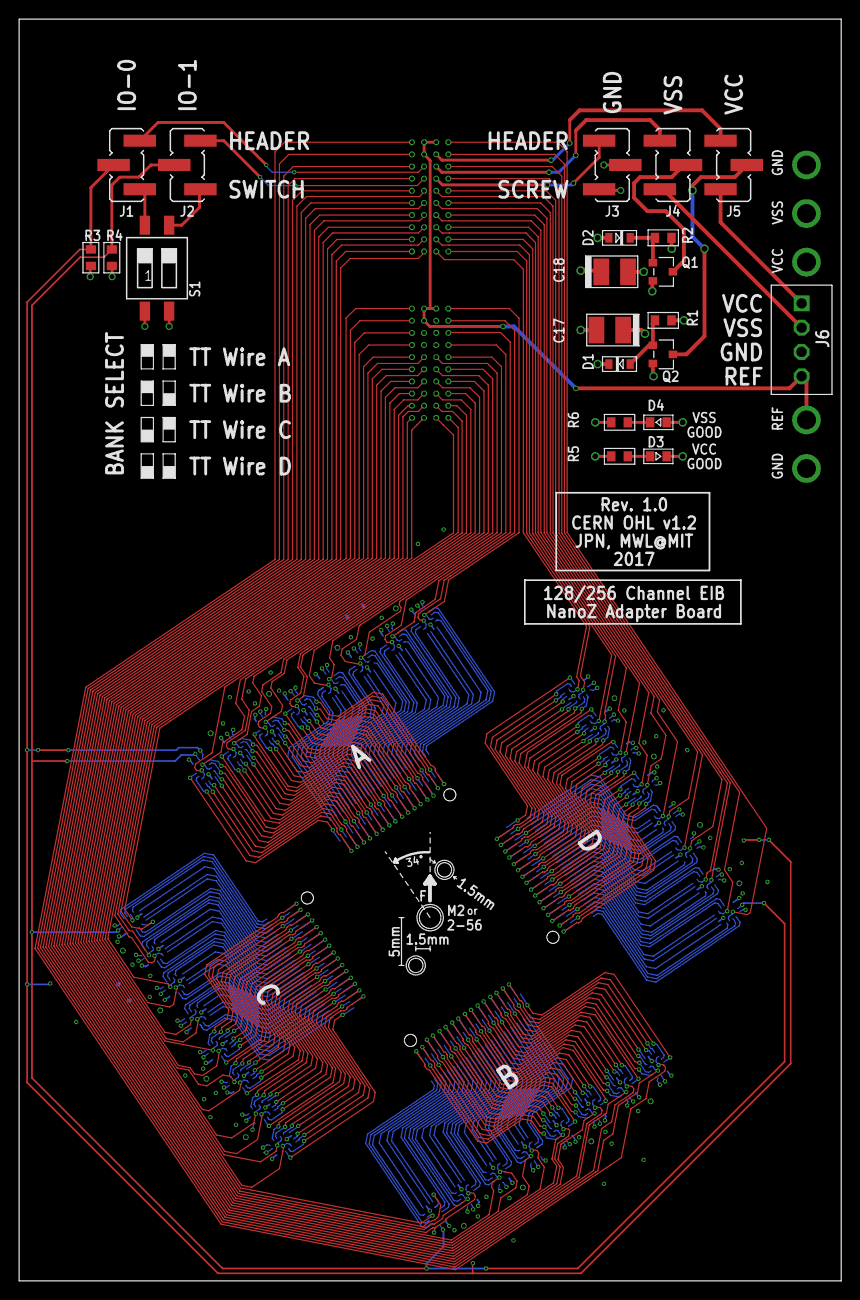
[picture p190: board eib-128-256-nanoz-adapter.brd from above]

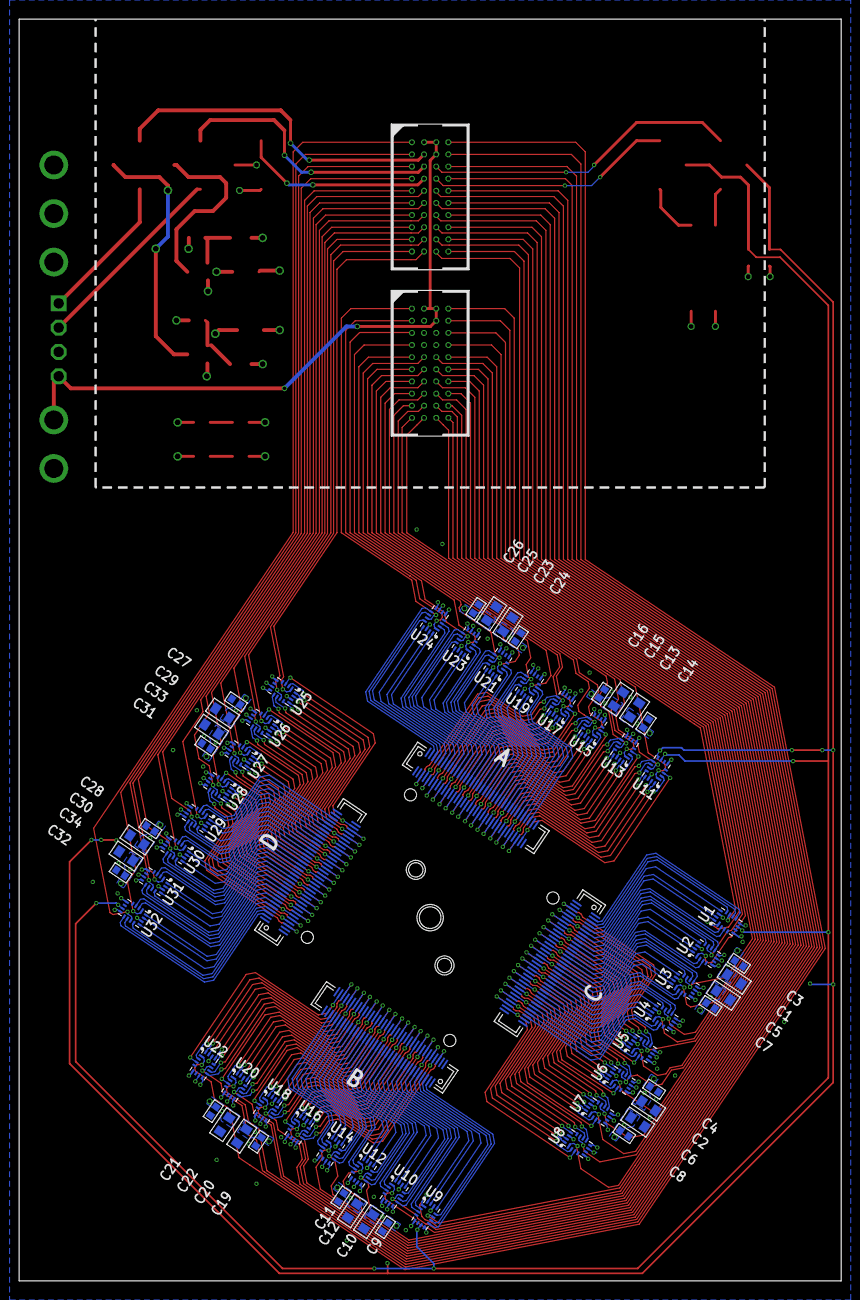
[picture p191: board eib-128-256-nanoz-adapter.brd from below]

Board: 4 copper layers, 86.0 x 132.0 mm, 92 parts (70 on the bottom side), 149 nets.

Other parts of the board:
U$1: EIB_MOUNT_A
