jonnew/ONIX/test-board-128-256/test-board-128-256.brd

## EAGLE design test-board-128-256/test-board-128-256.brd (2018-04-15)

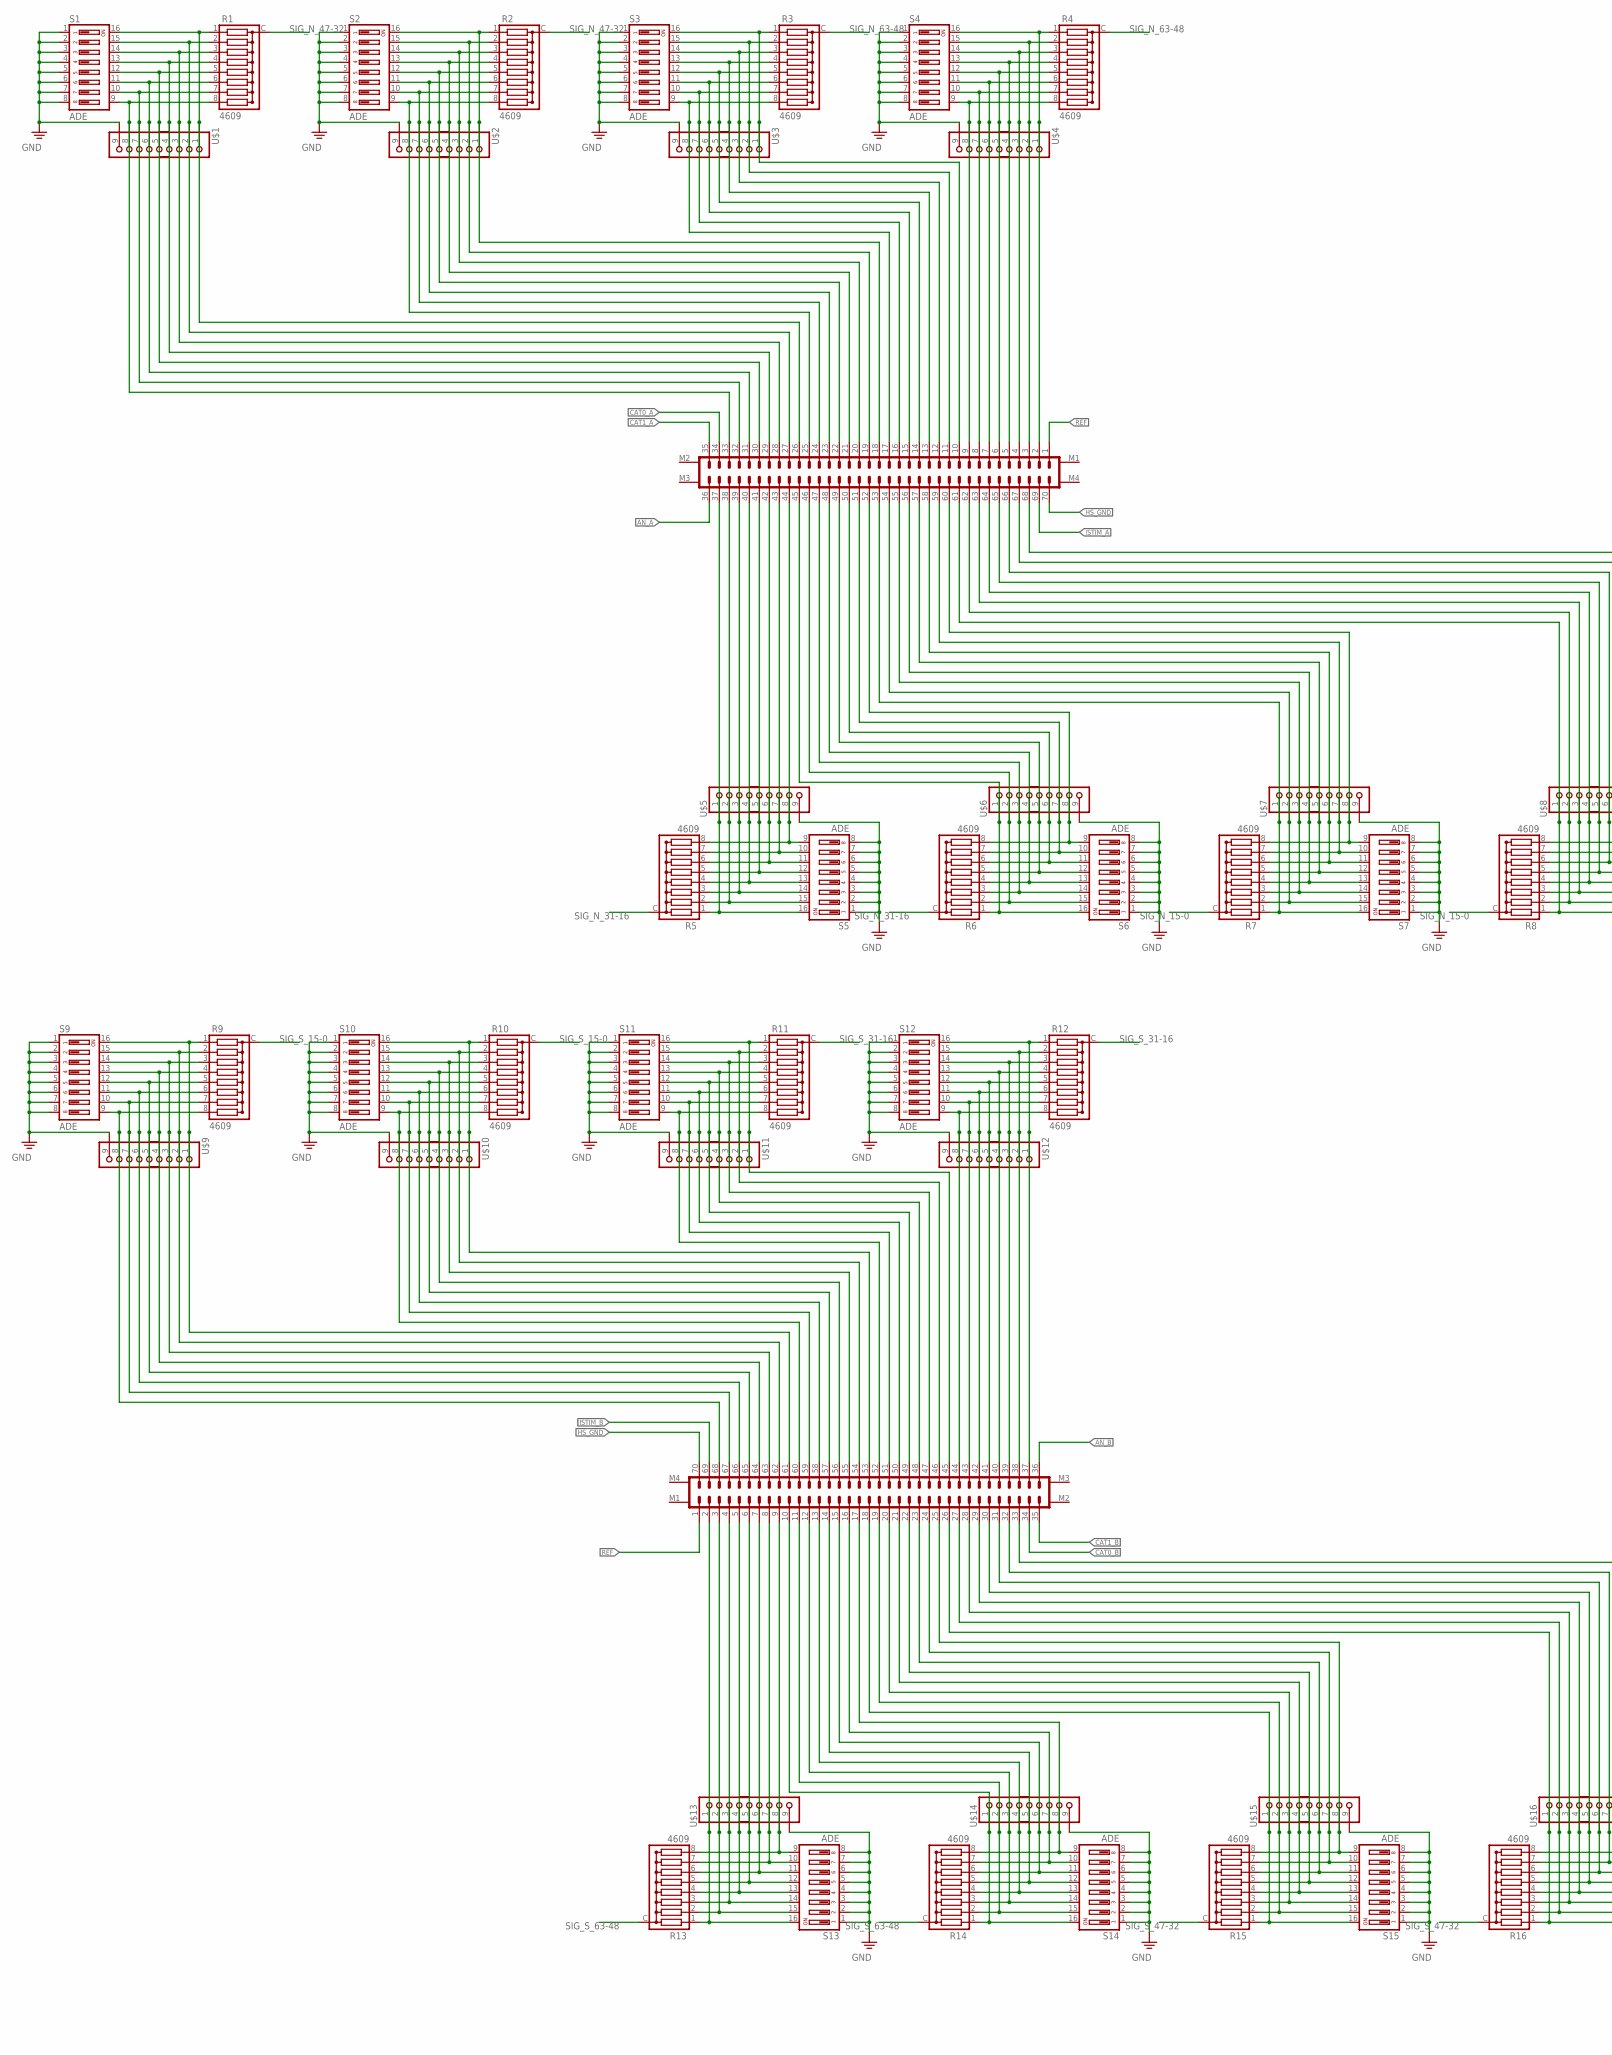
[picture p192: schematic test-board-128-256.sch, part in row 1, column 1]

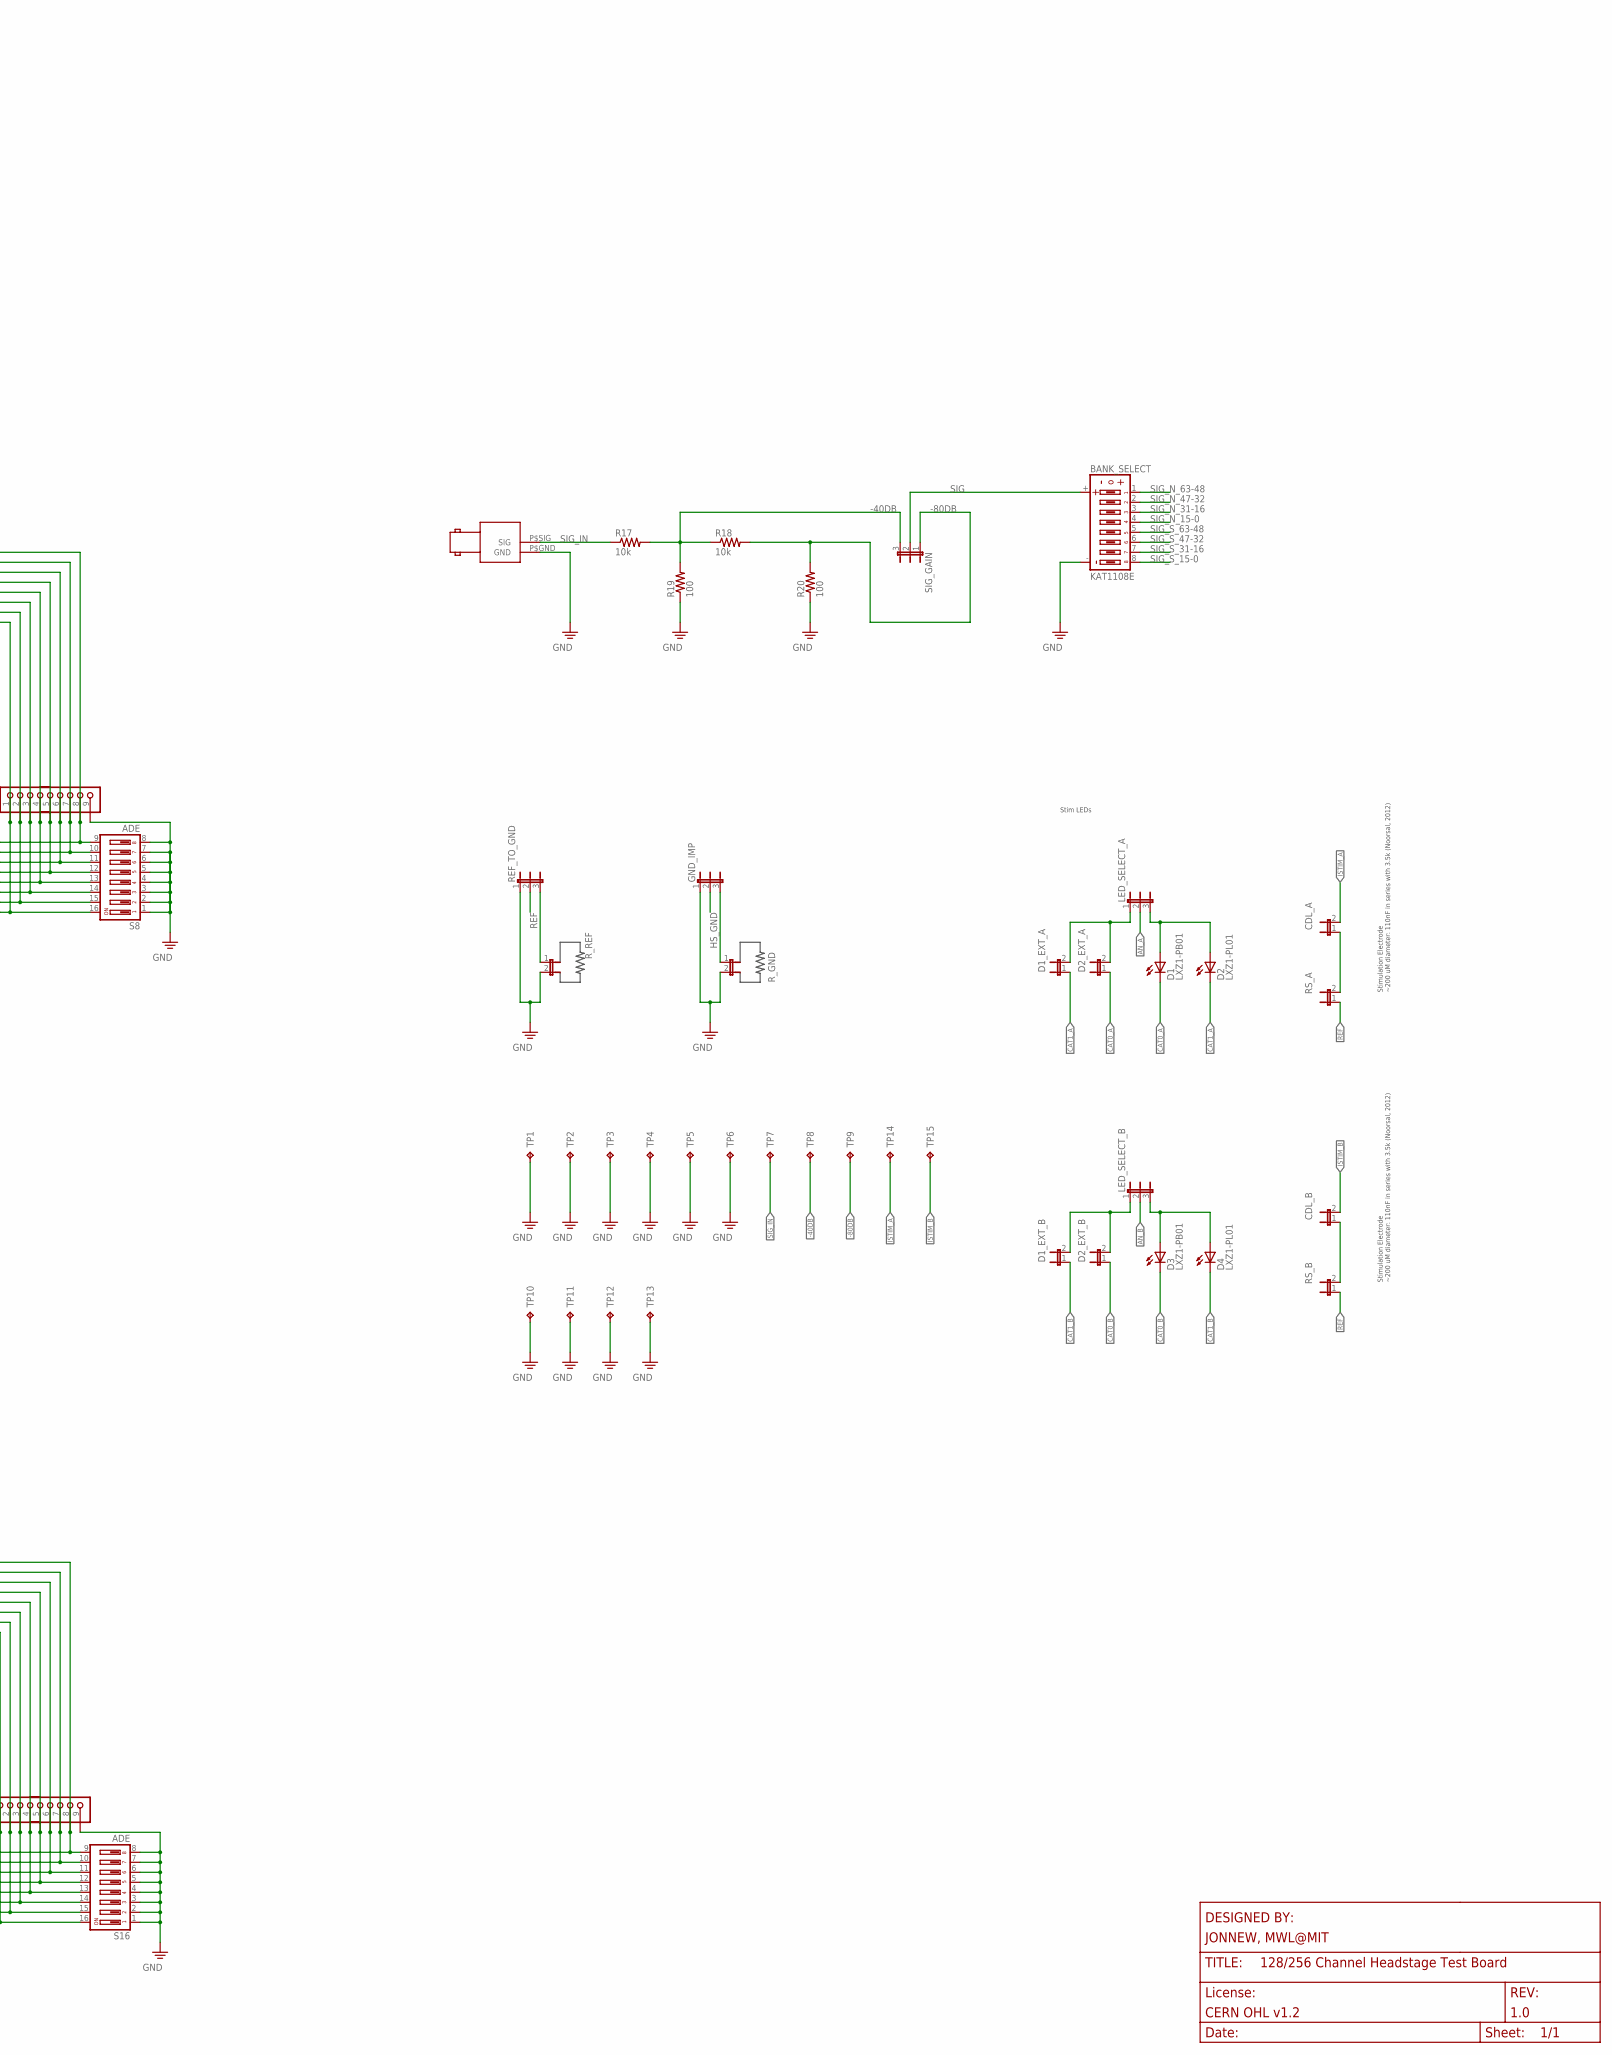
[picture p193: schematic test-board-128-256.sch, part in row 1, column 2]

Parts:
A-OR-D: DF40HEAD; DF40-70HEAD
B-OR-C: DF40HEAD; DF40-70HEAD
BANK_SELECT: KAT1108E; 206-124_DIP8-SPDT
CDL_A: JP2E_THRU-HOLE; JP2
CDL_B: JP2E_THRU-HOLE; JP2
D1, D3: LXZ1-PB01; LXZ1
D1_EXT_A, D1_EXT_B, D2_EXT_A, D2_EXT_B: JP2E_THRU-HOLE; JP2
D2, D4: LXZ1-PL01; LXZ1
GND_IMP: JP3E; JP3
LED_SELECT_A: JP3E; JP3
LED_SELECT_B: JP3E; JP3
R1, R2, R3, R4, R5, R6, R7, R8, R9, R10, R11, R12, R13, R14, R15, R16: 4609; RNX8-0.1
R17, R18: 10k; 0805
R19, R20: 100; 0805
REF_TO_GND: JP3E; JP3
RS_A: JP2E_THRU-HOLE; JP2
RS_B: JP2E_THRU-HOLE; JP2
R_GND: JP2E_THRU-HOLE; JP2
R_REF: JP2E_THRU-HOLE; JP2
S1, S2, S3, S4, S5, S6, S7, S8, S9, S10, S11, S12, S13, S14, S15, S16: ADE; ADE_DIP8-SPST
SIG_GAIN: JP3E; JP3
SIG_IN: 1-1634622-0; BNC_RIGHT_ANGLE
TP1, TP2, TP3, TP4, TP5, TP6: GND; P1-20
TP7: SIG_IN; P1-20
TP8: -40dB; P1-20
TP9: -80dB; P1-20
TP10, TP11, TP12, TP13: TP_4-40; 4-40_PLATED
TP14: V_ISTIM_A; P1-20
TP15: V_ISTIM_B; P1-20
U$1, U$2, U$3, U$4, U$5, U$6, U$7, U$8, U$9, U$10, U$11, U$12, U$13, U$14, U$15, U$16: PINHD-1X9; 1X09

Connections:
-40DB: R17.2, R18.1, R19.2, SIG_GAIN.3, TP8.TP
-80DB: R18.2, R20.2, SIG_GAIN.1, TP9.TP
AN_A: A-OR-D.36, LED_SELECT_A.2
AN_B: B-OR-C.36, LED_SELECT_B.2
AN_INT: D1.A, D2.A, LED_SELECT_A.3
AN_INT1: D3.A, D4.A, LED_SELECT_B.3
CAT0_A: A-OR-D.34, D1.C, D2_EXT_A.1
CAT0_B: B-OR-C.34, D2_EXT_B.1, D3.C
CAT1_A: A-OR-D.35, D1_EXT_A.1, D2.C
CAT1_B: B-OR-C.35, D1_EXT_B.1, D4.C
GND: BANK_SELECT.-, GND_IMP.1, R19.1, R20.1, REF_TO_GND.1, R_GND.2, R_REF.2, S1.1, S1.2, S1.3, S1.4, S1.5, S1.6, S1.7, S1.8, S2.1, S2.2, S2.3, S2.4, S2.5, S2.6, S2.7, S2.8, S3.1, S3.2, S3.3, S3.4, S3.5, S3.6, S3.7, S3.8, S4.1, S4.2, S4.3, S4.4, S4.5, S4.6, S4.7, S4.8, S5.1, S5.2, S5.3, S5.4, S5.5, S5.6, S5.7, S5.8, S6.1, S6.2, S6.3, S6.4, S6.5, S6.6, S6.7, S6.8, S7.1, S7.2, S7.3, S7.4, S7.5, S7.6, S7.7, S7.8, S8.1, S8.2, S8.3, S8.4, S8.5, S8.6, S8.7, S8.8, S9.1, S9.2, S9.3, S9.4, S9.5, S9.6, S9.7, S9.8, S10.1, S10.2, S10.3, S10.4, S10.5, S10.6, S10.7, S10.8, S11.1, S11.2, S11.3, S11.4, S11.5, S11.6, S11.7, S11.8, S12.1, S12.2, S12.3, S12.4, S12.5, S12.6, S12.7, S12.8, S13.1, S13.2, S13.3, S13.4, S13.5, S13.6, S13.7, S13.8, S14.1, S14.2, S14.3, S14.4, S14.5, S14.6, S14.7, S14.8, S15.1, S15.2, S15.3, S15.4, S15.5, S15.6, S15.7, S15.8, S16.1, S16.2, S16.3, S16.4, S16.5, S16.6, S16.7, S16.8, SIG_IN.P$GND (GND), TP1.TP, TP2.TP, TP3.TP, TP4.TP, TP5.TP, TP6.TP, TP10.P$1, TP11.P$1, TP12.P$1, TP13.P$1, U$1.9, U$2.9, U$3.9, U$4.9, U$5.9, U$6.9, U$7.9, U$8.9, U$9.9, U$10.9, U$11.9, U$12.9, U$13.9, U$14.9, U$15.9, U$16.9
HS_GND: A-OR-D.70, B-OR-C.70, GND_IMP.2
ISTIM_A: A-OR-D.69, CDL_A.2, TP14.TP
ISTIM_B: B-OR-C.69, CDL_B.2, TP15.TP
unnamed: CDL_A.1, RS_A.2
unnamed: GND_IMP.3, R_GND.1
unnamed: B-OR-C.3, R13.2, S13.15, U$13.2
unnamed: B-OR-C.5, R13.4, S13.13, U$13.4
unnamed: D1_EXT_A.2, D2_EXT_A.2, LED_SELECT_A.1
unnamed: A-OR-D.17, R3.8, S3.9, U$3.8
unnamed: A-OR-D.9, R4.8, S4.9, U$4.8
unnamed: A-OR-D.15, R3.6, S3.11, U$3.6
unnamed: A-OR-D.14, R3.5, S3.12, U$3.5
unnamed: A-OR-D.3, R4.2, S4.15, U$4.2
unnamed: A-OR-D.12, R3.3, S3.14, U$3.3
unnamed: A-OR-D.4, R4.3, S4.14, U$4.3
unnamed: A-OR-D.10, R3.1, S3.16, U$3.1
unnamed: CDL_B.1, RS_B.2
unnamed: D1_EXT_B.2, D2_EXT_B.2, LED_SELECT_B.1
unnamed: A-OR-D.7, R4.6, S4.11, U$4.6
unnamed: A-OR-D.8, R4.7, S4.10, U$4.7
unnamed: A-OR-D.6, R4.5, S4.12, U$4.5
unnamed: A-OR-D.2, R4.1, S4.16, U$4.1
unnamed: A-OR-D.27, R1.2, S1.15, U$1.2
unnamed: A-OR-D.29, R1.4, S1.13, U$1.4
unnamed: A-OR-D.43, R5.7, S5.10, U$5.7
unnamed: B-OR-C.7, R13.6, S13.11, U$13.6
unnamed: A-OR-D.32, R1.7, S1.10, U$1.7
unnamed: REF_TO_GND.3, R_REF.1
unnamed: A-OR-D.30, R1.5, S1.12, U$1.5
unnamed: A-OR-D.41, R5.5, S5.12, U$5.5
unnamed: A-OR-D.28, R1.3, S1.14, U$1.3
unnamed: B-OR-C.9, R13.8, S13.9, U$13.8
unnamed: A-OR-D.39, R5.3, S5.14, U$5.3
unnamed: A-OR-D.31, R1.6, S1.11, U$1.6
unnamed: B-OR-C.10, R14.1, S14.16, U$14.1
unnamed: A-OR-D.33, R1.8, S1.9, U$1.8
unnamed: A-OR-D.37, R5.1, S5.16, U$5.1
unnamed: A-OR-D.19, R2.2, S2.15, U$2.2
unnamed: A-OR-D.52, R6.8, S6.9, U$6.8
unnamed: A-OR-D.21, R2.4, S2.13, U$2.4
unnamed: B-OR-C.11, R14.2, S14.15, U$14.2
unnamed: A-OR-D.23, R2.6, S2.11, U$2.6
unnamed: A-OR-D.24, R2.7, S2.10, U$2.7
unnamed: B-OR-C.14, R14.5, S14.12, U$14.5
unnamed: B-OR-C.15, R14.6, S14.11, U$14.6
unnamed: A-OR-D.47, R6.3, S6.14, U$6.3
unnamed: B-OR-C.16, R14.7, S14.10, U$14.7
unnamed: B-OR-C.19, R15.2, S15.15, U$15.2
unnamed: B-OR-C.20, R15.3, S15.14, U$15.3
unnamed: B-OR-C.21, R15.4, S15.13, U$15.4
unnamed: B-OR-C.22, R15.5, S15.12, U$15.5
unnamed: B-OR-C.23, R15.6, S15.11, U$15.6
unnamed: B-OR-C.24, R15.7, S15.10, U$15.7
unnamed: B-OR-C.25, R15.8, S15.9, U$15.8
unnamed: B-OR-C.26, R16.1, S16.16, U$16.1
unnamed: A-OR-D.53, R7.1, S7.16, U$7.1
unnamed: B-OR-C.27, R16.2, S16.15, U$16.2
unnamed: B-OR-C.28, R16.3, S16.14, U$16.3
unnamed: B-OR-C.29, R16.4, S16.13, U$16.4
unnamed: B-OR-C.30, R16.5, S16.12, U$16.5
unnamed: B-OR-C.31, R16.6, S16.11, U$16.6
unnamed: B-OR-C.32, R16.7, S16.10, U$16.7
unnamed: B-OR-C.33, R16.8, S16.9, U$16.8
unnamed: B-OR-C.8, R13.7, S13.10, U$13.7
unnamed: B-OR-C.6, R13.5, S13.12, U$13.5
unnamed: B-OR-C.4, R13.3, S13.14, U$13.3
unnamed: B-OR-C.2, R13.1, S13.16, U$13.1
unnamed: B-OR-C.17, R14.8, S14.9, U$14.8
unnamed: B-OR-C.12, R14.3, S14.14, U$14.3
unnamed: B-OR-C.18, R15.1, S15.16, U$15.1
unnamed: B-OR-C.61, R9.1, S9.16, U$9.1
unnamed: B-OR-C.60, R10.8, S10.9, U$10.8
unnamed: B-OR-C.57, R10.5, S10.12, U$10.5
unnamed: B-OR-C.55, R10.3, S10.14, U$10.3
unnamed: B-OR-C.53, R10.1, S10.16, U$10.1
unnamed: B-OR-C.51, R11.7, S11.10, U$11.7
unnamed: B-OR-C.48, R11.4, S11.13, U$11.4
unnamed: B-OR-C.46, R11.2, S11.15, U$11.2
unnamed: B-OR-C.40, R12.4, S12.13, U$12.4
unnamed: B-OR-C.52, R11.8, S11.9, U$11.8
unnamed: B-OR-C.50, R11.6, S11.11, U$11.6
unnamed: B-OR-C.49, R11.5, S11.12, U$11.5
unnamed: B-OR-C.47, R11.3, S11.14, U$11.3
unnamed: B-OR-C.45, R11.1, S11.16, U$11.1
unnamed: B-OR-C.67, R9.7, S9.10, U$9.7
unnamed: B-OR-C.65, R9.5, S9.12, U$9.5
unnamed: B-OR-C.63, R9.3, S9.14, U$9.3
unnamed: B-OR-C.44, R12.8, S12.9, U$12.8
unnamed: B-OR-C.38, R12.2, S12.15, U$12.2
unnamed: B-OR-C.39, R12.3, S12.14, U$12.3
unnamed: B-OR-C.42, R12.6, S12.11, U$12.6
unnamed: B-OR-C.43, R12.7, S12.10, U$12.7
unnamed: B-OR-C.41, R12.5, S12.12, U$12.5
unnamed: B-OR-C.37, R12.1, S12.16, U$12.1
unnamed: B-OR-C.64, R9.4, S9.13, U$9.4
unnamed: B-OR-C.66, R9.6, S9.11, U$9.6
unnamed: B-OR-C.68, R9.8, S9.9, U$9.8
unnamed: B-OR-C.54, R10.2, S10.15, U$10.2
unnamed: B-OR-C.56, R10.4, S10.13, U$10.4
unnamed: B-OR-C.58, R10.6, S10.11, U$10.6
unnamed: B-OR-C.59, R10.7, S10.10, U$10.7
unnamed: B-OR-C.13, R14.4, S14.13, U$14.4
unnamed: B-OR-C.62, R9.2, S9.15, U$9.2
unnamed: A-OR-D.26, R1.1, S1.16, U$1.1
unnamed: A-OR-D.25, R2.8, S2.9, U$2.8
unnamed: A-OR-D.22, R2.5, S2.12, U$2.5
unnamed: A-OR-D.20, R2.3, S2.14, U$2.3
unnamed: A-OR-D.18, R2.1, S2.16, U$2.1
unnamed: A-OR-D.16, R3.7, S3.10, U$3.7
unnamed: A-OR-D.13, R3.4, S3.13, U$3.4
unnamed: A-OR-D.11, R3.2, S3.15, U$3.2
unnamed: A-OR-D.5, R4.4, S4.13, U$4.4
unnamed: A-OR-D.38, R5.2, S5.15, U$5.2
unnamed: A-OR-D.40, R5.4, S5.13, U$5.4
unnamed: A-OR-D.42, R5.6, S5.11, U$5.6
unnamed: A-OR-D.44, R5.8, S5.9, U$5.8
unnamed: A-OR-D.45, R6.1, S6.16, U$6.1
unnamed: A-OR-D.46, R6.2, S6.15, U$6.2
unnamed: A-OR-D.48, R6.4, S6.13, U$6.4
unnamed: A-OR-D.49, R6.5, S6.12, U$6.5
unnamed: A-OR-D.50, R6.6, S6.11, U$6.6
unnamed: A-OR-D.51, R6.7, S6.10, U$6.7
unnamed: A-OR-D.54, R7.2, S7.15, U$7.2
unnamed: A-OR-D.55, R7.3, S7.14, U$7.3
unnamed: A-OR-D.56, R7.4, S7.13, U$7.4
unnamed: A-OR-D.57, R7.5, S7.12, U$7.5
unnamed: A-OR-D.58, R7.6, S7.11, U$7.6
unnamed: A-OR-D.59, R7.7, S7.10, U$7.7
unnamed: A-OR-D.60, R7.8, S7.9, U$7.8
unnamed: A-OR-D.61, R8.1, S8.16, U$8.1
unnamed: A-OR-D.62, R8.2, S8.15, U$8.2
unnamed: A-OR-D.63, R8.3, S8.14, U$8.3
unnamed: A-OR-D.64, R8.4, S8.13, U$8.4
unnamed: A-OR-D.65, R8.5, S8.12, U$8.5
unnamed: A-OR-D.66, R8.6, S8.11, U$8.6
unnamed: A-OR-D.67, R8.7, S8.10, U$8.7
unnamed: A-OR-D.68, R8.8, S8.9, U$8.8
REF: A-OR-D.1, B-OR-C.1, REF_TO_GND.2, RS_A.1, RS_B.1
SIG: BANK_SELECT.+, SIG_GAIN.2
SIG_IN: R17.1, SIG_IN.P$SIG (SIG), TP7.TP
SIG_N_15-0: BANK_SELECT.4, R7.C, R8.C
SIG_N_31-16: BANK_SELECT.3, R5.C, R6.C
SIG_N_47-32: BANK_SELECT.2, R1.C, R2.C
SIG_N_63-48: BANK_SELECT.1, R3.C, R4.C
SIG_S_15-0: BANK_SELECT.8, R9.C, R10.C
SIG_S_31-16: BANK_SELECT.7, R11.C, R12.C
SIG_S_47-32: BANK_SELECT.6, R15.C, R16.C
SIG_S_63-48: BANK_SELECT.5, R13.C, R14.C

Notes on the sheet:
Stimulation Electrode ~200 uM diameter: 110nF in series with 3.5k (Noorsal, 2012)
Stim LEDs

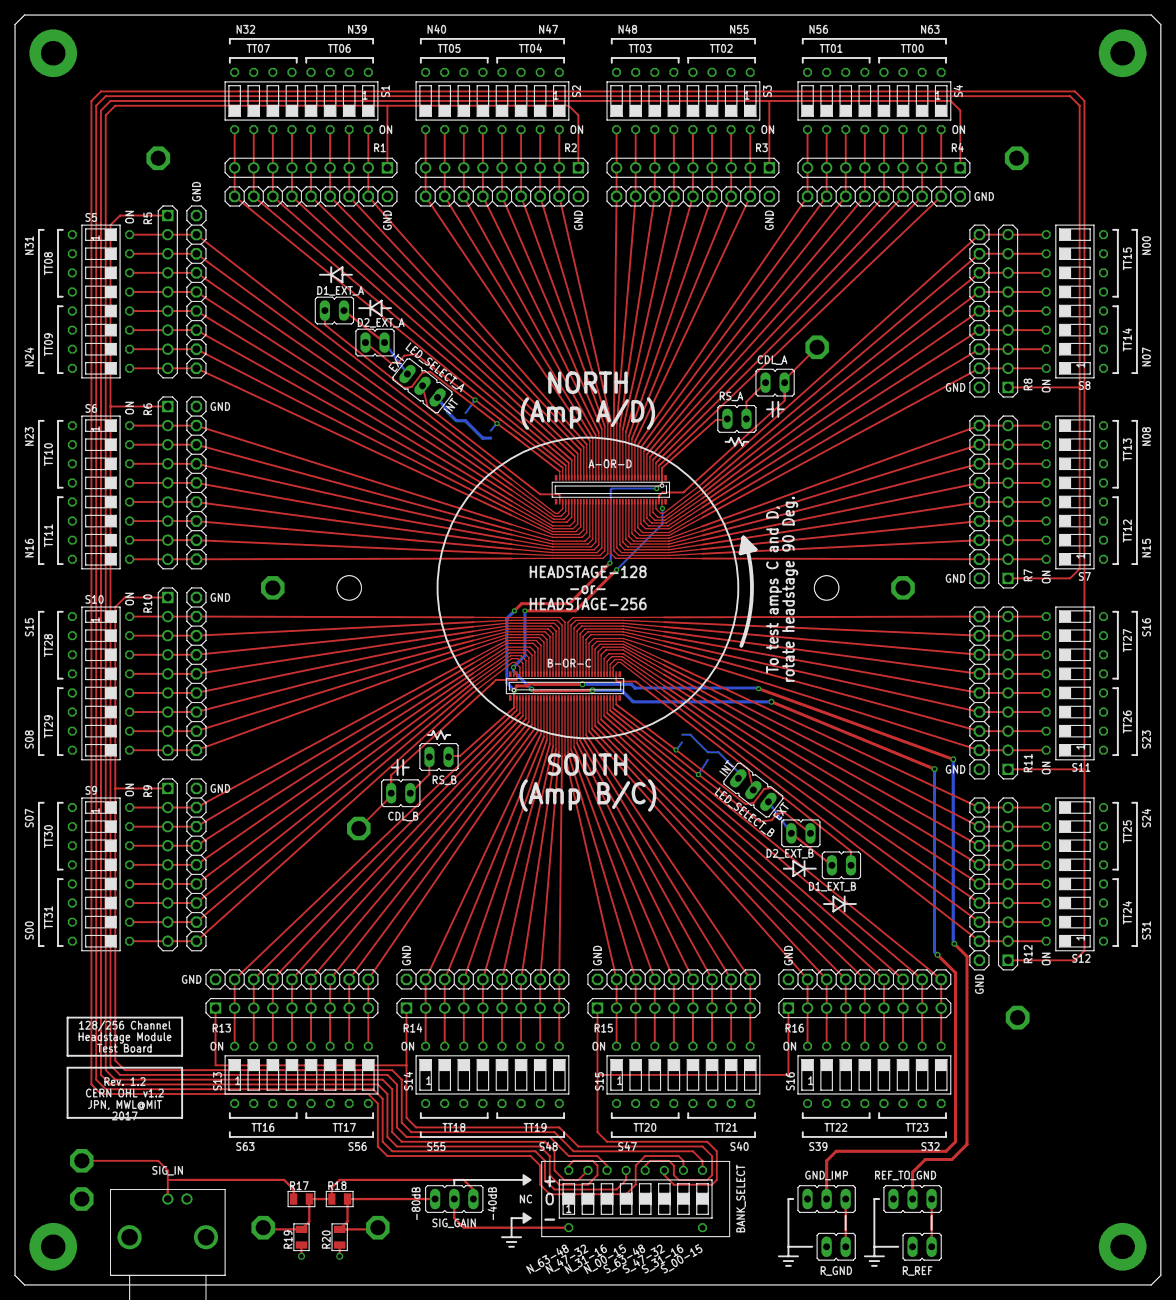
[picture p194: board test-board-128-256.brd from above]

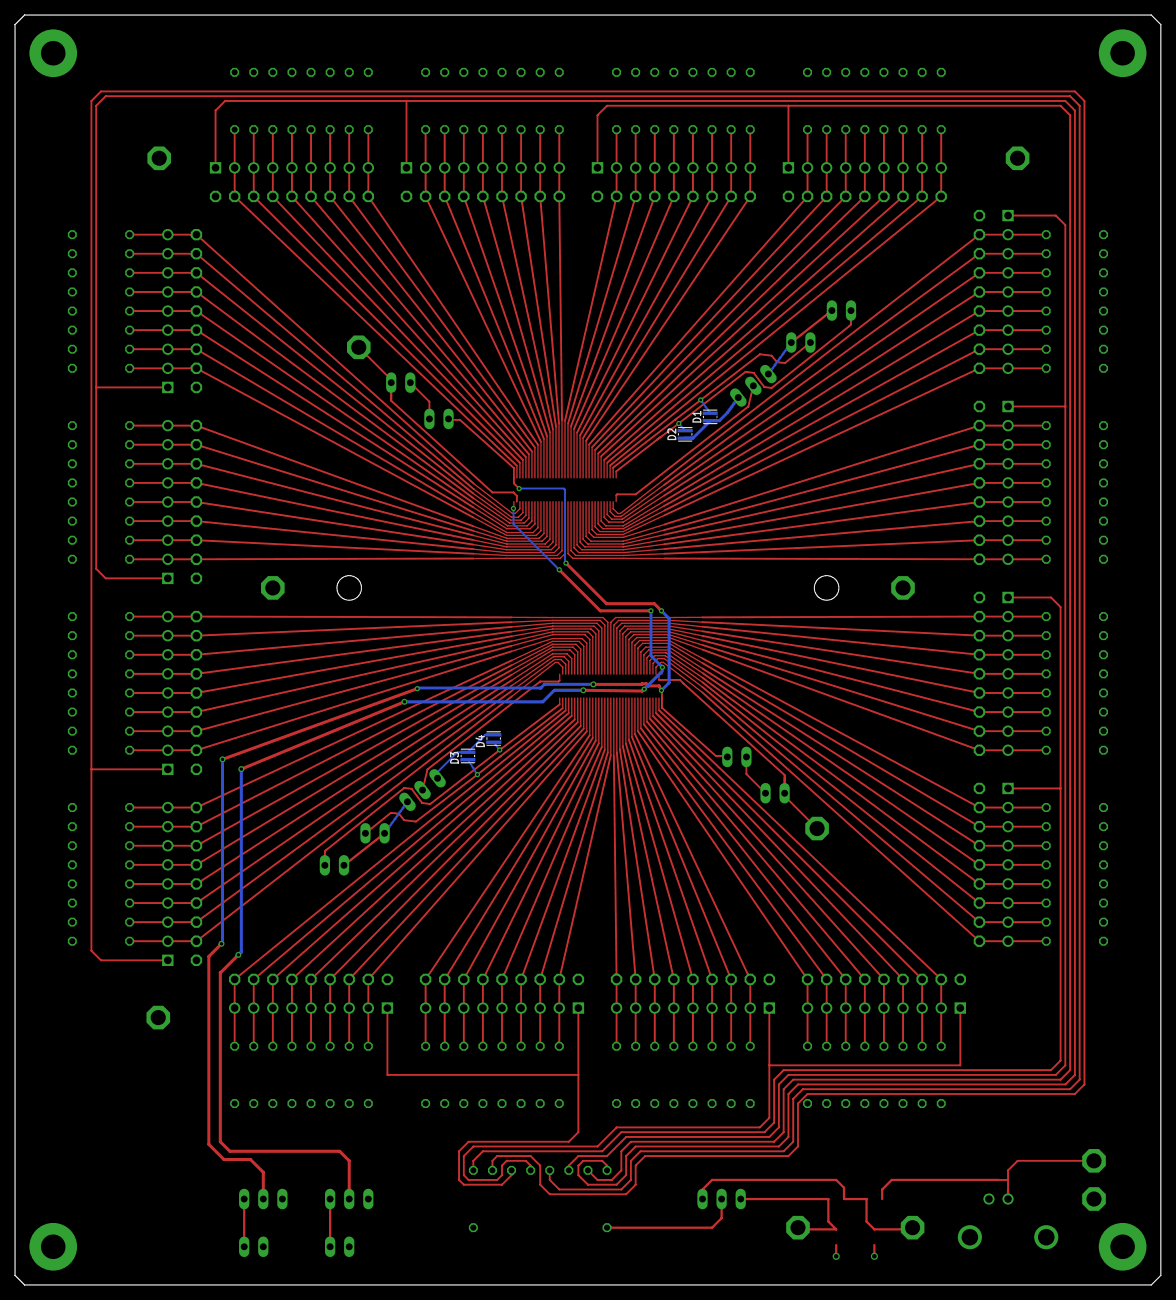
[picture p195: board test-board-128-256.brd from below]

Board: 2 copper layers, 152.4 x 168.9 mm, 90 parts (4 on the bottom side), 159 nets.
