jonnew/ONIX/led-flex-board/led-flex-board.brd

## EAGLE design led-flex-board/led-flex-board.brd (2017-12-16)

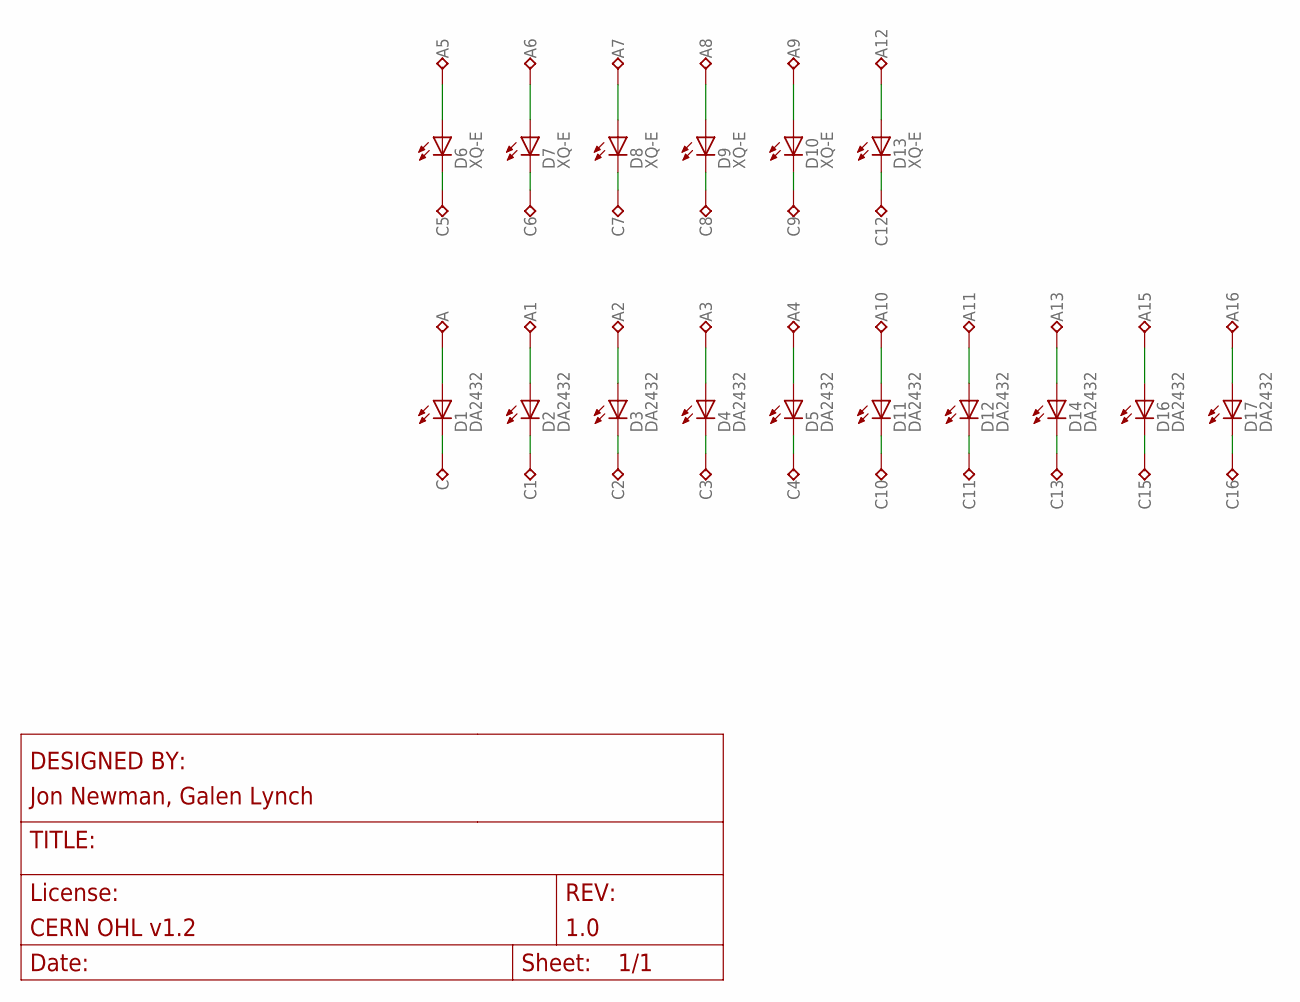
[picture p196: schematic led-flex-board.sch]

Parts:
A, A1, A2, A3, A4, A5, A6, A7, A8, A9, A10, A11, A12, A13, A15, A16: TP_S0.6X1.5MM; S0.6X1.5MM
C, C1, C2, C3, C4, C5, C6, C7, C8, C9, C10, C11, C12, C13, C15, C16: TP_S0.6X1.5MM; S0.6X1.5MM
D1, D2, D3, D4, D5, D11, D12, D14, D16, D17: DA2432
D6, D7, D8, D9, D10, D13: XQ-E; XLAMP_1.6X1.6MM

Connections:
unnamed: C.TP, D1.C
unnamed: A.TP, D1.A
unnamed: C1.TP, D2.C
unnamed: A1.TP, D2.A
unnamed: C2.TP, D3.C
unnamed: A2.TP, D3.A
unnamed: C3.TP, D4.C
unnamed: A3.TP, D4.A
unnamed: C4.TP, D5.C
unnamed: A4.TP, D5.A
unnamed: C5.TP, D6.C
unnamed: A5.TP, D6.A
unnamed: C6.TP, D7.C
unnamed: A6.TP, D7.A
unnamed: C7.TP, D8.C
unnamed: A7.TP, D8.A
unnamed: C8.TP, D9.C
unnamed: A8.TP, D9.A
unnamed: C9.TP, D10.C
unnamed: A9.TP, D10.A
unnamed: C10.TP, D11.C
unnamed: A10.TP, D11.A
unnamed: C11.TP, D12.C
unnamed: A11.TP, D12.A
unnamed: C12.TP, D13.C
unnamed: A12.TP, D13.A
unnamed: C13.TP, D14.C
unnamed: A13.TP, D14.A
unnamed: C15.TP, D16.C
unnamed: A15.TP, D16.A
unnamed: C16.TP, D17.C
unnamed: A16.TP, D17.A

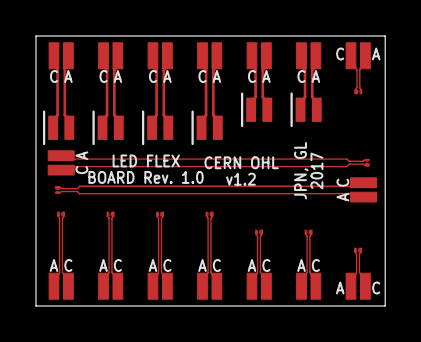
[picture p197: board led-flex-board.brd from above]

Board: 1 copper layer, 19.4 x 15.0 mm, 48 parts (0 on the bottom side), 32 nets.
