jonnew/ONIX/led-board/led-board.brd

## EAGLE design led-board/led-board.brd (2017-12-14)

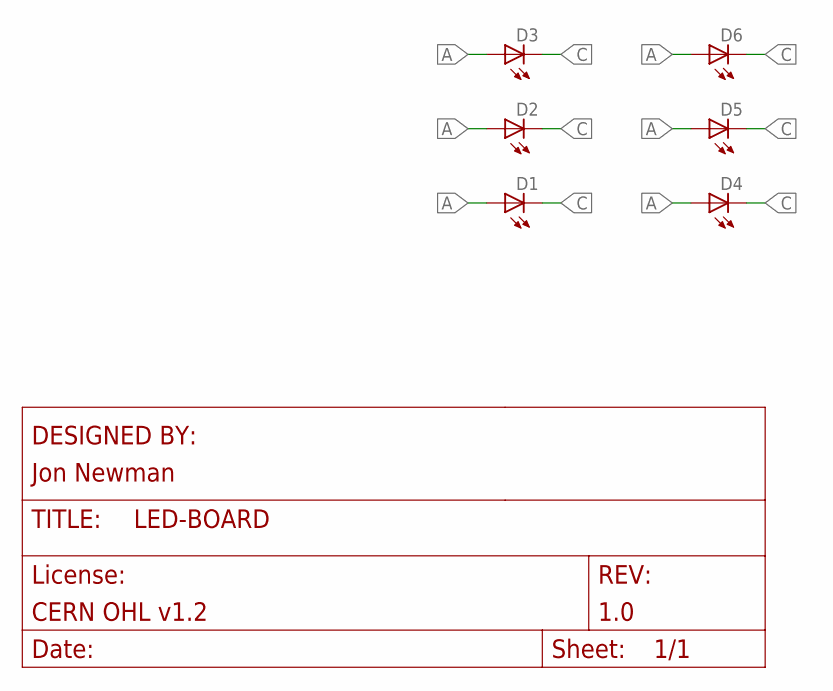
[picture p198: schematic led-board.sch]

Parts:
D1, D2, D3, D4, D5, D6: LED_LXZ1; LXZ1

Connections:
A: D1.A, D2.A, D3.A, D4.A, D5.A, D6.A
C: D1.C, D2.C, D3.C, D4.C, D5.C, D6.C

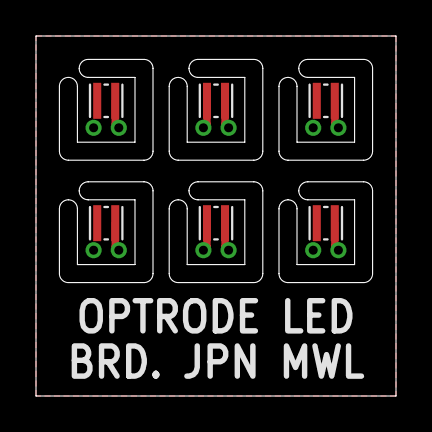
[picture p199: board led-board.brd from above]

Board: 2 copper layers, 20.0 x 20.0 mm, 6 parts (0 on the bottom side), 2 nets.
