jonnew/ONIX/eib-128/eib-128.brd

## EAGLE design eib-128/eib-128.brd (2017-11-18)

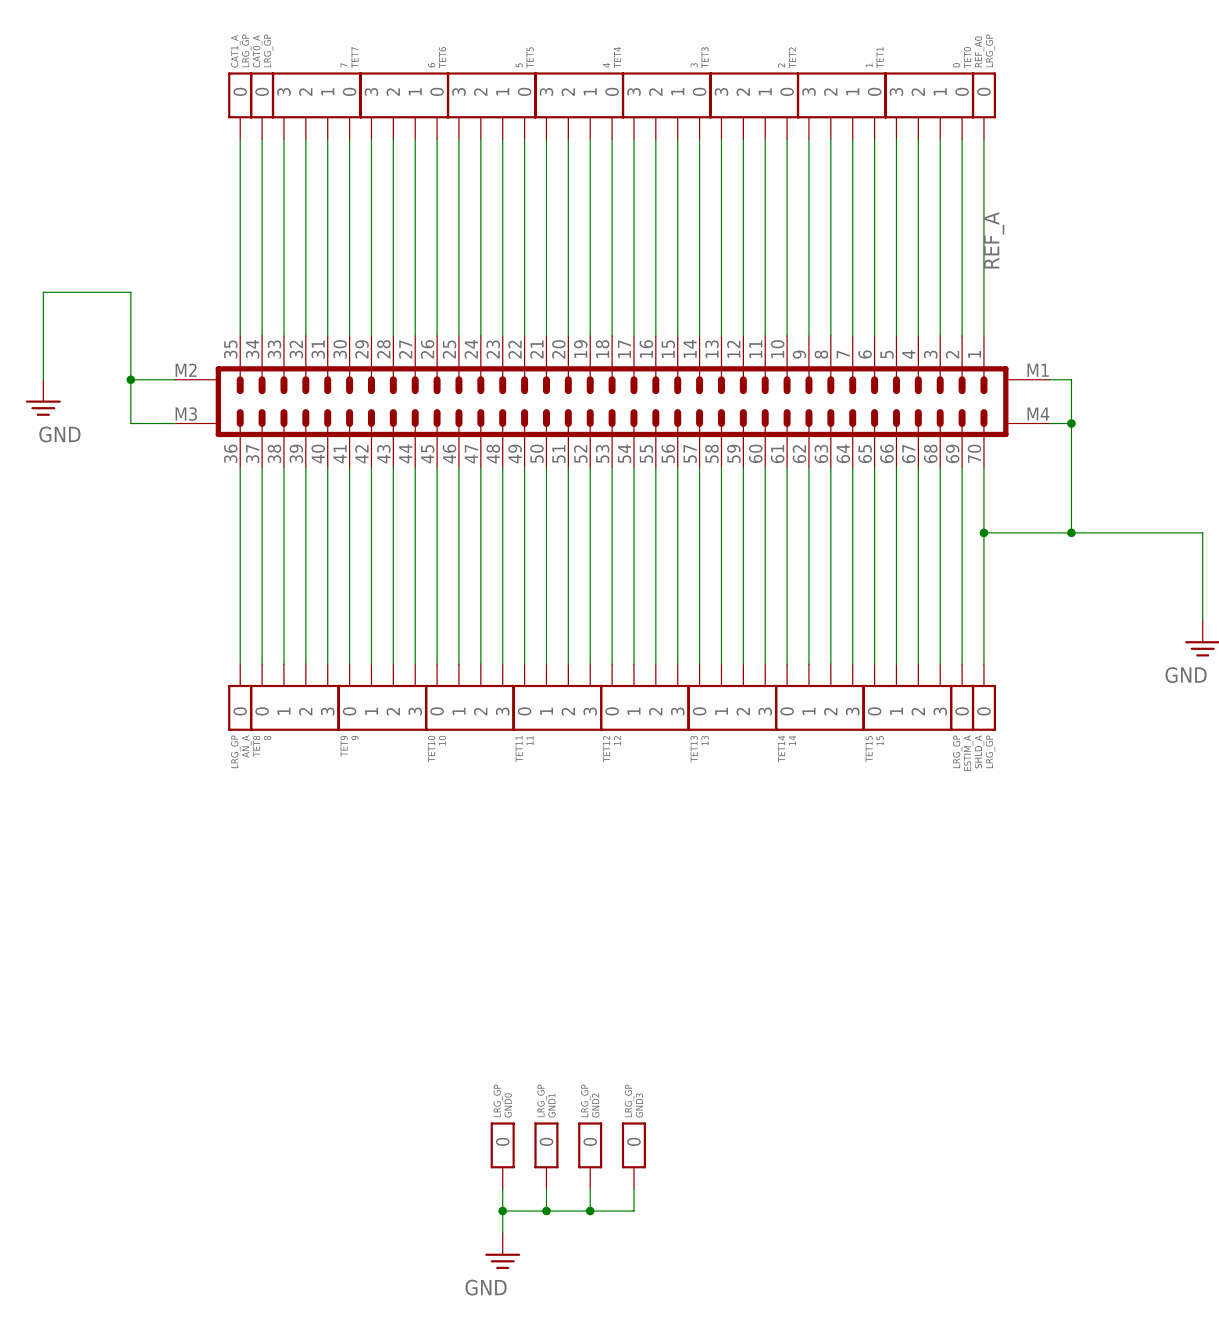
[picture p200: schematic eib-128.sch, part in row 1, column 1]

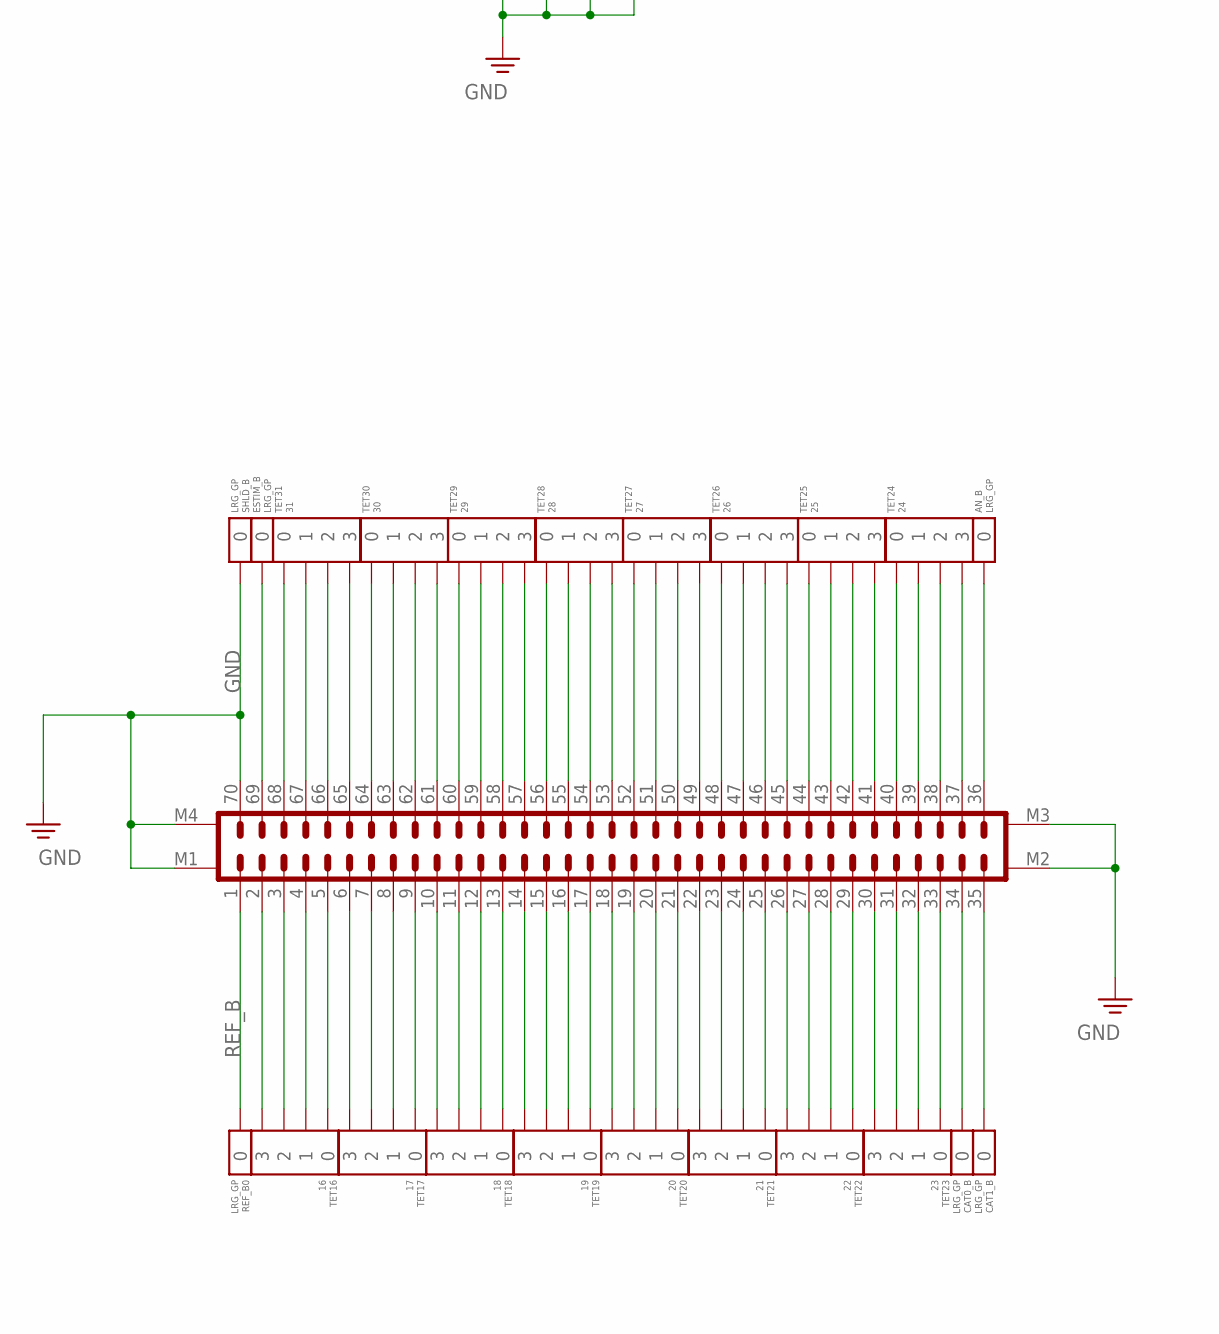
[picture p201: schematic eib-128.sch, part in row 2, column 1]

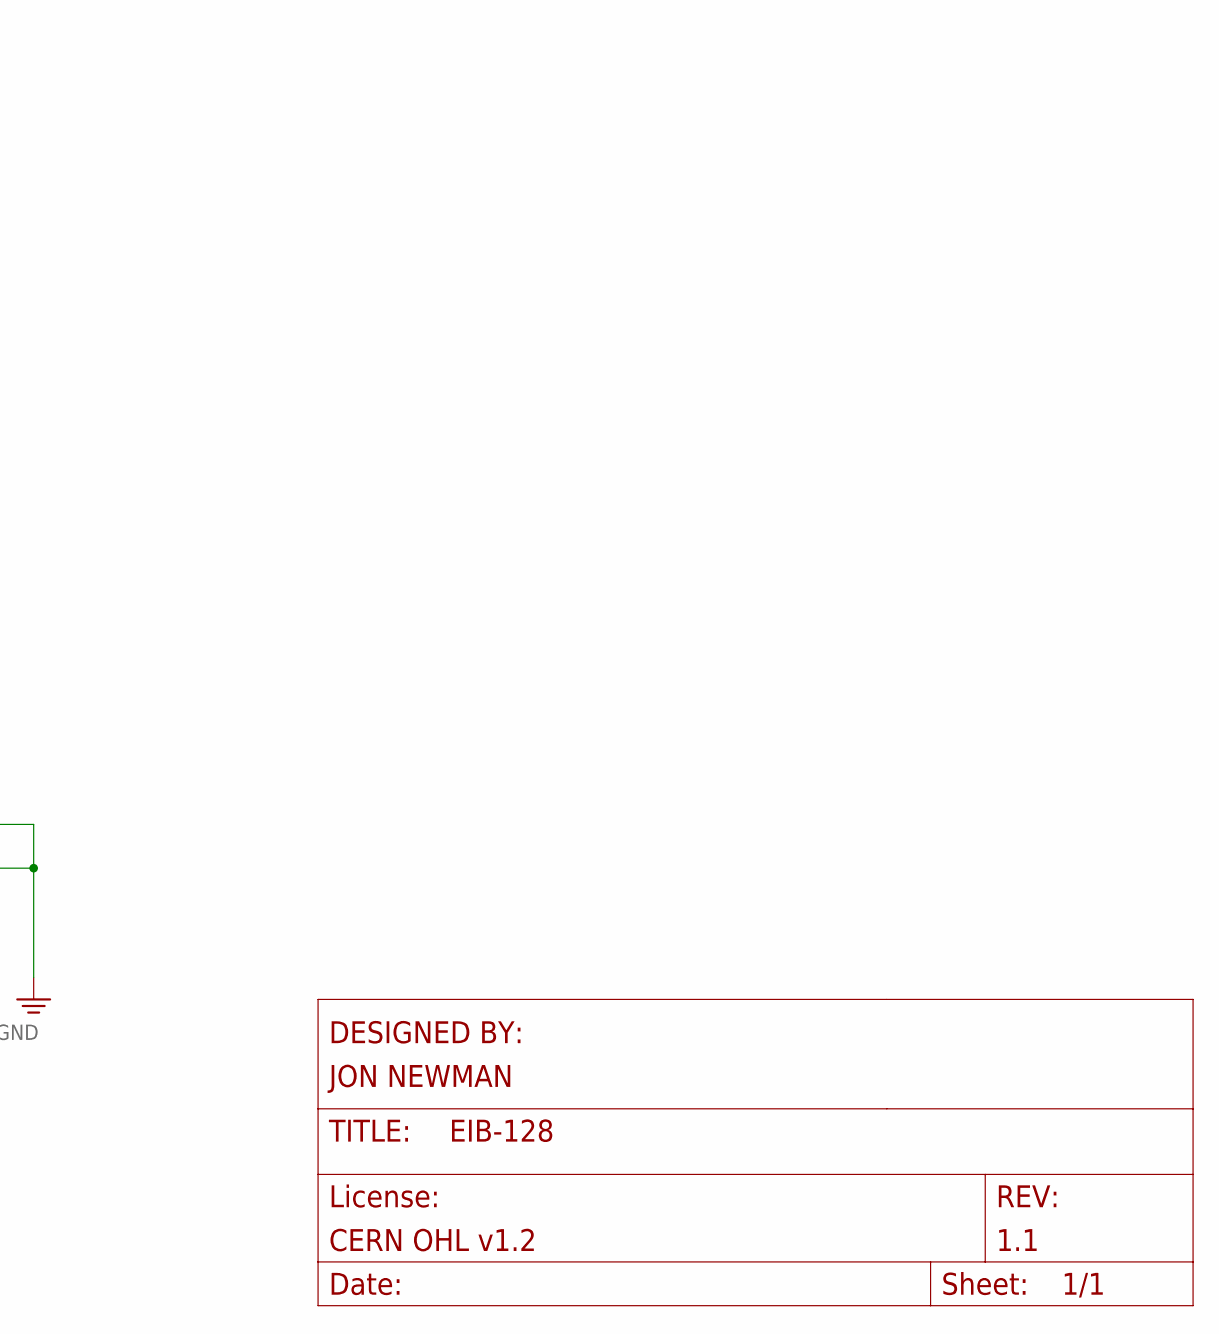
[picture p202: schematic eib-128.sch, part in row 2, column 2]

Parts:
A: DF40HEAD; DF40-70HEAD
AN_A: LRG_GP; GOLDPIN_0.5ID_0.7OD
AN_B: LRG_GP; GOLDPIN_0.5ID_0.7OD
B: DF40HEAD; DF40-70HEAD
CAT0_A, CAT0_B, CAT1_A, CAT1_B: LRG_GP; GOLDPIN_0.5ID_0.7OD
ESTIM_A: LRG_GP; GOLDPIN_0.5ID_0.7OD
ESTIM_B: LRG_GP; GOLDPIN_0.5ID_0.7OD
GND0, GND1, GND2, GND3: LRG_GP; GOLDPIN_0.5ID_0.7OD
REF_A0: LRG_GP; GOLDPIN_0.5ID_0.7OD
REF_B0: LRG_GP; GOLDPIN_0.5ID_0.7OD
SHLD_A: LRG_GP; GOLDPIN_0.5ID_0.7OD
SHLD_B: LRG_GP; GOLDPIN_0.5ID_0.7OD
TET0: 0; TETRODE_128_0.5ID_0.7OD
TET1: 1; TETRODE_128_0.5ID_0.7OD
TET2: 2; TETRODE_128_0.5ID_0.7OD
TET3: 3; TETRODE_128_0.5ID_0.7OD
TET4: 4; TETRODE_128_0.5ID_0.7OD
TET5: 5; TETRODE_128_0.5ID_0.7OD
TET6: 6; TETRODE_128_0.5ID_0.7OD
TET7: 7; TETRODE_128_0.5ID_0.7OD
TET8: 8; TETRODE_128_0.5ID_0.7OD
TET9: 9; TETRODE_128_0.5ID_0.7OD
TET10: 10; TETRODE_128_0.5ID_0.7OD
TET11: 11; TETRODE_128_0.5ID_0.7OD
TET12: 12; TETRODE_128_0.5ID_0.7OD
TET13: 13; TETRODE_128_0.5ID_0.7OD
TET14: 14; TETRODE_128_0.5ID_0.7OD
TET15: 15; TETRODE_128_0.5ID_0.7OD
TET16: 16; TETRODE_128_0.5ID_0.7OD
TET17: 17; TETRODE_128_0.5ID_0.7OD
TET18: 18; TETRODE_128_0.5ID_0.7OD
TET19: 19; TETRODE_128_0.5ID_0.7OD
TET20: 20; TETRODE_128_0.5ID_0.7OD
TET21: 21; TETRODE_128_0.5ID_0.7OD
TET22: 22; TETRODE_128_0.5ID_0.7OD
TET23: 23; TETRODE_128_0.5ID_0.7OD
TET24: 24; TETRODE_128_0.5ID_0.7OD
TET25: 25; TETRODE_128_0.5ID_0.7OD
TET26: 26; TETRODE_128_0.5ID_0.7OD
TET27: 27; TETRODE_128_0.5ID_0.7OD
TET28: 28; TETRODE_128_0.5ID_0.7OD
TET29: 29; TETRODE_128_0.5ID_0.7OD
TET30: 30; TETRODE_128_0.5ID_0.7OD
TET31: 31; TETRODE_128_0.5ID_0.7OD

Connections:
AN_A: A.36, AN_A.P$1
AN_B: AN_B.P$1, B.36
CAT0_A: A.34, CAT0_A.P$1
CAT0_B: B.34, CAT0_B.P$1
CAT1_A: A.35, CAT1_A.P$1
CAT1_B: B.35, CAT1_B.P$1
ESTIM_A: A.69, ESTIM_A.P$1
ESTIM_B: B.69, ESTIM_B.P$1
GND: A.70, A.M1, A.M2, A.M3, A.M4, B.70, B.M1, B.M2, B.M3, B.M4, GND0.P$1, GND1.P$1, GND2.P$1, GND3.P$1, SHLD_A.P$1, SHLD_B.P$1
unnamed: B.33, TET23.0
unnamed: B.32, TET23.1
unnamed: B.31, TET23.2
unnamed: B.30, TET23.3
unnamed: B.29, TET22.0
unnamed: B.28, TET22.1
unnamed: B.27, TET22.2
unnamed: B.26, TET22.3
unnamed: B.25, TET21.0
unnamed: B.24, TET21.1
unnamed: B.23, TET21.2
unnamed: B.22, TET21.3
unnamed: B.21, TET20.0
unnamed: B.20, TET20.1
unnamed: B.19, TET20.2
unnamed: B.18, TET20.3
unnamed: B.17, TET19.0
unnamed: B.16, TET19.1
unnamed: B.15, TET19.2
unnamed: B.14, TET19.3
unnamed: B.13, TET18.0
unnamed: B.12, TET18.1
unnamed: B.11, TET18.2
unnamed: B.10, TET18.3
unnamed: B.9, TET17.0
unnamed: B.8, TET17.1
unnamed: B.7, TET17.2
unnamed: B.6, TET17.3
unnamed: B.5, TET16.0
unnamed: B.4, TET16.1
unnamed: B.3, TET16.2
unnamed: B.38, TET24.2
unnamed: B.39, TET24.1
unnamed: B.40, TET24.0
unnamed: B.41, TET25.3
unnamed: B.42, TET25.2
unnamed: B.43, TET25.1
unnamed: B.44, TET25.0
unnamed: B.45, TET26.3
unnamed: B.46, TET26.2
unnamed: B.47, TET26.1
unnamed: B.48, TET26.0
unnamed: B.49, TET27.3
unnamed: B.50, TET27.2
unnamed: B.51, TET27.1
unnamed: B.52, TET27.0
unnamed: B.53, TET28.3
unnamed: B.54, TET28.2
unnamed: B.55, TET28.1
unnamed: B.56, TET28.0
unnamed: B.57, TET29.3
unnamed: B.58, TET29.2
unnamed: B.59, TET29.1
unnamed: B.60, TET29.0
unnamed: B.61, TET30.3
unnamed: B.62, TET30.2
unnamed: B.63, TET30.1
unnamed: B.64, TET30.0
unnamed: B.65, TET31.3
unnamed: B.66, TET31.2
unnamed: B.67, TET31.1
unnamed: B.68, TET31.0
unnamed: B.2, TET16.3
unnamed: B.37, TET24.3
unnamed: A.33, TET7.3
unnamed: A.32, TET7.2
unnamed: A.31, TET7.1
unnamed: A.30, TET7.0
unnamed: A.29, TET6.3
unnamed: A.28, TET6.2
unnamed: A.27, TET6.1
unnamed: A.26, TET6.0
unnamed: A.25, TET5.3
unnamed: A.24, TET5.2
unnamed: A.23, TET5.1
unnamed: A.22, TET5.0
unnamed: A.21, TET4.3
unnamed: A.20, TET4.2
unnamed: A.19, TET4.1
unnamed: A.18, TET4.0
unnamed: A.17, TET3.3
unnamed: A.16, TET3.2
unnamed: A.15, TET3.1
unnamed: A.14, TET3.0
unnamed: A.13, TET2.3
unnamed: A.12, TET2.2
unnamed: A.11, TET2.1
unnamed: A.10, TET2.0
unnamed: A.9, TET1.3
unnamed: A.8, TET1.2
unnamed: A.7, TET1.1
unnamed: A.6, TET1.0
unnamed: A.5, TET0.3
unnamed: A.4, TET0.2
unnamed: A.3, TET0.1
unnamed: A.2, TET0.0
unnamed: A.38, TET8.1
unnamed: A.39, TET8.2
unnamed: A.40, TET8.3
unnamed: A.41, TET9.0
unnamed: A.42, TET9.1
unnamed: A.43, TET9.2
unnamed: A.44, TET9.3
unnamed: A.45, TET10.0
unnamed: A.46, TET10.1
unnamed: A.47, TET10.2
unnamed: A.48, TET10.3
unnamed: A.49, TET11.0
unnamed: A.50, TET11.1
unnamed: A.51, TET11.2
unnamed: A.52, TET11.3
unnamed: A.53, TET12.0
unnamed: A.54, TET12.1
unnamed: A.55, TET12.2
unnamed: A.56, TET12.3
unnamed: A.57, TET13.0
unnamed: A.58, TET13.1
unnamed: A.59, TET13.2
unnamed: A.60, TET13.3
unnamed: A.61, TET14.0
unnamed: A.62, TET14.1
unnamed: A.63, TET14.2
unnamed: A.64, TET14.3
unnamed: A.65, TET15.0
unnamed: A.66, TET15.1
unnamed: A.67, TET15.2
unnamed: A.68, TET15.3
unnamed: A.37, TET8.0
REF_A: A.1, REF_A0.P$1
REF_B: B.1, REF_B0.P$1

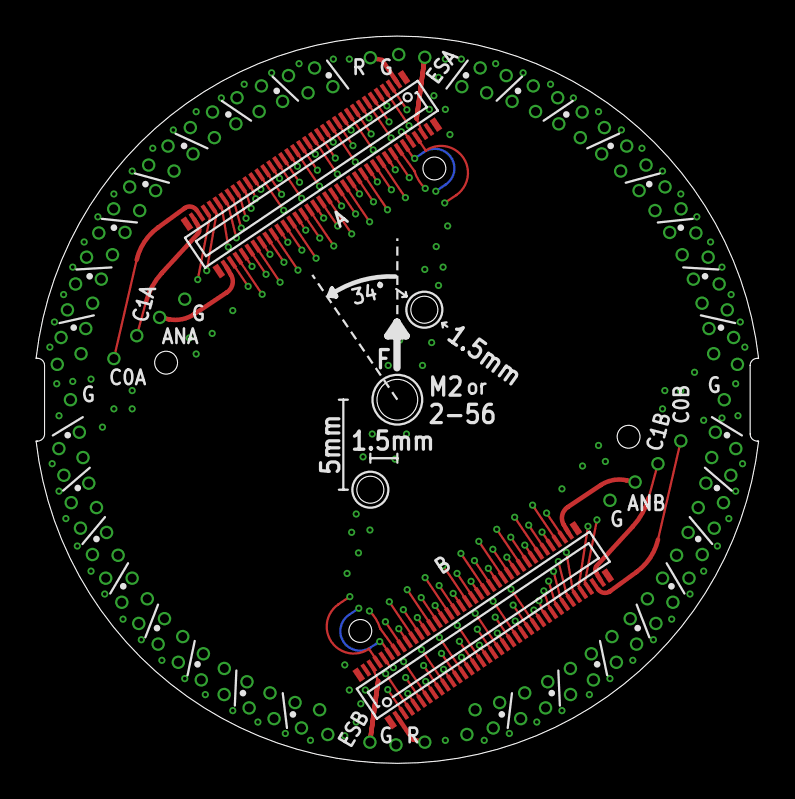
[picture p203: board eib-128.brd from above]

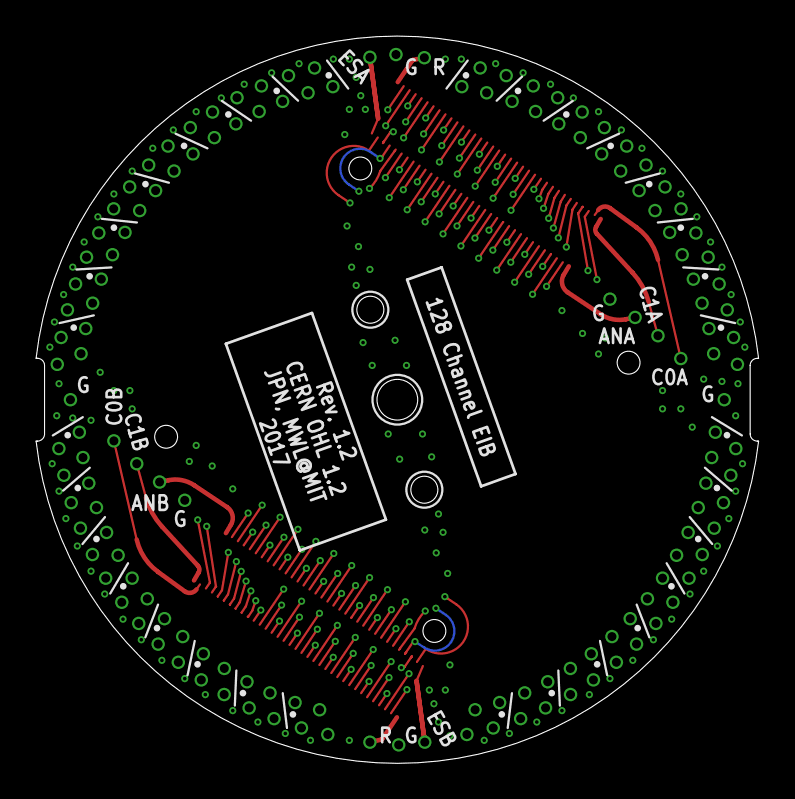
[picture p204: board eib-128.brd from below]

Board: 4 copper layers, 40.1 x 40.4 mm, 51 parts (16 on the bottom side), 139 nets.

Other parts of the board:
U$1: EIB_MOUNT_A
