jonnew/ONIX/headstage/headstage.brd

## EAGLE design headstage/headstage.brd (2017-07-25)

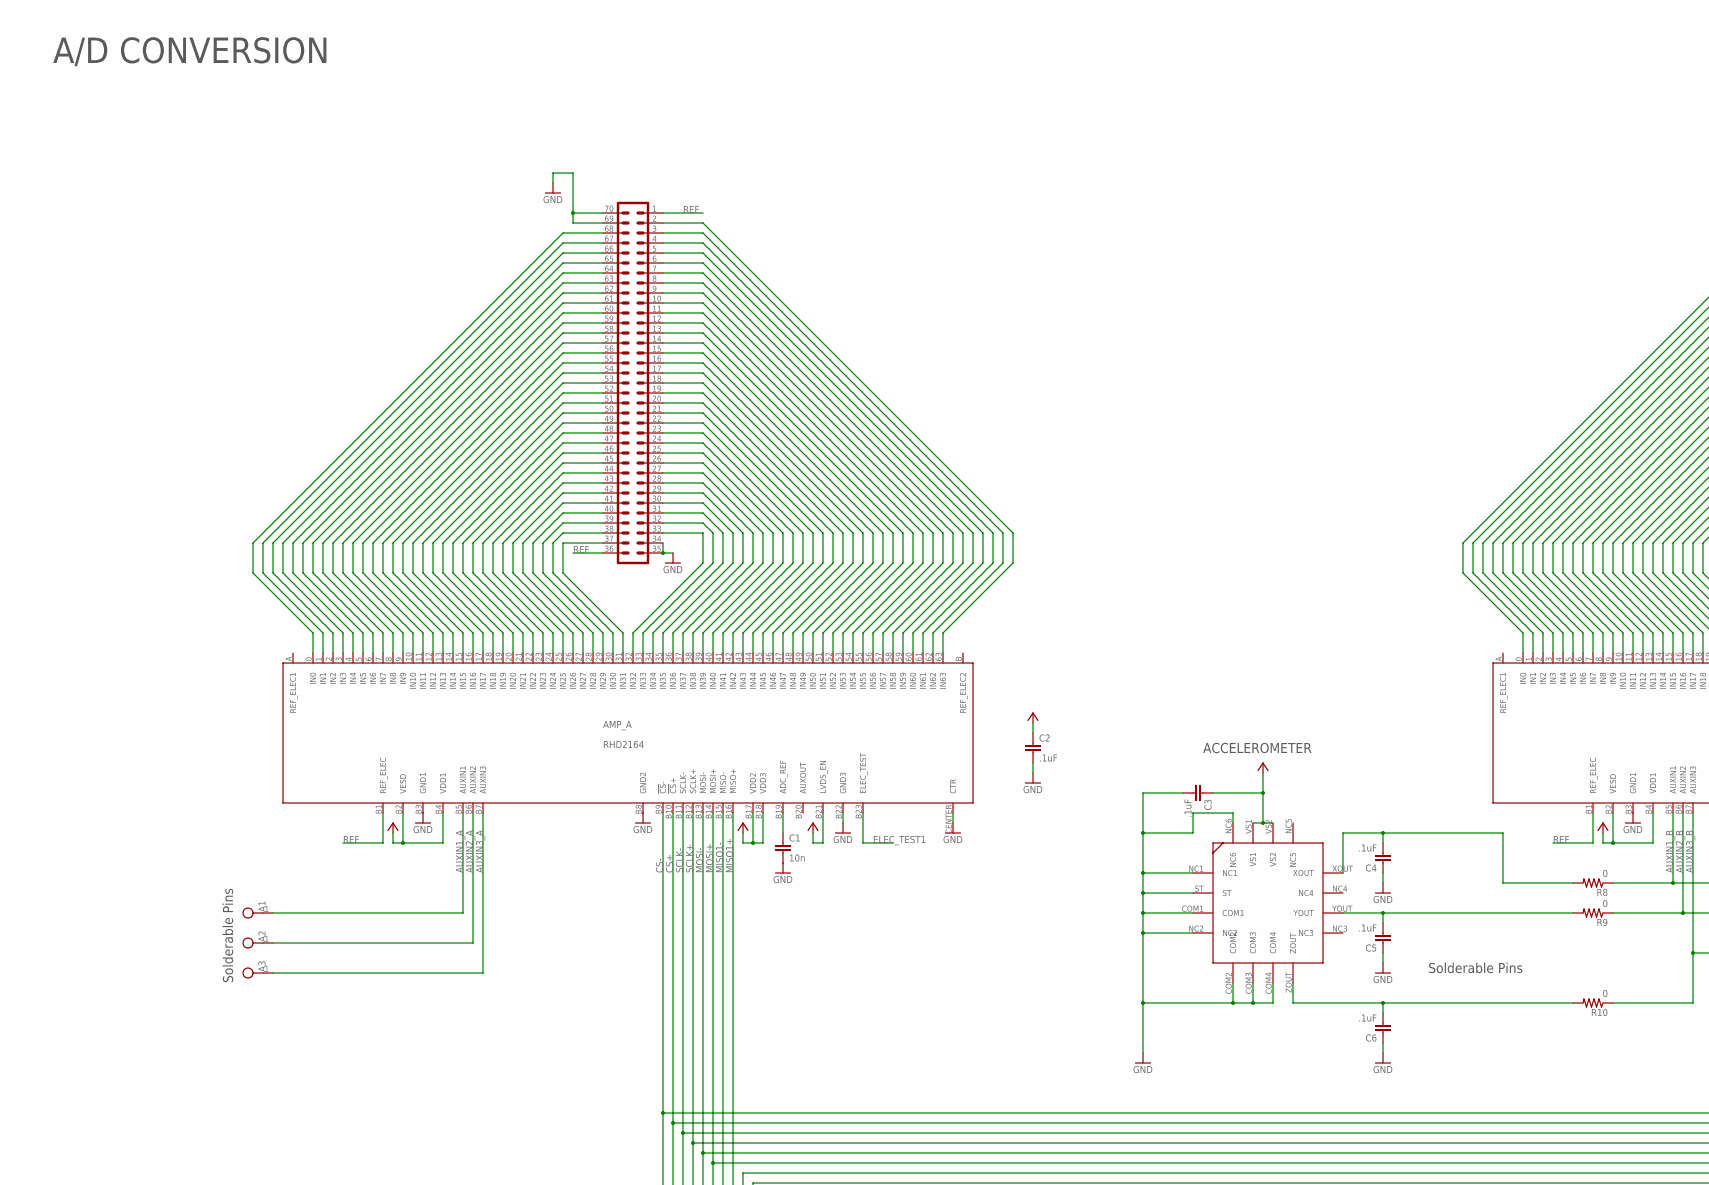
[picture p205: schematic headstage.sch, part in row 1, column 1]

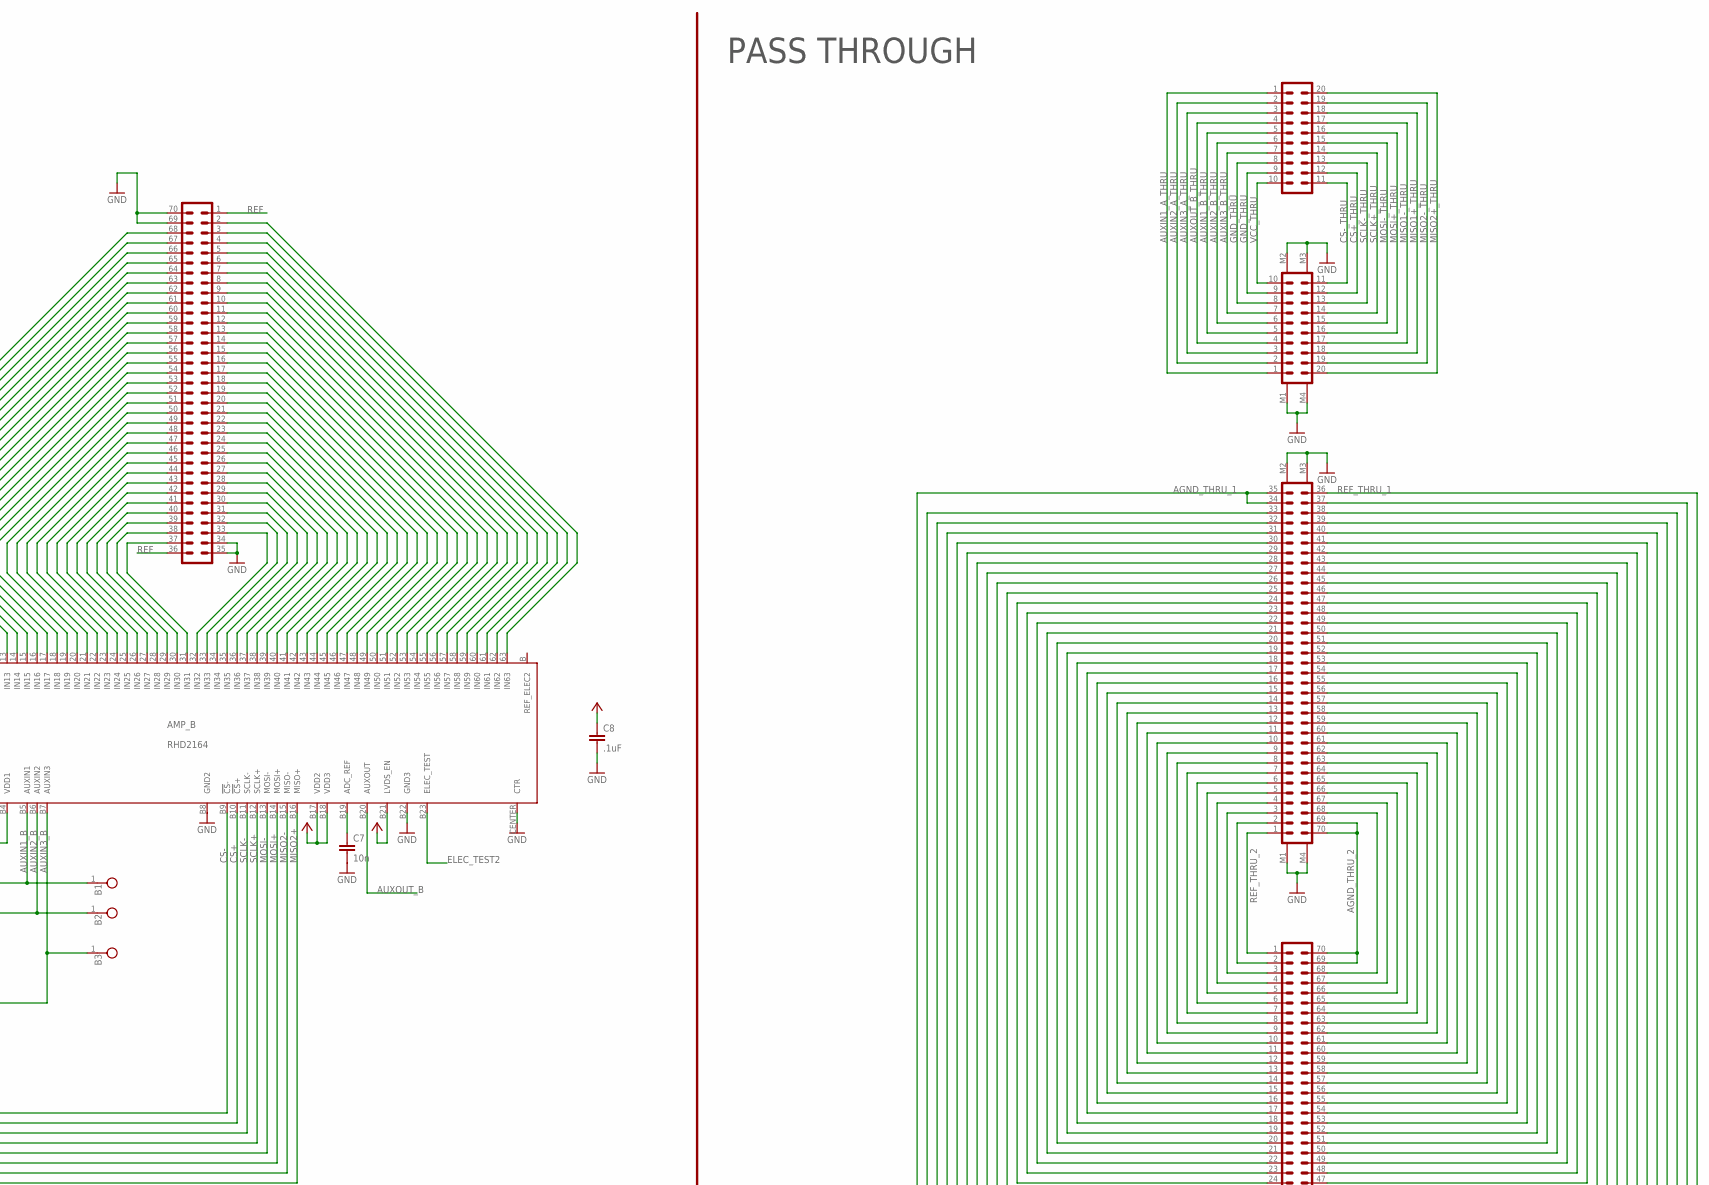
[picture p206: schematic headstage.sch, part in row 1, column 2]

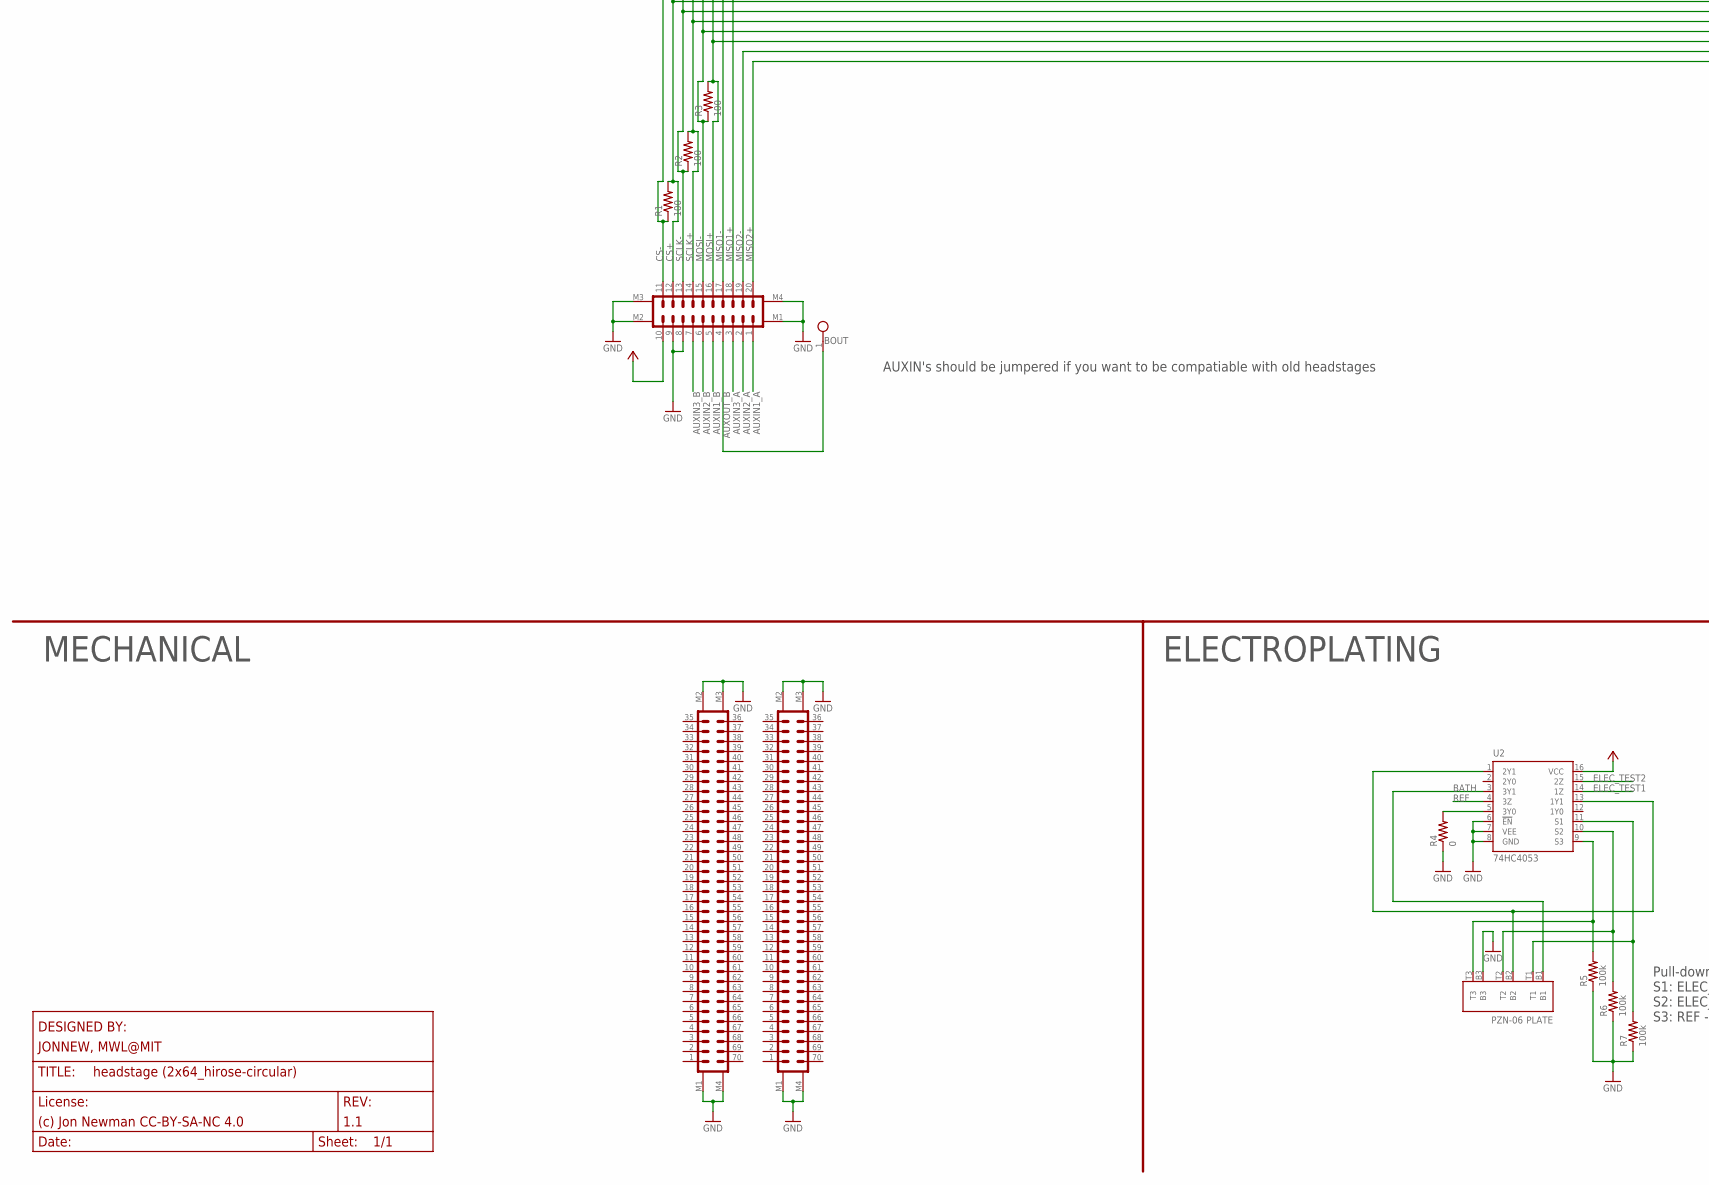
[picture p207: schematic headstage.sch, part in row 2, column 1]

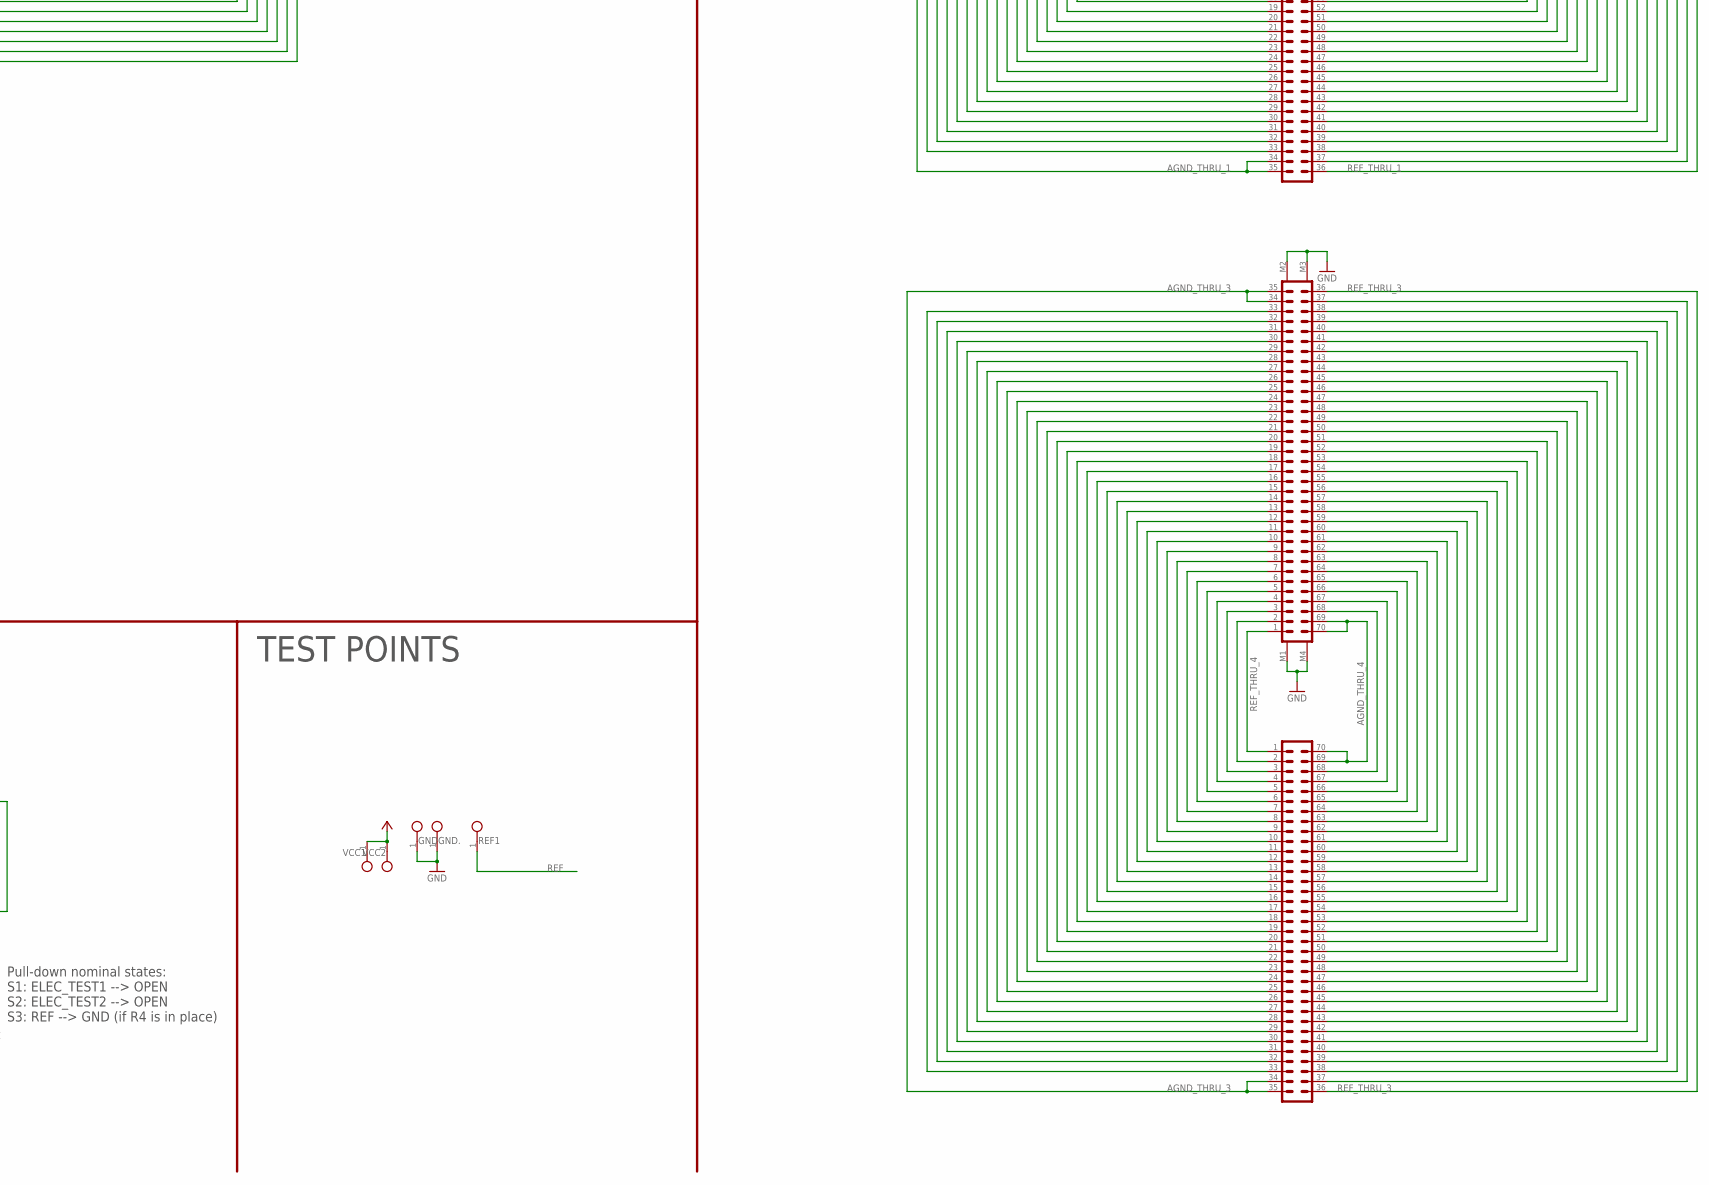
[picture p208: schematic headstage.sch, part in row 2, column 2]

Parts:
A1, A2, A3: TESTPOINT_SMALL
AIN_BNB: DF40REC; DF40-70REC
AIN_BSB: DF40REC; DF40-70REC
AMP_A: RHD2164; RHD2164_COB
AMP_B: RHD2164; RHD2164_COB
ATHRU_BEB: DF40REC; DF40-70REC
ATHRU_BWB: DF40REC; DF40-70REC
ATHRU_TEB: DF40HEAD; DF40-70HEAD
ATHRU_TWB: DF40HEAD; DF40-70HEAD
B1, B2, B3: TESTPOINT_SMALL
BOUT: TESTPOINT_SMALL
C1, C7: 10n; 0201
C2, C3, C4, C5, C6, C8: .1uF; 0402
DIO_TEA: DF40HEAD; DF40-20HEAD
DTHRU_BNA: DF40REC; DF40-20REC
DTHRU_TNA: DF40HEAD; DF40-20HEAD
GND, GND.: GND; TESTPOINT_SMALL
MECH_TNB: DF40HEAD; DF40-70HEAD
MECH_TSB: DF40HEAD; DF40-70HEAD
PLATE: PZN-06; OMNETICS_PZN-06-AA
R1, R2, R3: 100; 0402
R4, R8, R9, R10: 0; 0402
R5, R6, R7: 100k; 0201
REF1: REF; TESTPOINT_SMALL
U1: ADXL335
U2: 74HC4053; TSSOP-16
VCC1, VCC2: VCC; TESTPOINT_SMALL

Connections:
AGND_THRU_1: ATHRU_BWB.34, ATHRU_BWB.35, ATHRU_TWB.34, ATHRU_TWB.35
AGND_THRU_2: ATHRU_BWB.69, ATHRU_BWB.70, ATHRU_TWB.69, ATHRU_TWB.70
AGND_THRU_3: ATHRU_BEB.34, ATHRU_BEB.35, ATHRU_TEB.34, ATHRU_TEB.35
AGND_THRU_4: ATHRU_BEB.69, ATHRU_BEB.70, ATHRU_TEB.69, ATHRU_TEB.70
AUXIN1_A: A1.1, AMP_A.B5 (AUXIN1), DIO_TEA.1
AUXIN1_A_THRU: DTHRU_BNA.1, DTHRU_TNA.1
AUXIN1_B: AMP_B.B5 (AUXIN1), B1.1, DIO_TEA.5, R8.1
AUXIN1_B_THRU: DTHRU_BNA.5, DTHRU_TNA.5
AUXIN2_A: A2.1, AMP_A.B6 (AUXIN2), DIO_TEA.2
AUXIN2_A_THRU: DTHRU_BNA.2, DTHRU_TNA.2
AUXIN2_B: AMP_B.B6 (AUXIN2), B2.1, DIO_TEA.6, R9.1
AUXIN2_B_THRU: DTHRU_BNA.6, DTHRU_TNA.6
AUXIN3_A: A3.1, AMP_A.B7 (AUXIN3), DIO_TEA.3
AUXIN3_A_THRU: DTHRU_BNA.3, DTHRU_TNA.3
AUXIN3_B: AMP_B.B7 (AUXIN3), B3.1, DIO_TEA.7, R10.1
AUXIN3_B_THRU: DTHRU_BNA.7, DTHRU_TNA.7
AUXOUT_B: AMP_B.B20 (AUXOUT), BOUT.1, DIO_TEA.4
AUXOUT_B_THRU: DTHRU_BNA.4, DTHRU_TNA.4
BATH: PLATE.B1, U2.3 (3Y1)
CS+: AMP_A.B10 (!CS!+), AMP_B.B10 (!CS!+), DIO_TEA.12, R1.2
CS+_THRU: DTHRU_BNA.12, DTHRU_TNA.12
CS-: AMP_A.B9 (!CS!-), AMP_B.B9 (!CS!-), DIO_TEA.11, R1.1
CS-_THRU: DTHRU_BNA.11, DTHRU_TNA.11
ELEC_TEST1: AMP_A.B23 (ELEC_TEST), U2.14 (1Z)
ELEC_TEST2: AMP_B.B23 (ELEC_TEST), U2.15 (2Z)
GND: AIN_BNB.34, AIN_BNB.35, AIN_BNB.69, AIN_BNB.70, AIN_BSB.34, AIN_BSB.35, AIN_BSB.69, AIN_BSB.70, AMP_A.B3 (GND1), AMP_A.B8 (GND2), AMP_A.B22 (GND3), AMP_A.CENTER (CTR), AMP_B.B3 (GND1), AMP_B.B8 (GND2), AMP_B.B22 (GND3), AMP_B.CENTER (CTR), ATHRU_TEB.M1, ATHRU_TEB.M2, ATHRU_TEB.M3, ATHRU_TEB.M4, ATHRU_TWB.M1, ATHRU_TWB.M2, ATHRU_TWB.M3, ATHRU_TWB.M4, C1.2, C2.2, C3.2, C4.1, C5.1, C6.1, C7.2, C8.2, DIO_TEA.8, DIO_TEA.9, DIO_TEA.M1, DIO_TEA.M2, DIO_TEA.M3, DIO_TEA.M4, DTHRU_TNA.M1, DTHRU_TNA.M2, DTHRU_TNA.M3, DTHRU_TNA.M4, GND.1, GND..1, MECH_TNB.M1, MECH_TNB.M2, MECH_TNB.M3, MECH_TNB.M4, MECH_TSB.M1, MECH_TSB.M2, MECH_TSB.M3, MECH_TSB.M4, PLATE.B3, R4.1, R5.1, R6.1, R7.1, U1.COM1, U1.COM2, U1.COM3, U1.COM4, U1.NC1, U1.NC2, U1.NC6, U1.ST, U2.6 (!EN!), U2.7 (VEE), U2.8 (GND)
GND_THRU: DTHRU_BNA.8, DTHRU_BNA.9, DTHRU_TNA.8, DTHRU_TNA.9
MISO1+: AMP_A.B16 (MISO+), DIO_TEA.18
MISO1+_THRU: DTHRU_BNA.18, DTHRU_TNA.18
MISO1-: AMP_A.B15 (MISO-), DIO_TEA.17
MISO1-_THRU: DTHRU_BNA.17, DTHRU_TNA.17
MISO2+: AMP_B.B16 (MISO+), DIO_TEA.20
MISO2+_THRU: DTHRU_BNA.20, DTHRU_TNA.20
MISO2-: AMP_B.B15 (MISO-), DIO_TEA.19
MISO2-_THRU: DTHRU_BNA.19, DTHRU_TNA.19
MOSI+: AMP_A.B14 (MOSI+), AMP_B.B14 (MOSI+), DIO_TEA.16, R3.2
MOSI+_THRU: DTHRU_BNA.16, DTHRU_TNA.16
MOSI-: AMP_A.B13 (MOSI-), AMP_B.B13 (MOSI-), DIO_TEA.15, R3.1
MOSI-_THRU: DTHRU_BNA.15, DTHRU_TNA.15
unnamed: AMP_B.B19 (ADC_REF), C7.1
unnamed: AIN_BNB.38, AMP_A.30 (IN30)
unnamed: AIN_BNB.39, AMP_A.29 (IN29)
unnamed: AIN_BNB.40, AMP_A.28 (IN28)
unnamed: AIN_BNB.41, AMP_A.27 (IN27)
unnamed: AIN_BNB.42, AMP_A.26 (IN26)
unnamed: AIN_BNB.32, AMP_A.33 (IN33)
unnamed: AIN_BNB.31, AMP_A.34 (IN34)
unnamed: AIN_BNB.30, AMP_A.35 (IN35)
unnamed: AIN_BNB.29, AMP_A.36 (IN36)
unnamed: AIN_BSB.38, AMP_B.30 (IN30)
unnamed: AIN_BNB.28, AMP_A.37 (IN37)
unnamed: AIN_BNB.27, AMP_A.38 (IN38)
unnamed: AIN_BNB.26, AMP_A.39 (IN39)
unnamed: AIN_BNB.25, AMP_A.40 (IN40)
unnamed: AIN_BNB.24, AMP_A.41 (IN41)
unnamed: AIN_BNB.23, AMP_A.42 (IN42)
unnamed: AIN_BNB.22, AMP_A.43 (IN43)
unnamed: AIN_BNB.21, AMP_A.44 (IN44)
unnamed: AIN_BNB.20, AMP_A.45 (IN45)
unnamed: AIN_BNB.19, AMP_A.46 (IN46)
unnamed: AIN_BNB.18, AMP_A.47 (IN47)
unnamed: AIN_BNB.17, AMP_A.48 (IN48)
unnamed: AIN_BNB.16, AMP_A.49 (IN49)
unnamed: AIN_BNB.15, AMP_A.50 (IN50)
unnamed: AIN_BNB.14, AMP_A.51 (IN51)
unnamed: AIN_BNB.13, AMP_A.52 (IN52)
unnamed: AIN_BNB.12, AMP_A.53 (IN53)
unnamed: AIN_BNB.11, AMP_A.54 (IN54)
unnamed: AIN_BNB.10, AMP_A.55 (IN55)
unnamed: AIN_BNB.9, AMP_A.56 (IN56)
unnamed: AIN_BNB.8, AMP_A.57 (IN57)
unnamed: AIN_BNB.7, AMP_A.58 (IN58)
unnamed: AIN_BNB.6, AMP_A.59 (IN59)
unnamed: AIN_BSB.39, AMP_B.29 (IN29)
unnamed: AIN_BSB.40, AMP_B.28 (IN28)
unnamed: AIN_BSB.41, AMP_B.27 (IN27)
unnamed: AIN_BSB.42, AMP_B.26 (IN26)
unnamed: AIN_BSB.43, AMP_B.25 (IN25)
unnamed: AIN_BSB.44, AMP_B.24 (IN24)
unnamed: AIN_BNB.5, AMP_A.60 (IN60)
unnamed: AMP_A.B19 (ADC_REF), C1.1
unnamed: AIN_BNB.4, AMP_A.61 (IN61)
unnamed: AIN_BNB.3, AMP_A.62 (IN62)
unnamed: AIN_BNB.2, AMP_A.63 (IN63)
unnamed: AIN_BNB.33, AMP_A.32 (IN32)
unnamed: AIN_BSB.45, AMP_B.23 (IN23)
unnamed: AIN_BSB.46, AMP_B.22 (IN22)
unnamed: AIN_BSB.47, AMP_B.21 (IN21)
unnamed: AIN_BSB.48, AMP_B.20 (IN20)
unnamed: AIN_BSB.49, AMP_B.19 (IN19)
unnamed: AIN_BSB.50, AMP_B.18 (IN18)
unnamed: AIN_BSB.51, AMP_B.17 (IN17)
unnamed: AIN_BSB.52, AMP_B.16 (IN16)
unnamed: AIN_BSB.53, AMP_B.15 (IN15)
unnamed: AIN_BSB.54, AMP_B.14 (IN14)
unnamed: AIN_BSB.55, AMP_B.13 (IN13)
unnamed: AIN_BSB.56, AMP_B.12 (IN12)
unnamed: AIN_BSB.57, AMP_B.11 (IN11)
unnamed: AIN_BSB.58, AMP_B.10 (IN10)
unnamed: AIN_BSB.59, AMP_B.9 (IN9)
unnamed: AIN_BSB.60, AMP_B.8 (IN8)
unnamed: AIN_BSB.61, AMP_B.7 (IN7)
unnamed: AIN_BSB.62, AMP_B.6 (IN6)
unnamed: AIN_BSB.63, AMP_B.5 (IN5)
unnamed: AIN_BSB.64, AMP_B.4 (IN4)
unnamed: AIN_BSB.65, AMP_B.3 (IN3)
unnamed: AIN_BSB.66, AMP_B.2 (IN2)
unnamed: AIN_BSB.67, AMP_B.1 (IN1)
unnamed: AIN_BNB.43, AMP_A.25 (IN25)
unnamed: AIN_BNB.44, AMP_A.24 (IN24)
unnamed: AIN_BNB.45, AMP_A.23 (IN23)
unnamed: AIN_BNB.46, AMP_A.22 (IN22)
unnamed: AIN_BSB.68, AMP_B.0 (IN0)
unnamed: AIN_BSB.37, AMP_B.31 (IN31)
unnamed: AIN_BSB.32, AMP_B.33 (IN33)
unnamed: AIN_BSB.31, AMP_B.34 (IN34)
unnamed: AIN_BSB.30, AMP_B.35 (IN35)
unnamed: AIN_BSB.29, AMP_B.36 (IN36)
unnamed: AIN_BSB.28, AMP_B.37 (IN37)
unnamed: AIN_BSB.27, AMP_B.38 (IN38)
unnamed: AIN_BSB.26, AMP_B.39 (IN39)
unnamed: AIN_BSB.25, AMP_B.40 (IN40)
unnamed: AIN_BSB.24, AMP_B.41 (IN41)
unnamed: AIN_BSB.23, AMP_B.42 (IN42)
unnamed: AIN_BSB.22, AMP_B.43 (IN43)
unnamed: AIN_BSB.21, AMP_B.44 (IN44)
unnamed: AIN_BSB.20, AMP_B.45 (IN45)
unnamed: AIN_BSB.19, AMP_B.46 (IN46)
unnamed: AIN_BSB.18, AMP_B.47 (IN47)
unnamed: AIN_BSB.17, AMP_B.48 (IN48)
unnamed: AIN_BSB.16, AMP_B.49 (IN49)
unnamed: AIN_BSB.15, AMP_B.50 (IN50)
unnamed: AIN_BSB.14, AMP_B.51 (IN51)
unnamed: AIN_BSB.13, AMP_B.52 (IN52)
unnamed: AIN_BSB.12, AMP_B.53 (IN53)
unnamed: AIN_BSB.11, AMP_B.54 (IN54)
unnamed: AIN_BSB.10, AMP_B.55 (IN55)
unnamed: AIN_BSB.9, AMP_B.56 (IN56)
unnamed: AIN_BSB.8, AMP_B.57 (IN57)
unnamed: AIN_BSB.7, AMP_B.58 (IN58)
unnamed: AIN_BSB.6, AMP_B.59 (IN59)
unnamed: AIN_BSB.5, AMP_B.60 (IN60)
unnamed: AIN_BSB.4, AMP_B.61 (IN61)
unnamed: AIN_BSB.3, AMP_B.62 (IN62)
unnamed: AIN_BSB.2, AMP_B.63 (IN63)
unnamed: AIN_BSB.33, AMP_B.32 (IN32)
unnamed: ATHRU_BEB.33, ATHRU_TEB.33
unnamed: ATHRU_BEB.32, ATHRU_TEB.32
unnamed: ATHRU_BEB.31, ATHRU_TEB.31
unnamed: ATHRU_BEB.30, ATHRU_TEB.30
unnamed: ATHRU_BEB.29, ATHRU_TEB.29
unnamed: ATHRU_BEB.28, ATHRU_TEB.28
unnamed: ATHRU_BEB.27, ATHRU_TEB.27
unnamed: ATHRU_BEB.26, ATHRU_TEB.26
unnamed: ATHRU_BEB.25, ATHRU_TEB.25
unnamed: ATHRU_BEB.24, ATHRU_TEB.24
unnamed: ATHRU_BEB.23, ATHRU_TEB.23
unnamed: ATHRU_BEB.22, ATHRU_TEB.22
unnamed: ATHRU_BEB.21, ATHRU_TEB.21
unnamed: ATHRU_BEB.20, ATHRU_TEB.20
unnamed: ATHRU_BEB.19, ATHRU_TEB.19
unnamed: ATHRU_BEB.18, ATHRU_TEB.18
unnamed: ATHRU_BEB.17, ATHRU_TEB.17
unnamed: ATHRU_BEB.16, ATHRU_TEB.16
unnamed: ATHRU_BEB.15, ATHRU_TEB.15
unnamed: ATHRU_BEB.14, ATHRU_TEB.14
unnamed: ATHRU_BEB.13, ATHRU_TEB.13
unnamed: ATHRU_BEB.12, ATHRU_TEB.12
unnamed: ATHRU_BEB.11, ATHRU_TEB.11
unnamed: PLATE.T1, R7.2, U2.11 (S1)
unnamed: PLATE.T2, R6.2, U2.10 (S2)
unnamed: PLATE.T3, R5.2, U2.9 (S3)
unnamed: R4.2, U2.5 (3Y0)
unnamed: PLATE.B2, U2.1 (2Y1), U2.13 (1Y1)
unnamed: AIN_BNB.47, AMP_A.21 (IN21)
unnamed: AIN_BNB.48, AMP_A.20 (IN20)
unnamed: AIN_BNB.49, AMP_A.19 (IN19)
unnamed: AIN_BNB.50, AMP_A.18 (IN18)
unnamed: AIN_BNB.51, AMP_A.17 (IN17)
unnamed: AIN_BNB.52, AMP_A.16 (IN16)
unnamed: AIN_BNB.53, AMP_A.15 (IN15)
unnamed: AIN_BNB.54, AMP_A.14 (IN14)
unnamed: AIN_BNB.55, AMP_A.13 (IN13)
unnamed: AIN_BNB.56, AMP_A.12 (IN12)
unnamed: AIN_BNB.57, AMP_A.11 (IN11)
unnamed: AIN_BNB.58, AMP_A.10 (IN10)
unnamed: AIN_BNB.59, AMP_A.9 (IN9)
unnamed: AIN_BNB.60, AMP_A.8 (IN8)
unnamed: AIN_BNB.61, AMP_A.7 (IN7)
unnamed: AIN_BNB.62, AMP_A.6 (IN6)
unnamed: AIN_BNB.63, AMP_A.5 (IN5)
unnamed: AIN_BNB.64, AMP_A.4 (IN4)
unnamed: AIN_BNB.65, AMP_A.3 (IN3)
unnamed: AIN_BNB.66, AMP_A.2 (IN2)
unnamed: ATHRU_BEB.10, ATHRU_TEB.10
unnamed: ATHRU_BEB.9, ATHRU_TEB.9
unnamed: ATHRU_BEB.8, ATHRU_TEB.8
unnamed: ATHRU_BEB.7, ATHRU_TEB.7
unnamed: ATHRU_BEB.6, ATHRU_TEB.6
unnamed: AIN_BNB.37, AMP_A.31 (IN31)
unnamed: ATHRU_BEB.5, ATHRU_TEB.5
unnamed: ATHRU_BEB.4, ATHRU_TEB.4
unnamed: ATHRU_BEB.3, ATHRU_TEB.3
unnamed: ATHRU_BEB.2, ATHRU_TEB.2
unnamed: ATHRU_BEB.38, ATHRU_TEB.38
unnamed: ATHRU_BEB.39, ATHRU_TEB.39
unnamed: ATHRU_BEB.40, ATHRU_TEB.40
unnamed: ATHRU_BEB.41, ATHRU_TEB.41
unnamed: ATHRU_BEB.42, ATHRU_TEB.42
unnamed: ATHRU_BEB.43, ATHRU_TEB.43
unnamed: ATHRU_BEB.44, ATHRU_TEB.44
unnamed: ATHRU_BEB.45, ATHRU_TEB.45
unnamed: ATHRU_BEB.46, ATHRU_TEB.46
unnamed: ATHRU_BEB.47, ATHRU_TEB.47
unnamed: ATHRU_BEB.48, ATHRU_TEB.48
unnamed: ATHRU_BEB.49, ATHRU_TEB.49
unnamed: ATHRU_BEB.50, ATHRU_TEB.50
unnamed: ATHRU_BEB.51, ATHRU_TEB.51
unnamed: ATHRU_BEB.52, ATHRU_TEB.52
unnamed: ATHRU_BEB.53, ATHRU_TEB.53
unnamed: ATHRU_BEB.54, ATHRU_TEB.54
unnamed: ATHRU_BEB.55, ATHRU_TEB.55
unnamed: ATHRU_BEB.56, ATHRU_TEB.56
unnamed: ATHRU_BEB.57, ATHRU_TEB.57
unnamed: ATHRU_BEB.58, ATHRU_TEB.58
unnamed: ATHRU_BEB.59, ATHRU_TEB.59
unnamed: ATHRU_BEB.60, ATHRU_TEB.60
unnamed: ATHRU_BEB.61, ATHRU_TEB.61
unnamed: ATHRU_BEB.62, ATHRU_TEB.62
unnamed: ATHRU_BEB.63, ATHRU_TEB.63
unnamed: ATHRU_BEB.64, ATHRU_TEB.64
unnamed: ATHRU_BEB.65, ATHRU_TEB.65
unnamed: ATHRU_BEB.66, ATHRU_TEB.66
unnamed: ATHRU_BEB.67, ATHRU_TEB.67
unnamed: ATHRU_BEB.68, ATHRU_TEB.68
unnamed: ATHRU_BWB.33, ATHRU_TWB.33
unnamed: ATHRU_BWB.32, ATHRU_TWB.32
unnamed: ATHRU_BWB.31, ATHRU_TWB.31
unnamed: ATHRU_BWB.30, ATHRU_TWB.30
unnamed: ATHRU_BWB.29, ATHRU_TWB.29
unnamed: ATHRU_BWB.28, ATHRU_TWB.28
unnamed: ATHRU_BWB.27, ATHRU_TWB.27
unnamed: ATHRU_BWB.26, ATHRU_TWB.26
unnamed: ATHRU_BWB.25, ATHRU_TWB.25
unnamed: ATHRU_BWB.24, ATHRU_TWB.24
unnamed: ATHRU_BWB.23, ATHRU_TWB.23
unnamed: ATHRU_BWB.22, ATHRU_TWB.22
unnamed: ATHRU_BWB.21, ATHRU_TWB.21
unnamed: ATHRU_BWB.20, ATHRU_TWB.20
unnamed: ATHRU_BWB.19, ATHRU_TWB.19
unnamed: ATHRU_BWB.18, ATHRU_TWB.18
unnamed: ATHRU_BWB.17, ATHRU_TWB.17
unnamed: ATHRU_BWB.16, ATHRU_TWB.16
unnamed: ATHRU_BWB.15, ATHRU_TWB.15
unnamed: ATHRU_BWB.14, ATHRU_TWB.14
unnamed: ATHRU_BWB.13, ATHRU_TWB.13
unnamed: ATHRU_BWB.12, ATHRU_TWB.12
unnamed: ATHRU_BWB.11, ATHRU_TWB.11
unnamed: ATHRU_BWB.10, ATHRU_TWB.10
unnamed: ATHRU_BWB.9, ATHRU_TWB.9
unnamed: ATHRU_BWB.8, ATHRU_TWB.8
unnamed: ATHRU_BWB.7, ATHRU_TWB.7
unnamed: ATHRU_BWB.6, ATHRU_TWB.6
unnamed: ATHRU_BWB.5, ATHRU_TWB.5
unnamed: ATHRU_BWB.4, ATHRU_TWB.4
unnamed: ATHRU_BWB.3, ATHRU_TWB.3
unnamed: ATHRU_BWB.2, ATHRU_TWB.2
unnamed: ATHRU_BWB.38, ATHRU_TWB.38
unnamed: ATHRU_BWB.39, ATHRU_TWB.39
unnamed: ATHRU_BWB.40, ATHRU_TWB.40
unnamed: ATHRU_BWB.41, ATHRU_TWB.41
unnamed: ATHRU_BWB.42, ATHRU_TWB.42
unnamed: ATHRU_BWB.43, ATHRU_TWB.43
unnamed: ATHRU_BWB.44, ATHRU_TWB.44
unnamed: ATHRU_BWB.45, ATHRU_TWB.45
unnamed: ATHRU_BWB.46, ATHRU_TWB.46
unnamed: ATHRU_BWB.47, ATHRU_TWB.47
unnamed: ATHRU_BWB.48, ATHRU_TWB.48
unnamed: ATHRU_BWB.49, ATHRU_TWB.49
unnamed: ATHRU_BWB.50, ATHRU_TWB.50
unnamed: ATHRU_BWB.51, ATHRU_TWB.51
unnamed: ATHRU_BWB.52, ATHRU_TWB.52
unnamed: ATHRU_BWB.53, ATHRU_TWB.53
unnamed: ATHRU_BWB.54, ATHRU_TWB.54
unnamed: ATHRU_BWB.55, ATHRU_TWB.55
unnamed: ATHRU_BWB.56, ATHRU_TWB.56
unnamed: ATHRU_BWB.57, ATHRU_TWB.57
unnamed: ATHRU_BWB.58, ATHRU_TWB.58
unnamed: ATHRU_BWB.59, ATHRU_TWB.59
unnamed: ATHRU_BWB.60, ATHRU_TWB.60
unnamed: ATHRU_BWB.61, ATHRU_TWB.61
unnamed: ATHRU_BWB.62, ATHRU_TWB.62
unnamed: ATHRU_BWB.63, ATHRU_TWB.63
unnamed: ATHRU_BWB.64, ATHRU_TWB.64
unnamed: ATHRU_BWB.65, ATHRU_TWB.65
unnamed: ATHRU_BWB.66, ATHRU_TWB.66
unnamed: ATHRU_BWB.67, ATHRU_TWB.67
unnamed: ATHRU_BWB.68, ATHRU_TWB.68
unnamed: ATHRU_BEB.37, ATHRU_TEB.37
unnamed: AIN_BNB.68, AMP_A.0 (IN0)
unnamed: AIN_BNB.67, AMP_A.1 (IN1)
unnamed: ATHRU_BWB.37, ATHRU_TWB.37
REF: AIN_BNB.1, AIN_BNB.36, AIN_BSB.1, AIN_BSB.36, AMP_A.B1 (REF_ELEC), AMP_B.B1 (REF_ELEC), REF1.1, U2.4 (3Z)
REF_THRU_1: ATHRU_BWB.36, ATHRU_TWB.36
REF_THRU_2: ATHRU_BWB.1, ATHRU_TWB.1
REF_THRU_3: ATHRU_BEB.36, ATHRU_TEB.36
REF_THRU_4: ATHRU_BEB.1, ATHRU_TEB.1
SCLK+: AMP_A.B12 (SCLK+), AMP_B.B12 (SCLK+), DIO_TEA.14, R2.2
SCLK+_THRU: DTHRU_BNA.14, DTHRU_TNA.14
SCLK-: AMP_A.B11 (SCLK-), AMP_B.B11 (SCLK-), DIO_TEA.13, R2.1
SCLK-_THRU: DTHRU_BNA.13, DTHRU_TNA.13
VCC: AMP_A.B2 (VESD), AMP_A.B4 (VDD1), AMP_A.B17 (VDD2), AMP_A.B18 (VDD3), AMP_A.B21 (LVDS_EN), AMP_B.B2 (VESD), AMP_B.B4 (VDD1), AMP_B.B17 (VDD2), AMP_B.B18 (VDD3), AMP_B.B21 (LVDS_EN), C2.1, C3.1, C8.1, DIO_TEA.10, U1.VS1, U1.VS2, U2.16 (VCC), VCC1.1, VCC2.1
VCC_THRU: DTHRU_BNA.10, DTHRU_TNA.10
XOUT1: C4.2, R8.2, U1.XOUT
YOUT1: C5.2, R9.2, U1.YOUT
ZOUT1: C6.2, R10.2, U1.ZOUT

Notes on the sheet:
MECHANICAL
ELECTROPLATING
A/D CONVERSION
PASS THROUGH
TEST POINTS
Pull-down nominal states: S1: ELEC_TEST1 --> OPEN S2: ELEC_TEST2 --> OPEN S3: REF --> GND (if R4 is in place)
Solderable Pins
AUXIN's should be jumpered if you want to be compatiable with old headstages
ACCELEROMETER

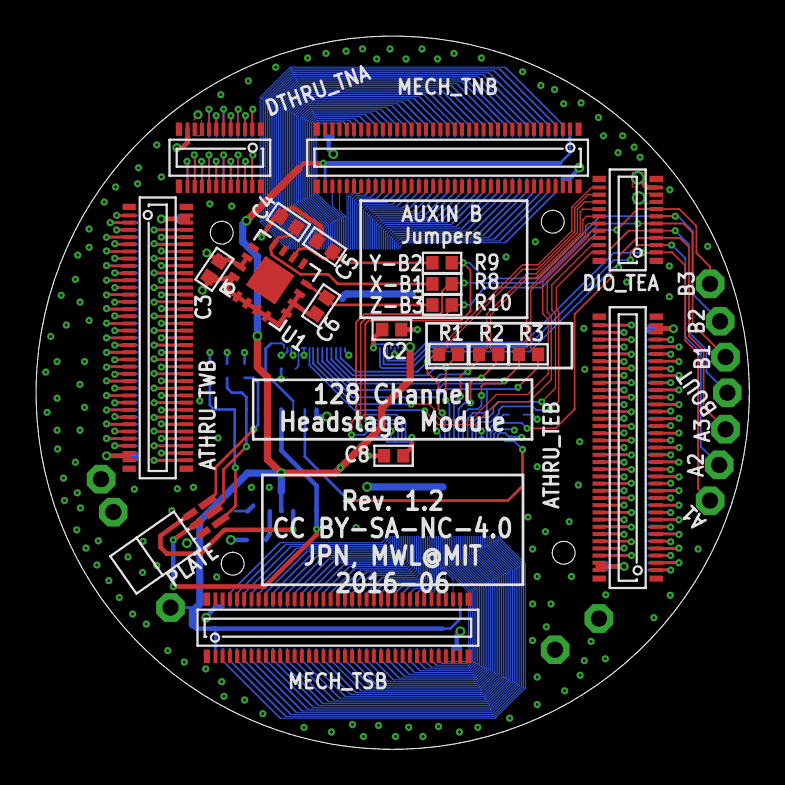
[picture p209: board headstage.brd from above]

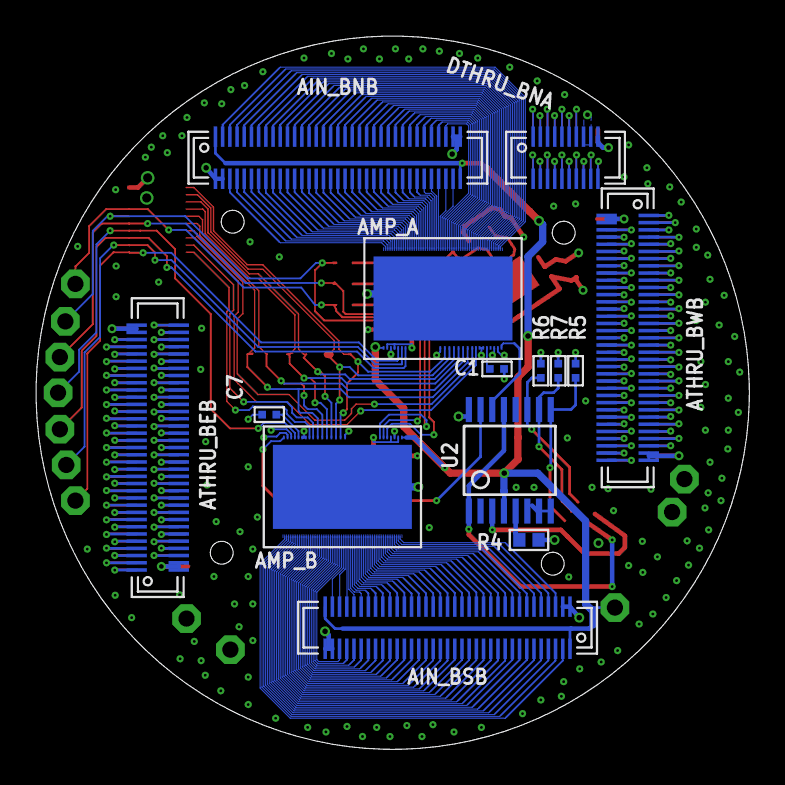
[picture p210: board headstage.brd from below]

Board: 4 copper layers, 39.6 x 39.6 mm, 46 parts (14 on the bottom side), 316 nets.
