jonnew/ONIX/spi-interface/spi-interface-TFML.brd

## EAGLE design spi-interface/spi-interface-TFML.brd (2016-10-10)

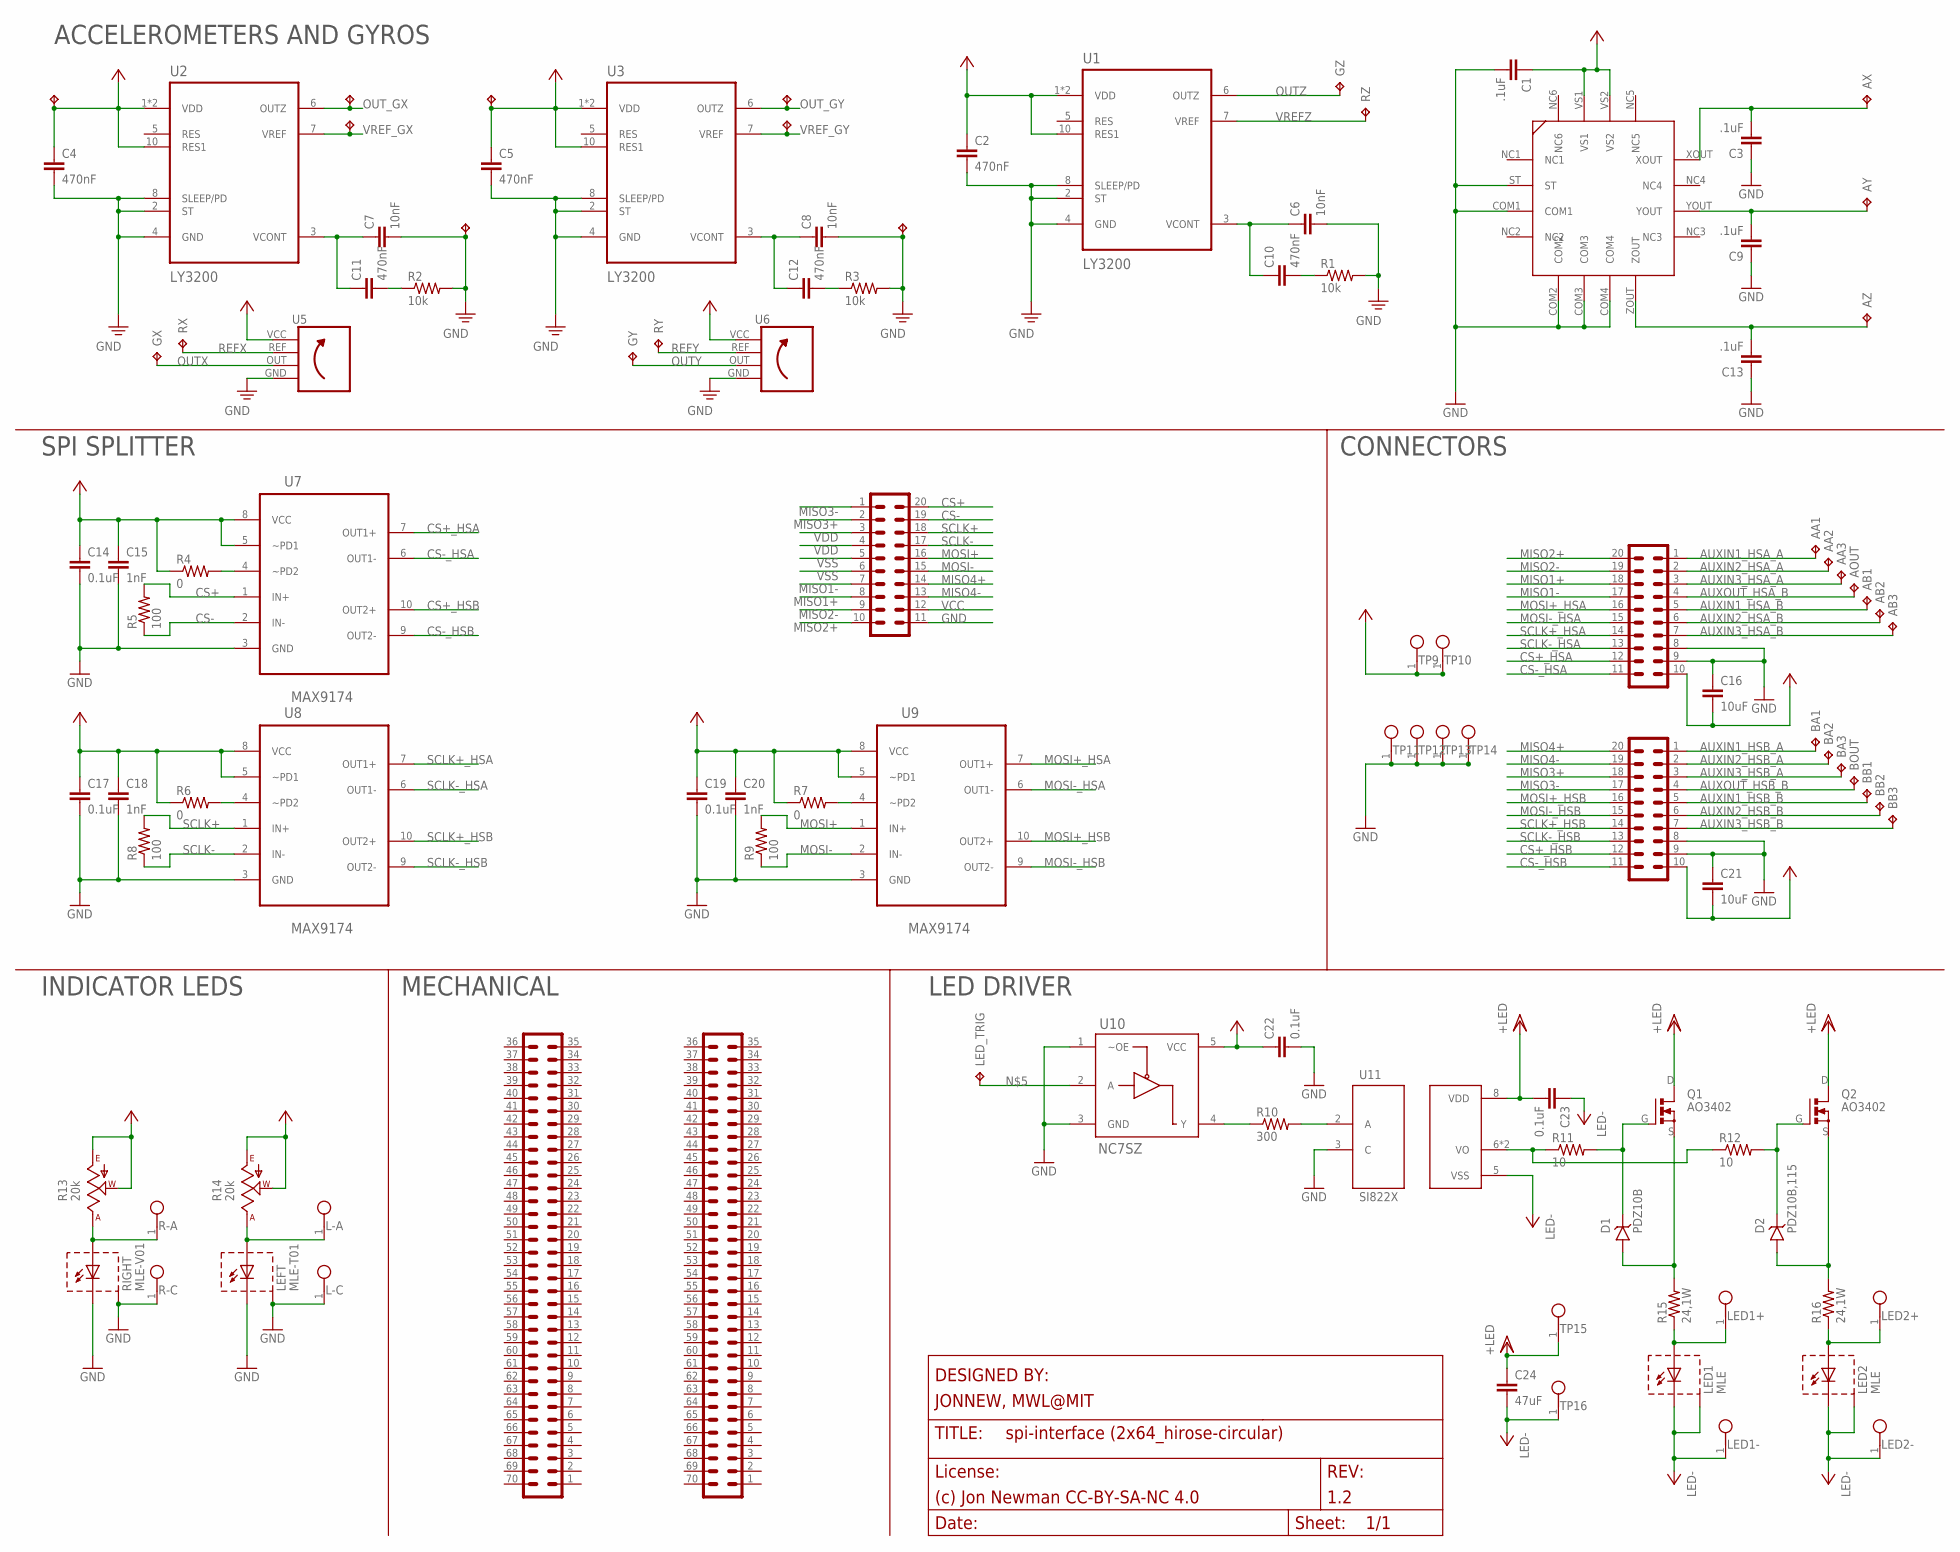
[picture p211: schematic spi-interface-TFML.sch]

Parts:
AA1, AA2, AA3: TP_0.5MM; TESTPOINT_0.5MM
AB1, AB2, AB3: TP_0.5MM; TESTPOINT_0.5MM
AOUT: TP_0.5MM; TESTPOINT_0.5MM
AX: TP_0.5MM; TESTPOINT_0.5MM
AY: TP_0.5MM; TESTPOINT_0.5MM
AZ: TP_0.5MM; TESTPOINT_0.5MM
BA1, BA2, BA3: TP_0.5MM; TESTPOINT_0.5MM
BB1, BB2, BB3: TP_0.5MM; TESTPOINT_0.5MM
BOUT: TP_0.5MM; TESTPOINT_0.5MM
C1: .1uF; 0402
C2, C4, C5, C10, C11, C12: 470nF; 0201
C3, C9, C13: .1uF; 0201
C6, C7, C8: 10nF; 0201
C14, C17, C19, C22, C23: 0.1uF; 0402
C15, C18, C20: 1nF; 0201
C16, C21: 10uF; 0805
C24: 47uF; 1206
D1: PDZ10B; SOD-323
D2: PDZ10B,115; SOD-323
DIO_HSA: PINHD-2X10_DF40-20REC; DF40-20REC
DIO_HSB: PINHD-2X10_DF40-20REC; DF40-20REC
GX: TP_0.5MM; TESTPOINT_0.5MM
GY: TP_0.5MM; TESTPOINT_0.5MM
GZ: TP_0.5MM; TESTPOINT_0.5MM
L-A: TESTPOINT_SMALL
L-C: TESTPOINT_SMALL
LED1, LED2: MLE; LED-MLE
LED1+, LED1-, LED2+, LED2-: TESTPOINT_SMALL
LED_TRIG: TP_0.5MM; TESTPOINT_0.5MM
LEFT: MLE-T01; LED-MLE
MECH_E0B: PINHD-2X35_DF40REC; DF40-70REC
MECH_W0B: PINHD-2X35_DF40REC; DF40-70REC
Q1, Q2: AO3402; SOT23-GSD
R1, R2, R3: 10k; 0201
R4, R6, R7: 0; 0201
R5, R8, R9: 100; 0201
R10: 300; 0402
R11, R12: 10; 0402
R13, R14: 20k; SM-42/43W
R15, R16: 24,1W; 0805
R-A: TESTPOINT_SMALL
R-C: TESTPOINT_SMALL
RIGHT: MLE-V01; LED-MLE
RX: TP_0.5MM; TESTPOINT_0.5MM
RY: TP_0.5MM; TESTPOINT_0.5MM
RZ: TP_0.5MM; TESTPOINT_0.5MM
TETHER: TFML-110-01-S-D-LC; TFML-110-01-2-D-LC
TP1, TP2, TP3, TP4, TP5, TP6, TP7, TP8: TPTP08SQ; TP08SQ
TP9, TP10, TP11, TP12, TP13, TP14, TP15, TP16: TESTPOINT_SMALL
U1, U2, U3: LY3200; LGA-10-COMPACT
U4: ADXL335
U5, U6: LY3200-VERT-MODULE
U7, U8, U9: MAX9174; 10-UMAX
U10: NC7SZ; SOT-23-5
U11: SI822X; SOIC127P500X400-8N

Connections:
AUXIN1_HSA_A: AA1.1, DIO_HSA.1
AUXIN1_HSA_B: AB1.1, DIO_HSA.5
AUXIN1_HSB_A: BA1.1, DIO_HSB.1
AUXIN1_HSB_B: BB1.1, DIO_HSB.5
AUXIN2_HSA_A: AA2.1, DIO_HSA.2
AUXIN2_HSA_B: AB2.1, DIO_HSA.6
AUXIN2_HSB_A: BA2.1, DIO_HSB.2
AUXIN2_HSB_B: BB2.1, DIO_HSB.6
AUXIN3_HSA_A: AA3.1, DIO_HSA.3
AUXIN3_HSA_B: AB3.1, DIO_HSA.7
AUXIN3_HSB_A: BA3.1, DIO_HSB.3
AUXIN3_HSB_B: BB3.1, DIO_HSB.7
AUXOUT_HSA_B: AOUT.1, DIO_HSA.4
AUXOUT_HSB_B: BOUT.1, DIO_HSB.4
CS+: R5.2, TETHER.20, U7.1 (IN+)
CS+_HSA: DIO_HSA.12, U7.7 (OUT1+)
CS+_HSB: DIO_HSB.12, U7.10 (OUT2+)
CS-: R5.1, TETHER.19, U7.2 (IN-)
CS-_HSA: DIO_HSA.11, U7.6 (OUT1-)
CS-_HSB: DIO_HSB.11, U7.9 (OUT2-)
GND: C1.2, C2.2, C3.1, C4.2, C5.2, C6.2, C7.2, C8.2, C9.1, C13.1, C14.2, C15.2, C16.1, C17.2, C18.2, C19.2, C20.2, C21.1, C22.2, DIO_HSA.8, DIO_HSA.9, DIO_HSB.8, DIO_HSB.9, L-C.1, LEFT.C1 (C), LEFT.C2 (C), LEFT.HS (BODY), R1.2, R2.2, R3.2, R-C.1, RIGHT.C1 (C), RIGHT.C2 (C), RIGHT.HS (BODY), TETHER.11, TP7.TP, TP8.TP, TP11.1, TP12.1, TP13.1, TP14.1, U1.2 (ST), U1.4 (GND), U1.8 (SLEEP/PD), U2.2 (ST), U2.4 (GND), U2.8 (SLEEP/PD), U3.2 (ST), U3.4 (GND), U3.8 (SLEEP/PD), U4.COM1, U4.COM2, U4.COM3, U4.COM4, U4.ST, U5.GND, U6.GND, U7.3 (GND), U8.3 (GND), U9.3 (GND), U10.1 (~OE), U10.3 (GND), U11.3 (C)
MISO1+: DIO_HSA.18, TETHER.8
MISO1-: DIO_HSA.17, TETHER.7
MISO2+: DIO_HSA.20, TETHER.10
MISO2-: DIO_HSA.19, TETHER.9
MISO3+: DIO_HSB.18, TETHER.2
MISO3-: DIO_HSB.17, TETHER.1
MISO4+: DIO_HSB.20, TETHER.14
MISO4-: DIO_HSB.19, TETHER.13
MOSI+: R9.2, TETHER.16, U9.1 (IN+)
MOSI+_HSA: DIO_HSA.16, U9.7 (OUT1+)
MOSI+_HSB: DIO_HSB.16, U9.10 (OUT2+)
MOSI-: R9.1, TETHER.15, U9.2 (IN-)
MOSI-_HSA: DIO_HSA.15, U9.6 (OUT1-)
MOSI-_HSB: DIO_HSB.15, U9.9 (OUT2-)
unnamed: R10.2, U11.2 (A)
unnamed: C7.1, C11.1, U2.3 (VCONT)
unnamed: LED1.A1 (A), LED1.A2 (A), LED1+.1, R15.1
unnamed: D1.A, Q1.S, R15.2
unnamed: LED_TRIG.1, U10.2 (A)
unnamed: R10.1, U10.4 (Y)
unnamed: D2.C, Q2.G, R12.2
unnamed: C11.2, R2.1
unnamed: R13.1 (A), R-A.1, RIGHT.A1 (A), RIGHT.A2 (A)
unnamed: C8.1, C12.1, U3.3 (VCONT)
unnamed: D2.A, Q2.S, R16.2
unnamed: LED2.A1 (A), LED2.A2 (A), LED2+.1, R16.1
unnamed: L-A.1, LEFT.A1 (A), LEFT.A2 (A), R14.1 (A)
unnamed: C12.2, R3.1
unnamed: C6.1, C10.1, U1.3 (VCONT)
unnamed: C10.2, R1.1
unnamed: R4.2, U7.4 (~PD2)
unnamed: R7.2, U9.4 (~PD2)
unnamed: R6.2, U8.4 (~PD2)
unnamed: D1.C, Q1.G, R11.2
unnamed: R11.1, R12.1, U11.6 (VO), U11.7 (VO)
OUTX: GX.1, U5.OUT
OUTY: GY.1, U6.OUT
OUTZ: GZ.1, U1.6 (OUTZ)
OUT_GX: TP2.TP, U2.6 (OUTZ)
OUT_GY: TP4.TP, U3.6 (OUTZ)
REFX: RX.1, U5.REF
REFY: RY.1, U6.REF
SCLK+: R8.2, TETHER.18, U8.1 (IN+)
SCLK+_HSA: DIO_HSA.14, U8.7 (OUT1+)
SCLK+_HSB: DIO_HSB.14, U8.10 (OUT2+)
SCLK-: R8.1, TETHER.17, U8.2 (IN-)
SCLK-_HSA: DIO_HSA.13, U8.6 (OUT1-)
SCLK-_HSB: DIO_HSB.13, U8.9 (OUT2-)
VCC: C1.1, C2.1, C4.1, C5.1, C14.1, C15.1, C16.2, C17.1, C18.1, C19.1, C20.1, C21.2, C22.1, DIO_HSA.10, DIO_HSB.10, R4.1, R6.1, R7.1, R13.2 (W), R13.3 (E), R14.2 (W), R14.3 (E), TETHER.12, TP1.TP, TP3.TP, TP9.1, TP10.1, U1.1 (VDD), U1.9 (VDD), U1.10 (RES1), U2.1 (VDD), U2.9 (VDD), U2.10 (RES1), U3.1 (VDD), U3.9 (VDD), U3.10 (RES1), U4.VS1, U4.VS2, U5.VCC, U6.VCC, U7.5 (~PD1), U7.8 (VCC), U8.5 (~PD1), U8.8 (VCC), U9.5 (~PD1), U9.8 (VCC), U10.5 (VCC)
VDD: C23.2, C24.1, Q1.D, Q2.D, TETHER.3, TETHER.4, TP15.1, U11.8 (VDD)
VREFZ: RZ.1, U1.7 (VREF)
VREF_GX: TP5.TP, U2.7 (VREF)
VREF_GY: TP6.TP, U3.7 (VREF)
VSS: C23.1, C24.2, LED1.C1 (C), LED1.C2 (C), LED1.HS (BODY), LED1-.1, LED2.C1 (C), LED2.C2 (C), LED2.HS (BODY), LED2-.1, TETHER.5, TETHER.6, TP16.1, U11.5 (VSS)
XOUT1: AX.1, C3.2, U4.XOUT
YOUT1: AY.1, C9.2, U4.YOUT
ZOUT1: AZ.1, C13.2, U4.ZOUT

Notes on the sheet:
SPI SPLITTER
MECHANICAL
LED DRIVER
CONNECTORS
INDICATOR LEDS
ACCELEROMETERS AND GYROS

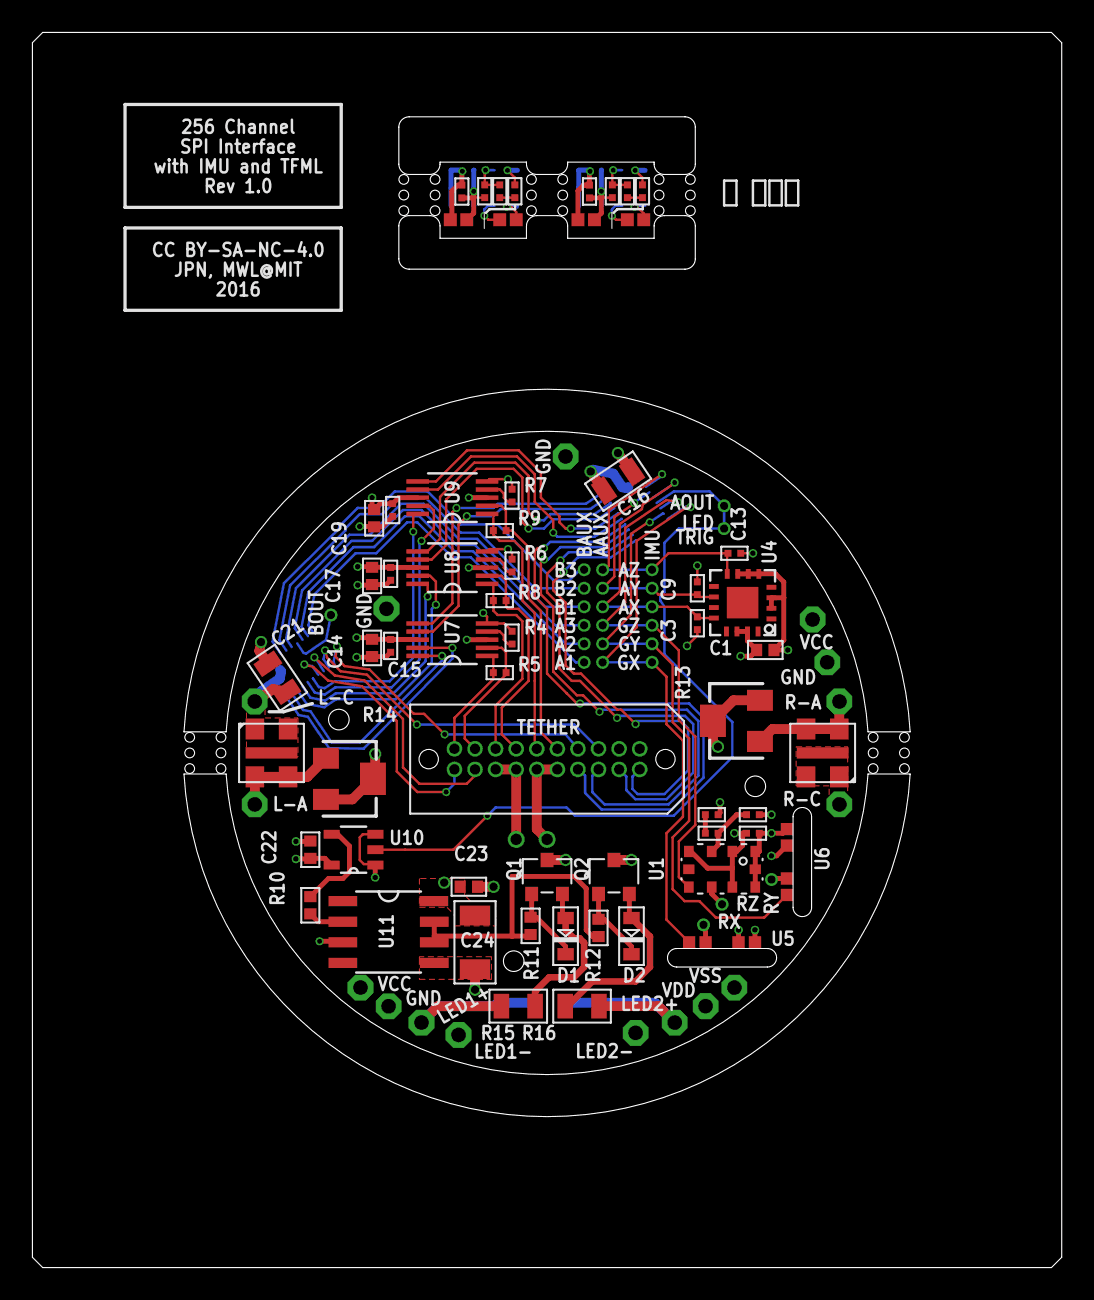
[picture p212: board spi-interface-TFML.brd from above]

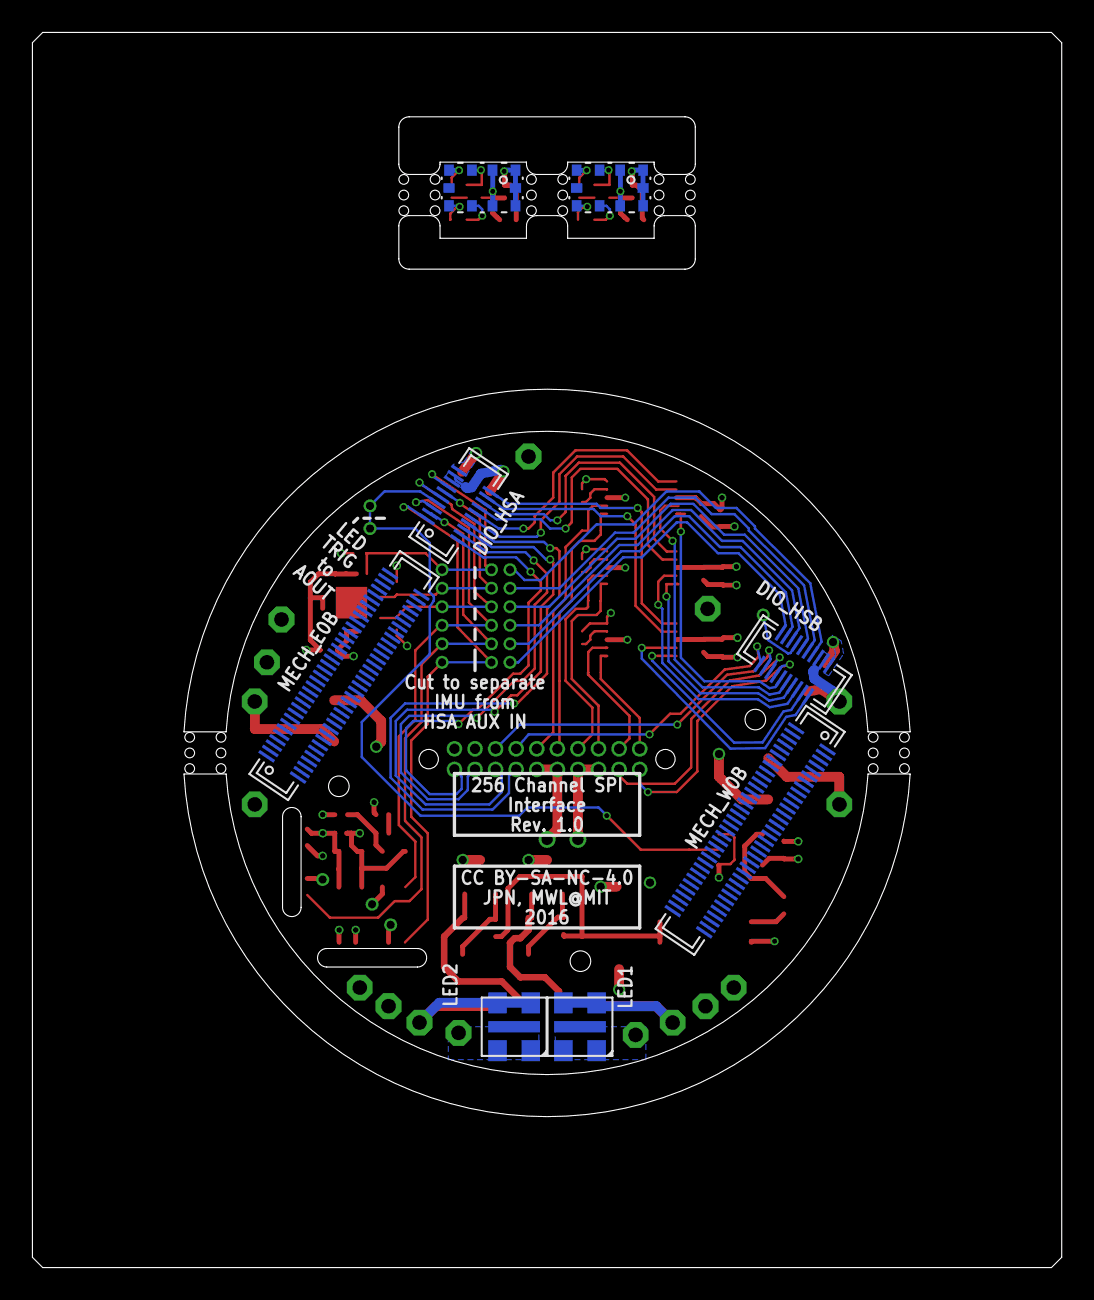
[picture p213: board spi-interface-TFML.brd from below]

Board: 4 copper layers, 63.5 x 76.2 mm, 112 parts (8 on the bottom side), 78 nets.
