jonnew/ONIX/2x32_JMD_Dual/spi-interface/spi-interface.sch

## EAGLE design 2x32_JMD_Dual/spi-interface/spi-interface.sch (2014-08-11)

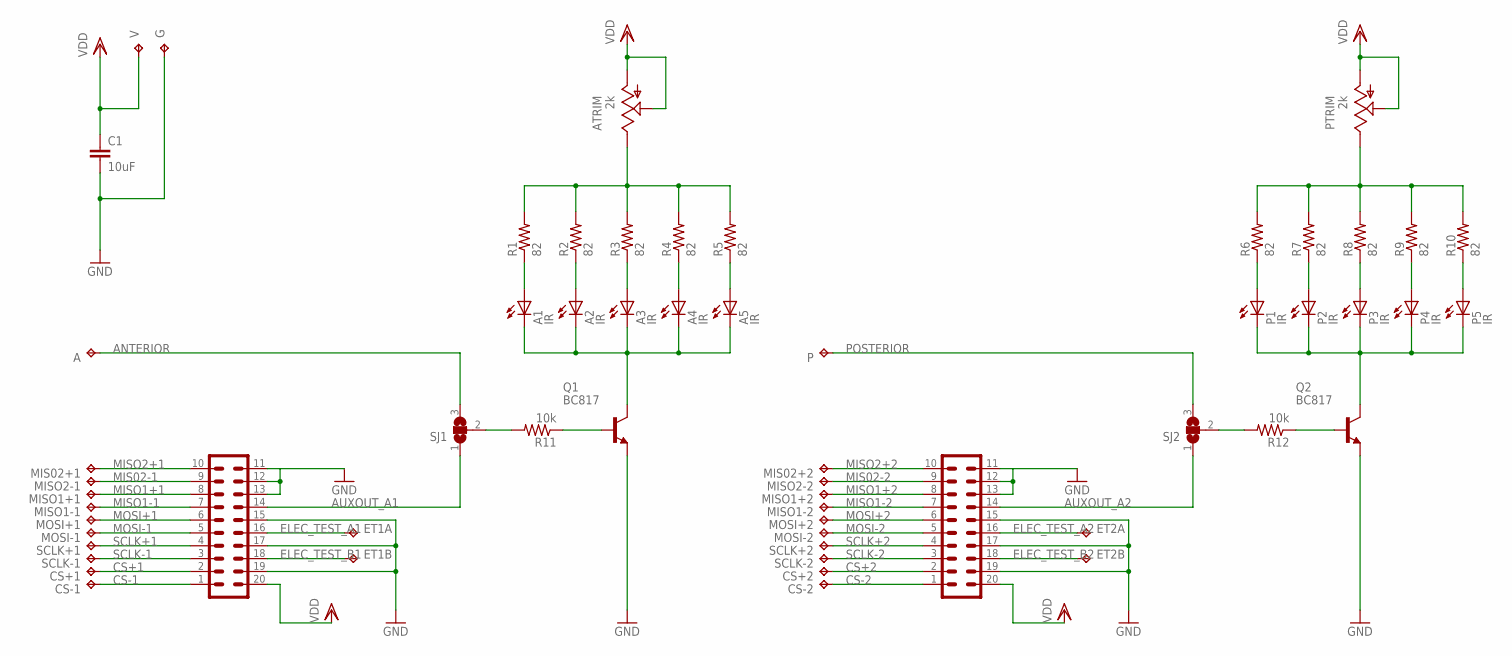
[picture p215: schematic spi-interface.sch]

Parts:
A: TP_01; TP01
A1, A2, A3, A4, A5: IR; LED-0603
ATRIM: 2k; EIA/EIAJ
C1: 10uF; 0805
CS+1, CS+2: TP_01; TP01
CS-1, CS-2: TP_01; TP01
ET1A, ET1B, ET2A, ET2B: TP_03; TP03
G: TP_02; TP02
HS1, HS2: JMD20-V
MIS02+1, MIS02+2: TP_01; TP01
MISO1+1, MISO1+2, MISO1-1, MISO1-2, MISO2-1, MISO2-2: TP_01; TP01
MOSI+1, MOSI+2: TP_01; TP01
MOSI-1, MOSI-2: TP_01; TP01
P: TP_01; TP01
P1, P2, P3, P4, P5: IR; LED-0603
PTRIM: 2k; EIA/EIAJ
Q1, Q2: BC817; SOT23-BEC
R1, R2, R3, R4, R5, R6, R7, R8, R9, R10: 82; 0402
R11, R12: 10k; 0402
SCLK+1, SCLK+2: TP_01; TP01
SCLK-1, SCLK-2: TP_01; TP01
SJ1, SJ2: SJ2W; SJ_2
V: TP_02; TP02

Connections:
ANTERIOR: A.TP, SJ1.3
AUXOUT_A1: HS1.14, SJ1.1
AUXOUT_A2: HS2.14, SJ2.1
B2: P1.C, P2.C, P3.C, P4.C, P5.C, Q2.C
CS+1: CS+1.TP, HS1.2
CS+2: CS+2.TP, HS2.2
CS-1: CS-1.TP, HS1.1
CS-2: CS-2.TP, HS2.1
ELEC_TEST_A1: ET1A.TP, HS1.16
ELEC_TEST_A2: ET2A.TP, HS2.16
ELEC_TEST_B1: ET1B.TP, HS1.18
ELEC_TEST_B2: ET2B.TP, HS2.18
F1: A1.C, A2.C, A3.C, A4.C, A5.C, Q1.C
GND: C1.2, G.TP, HS1.11, HS1.12, HS1.13, HS1.15, HS1.17, HS1.19, HS2.11, HS2.12, HS2.13, HS2.15, HS2.17, HS2.19, Q1.E, Q2.E
MIS02-1: HS1.9, MISO2-1.TP
MIS02-2: HS2.9, MISO2-2.TP
MISO1+1: HS1.8, MISO1+1.TP
MISO1+2: HS2.8, MISO1+2.TP
MISO1-1: HS1.7, MISO1-1.TP
MISO1-2: HS2.7, MISO1-2.TP
MISO2+1: HS1.10, MIS02+1.TP
MISO2+2: HS2.10, MIS02+2.TP
MOSI+1: HS1.6, MOSI+1.TP
MOSI+2: HS2.6, MOSI+2.TP
MOSI-1: HS1.5, MOSI-1.TP
MOSI-2: HS2.5, MOSI-2.TP
unnamed: ATRIM.E, R1.2, R2.2, R3.2, R4.2, R5.2
unnamed: P1.A, R6.1
unnamed: A1.A, R1.1
unnamed: R12.2, SJ2.2
unnamed: Q2.B, R12.1
unnamed: PTRIM.E, R6.2, R7.2, R8.2, R9.2, R10.2
unnamed: A2.A, R2.1
unnamed: A3.A, R3.1
unnamed: A4.A, R4.1
unnamed: A5.A, R5.1
unnamed: P2.A, R7.1
unnamed: P3.A, R8.1
unnamed: P4.A, R9.1
unnamed: P5.A, R10.1
unnamed: Q1.B, R11.1
unnamed: R11.2, SJ1.2
POSTERIOR: P.TP, SJ2.3
SCLK+1: HS1.4, SCLK+1.TP
SCLK+2: HS2.4, SCLK+2.TP
SCLK-1: HS1.3, SCLK-1.TP
SCLK-2: HS2.3, SCLK-2.TP
VDD: ATRIM.A, ATRIM.S, C1.1, HS1.20, HS2.20, PTRIM.A, PTRIM.S, V.TP
